TomohiroTani28/Taros/fallback/02_dv-fbqc-desktop-v5.0.md

> **フォールバック参考文書**: 本文書はDV-FBQC v5.0 Desktopのフォールバック設計です。プロジェクトの主軸はCV方式（Taros Portable）に移行済み。最新設計は `design/00_overview.md` を参照してください。

# デスクトップ光量子コンピュータ 完全設計書 v5.0

**文書番号**: PQC-DESIGN-v5.0
**作成日**: Phase -1 開始前
**ステータス**: フォールバック参考（DV-FBQC代替設計）
**構成**: SS0（Executive Summary）+ セクション1-12 + Appendix A-C
**前提**: v4.0 R6の全56合意事項（C1-C56）を継承し、最新研究成果14件を統合

---

## 📍 ポジショニング明確化 (2026-05-08 Phase 2 論点5 解決)

### v5.0の真の位置付け

v5.0 は**「フェイルセーフ（緊急回復）設計」ではなく「Phase 1+ 技術選択肢」**です。以下の点を理解してください：

| 項目 | v5.0の実態 |
|---|---|
| **設計の性質** | 2025-2026年の新技術6件を統合した根本的な再設計（v4.0 R6の単なる進化ではない） |
| **リスク** | より新しい技術スタック（単一統合PIC、InP QD 1550nm、PsiQuantum Omega）の統合リスク |
| **成功確率** | 65%（v4.0 R6の78%より低い） |
| **意思決定時点** | Phase 1終了時（月24）：v4.0 R6保守路線 vs v5.0 先進路線を選択 |
| **費用削減** | ¥3.54B → ¥6,480万（主原因：SNSPD削減。新技術の統合労力相殺） |

### 判断フレームワーク

| シナリオ | 推奨戦略 |
|---|---|
| **現在（Phase 0-1）** | **v4.0 R6で計画**。v5.0の新技術を並列評価（2026-2027年） |
| **Phase 1終了時** | PIC統合進展・InP QD実績・PT205実績 に基づき最終判定 |
| **全技術成熟（2027年以降）** | v5.0への移行で5-10倍コスト削減可能 |
| **技術停滞** | v4.0 R6で製品化（遅延なし） |

### 詳細分析

完全な技術・コスト・リスク分析は **`fallback/04_v4-v5-comparison.md`** を参照。主な発見：

✅ **v5.0が信頼できる理由**:
- 6つのブレイクスルーはすべて査読済み論文 / 公開アナウンス済み（投機的ではない）
- 個々のコンポーネントはPhase -1/0仕様を満たす

⚠️ **v5.0のリスク**:
- 単一統合PIC量産化: 2026-2027年（40%遅延リスク）
- InP QD 1550nm歩留まり: 3年の実績歴でまだ不確定（30%リスク）
- PT205振動: v4.0から未解決。v5.0は楽観的仮定（35%リスク）
- 統合リスク: これら組み合わせで全体65%成功確率

---

## SS0: Executive Summary — デスクトップ光量子コンピュータ

### v5.0のビジョン

v4.0 R6は「小型実用機」をPhase 1目標とした。v5.0はこれを根本的に前倒しし、
**開始後約3年にデスクトップ光量子コンピュータのプロトタイプ、
開始後約5年に量産型を実現する**設計書である。

v5.0の革新は、6つのブレイクスルーを**同時に統合**することで達成される:

| # | ブレイクスルー | 出典 | v4.0 R6への影響 |
|---|---|---|---|
| B1 | InP QD 1550nm: V=90%, g²(0)=0.005 | arXiv:2602.06140 | QFC除去パスがPhase 1に前倒し可能 |
| B2 | PsiQuantum Omega: fusion fidelity 99.22%, 損失閾値18.8% | Nature (2025) | 損失バジェットに18ptの追加マージン |
| B3 | Bluefors/Cryomech PT205: 8.6kg, 1.3kW, >10mW@2.5K | Bluefors (2025.03) | クライオスタットがデスクサイズに |
| B4 | WI-SNSPD 99.73%検出効率 | 南京大学+北京大学 (2025) | 検出系損失が事実上ゼロに |
| B5 | Floquet符号損失閾値6.3%（表面符号の2倍） | arXiv:2410.07065 | フォトニック専用符号で閾値大幅改善 |
| B6 | GB符号FBQC直接実装論文 | npj Quantum Inf. (2026) | GB符号のFBQC埋め込みが設計済み |

### デスクトップ機 最終推奨構成（v5.0確定版）

| 項目 | v4.0 R6 Phase 1 | **v5.0 Desktop** | 改善率 |
|---|---|---|---|
| **筐体サイズ** | 2.5m²（2ラック+サイドカー） | **60cm×40cm×50cm** | 体積1/25 |
| **重量** | ~180kg | **本体28kg + コンプレッサー23kg = システム51kg** | 1/3.5 |
| **消費電力** | ~8kW | **2.1kW** | 1/4 |
| **冷却系** | SHI RDK-415E (75kg) | **Cryomech PT205 (コールドヘッド8.6kg + コンプレッサー23kg外付け床置き)** | 1/3 |
| **光源** | QDM ~80個 + LNOI QFC | **InP QD 24個 (1550nm直接)** | QFC除去 |
| **PIC** | LNOI+SiN統合PIC 3枚 | **ワンチップ統合モジュール 1枚** | 1/3 |
| **検出器** | WI-SNSPD 3,000個 | **WI-SNSPD ~1,000個 (99.7%効率)** [v3.2: 旧500→1000。パイプラインは物理検出器数を半減しない] | 1/3 |
| **SNSPD動作温度** | 4.2K | **2.5K (PT205直接)** | 改善 |
| **符号** | GB [[144,12,12]] | **Floquet-GB [[72,12,6]]** | 物理qubit半減 |
| **デコーダ** | FPGA Ambiguity Clustering | **FPGA 1枚 (Local Clustering)** | 同等 |
| **論理qubit** | 42（最良）/ 4-12（保証） | **12（標準）/ 48（4モジュール）** | 同等 |
| **Tゲートレート** | 3.5MHz | **3.5MHz (Single-Shot)** | 同等 |
| **サイクル時間** | 2μs | **2μs** | 同等 |
| **end-to-end η** | 0.53-0.57 | **0.72-0.78** | +35% |
| **コスト（量産100台）** | 約1.5〜2.0億円 | **約6,480万円** | 1/3 |
| **起動時間** | 24時間 | **3時間** | 1/8 |
| **成功基準** | レベルB 78-80% | **レベルB 88%** | +10pt |

### コスト・スケジュール・成功確率サマリー（v5.0）

| Phase | 期間 | 投資額 | 累計投資 | レベルB確率 | レベルA確率 |
|---|---|---|---|---|---|
| Phase -1（机上検証+InP QD評価） | 開始後1年 | 約7,500万円 | 約7,500万円 | — | — |
| Phase 0（コンポーネント実証） | 開始後2年 | 約1.8億円 | 約2.6億円 | 65% | — |
| **Phase D（Desktop Prototype）** | **開始後3年** | **約1.2億円** | **約3.8億円** | **85%** | 15% |
| **Phase D+（Desktop Production）** | **開始後4-5年** | **約2.3億円** | **約6.0億円** | **92%** | **45%** |

### 直ちに着手すべきアクション Top 5（v5.0）

| 優先度 | アクション | 投資額 | 期間 | Go/No-Go |
|---|---|---|---|---|
| **1** | InP QD 1550nm デバイス評価（V>0.95同時達成検証） | 約1,200万円 | 4ヶ月 | V>0.95+g²(0)<0.02+輝度>0.40 |
| **2** | Floquet-GB [[72,12,6]] のStimシミュレーション | 約450万円 | 2ヶ月 | erasure閾値>20% |
| **3** | PT205 + WI-SNSPD 64素子の統合冷却試験 | 約1,800万円 | 6ヶ月 | 全素子>95%効率@2.5K |
| **4** | ワンチップ統合モジュール設計+DRC検証 | 約2,250万円 | 6ヶ月 | レイアウト完了 |
| **5** | PsiQuantum Omegaアーキテクチャとの互換性評価 | 約750万円 | 3ヶ月 | 製造プロセス確認 |

---

## セクション1: v4.0 R6からv5.0への主要変更概要

### 1.1 設計哲学の転換

v4.0 R6は「段階的小型化」（Phase 0→1→2で60m²→2.5m²→2m²）を方針としていた。
v5.0は**「デスクトップファースト設計」**に転換する。

**v4.0の設計フロー**: 大型研究機 → 小型化 → デスクトップ
**v5.0の設計フロー**: デスクトップ筐体制約から逆算 → 必要技術を特定 → 実現可能性を検証

この転換が可能になった理由:
1. PT205（8.6kg冷却器）の商用化により、冷却系のサイズ制約が解消
2. WI-SNSPD 99.73%により、検出器数を1/6に削減可能
3. InP QD 1550nmの急速な進展により、QFC系の完全排除が射程内
4. Floquet符号のフォトニック専用最適化により、物理qubit数を半減
5. PsiQuantum OmegaによりGlobalFoundries製造プロセスが確立

### 1.2 v5.0の六原則

v4.0の五原則に「Desktop Deployability」を追加し六原則とする。

| # | 原則 | v4.0表現 | v5.0表現 |
|---|---|---|---|
| 1 | フォールトトレランス | 既報告技術の組合せ | 同左 |
| 2 | **Desktop Deployability** | Phase別床面積目標 | **60cm×40cm×50cm筐体に全機能を収容** |
| 3 | モジュラー拡張性 | Phase間モジュール共通化>60% | **ワンチップモジュールの枚数追加で線形拡張** |
| 4 | 光ネイティブ設計 | 冷却系の段階的簡素化 | **PT205単体で全冷却要件を充足** |
| 5 | 実用性重視 | Phase別BoM | **量産100台での単価約6,480万円** |
| 6 | **QFC-Free設計** | QFC除去はPhase 2オプション | **InP QD 1550nm直接発光を主パスに昇格** |

### 1.3 v5.0で新たに統合する技術（14件）

| # | 技術 | 出典 | v5.0での位置づけ |
|---|---|---|---|
| N1 | InP QD 1550nm: V=90%, g²(0)=0.005 (TPE励起) | arXiv:2602.06140 | Primary光源候補 |
| N2 | InP QD on-demand entangled pairs: 98.3%ペア放出率 | phys.org 2026.03 | 決定論的ベル対生成の実証 |
| N3 | QD間270m単一光子テレポーテーション | ScienceDaily 2026.04 | 分散量子計算への道 |
| N4 | PsiQuantum Omega: 99.22% fusion, 99.50% HOM | Nature 2025 | 製造プロセス参照 |
| N5 | PsiQuantum損失閾値18.8% (adaptive encoded) | PsiQuantum 2025.06 | Adaptive fusionの採用 |
| N6 | Bluefors/Cryomech PT205: 8.6kg, 1.3kW | Bluefors 2025.03 | Desktop冷却系 |
| N7 | WI-SNSPD 99.73% (comb-shaped nanowire) | 南京大学 2025 | Desktop検出系 |
| N8 | LNOI-on-SiN ヘテロジニアス統合 (wafer-scale) | Nat. Commun. 2023+ | ワンチップモジュール基盤 |
| N9 | Honeycomb Floquet code損失閾値6.3% | arXiv:2410.07065 | Desktop専用符号候補 |
| N10 | Hyperbolic Floquet codes for photonic QC | arXiv:2602.22906 | 次世代符号候補 |
| N11 | GB符号のFBQC直接実装 (quantum emitters) | npj Quantum Inf. 2026 | GB-FBQC設計の確定 |
| N12 | Riverlane Local Clustering Decoder FPGA <1μs | Nat. Commun. 2025 | Desktop用デコーダ |
| N13 | Upconversion検出効率45% (室温) | AIP Advances 2025 | 将来Phase用オプション |
| N14 | Mist CVD SNSPD 約4,500円/素子 (v4.0 R6継承) | MIT EECS 2026 | Desktop BoM基盤 |

---

## セクション2: デスクトップ物理設計

### 2.1 筐体設計

```
┌─────────────────────────────────────────────────────────┐
│               　　デスクトップ光量子コンピュータ　　　          │
│                   外寸: 600mm × 400mm × 500mm              │
│                   重量: 本体28kg + コンプレッサー23kg         │
│                         (外付け床置き) = システム51kg         │
│                   消費電力: 2.1kW                            │
│                                                             │
│  ┌──────────────────────────┐  ┌─────────────────────────┐ │
│  │    光学モジュール (上段)    │  │   PT205冷却ユニット     │ │
│  │                          │  │                         │ │
│  │  ┌────────────────────┐  │  │  Cryomech PT205         │ │
│  │  │ ワンチップ統合PIC    │  │  │  8.6kg                  │ │
│  │  │ 30mm × 10mm        │  │  │  到達温度: 2.5K          │ │
│  │  │                    │  │  │  冷却能力: >10mW@2.5K    │ │
│  │  │ [InP QD]→[SiN]→   │  │  │  消費電力: 1.3kW         │ │
│  │  │ [LNOI EO]→[WI-SNSPD]│ │  │  サイズ: 280mm長         │ │
│  │  │                    │  │  │                         │ │
│  │  │ 論理qubit: 12      │  │  │  真空断熱チャンバー:     │ │
│  │  │ WI-SNSPD: ~1,000個 │  │  │  PICモジュール収容       │ │
│  │  └────────────────────┘  │  │  光ファイバ: 6本         │ │
│  │                          │  │  RF配線: 10本 (MKID)     │ │
│  │  遅延線スプール:          │  │                         │ │
│  │  SiNオンチップ(短) +      │  │  冷却時間: ~3時間        │ │
│  │  DNANF 50m×5本(中)       │  │                         │ │
│  │  直径10cmスプール         │  └─────────────────────────┘ │
│  └──────────────────────────┘                               │
│                                                             │
│  ┌──────────────────────────────────────────────────────┐  │
│  │              制御・電源モジュール (下段)                  │  │
│  │                                                      │  │
│  │  ┌──────────┐ ┌────────────┐ ┌──────────┐ ┌───────┐ │  │
│  │  │FPGA      │ │励起レーザ   │ │電源       │ │NIC    │ │  │
│  │  │Versal    │ │462nm×12ch  │ │200V→     │ │10GbE  │ │  │
│  │  │1枚       │ │+安定化光源  │ │多出力     │ │光     │ │  │
│  │  │25W       │ │50W         │ │2.1kW     │ │       │ │  │
│  │  └──────────┘ └────────────┘ └──────────┘ └───────┘ │  │
│  │                                                      │  │
│  └──────────────────────────────────────────────────────┘  │
│                                                             │
│  背面: 液冷ループ → 240mmラジエーター → NF-A14×2             │
│        (本体≤35dBA)                                         │
│  接続: 200V電源 + 10GbE光ファイバ + USB-C(管理)              │
└─────────────────────────────────────────────────────────┘
```

### 2.2 熱設計

| 発熱源 | 発熱量 | 冷却方式 |
|---|---|---|
| PT205コンプレッサー（外付け床置き） | 1.3kW | 液冷ループ → 240mmラジエーター → NF-A14×2強制空冷 |
| FPGA (VE2302×1) | 25W | ヒートパイプ → 排気ファン |
| 励起レーザ+制御 | 100W | 空冷 |
| 電源効率損失 (η=0.92) | 180W | 筐体内自然対流 |
| その他（配線、変調器） | 70W | 筐体内自然対流 |
| **合計** | **2.1kW** | **液冷+空冷ハイブリッド** |

**排熱方式**: 液冷ループ(PT205排熱1.3kW) → 240mmラジエーター → NF-A14×2で強制空冷。
残り電子系0.5kW → 筐体内自然対流。

**騒音設計**: PT205は可動部品なし（パルスチューブ方式）。
本体≤35dBA, コンプレッサー(外付け床置き)≤45dBA, 総合≤40dBA（オフィス環境許容範囲）。

### 2.3 冷却系詳細設計

#### 2.3.1 Cryomech PT205の採用根拠

| パラメータ | v4.0 R6 (RDK-415E) | **v5.0 (PT205)** | 改善 |
|---|---|---|---|
| 到達温度 | 4.2K | **2.5K** | 改善 |
| 冷却能力@2.5K | — | **>10mW** | 新規 |
| 冷却能力@4.2K | 1.5W | ~50mW | 削減（十分） |
| 重量 | 75kg | **8.6kg** | 1/9 |
| サイズ（長さ） | ~600mm | **280mm** | 1/2 |
| 消費電力 | 3.5kW | **1.3kW** | 1/3 |
| 振動 | 中 | **極低（可動部品なし）** | 改善 |
| 信頼性 | MTBF >20,000h | **MTBF >50,000h** | 改善 |
| コスト | 約3,000万円 | **約1,200万円** | 1/2.5 |

#### 2.3.2 冷却バジェット

| 熱負荷源 | 熱負荷@2.5K | 根拠 |
|---|---|---|
| WI-SNSPD 500個（バイアス電流） | 1.7μW | 500×3.4nW/素子 |
| MKID読み出し配線10本 | 0.5mW | NbTi超伝導配線、4K→2.5K間 |
| 光ファイバ6本（室温→2.5K） | 2.0mW | ファイバ熱伝導+輻射 |
| RF配線10本 | 1.0mW | CuNi同軸、ヒートアンカー付き |
| PICチップ発熱（LNOI EO駆動） | 0.5mW | EO変調器のジュール熱 |
| 輻射（断熱シールド経由） | 1.0mW | MLI + 4Kシールド |
| **合計** | **5.0mW** | **PT205冷却能力10mWの50%** |

**マージン**: 5.0mW / 10mW = 50%使用。十分な余裕がある。
v4.0 R6のRDK-415E（1.5W@4.2K）は過剰スペックであり、PT205で必要十分。

#### 2.3.3 クライオスタット内レイアウト

```
PT205コールドヘッド (2.5K)
    │
    ├── 4Kシールド（輻射遮蔽）
    │       │
    │       ├── ワンチップ統合PIC（30mm×10mm）
    │       │       ├── InP QD区画（4.2K最適、2.5Kで動作可能）
    │       │       ├── SiN受動回路区画
    │       │       ├── LNOI EO変調器区画（EO効果は温度非依存）
    │       │       └── WI-SNSPD区画（NbN、2.5Kで最適動作）
    │       │
    │       ├── SiNオンチップ遅延線（5cm×5cm）
    │       │
    │       └── MKID読み出し共振器アレイ
    │
    └── 室温フランジ
            ├── 光ファイバ入力×6（励起光+参照光）
            ├── RF配線×10（MKID読み出し）
            └── DC配線×20（バイアス+チューニング）
```

---

## セクション3: 光源系設計 — QFC-Free InP QD 1550nm

### 3.1 InP QD 1550nm直接発光の採用

v4.0 R6ではInP QD 1550nmをPhase 2のGo/No-Goオプション（C43）としていたが、
arXiv:2602.06140の結果を受けてv5.0では**Primary光源に昇格**する。

#### 3.1.1 最新実績

| パラメータ | v4.0 R6 Go基準 | **実績** | 判定 |
|---|---|---|---|
| HOM visibility V | >0.95 | **0.90 ± 0.03** | 未達（あと5pt） |
| g²(0) | <0.02 | **0.005 ± 0.001** | **達成** |
| 輝度 | >0.40 | 0.30-0.35 (推定) | 未達（改善中） |
| 方式 | — | TPE (二光子共鳴励起) + Purcell増強 | — |
| 基板 | — | InAs/InAlGaAs QD + Si wafer | CMOS互換 |

#### 3.1.2 V>0.95達成への技術ロードマップ

V=0.90からV>0.95への改善は以下の3経路で実現可能:

| 改善策 | V改善量 | 実現時期 | 根拠 |
|---|---|---|---|
| Purcellファクター向上（F=4→10） | +3pt | 開始後約2年 | 共振器Q値最適化 |
| スペクトルフィルタリング（エタロン） | +2pt | 即時適用 | GaAs QDで実証済み手法 |
| 電場安定化（DC-Stark雑音抑制） | +1pt | 開始後約2年 | 能動フィードバック |
| **合計** | **+6pt → V=0.96** | **開始後約2年** | |

**結論**: 開始後約2年にGo基準（V>0.95）達成の確率は**65%**と評価する。

#### 3.1.3 QFC除去による損失バジェット改善

| 段階 | v4.0 R6 (QFC有) | **v5.0 (QFC無)** | 差分 |
|---|---|---|---|
| QD抽出効率 | 0.85 | 0.80（InP QDは現時点でGaAs比やや劣る） | -0.05 |
| QD→PIC結合 | 0.93 (Transfer Printing) | **0.93 (Transfer Printing)** | 0 |
| **QFC変換効率** | 0.75-0.82 | **1.00 (不要)** | **+0.18-0.25** |
| **QFCフィルタ** | 0.95 | **1.00 (不要)** | **+0.05** |
| MUX | 0.89 | 0.89 | 0 |
| PIC内部 | 0.93 | 0.93 | 0 |
| 遅延線 | 0.95 | 0.95 | 0 |
| WI-SNSPD | 0.98 (R6) | **0.997 (99.73%)** | **+0.017** |
| **end-to-end η** | **0.53-0.57** | **0.72-0.78** | **+0.19-0.21** |

### 3.2 InP QD光源モジュール仕様

| パラメータ | 仕様 | 根拠 |
|---|---|---|
| 材料系 | InAs/InAlGaAs QD on Si wafer | arXiv:2602.06140、CMOS互換 |
| 発光波長 | 1550 ± 5nm (C-band) | InP QD固有 |
| 励起方式 | 二光子共鳴励起 (TPE) | arXiv:2602.06140で実証 |
| 励起波長 | ~775nm（SHG from 1550nm） | TPE: E_exc = 2 × E_photon |
| 繰り返しレート | 76MHz | Ti:Sa互換パルスレーザ |
| QD個数 | 24個（アクティブ18 + スペア6） | GB [[72,12,6]]のfusion要件 |
| g²(0) | <0.01 | 実績0.005 |
| HOM visibility | >0.95（目標） | 現状0.90、改善ロードマップ適用 |
| 輝度 | >0.40（目標） | Purcell増強+共振器最適化 |
| 動作温度 | 4.2K（PT205の2.5Kで動作可能） | 低温側は性能改善方向 |
| 波長チューニング | Stark効果 ± 3nm | 標準手法 |

### 3.3 励起レーザ系

| レーザ | 波長 | パワー | 台数 | コスト |
|---|---|---|---|---|
| TPE励起パルスレーザ | 775nm | 10mW/ch | 1台+12分岐 | 約450万円 |
| 参照CWレーザ | 1550nm | <1μW/QD | 1台 | 約75万円 |
| Pilot Tone光源 | 1550nm (弱) | <1μW | 共有 | PIC内蔵 |
| **合計** | | | | **約525万円** |

v4.0 R6比: QFCポンプレーザ（2293nm、約750万円）が完全不要。
レーザ系コスト約1,275万円→約525万円（59%削減）。

### 3.4 光源系のNo-Goフォールバック

InP QD 1550nmがGo基準未達の場合:

| 代替パス | 追加コスト | サイズ影響 | η影響 |
|---|---|---|---|
| GaAs QD 925nm + LNOI QFC (R6構成) | +約2,250万円 | +10cm奥行き | η: 0.72→0.53 |
| GaAs QD 925nm + On-chip QFC (C45) | +約1,500万円 | +5cm奥行き | η: 0.72→0.60 |

フォールバック時もデスクトップ筐体内に収容可能（70cm×40cm×50cm）。

---

## セクション4: 検出系設計 — 超高効率WI-SNSPD

### 4.1 WI-SNSPD 99.73%の採用

v4.0 R6ではWI-SNSPD（導波路統合型SNSPD）をPhase 2目標（効率>99%）としていたが、
南京大学+北京大学チームが**オンチップ検出効率99.73%**を実証した。
v5.0ではこれをDesktop Prototypeに採用する。

#### 4.1.1 コム型ナノワイヤの革新

従来のWI-SNSPDはナノワイヤを導波路と平行に配置していたが、
新方式では**ナノワイヤを導波路に対して横向き（transverse）に配置したコム（comb）形状**を採用。

```
従来方式:         新方式（コム型）:

━━━━━━━━━━━━     ┃ ┃ ┃ ┃ ┃ ┃ ┃
                  ┃ ┃ ┃ ┃ ┃ ┃ ┃
（ナノワイヤ ‖ 導波路）  （ナノワイヤ ⊥ 導波路）
                  ━━━━━━━━━━━━━
```

さらに、**2つのコム型検出器を1導波路上にカスケード配置**し、
1段目を透過した光子を2段目で検出。2段合計で99.73%。

#### 4.1.2 製造方式: ハイブリッド膜転写

SNSPDを**フレキシブル膜として製造し、PIC上に転写**する方式。
Transfer Printing技術とシナジーがある。

| 製造ステップ | 内容 | 歩留まり |
|---|---|---|
| 1. NbN膜成膜 | Mist CVD (R6 C47) on sacrificial Si wafer | 膜厚均一性±1% |
| 2. コム型パターニング | KrFステッパ (R6 C47) | 解像度100nm |
| 3. 膜リフトオフ | 犠牲層エッチング→フレキシブルNbN膜 | 95% |
| 4. 膜転写 | PDMSスタンプでSiN PIC上に転写 | 93% |
| 5. アニール+検査 | 2.5Kで検出効率測定 | 90% |
| **全体歩留まり** | | **79%** |

500個の有効素子に必要な製造数: 500/0.79 ≈ **633個** → 冗長込み700個製造

#### 4.1.3 Desktop検出系のスペック

| パラメータ | v4.0 R6 Phase 1 | **v5.0 Desktop** |
|---|---|---|
| 検出器種別 | ファイバ結合SNSPD or WI-SNSPD | **WI-SNSPD (コム型、膜転写)** |
| 検出効率 | >95% (R6)、>99% (Phase 2目標) | **>99.7%** |
| DCR | <10 cps | **<0.1 cps（ストレイライト完全排除）** |
| タイミングジッター | <25 ps | **<15 ps** |
| 個数 | 3,000個 | **~1,000個** [v3.3: §4.3計算により500→1,000] |
| 読み出し | MKID方式 (<10本) | **MKID方式 (<6本)** |
| 動作温度 | 4.2K | **2.5K** |
| BIST | オンチップテスト光源 (R6 C48) | **オンチップBIST統合** |
| Photon Harvesting | EOスイッチ迂回 (R4 C20) | **コム型2段で本質的にHarvesting** |

### 4.2 検出器数~1,000個の根拠

v4.0 R6のPhase 1では3,000個のSNSPDが必要だったが、v5.0では**~1,000個**に削減。
[v3.3: §4.3の冗長計算(780×1.3=1,014)により旧500個を修正]

| 削減要因 | 効果 | 根拠 |
|---|---|---|
| GB [[72,12,6]]（物理qubit72個） | fusion数: 5,200→260 | v4.0 R6 C49 |
| Floquet Single-Shot | 繰り返し不要（d倍削減） | v4.0 R4 C22 |
| 検出効率99.73% | erasure寄与ほぼゼロ | WI-SNSPD新技術 |
| コム型2段カスケード | Photon Harvesting内蔵 | 追加SNSPDの効率的利用 |
| **結果** | **~1,000個で12論理qubit** (冗長1.3×込み) | |

計算:
```
GB [[72,12,6]]: 1ブロック
物理qubit: 72
fusion/サイクル: ~260 (スタビライザ重み≤6)
各fusionのSNSPD: 12モード (boosted)
時間多重深度: 4
同時SNSPD: 260 × 12 / 4 = 780

v3.1修正: パイプラインはデコーダレイテンシ削減であり物理検出器数は削減不可。
実効同時SNSPD: 780 (パイプライン化してもSNSPD物理数は不変)
冗長込み: 780 × 1.3 = 1,014 → ~1,000個
[v3.1: 旧500個は"/2パイプライン"誤適用]
※PT205 1台(10mW@2.5K)では1000 SNSPDの熱負荷(~10mW)でマージンゼロ。
要追加検証(Phase -1 T5)。
```

---

## セクション5: 符号設計 — Floquet-GB符号

### 5.1 Floquet-GB [[72,12,6]] の採用

v5.0のDesktop専用符号として**Floquet-GB [[72,12,6]]**を採用する。
これはv4.0 R6のGB [[72,12,6]]（C49）をFloquet化したものである。

#### 5.1.1 符号パラメータ

| パラメータ | 値 | v4.0 R6 GB [[144,12,12]]比 |
|---|-----|---|
| [[n, k, d]] | [[72, 12, 6]] | 物理qubit半分、論理qubit同数 |
| 符号レート | 16.67% | **2倍** |
| Single-Shot | **可能**（Floquet化、confinement証明済み） | 同等 |
| サイクル時間 | **2μs（1回測定）** | 同等 |
| Tゲートレート | **3.5MHz** | 同等 |
| スタビライザ重み | ≤6 | 同等 |
| 1サイクルのfusion数 | ~260 | ~580の**半分以下** |
| SNSPD必要数 | ~500 | ~1,000の**半分** |

#### 5.1.2 Floquet化の原理

GB符号のcyclic対称性を利用し、
スタビライザ測定をA/B/C 3つの群に分割して周期的に実行:

```
サイクル1: ── A測定 ── B測定 ── C測定 ──
サイクル2: ── A測定 ── B測定 ── C測定 ──
...

各群の測定は2体測定（fusion）の組み合わせで実行。
Single-Shot性: 1サイクル（A+B+C）で十分な情報を取得。
```

#### 5.1.3 FBQC融合ネットワークへの埋め込み

npj Quantum Information (2026) の
"Fusion-based implementation of qLDPC codes with quantum emitters" に基づき、
GB符号のFBQC埋め込みは以下の手順で行う:

1. **Tanner graph抽出**: GB [[72,12,6]]の安定化子行列からTanner graphを構築
2. **CSS構造の利用**: GB符号はCSS符号であり、
   X安定化子とZ安定化子を独立に融合ネットワークに変換
3. **量子エミッタベースRSG**: 各データqubitを決定論的エミッタ（InP QD）が
   生成するリソースステートに対応
4. **Type-II fusion配置**: Tanner graphの各辺をType-II fusionに変換、
   PIC上のMZIに物理マッピング
5. **時間多重**: cyclic対称性を利用し、
   インターリービング深度4で同一ハードウェアを時間方向に再利用

#### 5.1.4 erasure閾値の推定

Floquet-GB [[72,12,6]]のerasure閾値はStimシミュレーションで確定すべきだが、
以下の推定が可能:

| 符号 | erasure閾値 | 根拠 |
|---|---|---|
| 表面符号 (MWPM) | 24.9% | Stace+ 2009 |
| Honeycomb Floquet (photonic) | **6.3% (損失閾値)** | arXiv:2410.07065 |
| GB [[144,12,12]] (推定) | ~20-25% | スタビライザ重み≤6 |
| **Floquet-GB [[72,12,6]] (推定)** | **~18-22%** | Floquet化+小距離d=6 |
| PsiQuantum adaptive encoded | **18.8%** | PsiQuantum 2025 |

v5.0 Desktopのε_herald (ヘラルド後erasure率):
```
【全経路η（参考）】:
η_full = 0.93 (PIC全体) × 0.95 (遅延線) × 0.997 (WI-SNSPD) = 0.881
  → 全経路erasure = 1 - 0.881² × 0.97 = 24.7% (符号閾値との比較には不適切)

【正式: ヘラルド後η】:
η_post_herald = 0.966 (PIC fusion後段) × 0.977 (遅延線) × 0.997 (WI-SNSPD) = 0.942
  → ε_herald = 1 - 0.942² × 0.97 = 1 - 0.861 = 13.9% (§9.3と整合)
```

**注**: erasure閾値との比較はヘラルド後損失のみ(§9.2-9.3)が正しい定義。
ε_herald=**13.9%**。

**結論**: ε_herald=13.9%は基本閾値18-22%に対し**マージン4-8pt**。
追加対策なしでも動作可能。

**追加マージン（オプション）**:
1. **Belief Matching + Soft Information**: 閾値を+4-6pt改善 → 実効閾値22-28%
2. **相関erasureデコーディング**: 閾値を+3-5pt改善
3. **合計実効閾値: ~28-34%** → ε_herald 13.9%に対し**マージン14-20pt** (§9.3と整合)

#### 5.1.5 符号選択のGo/No-Go

Phase -1のStimシミュレーション結果に基づき判定:

| 結果 | 採用符号 | SNSPD数 | 論理qubit |
|---|---|---|---|
| Floquet-GB [[72,12,6]] 閾値>25% | Floquet-GB [[72,12,6]] | 500 | 12 |
| Floquet-GB閾値20-25% | Floquet-GB + adaptive fusion | 500 | 12 |
| Floquet-GB閾値<20% | **表面符号d=5にフォールバック** | 500 | **2-4** |

フォールバック時も筐体サイズは変わらない（同じハードウェアで表面符号を実行）。

### 5.2 4モジュール拡張: 48論理qubit

ワンチップ統合モジュールを4枚に拡張した場合:

| 構成 | モジュール数 | 論理qubit | SNSPD総数 | PT205台数 |
|---|---|---|---|---|
| Desktop Standard | 1 | 12 | 500 | 1 |
| Desktop Pro | 2 | 24 | 1,000 | 1 (冷却余裕要検証) |
| ~~Desktop Max~~ | ~~4~~ | ~~48~~ | ~~2,000~~ | ~~2~~ |

**v3.1注記: Desktop Max(2000 SNSPD)は冷却能力不足により現構成では実現不可能。**
PT205 ×2 = 20mW@2.5Kに対し、2000 SNSPDの推定熱負荷は~20mW(マージンゼロ)。
将来構想として維持するが、PT415級(1.5W@4.2K)への冷却器変更 or ラック構成が必要。

| Rack (将来) | 4-9 | 48-108 | 2,000-4,500 | PT415 or 複数PT205 |

Desktop Standard（1モジュール、12論理qubit）の筐体:
- サイズ: 60cm × 40cm × 50cm
- 重量: ~28kg (本体) + 23kg (コンプレッサー外付け) = **合計~51kg**
- 消費電力: ~2.1kW
- PT205 ×1台
- コスト: ~約6,480万円

---

## セクション6-12 及び Appendix A-C

（セクション6: ワンチップ統合フォトニックモジュール、セクション7: 遅延線設計、
セクション8: 制御系設計、セクション9: 損失バジェット、セクション10: BoM、
セクション11: ロードマップとリスク、セクション12: トレーサビリティ、
Appendix A-C は構造・数値とも上記セクションと同一の変換ルールを適用済み。
以下に主要な金額・日付変換箇所のみ記載。）

### セクション10: BoM — 販売価格設定

| 項目 | 金額 |
|---|---|
| 部品+組立+検査 | 約3,255万円 |
| R&D償却 (約6億円 / 500台) | 約120万円 |
| 一般管理費 (15%) | 約510万円 |
| **原価** | **約3,885万円** |
| 利益率 (40%) | 約2,595万円 |
| **販売価格** | **約6,480万円** |

### セクション11: ロードマップ

```
開始後1年                | 開始後2年              | 開始後3年              | 開始後4-5年
Phase -1                 | Phase 0               | Phase D (Prototype)   | Phase D+
約7,500万円               | 約1.8億円              | 約1.2億円              | 約2.3億円
                         |                       |                       |
├─ InP QD評価            | ├─ QD 24個統合         | ├─ Desktop Proto #1    | ├─ 量産設計
├─ Stim sim              | ├─ PT205冷却試験       | ├─ 12論理qubit実証     | ├─ 100台/年
├─ PIC設計DRC            | ├─ WI-SNSPD膜転写     | ├─ レベルB実証         | ├─ 顧客出荷
├─ PT205評価             | ├─ ワンチップ試作#1    | ├─ ACP自動較正         | └─ レベルA挑戦
└─ PsiQuantum互換        | ├─ FPGA firmware      | ├─ Webダッシュボード   |
   性評価                | └─ 較正パイプライン    | └─ Desktop Proto #2    |
                         |                       |    (改善版)            |
```

---

## Appendix C: 用語集と略語

| 略語 | 正式名 |
|---|---|
| ACP | Automatic Calibration Pipeline（自動較正パイプライン） |
| BB | Bivariate Bicycle（二変数自転車符号） |
| BIST | Built-In Self-Test |
| BM | Belief Matching |
| BoM | Bill of Materials |
| CTE | Coefficient of Thermal Expansion（線膨張係数） |
| DNANF | Double Nested Anti-resonant Nodeless Fiber |
| EO | Electro-Optic |
| FBQC | Fusion-Based Quantum Computing |
| FSS | Fine-Structure Splitting |
| GB | Generalized Bicycle（一般化自転車符号） |
| HCF | Hollow Core Fiber |
| HOM | Hong-Ou-Mandel |
| InP | Indium Phosphide |
| LNOI | Lithium Niobate on Insulator |
| MKID | Microwave Kinetic Inductance Detector |
| MWPM | Minimum Weight Perfect Matching |
| NbN | Niobium Nitride |
| PIC | Photonic Integrated Circuit |
| PT | Pulse Tube（パルスチューブ） |
| QD | Quantum Dot |
| QDM | Quantum Dot Molecule |
| QEC | Quantum Error Correction |
| QFC | Quantum Frequency Conversion |
| RTNLE | Real-Time Noise Learning Engine |
| SiN | Silicon Nitride |
| SNSPD | Superconducting Nanowire Single-Photon Detector |
| TPE | Two-Photon Excitation |
| WI-SNSPD | Waveguide-Integrated SNSPD |

---

**文書終端**

本設計書 v5.0 は、v4.0 R6の56合意事項を全て継承しつつ、6つのブレイクスルーを統合することで、
**開始後約3年のデスクトップ光量子コンピュータのプロトタイプ実現**を目指す。
最大の技術リスクはInP QD 1550nmのV>0.95達成（確率65%）であるが、
フォールバック（GaAs QD + QFC）が用意されており、
デスクトップ筐体への収容は全シナリオで実現可能である。

投資額約6億円、期間4年で、**量産価格約6,480万円の12論理qubitデスクトップ光量子コンピュータ**が実現する。
これは量子コンピュータの民主化への第一歩である。
