TomohiroTani28/Taros/fallback/01_deskside-vision.md

> **フォールバック参考文書**: 本文書はDV-FBQC v5.0 Desktopのフォールバック設計です。プロジェクトの主軸はCV方式（Taros Portable）に移行済み。最新設計は `design/00_overview.md` を参照してください。

# デスクトップ光量子コンピュータ設計書

**Document ID**: PQC-DESKSIDE-v1.0
**Last Updated**: Phase -1 開始前
**Status**: フォールバック参考（旧「新主軸」記述は撤廃）

---

## 1. ビジョンと定義

### 1.1 「デスクトップ光量子コンピュータ」とは

**定義**: 一般的なサーバールームやラボに設置可能な、42U標準ラック1本以内に全機能を収容した誤り訂正型量子コンピュータ。

```
┌─────────────────────────────────────────────┐
│                                             │
│   ┌─────────┐                               │
│   │         │  42U Standard Rack            │
│   │  Taros  │  600mm x 1070mm x 2000mm     │
│   │ Deskside│                               │
│   │   QC    │  + 外部冷却ユニット             │
│   │         │    400mm x 400mm x 800mm      │
│   │         │                               │
│   └─────────┘  ┌────────┐                   │
│                │ Cooling │                   │
│                │  Unit   │                   │
│                └────────┘                   │
│                                             │
│   設置面積: 2.0m x 1.5m = 3.0m²             │
│   消費電力: < 5kW                            │
│   重量: < 120kg（冷却ユニット含む）            │
│   冷却水: 不要（空冷コンプレッサ）              │
│                                             │
└─────────────────────────────────────────────┘
```

### 1.2 なぜ「デスクトップ」が正しい目標か

| 観点 | 根拠 |
|---|---|
| **市場** | 量子コンピュータのオンプレミス需要（金融・製薬・防衛）は開始後約10年で1.5兆円規模と予測。クラウド専用では満たせないレイテンシ・セキュリティ要件が存在する |
| **技術的到達性** | Phase 2（開始後約6年）で1ラック+外部冷却が既に設計済み。追加2-3年の技術成熟で「空冷・冷却水不要」が射程圏内 |
| **競争優位** | 超伝導方式は原理的にmK冷却が必要で、デスクトップは不可能。フォトニック方式のみが実現可能な形態であり、決定的差別化要因 |
| **長期目標との整合** | 20年ビジョンの「個人量子デバイス」への中間マイルストーンとして、開始後約10年のデスクトップQCは不可欠 |

### 1.3 超伝導方式との構造的差異（小型化の物理的根拠）

```
超伝導方式（IBM/Google）:
  量子ビット動作温度: 10-20 mK  → 希釈冷凍機が必須（~1,000kg, ~200kW）
  配線: 同軸ケーブル数千本      → 冷凍機サイズが配線で律速
  デスクトップ化: 物理的に不可能（冷凍機だけで1トン超）

フォトニック方式（Taros）:
  量子ビット（光子）: 室温動作   → 冷却不要
  光学回路: 室温動作             → 冷却不要
  冷却対象: SNSPDのみ（2.5-4.2K）→ PT冷凍機で十分（40-75kg）
  配線: 光ファイバ（軽量）       → 重量・体積の律速要因にならない
  デスクトップ化: 技術的に到達可能
```

---

## 2. デスクトップQCのスペック目標

### 2.1 ハードウェアエンベロープ

| 項目 | 目標値 | 制約根拠 |
|---|---|---|
| **設置面積** | ≤ 3.0 m² | 標準ラック+冷却ユニット+保守スペース |
| **ラック** | 42U × 1本 | 標準サーバールーム互換 |
| **重量** | ≤ 120 kg（ラック+冷却） | エレベーター搬入可能、床荷重300kg/m²以内 |
| **消費電力** | ≤ 5 kW | 一般的な単相200V/30Aで運用可能 |
| **冷却水** | **不要**（空冷コンプレッサ） | 水配管工事の排除が設置容易性の鍵 |
| **振動** | VC-C以下（12.5 μm/s rms） | 一般オフィスビル相当。VC-D不要 |
| **騒音** | ≤ 55 dBA @ 1m | サーバールーム許容範囲 |
| **設置時間** | ≤ 3日（搬入+接続+較正） | 顧客エンジニアの最小拘束 |
| **保守** | リモート監視 + 年2回オンサイト | PT冷凍機メンテ20,000h間隔（~2.3年） |

### 2.2 計算性能目標

| 項目 | 目標値 | 根拠 |
|---|---|---|
| **論理qubit数** | 48-100 | GB [[144,12,12]]（Floquet）で42-100、最小構成でも12 |
| **論理エラー率** | p_L < 10⁻⁶ / gate | 量子化学計算の実用要件 |
| **Tゲートレート** | 3.5 MHz | Floquet Single-Shot（2μsサイクル） |
| **クリフォードゲートレート** | ~71 kHz（d=7） | d × 2μs |
| **end-to-end η** | ≥ 0.70（保守）/ 0.77（楽観） | クライオPIC構成による損失最小化 |
| **アプリケーション** | VQE（LiH, STO-3G）: ~100ms / QAOA（MaxCut n=50）: ~10ms | 50-100論理qubit範囲の実用問題 |

### 2.3 コスト目標

| 項目 | 目標値 |
|---|---|
| **製造原価** | ≤ 約1.5億円 |
| **販売価格** | 約2.3〜3.0億円 |
| **年間保守費** | 約1,500〜2,300万円 |
| **量産時目標（100台/年）** | 製造原価 約7,500万円以下 |

---

## 3. ラック内配置設計

### 3.1 42Uラック統合レイアウト

```
42U Standard Rack (600mm W x 1070mm D x 2000mm H)
┌─────────────────────────────────────────┐
│ [42-39U] 電源・UPS・PDU                  │  4U
│          + ネットワーク (10GbE)           │  ~8kg, 0.5kW
├─────────────────────────────────────────┤
│ [38-35U] 制御・デコーダ                   │  4U
│          FPGA ×1 (Versal AI Edge)       │  ~12kg, 0.3kW
│          + デコーダASIC ×1               │
│          + ホストCPU (組込みクラス)        │
├─────────────────────────────────────────┤
│ [34-27U] QD光源 + QFC（統合モジュール）    │  8U
│          Transfer Printing QD ×64-80    │  ~15kg, 0.4kW
│          + On-chip QFC ×8 (集積チップ)   │
│          + パルス励起レーザ ×2            │
│          + 小型4Kクーラー (QD用)          │
├─────────────────────────────────────────┤
│ [26-19U] 統合PIC + EO変調                │  8U
│          モノリシックPIC ×2-3            │  ~10kg
│          (LNOI+SiN ヘテロジニアス集積)    │
│          + EO集積チップ ×4               │
│          + 光スイッチ (集積型)            │
├─────────────────────────────────────────┤
│ [18-11U] 遅延線                          │  8U
│          3層構成:                        │  ~5kg
│           - DNANF 50m×5本 (v5.0削減)     │
│             (スプール直径10cm, 2U)        │
│           - SiNオンチップスパイラル (PIC内) │
│           - SNCM超短遅延 (PIC内)          │
├─────────────────────────────────────────┤
│ [10-5U]  光ファイバパッチ + 配線管理       │  6U
│          冷却ユニット接続インタフェース     │  ~5kg
│          PMF/SMF パッチパネル             │
├─────────────────────────────────────────┤
│ [4-1U]   SNSPD接続 + 読み出しI/F         │  4U
│          MKID周波数多重読み出し            │  ~5kg
│          RF配線 <10本 → 冷却ユニットへ    │
└─────────────────────────────────────────┘

ラック内合計: ~75kg, ~1.2kW (冷却系除く)
```

### 3.2 外部冷却ユニット（v1.1更新: v5.0知見反映）

> **v1.1更新**: v5.0設計書の知見（PT205 8.6kg、WI-SNSPD 99.73%コム型）を反映し、2構成を併記する。

**構成A（SNSPD ~1,000個、GB [[72,12,6]]使用時 -- v5.0推奨）**:

```
Cryomech PT205 (280mm長, 8.6kg)
┌───────────────────────┐
│  WI-SNSPDコム型 ~1,000個 │  検出効率 >99.7%
│  (ワンチップ統合PIC上)  │  Mist CVD + 膜転写
│  + InP QD 24個          │  1550nm直接、QFC不要
│  @ 2.5K                │
│                       │
│  PT205コールドヘッド    │  冷却能力 >10mW@2.5K
│  消費電力: 1.3kW       │  重量: 8.6kg
│  接続: 光ファイバ6本    │  RF (MKID) 6本
└───────────────────────┘
→ システム重量: 本体~28kg + コンプレッサー23kg(外付け床置き) = 合計~51kg,
  消費電力: ~2.1kW
```

**構成B（SNSPD 1,500個、GB [[144,12,12]]使用時 -- 元設計）**:

```
PT冷凍機一体型 (400mm W x 400mm D x 800mm H)
┌───────────────────────┐
│  WI-SNSPD 1,500-2,000個 │  検出効率 >92% → >99.7% (コム型適用時)
│  (WI-SNSPD)            │  NbN on SiN導波路
│  @ 2.5-4.2K            │
│                       │
│  PT冷凍機              │  CryoMech PT410相当 or PT205×2
│  コールドヘッド         │  到達温度 2.5K
│                       │
│  空冷コンプレッサ内蔵   │  消費電力 2.5kW
│                       │  重量 ~40kg
│  接続: 光ファイバ ~10本  │  RF信号線 <10本
└───────────────────────┘
→ システム重量: ~120kg, 消費電力: ~5kW
```

### 3.3 ラック間接続（ラック <-> 冷却ユニット）

| 接続 | 種類 | 本数 | 備考 |
|---|---|---|---|
| 光子入力 | SMF-28 1550nm | ~10本 | メイン遅延HCF出力 → SNSPD |
| MKID読み出し | 同軸RF | <10本 | 周波数多重で劇的削減 |
| バイアス電源 | DC配線 | 2本 | 一括供給 |
| 制御信号 | 同軸/光ファイバ | 5本 | クロック・同期・監視 |
| **合計** | | **~27本** | ケーブル1束で接続完了 |

Phase 0の8,320本光ファイバ+360本同軸から**99.7%削減**。
これがデスクトップ化の本質的実現要因。

---

## 4. 小型化の技術階段（Phase 2 → デスクトップQC）

### 4.1 Phase 2からの差分

Phase 2の1ラック+外部冷却構成を基盤とし、以下の追加技術でデスクトップQCを完成させる。

| 技術課題 | Phase 2（開始後約6年） | デスクトップQC（開始後約8-10年） | 差分 |
|---|---|---|---|
| **冷却水** | 水冷チラー必要 | **空冷コンプレッサ** | チラー排除 |
| **QFC** | LNOI QFC η=0.75-0.82 | **On-chip QFC or QFC除去** | InP QD 1550nm直接 or 統合QFC |
| **SNSPD接続** | ファイバ結合 | **WI-SNSPD完全統合** | 結合損失消滅 |
| **遅延線** | 外部HCF + オンチップ | **クライオHCFスプール検討** | フィードスルー削除 |
| **制御** | FPGA×1 + ASIC | **SoC統合（FPGA+ASIC+CPU）** | ボード数1/3 |
| **較正** | ACP 3層（半自動） | **ACP 3層（全自動）+ ML自己較正** | 人的介入最小化 |
| **筐体** | ラック+外部冷却 | **一体型筐体（オプション）** | 搬入・設置の簡素化 |

### 4.2 技術成熟マトリクス

各技術の現在のTRLとデスクトップQCに必要なTRL。

| 技術 | 現在TRL | Phase 2必要TRL | デスクトップQC必要TRL | 成熟確率 | Critical Path |
|---|---|---|---|---|---|
| GaAs QD (925nm) | 4-5 | 6 | 7 | 85% | |
| Transfer Printing | 3-4 | 5 | **7** | 60% | **Yes** |
| LNOI+SiN統合PIC | 3-4 | 5 | **7** | 70% | **Yes** |
| WI-SNSPD | 3 | 5 | **7** | 55% | **Yes** |
| PT冷凍機(空冷) | 7 | 7 | **8** | 90% | |
| MKID読み出し | 3-4 | 5 | 6 | 65% | |
| デコーダASIC | 2-3 | 5 | 6 | 70% | |
| DNANF HCF | 4 | 5 | 6 | 80% | |
| Floquet Single-Shot | 3 | 5 | 6 | 75% | |
| GB [[144,12,12]] | 2-3 | 5 | 6 | 70% | |
| 自動較正(ACP) | 2 | 4 | **6** | 75% | |
| InP QD 1550nm直接 | 2-3 | — | 5 (option) | 40% | |

**Critical Path技術（3つ）**: Transfer Printing、LNOI+SiN統合PIC、WI-SNSPD
→ この3技術のうち2つ以上が成功すればデスクトップQCは実現可能。

### 4.3 統合確率評価

| シナリオ | 前提条件 | デスクトップQC実現確率 | 論理qubit数 |
|---|---|---|---|
| **Best** | 3 Critical Path技術すべて成功 | 40% | 100+ |
| **Likely** | 3技術中2つ成功 | 65% | 48-72 |
| **Minimum** | 3技術中1つのみ成功 | 80% | 12-24 |
| **Fallback** | 3技術すべて失敗 | — | デスクトップ不可、2ラック構成に後退 |

3技術すべて失敗する確率: (1-0.60)×(1-0.70)×(1-0.55) = 0.40×0.30×0.45 = **5.4%**
→ **デスクトップQCが何らかの形で実現する確率: ~95%**

---

## 5. ロードマップ

### 5.1 Phase体系の再定義

既存Phase体系にPhase 2.5「デスクトップQC」を追加する。

```
Phase 0a-0c  (開始後1-3年)  コンポーネント実証 → 最小論理qubit
    │
Phase 1      (開始後4-5年)  小型実用機 [2ラック+サイドカー, 5-6m²]
    │
Phase 2      (開始後6-7年)  次世代小型機 [1ラック+外部冷却, 4m²]
    │
Phase 2.5    (開始後8-10年) デスクトップQC [1ラック統合, ≤3m²]  ← 新規追加
    │
Phase 3      (開始後11年-)  マルチノード / スケールアウト
    │
Ultimate     (開始後約20年-) 個人量子デバイス
```

### 5.2 Phase 2.5 マイルストーン

| 時期 | マイルストーン | Go/No-Go判定基準 | 投資額 |
|---|---|---|---|
| **開始後8年 Q1** | WI-SNSPD ~1,000個の安定動作（Phase 2実機で検証） | 検出効率>90% @ 4.2K、歩留>85% | 約3,000万円 |
| **開始後8年 Q3** | 空冷PT冷凍機プロトタイプ | 2.5K到達、振動<3μm p-p、騒音<60dBA | 約2,250万円 |
| **開始後9年 Q1** | クライオPICモジュール（QD+PIC+WI-SNSPD一体型）α版 | η>0.65、48論理qubit動作 | 約4,500万円 |
| **開始後9年 Q3** | 42Uラック統合プロトタイプ | 全機能収容、設置3日以内 | 約3,000万円 |
| **開始後10年 Q1** | デスクトップQC β版（社内運用開始） | 連続稼働>720h（30日）、リモート保守実証 | 約2,250万円 |
| **開始後10年 Q3** | デスクトップQC 製品版（初号機出荷） | 全スペック目標達成、CE/UL認証 | — |
| | **Phase 2.5 追加投資合計** | | **約1.5億円** |

### 5.3 累積投資計画（更新版）

| Phase | 期間 | 投資額 | 累計 | 成果物 |
|---|---|---|---|---|
| Phase 0a-0c | 開始後1-3年 | 約3.9億円 | 約3.9億円 | 最小論理qubit実証 |
| Phase 1 | 開始後4-5年 | 約3.8〜4.5億円 | 約7.7〜8.4億円 | 小型実用機（5-6m²） |
| Phase 2 | 開始後6-7年 | 約2.3億円 | 約9.9〜10.7億円 | 次世代小型機（4m²） |
| **Phase 2.5** | **開始後8-10年** | **約1.5億円** | **約11.4〜12.2億円** | **デスクトップQC（≤3m²）** |

Phase 2→2.5の追加投資が約1.5億円と小さいのは、Phase 2のハードウェア基盤をそのまま活用し、
「統合・小型化・自動化」のエンジニアリングが中心であるため。

---

## 6. 小型化の5つの技術レバー（定量分析）

### 6.1 レバー1: 冷却系の空冷化

| 項目 | Phase 2 | デスクトップQC | 改善 |
|---|---|---|---|
| 冷却方式 | PT冷凍機 + 水冷チラー | PT冷凍機 + **空冷コンプレッサ** | チラー排除 |
| 冷却水 | 必要（15L/min） | **不要** | 設置工事大幅削減 |
| コンプレッサ消費電力 | 2.5kW | 3.0kW（空冷のため微増） | +0.5kW |
| コンプレッサ重量 | 30kg + チラー20kg = 50kg | 35kg（一体型） | -15kg |
| 設置面積（冷却系） | 0.16m² + チラー0.25m² | **0.20m²** | -0.21m² |

**実現要件**: SNSPD数を1,500個以下に抑え、4Kステージ熱負荷を0.8W以下にすること。
MKID読み出し（熱負荷65mW）の導入が前提。

**リスク**: 空冷コンプレッサの騒音が55dBAを超過する可能性
（対策: 防音エンクロージャ+約150万円）。

### 6.2 レバー2: WI-SNSPD + クライオPIC統合

| 項目 | Phase 2 | デスクトップQC | 改善 |
|---|---|---|---|
| SNSPD結合方式 | ファイバ結合 | **導波路集積（WI-SNSPD）** | 結合損失 0.29dB→0.04dB |
| SNSPD-PIC間接続 | ファイバ×1,500本 | **オンチップ（接続0本）** | 配線99.9%削減 |
| 4K→室温間配線 | MKID RF <10本 | MKID RF <10本 | 同等 |
| η（検出段） | 0.92 | **0.99** | +7.6% |
| 全系η | 0.70 | **0.77** | 3技術成功時 |

### 6.3 レバー3: QFC除去（InP QD 1550nm直接発光）

| 項目 | Phase 2（QFCあり） | デスクトップQC（QFC除去時） | 改善 |
|---|---|---|---|
| QFC損失 | 0.75-0.82 | **1.0（QFCなし）** | +1.2-2.5dB回復 |
| 全系η | 0.70 | **0.80+** | 顕著な改善 |
| 部品点数 | QFCチップ×8 + ポンプレーザ×4 | **削除** | -12部品 |
| コスト削減 | — | **約-1,800万円** | QFC+ポンプレーザ分 |
| ラック占有 | 2U | **0U** | 2U空き |

**ただしInP QD 1550nmの成熟確率は40%**
（g²(0)<0.01かつV>0.95の同時達成未報告）。
Go/No-Go判定はPhase 1末（開始後約5年）。

QFC除去のGo判定: InP QD単体で V > 0.93 かつ g²(0) < 0.02 を達成した場合。
No-Go時: On-chip QFC（LNOI導波路をPIC上に統合）で対応。η=0.82は確保。

### 6.4 レバー4: DNANF + クライオHCFスプール

| 項目 | Phase 2 | デスクトップQC | 改善 |
|---|---|---|---|
| HCF種類 | NANF | **DNANF** | 損失1/3、曲げ半径1/3 |
| スプール直径 | 10cm | **7cm**（DNANF曲げ半径5cm） | -30% |
| スプール配置 | ラック内（室温） | **クライオ内（4.2K）オプション** | フィードスルー削除 |
| 全スプール体積 | 4U | **3U** | -1U |

### 6.5 レバー5: 制御系SoC統合

| 項目 | Phase 2 | デスクトップQC | 改善 |
|---|---|---|---|
| 制御ボード | FPGA×1 + ASIC×1 + CPU×1 | **SoC 1チップ** | ボード3枚→1枚 |
| 消費電力 | 0.5kW | **0.2kW** | -60% |
| ラック占有 | 4U | **2U** | -2U |

**SoCアーキテクチャ**: Xilinx Versal AI EdgeのようなFPGA+ARM+AIエンジン統合チップに、
デコーダASICをチップレット実装。
開始後約8年時点のプロセスノード（3-5nm）で十分実現可能。

---

## 7. BoM（デスクトップQC製品版）

### 7.1 部品リスト

| カテゴリ | 品目 | 数量 | 単価(万円) | 小計(万円) |
|---|---|---|---|---|
| **光源** | QDモジュール（Transfer Printing統合型） | 64-80 | — | 3,000 |
| | On-chip QFC（またはQFC除去） | 8 | — | 750 |
| | パルス励起レーザ | 2 | 225 | 450 |
| | 小型4Kクーラー（QD用） | 1 | 450 | 450 |
| **光学** | モノリシックPIC（LNOI+SiN） | 2-3 | 750 | 1,800 |
| | EO集積チップ | 4 | 150 | 600 |
| **遅延線** | DNANF HCF 200m×50本 | 50 | 7.5 | 375 |
| | SiNオンチップ遅延（PIC内） | — | — | (PIC内) |
| **検出** | WI-SNSPD一体型モジュール | 1,500 | 0.75 | 1,125 |
| | PT冷凍機（空冷コンプレッサ付） | 1 | 900 | 900 |
| | MKID読み出し回路 | 1式 | — | 450 |
| **制御** | SoC（FPGA+ASIC+CPU） | 1 | 300 | 300 |
| | ネットワーク・ストレージ | 1式 | — | 150 |
| **筐体・インフラ** | 42Uラック + 配線 | 1式 | — | 450 |
| | 光ファイバパッチパネル | 1式 | — | 150 |
| **SI** | 組立・較正・テスト | 1式 | — | 2,250 |
| | ソフトウェアライセンス | 1式 | — | 750 |
| | **合計** | | | **約1.4億円** |

**30%マージン込み: ~約1.8億円**（目標約1.5億円に対しやや超過。量産効果で約1.5億円以下を目指す）

### 7.2 コスト感度分析

| パラメータ | 基準値 | 変動 | コスト影響 |
|---|---|---|---|
| SNSPD単価 | 約7,500円/個 | ±50% | ±約560万円 |
| PICチップ数 | 3枚 | ±1枚 | ±約750万円 |
| QFC除去成功 | No | Yes | **約-1,200万円** |
| 量産規模 | 1台 | 100台/年 | **-40%（約8,400万円/台）** |

**最大コストドライバ**: 光源系（約4,650万円, 33%）とSI（約3,000万円, 22%）。
量産時はSIの自動化により約3,000万円→約750万円に削減可能。

---

## 8. 設置環境要件

### 8.1 要件比較（Phase 0 → デスクトップQC）

| 要件 | Phase 0 | デスクトップQC | 改善 |
|---|---|---|---|
| 床面積 | 60m²（専用室） | **3m²（サーバールーム内）** | **95%削減** |
| 天井高 | ≥3.0m | ≥2.5m（標準天井） | 一般オフィス対応 |
| 床荷重 | 500kg/m²（局所1000） | **300kg/m²** | 一般オフィスビル対応 |
| 室温 | 22±0.5℃ | 22±2.0℃ | 精密空調不要 |
| 湿度 | 40-60% RH | 30-70% RH | 一般空調で対応 |
| 振動 | VC-D（半導体fab相当） | **VC-C以下** | 一般オフィスビル対応 |
| 電源 | 3相200V, 60kVA | **単相200V, 30A (6kVA)** | 一般電源で対応 |
| 冷却水 | 60L/min | **不要** | 水配管工事不要 |
| クリーンレベル | ISO 7推奨 | **不要**（密閉型光路） | クリーンルーム不要 |
| EMI | RF機器持込制限 | 通常のサーバールーム | 特別な制限不要 |

**設置工事**: 電源コンセント1口 + LANケーブル1本で接続完了（理想形態）。

### 8.2 「箱出し」設置のための設計原則

1. **光路完全密閉**: すべての光路をPIC内またはコネクタ付きファイバで接続。端面露出なし → クリーンルーム不要
2. **自動アライメント**: Transfer Printing + WI-SNSPDにより個別光学調整ゼロ
3. **自己較正**: ACP 3層が起動時に全パラメータを自動較正。ML推論で経年劣化を補償
4. **リモート監視**: 全センサーデータをクラウドに送信。異常検知→自動退避→オンサイト保守依頼

---

## 9. リスクと対策

### 9.1 技術リスク

| リスク | 確率 | 影響 | 対策 | 検証時期 |
|---|---|---|---|---|
| WI-SNSPD歩留<80% | 30% | SNSPD数不足→論理qubit削減 | ファイバ結合SNSPDにフォールバック（+0.5ラック） | Phase 2 |
| 空冷PT振動>5μm | 25% | SNSPD結合不安定 | WI-SNSPDなら振動無関係（導波路統合のため）。ファイバ結合時はバッファガス対策 | Phase 2.5初期 |
| InP QD 1550nm No-Go | 60% | QFC除去不可 | On-chip QFCで対応（η=0.82確保）。コスト+約1,200万円 | Phase 1末 |
| デコーダASIC遅延 | 20% | FPGA継続使用（+0.3kW, +1U） | FPGA性能で十分。ASICは次世代での最適化 | Phase 2 |
| DNANF曲げ半径の長期信頼性 | 15% | NANF使用（スプール体積1.5倍） | Phase 2初期でDNANF加速寿命試験 | Phase 2 |

### 9.2 フォールバック構成

デスクトップQCが目標スペックを達成できない場合のフォールバック。

| レベル | 構成 | 床面積 | 論理qubit | 条件 |
|---|---|---|---|---|
| **A（目標）** | 42U×1 + 外部冷却 | 3.0m² | 48-100 | 3 Critical Path技術中2以上成功 |
| **B（縮退）** | 42U×1 + 外部冷却大型化 | 4.0m² | 24-48 | WI-SNSPD失敗→ファイバ結合SNSPD |
| **C（最小）** | 42U×1 + ハーフラック + 外部冷却 | 5.0m² | 12-24 | 統合PIC失敗→ディスクリートPIC |

レベルCでもPhase 0の60m²から**92%削減**であり、超伝導方式に対する圧倒的優位は維持。

---

## 10. 競合との差別化

### 10.1 開始後約10年時点の競合予測

| プレイヤー | 方式 | 予測スペック | デスクトップ可能性 |
|---|---|---|---|
| **Taros** | フォトニック | 48-100論理qubit, 3m², 5kW | **Yes** |
| IBM | 超伝導 | 1,000+論理qubit, 200m², 500kW | No（mK冷却必須） |
| Google | 超伝導 | 1,000+論理qubit, 150m², 400kW | No |
| PsiQuantum | フォトニック | 100+論理qubit, 50m², 50kW | No（大規模集中型設計） |
| Xanadu | フォトニック | 50-100論理qubit, 30m², 30kW | Possible（ただし小型化は非主軸） |
| QuiX | フォトニック(PIC) | 20-50論理qubit, 10m² | Possible |

**Tarosの差別化ポイント**: 「世界初のデスクトップ誤り訂正型光量子コンピュータ」を
明確な製品カテゴリとして確立。超伝導方式では原理的に到達不可能なフォームファクタ。

### 10.2 市場ポジショニング

```
                    論理qubit数
                        │
              1000+ ────┤         ○ IBM/Google
                        │         (大規模クラウド)
               100  ────┤  ★ Taros Deskside
                        │  (オンプレミス)
                50  ────┤
                        │
                10  ────┤
                        │
                    ────┼────────────────────── 設置面積
                        1m²   10m²  100m²  1000m²
```

**ターゲットセグメント**:
1. **金融機関**: ポートフォリオ最適化、リスク計算（レイテンシ要件でクラウド不可）
2. **製薬企業**: 分子シミュレーション（知的財産保護でオンプレミス必須）
3. **防衛・政府**: 暗号解析、最適化（セキュリティ要件）
4. **大学・研究機関**: 量子アルゴリズム研究（手元で実験したい）

---

## 11. 成功基準

### 11.1 Phase 2.5 成功基準

| レベル | 基準 | 達成確率 | 市場インパクト |
|---|---|---|---|
| **Level S（超過達成）** | 48+論理qubit、≤3m²、≤5kW、冷却水不要、約1.5億円以下 | 35% | 量子コンピュータ業界の再定義 |
| **Level A（完全達成）** | 24+論理qubit、≤4m²、≤6kW、約2.3億円以下 | 55% | 世界初デスクトップQC製品化 |
| **Level B（部分達成）** | 12+論理qubit、≤5m²、≤8kW | 75% | 超小型QCとしての技術実証 |
| **Level C（最低保証）** | エラー抑制実証、≤6m² | 90% | Phase 2からの明確な小型化進歩 |

### 11.2 製品としてのKPI

| KPI | 目標値 | 測定方法 |
|-----|---|---|
| MTBF（平均故障間隔） | ≥ 2,000時間 | 連続稼働ログ |
| 稼働率 | ≥ 95%（年間） | ダウンタイム集計 |
| 設置時間 | ≤ 3日 | 搬入→初回較正完了 |
| 較正時間（再起動後） | ≤ 4時間 | 冷却開始→量子計算準備完了 |
| リモート解決率 | ≥ 80% | 障害対応ログ |

---

## 12. 直ちに着手すべきアクション（デスクトップQC向け）

既存のPhase 0-2アクションに加え、デスクトップQCを見据えた追加アクション。

| 優先度 | アクション | 投資額 | 期間 | 実施Phase | 意思決定への影響 |
|---|---|---|---|---|---|
| **D1** | 空冷PT冷凍機の騒音・振動特性評価 | 約450万円 | 3ヶ月 | Phase 0b | 冷却水不要の実現可能性判定 |
| **D2** | WI-SNSPD 100個規模の歩留評価 | 約2,250万円 | 8ヶ月 | Phase 0c-1 | クライオPIC構成のGo/No-Go |
| **D3** | InP QD 1550nm のV・g²同時評価 | 約1,200万円 | 6ヶ月 | Phase 1 | QFC除去のGo/No-Go |
| **D4** | SoC統合デコーダのアーキテクチャ設計 | 約750万円 | 4ヶ月 | Phase 1 | 制御系の小型化・省電力設計 |
| **D5** | 密閉型光路モジュールの環境試験 | 約600万円 | 6ヶ月 | Phase 1-2 | クリーンルーム不要の実証 |
| **D6** | 自動較正ML（ACP Layer 3）の訓練 | 約450万円 | 12ヶ月 | Phase 1-2 | 「箱出し」設置の実現 |
| **D7** | デスクトップQC筐体の工業デザイン | 約300万円 | 3ヶ月 | Phase 2 | 製品としての外観・UX |
| | **合計** | **約6,000万円** | | | |

---

## 13. 20年ビジョンとの接続

```
開始後1-3年    Phase 0     最小論理qubit実証（60m², ラボ）
    │
開始後4-5年    Phase 1     小型実用機（5-6m², サーバールーム）
    │
開始後6-7年    Phase 2     次世代小型機（4m², サーバールーム）
    │
開始後8-10年 ★ Phase 2.5   デスクトップQC（≤3m², 一般オフィス）  ← 本書の主軸
    │
開始後11-13年   Phase 3     マルチノード（デスクトップQC ×10ノード = 1,000論理qubit）
    │
開始後14-17年   Phase 4     量子光チップ（モノリシック集積、チップ単価~1万円）
    │
開始後18-20年   Phase 5     個人量子デバイス（スマートフォンサイズ、室温動作SNSPD）
```

**デスクトップQCはPhase 3のビルディングブロック**:
マルチノード構成では、デスクトップQC同士を光ファイバで接続する。
10台のデスクトップQC（各48-100論理qubit）をエキスパンダーグラフ接続すれば、
480-1,000論理qubitの分散量子コンピュータが実現する。
これはフォトニック方式のネイティブな利点（光ファイバ接続の容易さ）を
最大限に活用するアーキテクチャである。

---

## Appendix A: 用語定義

| 用語 | 定義 |
|---|---|
| デスクトップQC | 42Uラック1本以内に全機能を収容した誤り訂正型量子コンピュータ |
| WI-SNSPD | Waveguide-Integrated SNSPD。SiN導波路上に直接NbN薄膜を堆積した検出器 |
| クライオPIC | QD光源+PIC+WI-SNSPDを2.5-4.2Kで一体動作させる統合フォトニクスモジュール |
| DNANF | Double Nested Anti-resonant Nodeless Fiber。損失0.064dB/km、曲げ半径5cm |
| MKID | Microwave Kinetic Inductance Detector。周波数多重読み出し方式 |
| ACP | Automatic Calibration Pipeline。3層自動較正パイプライン |
| SoC | System on Chip。FPGA+ASIC+CPUを1チップに統合 |

---

*本書はPQC-DESIGN-v4.0-R6を基盤とし、「デスクトップ量子コンピュータ」を主軸として再構成したものである。*
