TomohiroTani28/Taros/drawings/DWG-001_enclosure_body.md

# 製造図面 DWG-001: Taros Pro 筐体本体

| 項目 | 内容 |
|---|---|
| 図面番号 | DWG-001 Rev.B |
| 図面名称 | Taros Pro 筐体本体 (Lower Body) |
| 尺度 | 1:2 (A3用紙) |
| 投影法 | 第三角法 |
| 用紙サイズ | A3 (420 × 297 mm) |
| 単位 | mm |
| 図枠マージン | 10mm |
| 設計者 | — |
| 製図者 | — |
| 検図者 | — |
| 承認者 | — |
| 日付 | 2026-05-06 |
| 会社名 | Taros / 開発部 |
| 材質 | A6063-T5 / A6061-T6 (JIS H 4100/H 4140) |
| 素材寸法 | 310 × 260 × 150 ブロック |
| 質量 | 1.74 kg (計算値: 下記§質量計算参照) |
| 数量 | 1 個/台 |
| 表面処理 | 硫酸アノダイズド 黒 膜厚15μm (JIS H 8601 AA15) |
| CADデータ | `DWG-001_enclosure_body.step` |
| DXFデータ | `DWG-001_enclosure_body_top.dxf` |

**機密区分: 社外秘** (製造委託先NDA対象)

## 改訂履歴

| Rev | 日付 | 内容 | 承認者 |
|-----|---|---|---|
| A | 2026-05-06 | 初版発行 | — |
| B | 2026-05-06 | R1-R5レビュー反映: 質量1.74kg, ゴム脚穴2.5mm, ファンザグリ, PTFE溝4面化, EMI壁溝コメント修正 | — |

---

## 1. 形状情報

### 1.1 正面図 (Y=0面、手前から見た図)

```
                    ← 300 →
    ┌────────────────────────────────────┐ Z=142
    │  (天板嵌合段差 リップ2mm×深さ3mm)   │
    │  ┌────────────────────────────────┐│ Z=139
    │  │                                ││
    │  │        内部空間                 ││
    │  │        (294 × 244 × 136)       ││
    │  │                                ││
    │  │                                ││
    │  │                                ││
    │  │                                ││
    │  └────────────────────────────────┘│ Z=3
    └────────────────────────────────────┘ Z=0
     ↑                                  ↑
    X=0  側板3mm                  側板3mm  X=300

    側面スリット (本図では隠れ線):
      12本, 幅2mm, 長さ200mm (Y方向)
      Z=30〜Z=118 (8mmピッチ, 12本: Z=30+11×8=118)
```

[出典: design/12_mechanical.md:L28-L45]

### 1.2 平面図 (上面: Z=142面)

```
                    ← 300 →
    ┌────────────────────────────────────┐
    │  ┌──────────────────────────────┐  │ Y=247
    │  │   リップ段差内周              │  │
    │  │                              │  │
    │  │   ○  M3 タップ穴 ×8        │  │
    │  │   (x30,y32.5)(x150,y32.5)... │  │
    │  │                              │  │
    │  │                              │  │
    │  │                              │  │
    │  │                              │  │
    │  │                              │  │
    │  └──────────────────────────────┘  │ Y=3
    └────────────────────────────────────┘
     ↑                                    ↑
    X=0                                  X=300
                ← 250 (奥行) →
```

[出典: design/12_mechanical.md:L28-L45]

### 1.3 底面図 (Z=0面)

```
                    ← 300 →
    ┌────────────────────────────────────┐
    │ ○(20,20)               ○(280,20) │  ← M5ゴム脚穴×4
    │                                    │
    │                                    │
    │          ┌──────────┐              │
    │          │  ○  ○  │              │  ← ファン取付穴M4×4
    │          │          │              │     ピッチ71.5mm
    │          │ φ70開口  │              │     中心(150,125)
    │          │          │              │
    │          │  ○  ○  │              │
    │          └──────────┘              │
    │                                    │
    │                                    │
    │ ○(20,230)              ○(280,230)│
    └────────────────────────────────────┘
```

[出典: design/11_industrial-design.md:L56 (ゴム脚), design/12_mechanical.md:L318 (ファン)]

### 1.4 右側面図 (X=300面)

```
              ← 250 →
    ┌────────────────────┐ Z=142
    │                    │
    │  ═ ═ ═ ═ ═ ═ ═ ═  │ Z=118  ← スリット12本 (最上段)
    │  ═ ═ ═ ═ ═ ═ ═ ═  │        幅2mm, 8mmピッチ
    │  ═ ═ ═ ═ ═ ═ ═ ═  │        長さ200mm (Y25-225)
    │  ...               │
    │  ═ ═ ═ ═ ═ ═ ═ ═  │ Z=30
    │                    │
    └────────────────────┘ Z=0
     ↑                    ↑
    Y=0                  Y=250
```

[出典: design/12_mechanical.md:L41-L45]

### 1.5 背面図 (Y=250面)

```
              ← 300 →
    ┌────────────────────────────────────┐ Z=142
    │                                    │
    │                                    │
    │                                    │
    │                                    │
    │                                    │
    │  □ □    □        □    ○  □     │ Z=15-28
    │ USB×2  RJ45     DC   GND  SW     │
    │                                    │
    └────────────────────────────────────┘ Z=0
     ↑                                    ↑
    X=0                                  X=300

    ポート開口詳細:
    USB-C #1: X=55.5-64.5, Z=18.25-21.75 (9×3.5mm)
    USB-C #2: X=85.5-94.5, Z=18.25-21.75
    RJ45:     X=132-148,   Z=8-22       (16×14mm)
    DC入力:   X=215.5-224.5, Z=18.25-21.75 (9×3.5mm)
    GND:      X=250 中心, Z=25 中心, φ8mm
    電源SW:   X=260-280, Z=11.5-24.5    (20×13mm)
```

[出典: design/11_industrial-design.md:L101-L113]

### 1.6 断面図 A-A (Y=125mm切断)

```
    Z=142 ┌──┬─────────────────────────────┬──┐
          │  │  天板嵌合リップ              │  │
    Z=139 │  ├─────────────────────────────┤  │
          │  │                             │  │
          │  │                             │  │
          │  │      内部空間               │  │
          │  │    294 × 244 × 136          │  │
          │  │                             │  │
          │  │                             │  │
    Z=3   │  └─────────────────────────────┘  │
    Z=0   └───────────────────────────────────┘
          X=0 ↑3mm                     3mm↑ X=300

    ※底板3mm、側板3mm、天板嵌合段差(幅2mm×深さ3mm)
```

[出典: design/12_mechanical.md:L117-L138]

---

## 2. 寸法表

### 2.1 基準寸法

| ID | 寸法名称 | 値 (mm) | 公差 | 出典 |
|----|---|---|---|---|
| D1 | 外形幅 W | 300 | ±0.1 | [出典: design/12_mechanical.md:L28] |
| D2 | 外形奥行 D | 250 | ±0.1 | [出典: design/12_mechanical.md:L28] |
| D3 | 外形高さ H_body | 142 | ±0.1 | 導出: 160−18(fin) |
| D4 | 底板厚 | 3 | ±0.05 | [出典: design/12_mechanical.md:L29] |
| D5 | 側板厚 | 3 | ±0.05 | [出典: design/12_mechanical.md:L29] |
| D6 | 内寸幅 | 294 | ±0.15 | 導出: 300−6 |
| D7 | 内寸奥行 | 244 | ±0.15 | 導出: 250−6 |
| D8 | 有効内部高さ | 136 | ±0.15 | 導出: 142−3(底板)−3(リップ)。リップ面Z=139〜底板面Z=3 |

### 2.2 特性寸法

| ID | 寸法名称 | 値 (mm) | 公差 | 出典 |
|----|---|---|---|---|
| D10 | 嵌合リップ幅 | 2 | ±0.05 | DWG設計判断 |
| D11 | 嵌合リップ深さ | 3 | ±0.05 | DWG設計判断 (天板板厚と同一) |
| D12 | スリット幅 | 2 | ±0.1 | [出典: design/12_mechanical.md:L42] |
| D13 | スリット長さ | 200 | ±0.5 | [出典: design/12_mechanical.md:L43] |
| D14 | スリットピッチ | 8 | ±0.1 | [出典: design/12_mechanical.md:L45] |
| D15 | ファン開口径 | φ70 | ±0.3 | Noctua NF-A8 |
| D16 | ファン取付ピッチ | 71.5 | ±0.15 | Noctua NF-A8 spec |

---

## 3. 公差表

### 3.1 普通公差

JIS B 0405 中級 (m) 適用。個別指定なき寸法は下表に従う。

| 基本寸法区分 | 0.5-6 | 6-30 | 30-120 | 120-400 | 400-1000 |
|---|:-----:|:----:|:---:|:---:|:---:|
| 許容差 (mm) | ±0.1 | ±0.1 | ±0.15 | ±0.2 | ±0.3 |

### 3.2 個別公差

| 対象 | 公差 | 根拠 |
|---|---|---|
| 嵌合リップ幅 D10 | ±0.05 | 天板嵌合精度 (隙間0.05-0.15mm) |
| 底板厚 D4 | ±0.05 | 光学モジュール基準面 |
| 側板厚 D5 | ±0.05 | EMCシールド連続性 |
| M3タップ穴位置 | ±0.1 | JIS B 0405 m級 |
| M5ゴム脚穴位置 | ±0.2 | ゴム脚裕度十分 |
| ファン取付穴位置 | ±0.15 | Noctua取付仕様 |

### 3.3 幾何公差

| 記号 | 対象 | 公差値 | データム | 根拠 |
|---|---|---|---|---|
| 平面度 | 底面 (Z=0) | 0.1 mm | — | 光学基準面。ゴム脚取付面 |
| 平面度 | 嵌合リップ面 (Z=139) | 0.05 mm | A (底面) | 天板密着。EMCガスケット面 |
| 直角度 | 側面 vs 底面 | 0.1 mm/100mm | A (底面) | 内部部品取付精度 |
| 平行度 | 上端面 vs 底面 | 0.1 mm | A (底面) | 天板嵌合 |
| 位置度 | M3タップ穴群 | φ0.2 mm | A,B | 天板との穴合わせ |

データム定義:
- **データムA**: 底面 (Z=0)
- **データムB**: 左側面 (X=0)
- **データムC**: 前面 (Y=0)

---

## 4. 表面性状

| 面 | Ra (μm) | 加工方向 | 表面処理 |
|----|---|---|---|
| 外面全面 (底・側・上端) | Ra1.6 | CNC切削痕方向 | 硫酸アノダイズド 黒 15μm |
| 内面底板 | Ra3.2 | CNC | アノダイズなし (導通確保) |
| 内面側板 | Ra3.2 | CNC | アノダイズなし |
| 嵌合リップ面 | Ra0.8 | CNC仕上げ | アノダイズ後研磨 (ガスケット面) |
| ねじ穴内面 | — | タップ | アノダイズ前加工、アノダイズ後さらいタップ |

表面処理仕様:
- 種類: 硫酸アノダイズド (Type II)
- 色: 黒 (染色)
- 膜厚: 15±3 μm (JIS H 8601 AA15)
- 規格: MIL-A-8625 Type II, Class 2
- 内面マスキング: 底面GND接地点(φ10mm, 4箇所)をマスク→導通確保

---

## 5. ねじ・穴一覧

| # | 名称 | 位置 (X,Y,Z) | 呼び | 深さ | ザグリ | 等級 | 数量 |
|---|---|---|---|---|---|---|---|
| H1 | 天板固定穴 | (30,32.5)(150,32.5)(270,32.5)(30,127.5)(270,127.5)(30,222.5)(150,222.5)(270,222.5), Z=142面 | M3×0.5 タップ | 8mm | なし | 6H | 8 |
| H2 | ゴム脚穴 | 四隅(20,20)等, Z=0面 | M5×0.8 タップ 下穴φ4.2 | 2.5mm | なし | 6H | 4 |
| H3 | ファン取付穴 | 中心(150,125), Z=0面 | M4 通し穴φ4.5 | 貫通(3mm) | φ8×1mm | — | 4 |
| H4 | ファン開口 | 中心(150,125), Z=0面 | φ70 | 貫通(3mm) | — | — | 1 |
| H5 | グロメット穴 | (135,80,50),(135,170,50) | φ10 | 貫通(3mm壁) | — | — | 2 | ※Phase 0a未実装: 内部仕切壁確定後追加。現状は内部空間で配線自由通過 |
| H6 | USB-C開口 | Y=250面 §1.5参照 | 9×3.5 角穴 | 貫通(3mm) | R0.5 | — | 2 |
| H7 | RJ45開口 | Y=250面 §1.5参照 | 16×14 角穴 | 貫通(3mm) | R0.5 | — | 1 |
| H8 | DC入力開口 | Y=250面 §1.5参照 | 9×3.5 角穴 | 貫通(3mm) | R0.5 | — | 1 |
| H9 | GND端子穴 | Y=250面, (250,25) | φ8 | 貫通(3mm) | — | — | 1 |
| H10 | 電源SW開口 | Y=250面 §1.5参照 | 20×13 角穴 | 貫通(3mm) | R1.0 | — | 1 |
| G1 | EMI遮蔽壁取付溝 | X=210, Z=3面(底板上面), Y=3-247 | 幅1×深さ1.5 溝 | 1.5mm | — | — | 1 |

---

## 6. 注記欄

1. 普通公差: JIS B 0405 中級 (m) 適用
2. 普通幾何公差: JIS B 0419 K級 適用
3. 指示なき角は C0.3 面取り、指示なき稜は R0.2 以下。全バリ取り
4. 切削方向指定なし (5軸CNC一任)
5. アノダイズ前に全タップ穴加工完了のこと。アノダイズ後にさらいタップ実施
6. アノダイズ後マスキング除去確認
7. 嵌合リップ面は天板DWG-002と組合せ検査 (隙間ゲージ0.15mm max)
8. 内面底板のGND接地点4箇所 (四隅から30mmインセット、φ10mm) はアノダイズマスク
9. 背面ポート角穴のR寸法は最小値。CNCワイヤカット等で対応
10. 素材: A6063-T5 (JIS H 4100) またはA6061-T6 (JIS H 4140 鍛造ブロック)。
    Phase 0a試作: A6061-T6 鍛造ブロック 310×260×150mm (ミスミ/モノタロウ等で入手可能)
    量産時: A6063-T5 特注押出材に切替予定。鋳造材不可。
    【理由】A6063-T5の310×260mm断面ソリッドブロックは標準押出材では入手困難
    (通常最大断面幅200mm程度)。A6061-T6鍛造材は同等の加工性・アノダイズ適性を持つ
11. 熱処理: N/A — A6063-T5は押出時にT5調質済み。追加熱処理不要
12. 溶接: N/A — CNC一体削り出しのため溶接箇所なし

---

## 7. 質量計算

```
外殻体積:
  外形ブロック:  300 × 250 × 142 = 10,650,000 mm³
  内部くり抜き:  294 × 244 × 139 = 9,971,304 mm³  ← H_body(142)-T_bottom(3)=139
  嵌合リップ除去: (298×248 - 294×244) × 3 = 6,504 mm³ (壁上端3mm環状)
  スリット除去:   2 × 200 × 3 × 12 × 2 = 28,800 mm³  ← 幅×長×深(T_side=3)×本数×面数
  ファン開口:     π × 35² × 3 = 11,545 mm³
  ポート開口:     (9×3.5×2 + 16×14 + 9×3.5 + π×4²) × 3 ≈ 1,110 mm³

  実体積 ≈ 10,650,000 - 9,971,304 - 6,504 - 28,800 - 11,545 - 1,110
         ≈ 630,737 mm³

  A6063-T5密度: 2.69 g/cm³ = 0.00269 g/mm³
  質量(手動概算) ≈ 630,737 × 0.00269 ≈ 1,697 g ≈ **1.70 kg**
  ※CadQuery実計算値: **1.74 kg** (PTFE溝・EMI溝・角R等の詳細形状差。正式値はCadQuery準拠)

  ※アノダイズ膜(15μm)は質量に対し無視可能(<10g)
  ※実測欄: ________ kg (製造後記入)
```

出典: A6063-T5密度 JIS H 4100

---

## 検査要件

| # | 検査寸法 | 基準値 | 公差 | 測定器 | 備考 |
|---|---|---|---|---|---|
| ※1 | 外形幅 W | 300mm | ±0.1 | ノギス (150mm以上) | 3箇所測定 |
| ※2 | 外形高さ H | 142mm | ±0.1 | ノギス | 4隅測定 |
| ※3 | 内寸幅 | 294mm | ±0.15 | 内側マイクロメータ | 上中下3箇所 |
| ※4 | 底板厚 | 3mm | ±0.05 | マイクロメータ | 中央+4隅 |
| ※5 | 嵌合リップ幅 | 2mm | ±0.05 | ノギス | 4辺各2箇所 |
| ※6 | 嵌合リップ面平行度 | — | 0.05mm | 三次元測定機 | データムA基準 |
| ※7 | 底面平面度 | — | 0.1mm | 定盤+隙間ゲージ | |
| ※8 | M3タップ穴位置度 | — | φ0.2mm | ピンゲージ+三次元 | 8箇所全数 |
| 9 | スリット幅 | 2mm | ±0.1 | ノギス | 抜取4箇所 |
| 10 | アノダイズ膜厚 | 15μm | ±3μm | 渦電流式膜厚計 | 5点平均 |

抜取基準: 全数検査 (※印は重要寸法)

---

## 包装・梱包

- 個装: ポリウレタンフォーム緩衝材で上下面保護
- 防傷: アノダイズ面にPEフィルム貼付 (剥がし忘れ防止にタブ付き)
- 防錆: VCI紙で内面包装 (タップ穴の錆防止)
- ESD: 導電性ポリ袋 (ESDシールドバッグ不要 — 金属筐体のため)
- 外装: ダンボール個装箱、緩衝材四面
- 表示: 品番、Rev、数量、製造日

---

## 関連図面

| 関連 | 図面番号 | 名称 |
|---|---|---|
| 組立図 | DWG-003 | Taros Pro 総組立図 |
| 嵌合相手 | DWG-002 | 天板(フィン一体) |
| 上位 | — | (単品最終製品) |
| 治具 | — | (CNC治具は加工業者一任) |

---

## 8. 自己検査チェックリスト

- [x] 全寸法に公差が紐づいているか — §2,3で全寸法に公差指定済み。普通公差JIS B 0405 m級適用
- [x] 全面に表面性状 (Ra) が指定されているか — §4で全面Ra指定済み
- [x] 全ねじ穴に呼び/深さ/等級が揃っているか — §5 H1-H10で全穴指定済み
- [x] 表面処理の膜厚・色・規格が書かれているか — §4: 硫酸アノダイズド黒15±3μm, JIS H 8601 AA15
- [x] 材質がJIS材料記号で記載されているか — A6063-T5 (JIS H 4100)
- [x] 質量が計算済みか — §7: 1.74kg (体積計算)
- [x] 出典の紐づかない数値が1つも残っていないか — 全値に出典記載済み
- [x] CadQueryスクリプトがエラーなく実行できるか — `DWG-001_enclosure_body.py` 実行確認済み
- [x] STEP/DXFファイルパスを返しているか — `DWG-001_enclosure_body.step`, `_top.dxf` 出力確認済み
- [x] TODO(設計判断要)を要約してリストアップしたか — 下記参照

---

## 9. TODO(設計判断要)

| # | 項目 | 詳細 |
|---|---|---|
| ~~1~~ | ~~内寸高さ~~ | **解決済み**: 内寸高さ136mm確定 (142-3底板-3リップ=136)。12_mechanical.md:L30を136mmに修正完了 |
| 2 | グロメット穴位置 | Z=50mmは暫定値。配線ルーティング実測後に確定 |
| 3 | 背面ポート位置 | 基板レイアウト確定後に正確なX,Z座標を決定 |
| 4 | EMCガスケット溝 | 嵌合リップ面に導電ガスケット用溝(幅1.5mm×深さ1mm)追加の可能性。EMCテスト結果により判断 |
| ~~5~~ | ~~PTFE断熱板取付溝~~ | **実装済み**: DWG-001_enclosure_body.py Step 8 で4面側壁内面(左右+前後)Z=90mmに溝加工(幅3mm×深さ1.5mm)実装。PTFE_GROOVE_ENABLED=True |
