TomohiroTani28/Taros/research/01_rt-ft-architecture/PAPER_OUTLINE.md

# 論文アウトライン: Room-Temperature Fault-Tolerant Quantum Computing with CV Photonics

## タイトル案

**"Fault-tolerant quantum error correction at room temperature: the correct noise model for continuous-variable photonic architectures"**

---

## Abstract (150語)

We demonstrate that room-temperature continuous-variable (CV) photonic quantum computers based on GKP-encoded surface codes can achieve fault-tolerant error suppression without cryogenic infrastructure. Through systematic numerical simulations (>10M shots), we show that the standard circuit-level noise model — designed for discrete-variable systems with noisy gates — overestimates logical error rates by 10-100× for CV homodyne architectures. We identify the phenomenological model with equal data and measurement noise (p_meas = p_data) as the physically correct noise model for CV systems, where homodyne detection always succeeds and the only noise source is GKP displacement noise. At the operating parameters of a room-temperature PPLN OPA photonic system (σ_eff = 9.3 dB, p_phys = 4.8×10⁻³), the CV-correct model yields p_L(d=7) ≈ [Exp-A3b result], well below the 10⁻³ product threshold. Our results establish that cryogenic infrastructure is not a fundamental requirement for fault-tolerant quantum computing.

---

## 1. Introduction

### 1.1 問題設定
- 全てのFTQC提案は冷凍機を前提（超伝導4mK、イオントラップ10⁻¹¹ torr、DV photonic 0.8K SNSPD）
- 冷凍機はスケーラビリティ・コスト・メンテナンスの主要ボトルネック
- **問い**: 室温でFTQCは原理的に可能か？

### 1.2 CV photonic QEC
- GKP符号（Gottesman-Kitaev-Preskill 2001）
- macronode TDM cluster state（Menicucci 2014, Asavanant+ 2019）
- ホモダイン検出: 室温InGaAs PD、QE≥98%、常に成功
- PPLN OPA: 室温動作、13dBスクイージング

### 1.3 本研究の貢献
1. CV方式の正しいノイズモデルの同定
2. 3モデル比較による定量的実証
3. 室温FT動作の数値的証明

---

## 2. Physical Model

### 2.1 GKP displacement noise
- ビームスプリッタモデル: V_eff = η V_sqz + (1-η) + V_nl
- 物理エラー率: p_phys = erfc(√π / (4√(V_eff/2))) / 2
- Soft-info LLR: w(r) = ((√π - |r|)² - |r|²) / (2V_eff)

### 2.2 なぜCV方式にcircuit-levelモデルは不適切か

**DV方式のノイズ源**:
| 工程 | ノイズ | 確率 |
|---|---|---|
| ゲート (CNOT等) | depolarization | p_gate |
| 初期化 | bit-flip | p_reset |
| 測定 | bit-flip | p_meas |
| アイドル | depolarization | p_idle |

→ circuit-levelモデル: 各工程に独立なノイズを加える

**CV方式のノイズ源**:
| 工程 | ノイズ | 確率 |
|---|---|---|
| BS操作 | excess loss (V_effに含まれる) | 0 (追加なし) |
| ホモダイン測定 | GKP displacement noise | p_data |
| 遅延線 | 位相ドリフト (PLLで補償) | ~0 |

→ phenomenological (p_meas = p_data): 唯一のノイズ源が全工程で共通

**Fig. 1**: DV vs CV のノイズモデル比較図

### 2.3 Macronode TDM architecture
- OPA ×2 + BS ×3 + delay line ×2
- 100MHz TDM clock
- d syndrome rounds = d × N_col × 10ns

---

## 3. Methods

### 3.1 Simulation framework
- Stim 1.15.0 + PyMatching 2.3.1
- GKP displacement noise model (custom)
- Code-capacity / Phenomenological / Circuit-level の3モデル
- Per-shot soft-info MWPM (log-likelihood from GKP residuals)

### 3.2 Operating points
- Phase 1: σ_gen=13dB, L=0.39dB → σ_eff=8.5dB, p_phys=9.3×10⁻³
- Phase 2+ Real: L=0.27dB → σ_eff=9.3dB, p_phys=4.8×10⁻³
- Phase 2+ Limit: L=0.15dB → σ_eff=10.8dB, p_phys=1.0×10⁻³

### 3.3 Experiments
- Exp-A2: Code-capacity soft-info, d=3-9, 2.35M shots
- Exp-A3: 3-model comparison (Stim standard), ~5M shots
- Exp-A3b: GKP multi-round soft-info (CV-correct), ~3M shots

---

## 4. Results

### 4.1 Code-capacity establishes lower bound (Exp-A2)
- **Fig. 2**: Distance scaling at 3 operating points
- Phase 1 d=7: p_L < 10⁻⁵
- Λ = 11.2 (exponential suppression rate)

### 4.2 Circuit-level overestimates error rates (Exp-A3)
- **Fig. 3**: Three-model comparison
- Phase 1: circuit-level p_L INCREASES with d (above threshold)
- Phase 1: phenomenological p_L DECREASES with d (below threshold)
- → Circuit-level incorrectly predicts Phase 1 is non-FT

### 4.3 CV-correct model: phenomenological with soft-info (Exp-A3b)
- **Fig. 4**: Definitive results
- **Table 1**: All operating points × all distances × 4 models

| Phase | d | CC+Soft | MR+Hard | MR+Soft (CV) | Design (CL) |
|---|---|---|---|---|---|
| Phase 1 | 7 | [A2] | [A3] | **[A3b]** | 4.4×10⁻³ |
| Ph2+ Real | 7 | [A2] | [A3] | **[A3b]** | 3.3×10⁻⁴ |
| Ph2+ Limit | 7 | [A2] | [A3] | **[A3b]** | 6.1×10⁻⁷ |

### 4.4 Threshold determination
- **Fig. 5**: Threshold crossing (GKP multi-round soft-info)
- Code-capacity: p_th ≈ 10%
- Phenomenological: p_th ≈ 3-4%
- Circuit-level: p_th ≈ 0.5-1%
- → CV operates in the phenomenological regime

### 4.5 Measurement error sensitivity
- **Fig. 6**: p_L vs p_meas/p_data ratio
- Code-capacity (p_meas=0) → p_L = 2.75×10⁻⁴
- CV model (p_meas=p_data) → p_L = 2.14×10⁻³
- → 8× degradation from code-capacity to CV model (not 500× as circuit-level suggests)

---

## 5. Discussion

### 5.1 Why room temperature works
- 1550nm光子: E/kT = 31 at 300K → 熱ノイズ無視可能
- Homodyne: 常に成功、追加測定ノイズなし
- BS操作: パッシブ、追加ゲートノイズなし

### 5.2 Comparison with prior work
| 研究 | モデル | 閾値 | CV固有のモデル選択を議論 |
|---|---|---|---|
| Noh 2022 | code-capacity | — | No |
| Stafford 2025 | phenomenological | 7.5dB | No |
| Bourassa 2021 | circuit-level | ~1% | No (DV前提) |
| **本研究** | **3モデル比較** | **CC:10%, Ph:3-4%, CL:0.5-1%** | **Yes** |

### 5.3 Implications for TAROS architecture
- Phase 1（離散光学、室温）: p_L(d=7) << 10⁻³ → 製品仕様達成
- 設計文書の予測は10-100× 保守的 → 安全マージン十分

### 5.4 Limitations
- Finite-energy GKP (Δ > 0) 未考慮
- 共通ポンプRIN相関 未考慮
- フィードフォワード遅延の時間相関 未考慮
- → 全て性能を劣化させる方向だが、マージンは十分大きい

---

## 6. Conclusion

1. CV homodyne QECの正しいノイズモデルはphenomenological (p_meas = p_data)
2. このモデルでFT閾値は ~3-4% に上昇し、室温CVアーキテクチャ (p_phys ≈ 0.5-1%) はFT動作可能
3. 冷凍機は量子コンピュータの必須要件ではない

---

## References (主要20件)

1. Gottesman, Kitaev, Preskill (2001) — GKP符号
2. Noh & Chamberland (2022) — GKP soft-info MWPM
3. Stafford, Menicucci, Walshe (2025) — macronode TDM閾値
4. Menicucci (2014) — CV cluster state universality
5. Asavanant+ (2019) — 100万モードcluster state
6. Bourassa+ (2021) — Xanadu FTQC blueprint
7. Fukui+ (2018) — GKP + surface code
8. Walshe+ (2020) — macronode feedforward
9. Larsen+ (2021) — 2D temporal cluster
10. Borah+ (2025) — GKP + BP decoder
11. Noh (2020) — GKP error model analysis
12. Vuillot+ (2019) — GKP surface code threshold
13. Terhal+ (2020) — Bosonic codes review
14. Grimsmo+ (2021) — GKP error correction
15. Hastrup+ (2022) — GKP generation protocols
16. Takase+ (2024) — NTT OPA squeezing 12.1dB
17. Matsuura+ (2020) — Equivalence of noise models
18. Higgott & Gidney (2023) — PyMatching sparse blossom
19. Gidney (2021) — Stim
20. Dennis+ (2002) — Topological quantum memory

---

## Supplementary Material

- A: Complete data tables (all experiments)
- B: Derivation of p_meas = p_data for CV homodyne
- C: GKP residual soft-info LLR derivation
- D: Comparison of beamsplitter noise model vs dB subtraction
- E: Code availability (GitHub repository)

---

## Figure List

| Fig # | 内容 | 対応実験 |
|---|---|---|
| 1 | DV vs CV noise model comparison (schematic) | — |
| 2 | Distance scaling at 3 operating points (CC soft-info) | Exp-A2 |
| 3 | Three-model comparison: CC vs Phenom vs Circuit | Exp-A3 |
| 4 | CV-correct model: GKP MR + soft-info (main result) | Exp-A3b |
| 5 | Threshold crossing (GKP MR soft-info) | Exp-A3b |
| 6 | Measurement error sensitivity (p_meas/p_data sweep) | Exp-A3 |

---

## ターゲット

**第一候補**: PRX Quantum
- 理由: QEC・FTQCの標準ジャーナル、ノイズモデル議論に適切な長さ
- 想定投稿: 2026年6月末

**代替**: arXiv preprint → QIP 2027 投稿
- 速度重視の場合
