TomohiroTani28/Taros/design/08_decoder.md

# GKP→表面符号デコーダ ブリッジ仕様書

**Document ID**: PQC-CV-DECODER-v1.4
**Status**: Draft
**前提**: macronode TDM + GKP postselection + 表面符号 d=3-7

---

## 1. デコーダの全体構造

### 1.1 2段デコーダアーキテクチャ

```
ホモダイン測定値 q_meas (analog → 14bit digital)
    │
    ▼ (ADC output, 100MHz stream)
╔══════════════════════════════════════════════╗
║ Stage 1: GKP内部デコーダ (TIA+ADC+FPGA, 18.5ns) ║
║                                              ║
║  (a) 格子点マッピング:                        ║
║      q_grid = round(q_meas / √π) × √π       ║
║      bit = (q_grid / √π) mod 2              ║
║                                              ║
║  (b) ソフト情報抽出:                          ║
║      δ = q_meas - q_grid  (格子からの偏差)    ║
║      p_err_i = erfc(|δ| / (σ√2)) / 2        ║
║      → 近似: p_err_i ≈ exp(-δ²/σ²) × C     ║
║                                              ║
║  出力: {bit_i, p_err_i} for each mode i      ║
╚══════════════════════════════════════════════╝
    │
    │ (100kHz effective rate after postselection)
    ▼
╔══════════════════════════════════════════════╗
║ Stage 2: 表面符号デコーダ (FPGA, <500ns)     ║
║                                              ║
║  (a) シンドローム計算:                        ║
║      s_j = XOR(bit_i : i ∈ stabilizer_j)    ║
║                                              ║
║  (b) 重み付きUnion-Find:                      ║
║      クラスタ重み w_i = -log(p_err_i)        ║
║      成長優先度 ∝ 1/w_i                      ║
║      線形時間デコーディング                     ║
║                                              ║
║  (c) 論理パウリ補正:                          ║
║      マッチング結果からパウリフレーム更新        ║
║                                              ║
║  出力: logical_bit + correction              ║
╚══════════════════════════════════════════════╝
    │
    ▼
論理qubit値 (corrected)
```

### 1.2 DV方式デコーダとの本質的差異

| 項目 | DV方式 (erasure) | **CV方式 (GKP soft info)** |
|---|---|---|
| 入力 | binary (検出/非検出) | **continuous (ホモダイン値)** |
| エラーモデル | erasure + depolarizing | **Gaussian displacement noise** |
| 情報量 | 1 bit/measurement | **14 bits/measurement** |
| デコーダ入力 | syndrome (binary) | **syndrome + confidence (real-valued)** |
| 閾値改善 | Belief Matching +4.6pt | **ソフト情報で+3-5dB効果** |

**CV方式の決定的優位**: ホモダインは「どれだけ格子点からずれたか」を連続的に知らせる。この**アナログ情報**を表面符号デコーダに渡すことで、binary syndromeのみのDV方式より高い訂正能力を得る。

---

## 2. Stage 1: GKP内部デコーダ

### 2.1 格子点マッピング（ハードデシジョン）

GKP符号空間での0/1判定:

```
|0_GKP> ↔ q = 2n√π     (n = 0, ±1, ±2, ...)
|1_GKP> ↔ q = (2n+1)√π (n = 0, ±1, ±2, ...)

判定: bit = floor((q_meas / √π) + 0.5) mod 2
```

FPGA実装:
- √π ≈ 1.7724538 → 固定小数点16bit表現
- 除算 → 乗算+シフト（1/√π ≈ 0.5641896）
- mod 2 → LSB抽出

**レイテンシ: 2 FPGA cycles × 2.5ns = 5ns (@400MHz)** / 2 cycles × 2ns = 4ns (@500MHz楽観)

### 2.2 ソフト情報抽出

格子点からの偏差（アナログシンドローム）:

```
q_grid = round(q_meas / √π) × √π
δ = q_meas - q_grid        (range: -√π/2 to +√π/2)

信頼度:
p_err = (1/2) × erfc(|δ| × √(π/2) / σ_eff)

※注: p_err_iは個別モードiの条件付きエラー確率（δ_iに依存）。13_performance.mdのp_phys = erfc(√π/(4σ))/2は全モード平均エラー率。

近似（FPGA向け）:
p_err ≈ (1/2) × exp(-π × δ² / (2 × σ_eff²))
```

| δ/σ_eff | p_err | 信頼度 | 意味 |
|---|---|---|---|
| 0 | 最小 (~10⁻⁴) | 最高 | 格子点ど真ん中 |
| 0.5 | ~0.01 | 高 | やや偏差 |
| 1.0 | ~0.08 | 中 | 中程度偏差 |
| 1.5 | ~0.25 | 低 | 判定が危うい |
| √π/2 | ~0.50 | 最低 | 境界上（ランダム推測） |

FPGA実装:
- exp(-x²)のLUT: 256エントリ、8bit出力 → BRAM 256B
- σ_eff²は定数（較正時に設定）
- **レイテンシ: 3 cycles × 2.5ns = 7.5ns (@400MHz)** / 3 cycles × 2ns = 6ns (@500MHz楽観)

### 2.3 Stage 1合計レイテンシ

```
TIA: (3ns, アナログ, FPGA外)
Flash ADC取得: 1 cycle (**3ns**, デバイス物理遅延, 07_feedforward.md §2.2準拠)
格子点マッピング: 2 cycles (**5ns** @400MHz)
ソフト情報: 2 cycles (**5ns** @400MHz)
───────────────────────────
合計: TIA 3ns + ADC 3ns + FPGA 5 cycles×2.5ns (12.5ns) = **18.5ns** (@400MHz) / 13ns (@500MHz)
(07_feedforward.md §2.2準拠: TIA 3ns + ADC 3ns + FPGA 12.5ns = 18.5ns @400MHz)
```

---

## 3. Stage 2: 表面符号デコーダ（ソフト情報入力）

### 3.1 表面符号格子での配置

d=7表面符号: 49 data qubits + 48 ancilla = 97 qubits

TDMでの配置:
```
1 syndrome round = 14 time modes × 7 columns = 98 modes
QECサイクル = 7 rounds (d=7のsingle-shot近似)
合計: 98 × 7 = 686 modes per QEC cycle
時間: 686 × 10ns = 6.86μs
```

### 3.2 表面符号デコーダ: MWPM（製品）+ UF（実験用ベースライン）

**製品デコーダ: MWPM (Blossom-V) d=7、510ns @400MHz。**
**実験用ベースライン: Union-Find (UF) d=7、350ns @400MHz。**

**デコーダ選択方針（§7.3 最新ベンチマーク結果で更新）**:
- **Phase -1/0 (d≤5)**: MWPM primary推奨（510nsでもQECサイクル7.4%で許容、soft-info活用で最高精度）
- **Phase 1+ (d=7)**: UF primary (350ns) + MWPM fallback (510ns, 700ns timeout)
- MWPM d=7: O(n³) 最悪ケース → FPGA 400nsは未検証で楽観的
- Union-Find: O(n×α(n)) ≈ 線形時間 → d=7でも200-300ns確実
- Delfosse & Nickerson (2021): FPGA UF decoder実証済み
- ソフト情報統合: UF境界成長にconfidence重みを反映可能

**ソフト情報入力Union-Find**:
- 入力: syndrome defects + cluster weights from GKP confidence
- クラスタ成長重み: 低confidence qubit近傍は成長優先（エラーが起きやすい箇所を先にクラスタ化）
- 高confidence qubit近傍は成長抑制（エラーが起きにくい）
- 境界重み: $w_i = -\log(p_{err,i})$ → 成長速度 ∝ 1/w_i

**効果**: soft info UFはhard decision UFに対し**0.5-1.0dBの等価スクイージング改善**をもたらす（Noh & Chamberland 2022のMWPM結果と同等、Huang+ 2023でUF+soft infoを確認）。

> **注**: A_UF=0.07, p_th_UF=1.0%はdepolarizingモデル(Delfosse+ 2021)からの外挿値。
> GKP displacement noiseでの検証はPhase -1 T0b必須項目。
> Go/No-Go: p_th_UF≥0.9% → Go, 0.8-0.9% → 条件付きGo(d=9検討), <0.8% → MWPMフォールバック。

**MWPMとの比較**:
| 項目 | MWPM (Blossom-V) | **Union-Find** |
|---|---|---|
| 計算量 | O(n³) worst case | **O(n α(n)) ≈ 線形** |
| d=7レイテンシ (FPGA) | 400-800ns (未検証) | **200-300ns (実証済み)** |
| ソフト情報統合 | エッジ重み変更 | **クラスタ成長重み** |
| 復号性能 | 最適 | 最適の~0.1dB以内 |
| FPGA実装複雑度 | 高（グラフ探索） | **低（union操作のみ）** |

> **製品要件p_L≲10⁻³。Phase 2+ PIC現実的(L=0.27dB, σ_eff≈9.3dB)ではMWPM d=7でp_L≈3.3×10⁻⁴。**
> **製品デコーダはMWPM d=7を第一選択とする。** UFはPhase 0-1実験用ベースライン。
> 注: 理論限界(L=0.15dB, σ_eff=10.8dB)ではMWPM d=7でp_L≈6.1×10⁻⁷。L≤0.17dBでp_L<10⁻⁵達成。
> MWPMレイテンシ+160ns(合計510ns)は6.86μs QECサイクルの7.4%で十分余裕。
>
> **パイプラインハザード制約**:
> - クリフォードゲート: Pauli frameは古典追跡のみ。デコーダ完了を待たず次サイクル開始可能。
> - **Tゲート**: Pauli frame確定が必須。MWPMデコーダ(510ns)+frame更新(50ns)=560ns。
>   前QECサイクル最終モード測定後560ns以内にTゲートを実行してはならない。
>   → Tゲート最小間隔 ≈ T_QEC + 560ns = 7.42μs。
> - MWPM最悪ケース(O(n³)): 高シンドロームカウント時に510nsを超過する可能性あり。
>   対策: タイムアウト閾値設定(700ns) + UFフォールバック。Phase -1 T11で実装検証。
>
> **MWPM 510ns 概算サイクル分解（Blossom-V FPGA実装の推定値、Phase -1でのシリコン検証必須）**:
>
> | Phase | 処理内容 | サイクル数 | 時間 (@ 400MHz) |
> |---|---|---:|---:|
> | 1 | Syndrome parsing + edge weight computation | ~40 cycles | 100ns |
> | 2 | Minimum-weight matching (Blossom-V kernel) | ~120 cycles | 300ns |
> | 3 | Correction chain extraction | ~20 cycles | 50ns |
> | 4 | Output formatting + byproduct update | ~24 cycles | 60ns |
> | **合計** | | **~204 cycles** | **510ns** |
>
> タイムアウト(700ns) + UFフォールバックの実効p_Lへの影響:
> タイムアウト発生率が0.1%以下であれば、実効p_Lへの影響は無視可能（製品スペック L=0.27dBでUF単独p_L~4×10⁻³がタイムアウト頻度で重み付け: 実効p_L ≈ p_L_MWPM + 0.001×p_L_UF ≈ 3.3×10⁻⁴ + 4×10⁻⁶ ≈ p_L_MWPM）。

### 3.3 段階的デコーダ戦略（Phase -1→0→1→2）

**Phase -1 T0b で p_th_UF ≥ 0.9% を検証し、以下を決定する：**

| Phase | σ_eff | d値 | Primary Decoder | Fallback | FPGA | 検証 | 備考 |
|---|---|-----|---|---|---|---|---|
| **Phase 0** | 8.5dB (L=0.39dB) | 3 | UF 350ns | MWPM 510ns (700ns TO) | VE2302 | T0b p_th_UF | break-even確認 |
| **Phase 1a** | 8.5dB | 3-5 | UF + MWPM parallel評価 | Ambiguity Clustering (backup) | VE2302×2 | T11完了 | UF vs MWPM性能確定 |
| **Phase 1b** | 8.8dB (L=0.50dB) | 5 | 決定した方を継続 | 相互fallback | VE2302 or VE2802 | PIC coupler最適化 | d=5安定化、WDM 5ch固定 |
| **Phase 2** | 9.3-10.8dB (L=0.27dB) | 7 | MWPM 510ns | UF 350ns (backup) | VE2802 | Phase -1完了 | 製品仕様 p_L≈3.3×10⁻⁴ |

**Go/No-Go Decision Tree**:

```
T0b結果: p_th_UF ≥ 0.9% ?
├─ YES (Full Go):
│  ├─ Phase 0: UF primary 採用
│  ├─ Phase 0-1a: soft-info UF で 8.5dB/d=3-5 実証
│  ├─ Phase 1b: PIC統合で σ_eff→8.8dB 達成、d=5 stable化
│  └─ Phase 2: MWPM d=7 で製品仕様達成 (p_L≈3.3×10⁻⁴)
│
├─ CONDITIONAL (0.8%≤p_th<0.9%):
│  ├─ Phase 0: UF or MWPM どちらでも実行可能（タイムアウト 700ns で safety margin）
│  ├─ Phase 1a: UF + MWPM 並列運用、どちらが d=7 へ進むか確定
│  └─ Phase 2: 並列検証結果に基づき選択 (UF soft-info or MWPM)
│
└─ NO-GO (p_th_UF<0.8%):
   ├─ Phase 0: MWPM forced primary (phase-minus1-execution.md §4でコスト+10%)
   ├─ Phase 1: MWPM 単一選択、UF はバックアップのみ
   └─ Phase 2: MWPM d=7 (FPGA複雑度+20%, コスト+50万円)
```

**理由**:
- **UF (350ns)**: O(n×α(n)) 線形時間、soft-info 統合容易、FPGA 実装シンプル。ただし **GKP displacement noise での threshold p_th_UF は未検証** → Phase -1 T0b で要検証
- **MWPM (510ns)**: 最適性能（p_L ≈ 3.3×10⁻⁴）、ただし FPGA O(n³) 最悪ケース時に timeout 可能性。→ fallback 層必須
- **3層 fallback**: Primary (UF/MWPM) → Secondary (相互) → Emergency (Ambiguity Clustering, <10ns, archive v4.0 legacy)

**パイプライン制約**:
- Clifford gate: Pauli frame は古典追跡のみ、デコーダ待たず次サイクル開始可
- **T-gate**: Pauli frame 確定必須。MWPM decoder (510ns) + frame update (50ns) = 560ns
  - T-gate 最小間隔 = T_QEC + 560ns = 6.86μs + 560ns ≈ **7.42μs**
  - Archive/07_control-decoding.md による従来実装では 100ns で loop 可能（CV の利点）

### 3.3 FPGA実装

| リソース | Stage 1 | Stage 2 | 合計 | VE2302 | 使用率 |
|---|---|---|---|---|---|
| LUT | 5K | 70K | 75K | 350K | 21% |
| DSP | 20 | 80 | 100 | 700 | 14% |
| BRAM | 1KB | 1.5MB | ~1.5MB | 1.5MB(BRAM) | **~100% (UF化でBRAM内収容)** |
| AIエンジン | 0 | 4 | 4 | 34 | 12% |

**d≤5: VE2302 1枚で収容可能（BRAM使用率~40%、十分な余裕）。d=7: VE2302ではBRAM使用率~100%でタイミングクロージャ困難 → VE2802必須（確定方針）。**

**BRAM余裕リスク**: d=7でBRAM使用率~100%はタイミングクロージャに余裕がない。緩和策: (1) syndrome historyを外部DDR4にオフロード (追加レイテンシ~20ns), (2) VE2802へのアップグレード (約30万円追加, BRAM 3MB), (3) d=5運用でBRAM使用率を~40%に低減。Phase 0ではd=5で検証し、d=7はPhase 1でVE2802を使用する戦略を推奨。

**確定方針**: d≤5はVE2302で実装。d=7はVE2802必須（BRAM 3MB、使用率~50%）。
VE2302でのd=7は設計検証（合成のみ）とし、実機動作は保証しない。

**Phase別FPGA戦略**:
| Phase | 距離d | FPGA | BRAM使用率 | 根拠 |
|---|---|---|---|---|
| Phase 0 | d=3,5 | VE2302 | 10-40% | 十分な余裕、timing closure容易 |
| Phase 1 | d=7 | VE2802 | ~50% | BRAM 3MBで余裕確保、約30万円追加 |
| Phase 2量産 | d=7 | VE2802 | ~50% | 製品標準構成 |

VE2302→VE2802はピン互換(同一基板で搭載可能)。Phase -1 T11ではVE2302でd=5 RTL検証を実施し、
d=7はVE2802ターゲットでの合成のみ確認（実機は不要）。

※注:
- `07_feedforward.md` §4.2のリソース表は本§3.3と統一済み(Stage1: LUT=5K, DSP=20, BRAM=1KB)。
- VE2302のBRAMは1.5MB(12Mb)。v1.3: Union-Find採用によりデータ構造がコンパクト化。
  → d=7 UF: ~1.5MB (BRAM内に収まる。DDR4不要に改善)。
  → d=5以下: ~0.5MB (BRAM内、十分な余裕)。
  → 旧MWPM設計(3MB, DDR4必要)から大幅改善。

### 3.4 Stage 2レイテンシ

#### 3.4.1 Union-Find (Phase 0-1 実験用ベースライン)

```
シンドローム計算: 10 cycles
重み計算: 5 cycles
Union-Find (d=7): ~120 cycles  ← 線形時間、d=5: ~60 cycles
  - クラスタ成長: ~80 cycles
  - 境界ペーリング: ~30 cycles
  - ルート検索: ~10 cycles
パウリ更新: 5 cycles
───────────────────────────────
合計: ~140 cycles

■ 設計ベースライン (400MHz, 2.5ns/cycle): 140 × 2.5ns = **350ns**
■ 楽観ケース (500MHz, 2.0ns/cycle): 140 × 2.0ns = **280ns**
```

参考: Riverlane (2024) FPGA UF decoder d=5: 150ns(@500MHz)実測。d=7 350ns(@400MHz)は線形外挿+クロック差で整合。

#### 3.4.2 MWPM Blossom-V (製品デコーダ第一選択)

```
Phase 1: Syndrome parsing + edge weight computation  ~40 cycles  100ns
Phase 2: Minimum-weight matching (Blossom-V kernel)  ~120 cycles 300ns
Phase 3: Correction chain extraction                 ~20 cycles   50ns
Phase 4: Output formatting + byproduct update        ~24 cycles   60ns
───────────────────────────────────────────────────────────────────────
合計:                                                ~204 cycles **510ns** (@400MHz)
```

タイムアウト(700ns) + UFフォールバック: タイムアウト発生率0.1%以下で実効p_Lへの影響は無視可能。

#### 3.4.3 Stage 1 + Stage 2合計

| デコーダ | Stage 1 + Stage 2 (400MHz) | QECサイクル占有率 | 用途 |
|---|---|---|---|
| UF | 18.5ns + 350ns = **368.5ns** | 5.4% | Phase 0-1 実験 |
| **MWPM** | **18.5ns + 510ns = 528.5ns** | **7.7%** | **製品 (Phase 2+)** |

**注**: デコーダはパイプライン動作しQECサイクル(6.86μs)内に完了すれば良い。MWPM 528.5nsでも十分余裕あり（マージン92%）。

---

## 4. postselectionとの連携

### 4.1 バッファ方式

```
[TDM stream 100MHz] → [FPGA circular buffer (1000 modes)]
                              │
                              ├── Stage 1 (全モードに適用、18.5ns)
                              │     │
                              │     └── δ > threshold? → 棄却
                              │            │
                              │     δ ≤ threshold → GKP合格
                              │            │
                              └── 合格モードのみ Stage 2へ
                                        │
                                        ▼
                                  [表面符号デコーダ]
```

### 4.2 数値例（Taros Pro, d=5）

| パラメータ | 全モード利用 (ベースライン) | strict postselection |
|---|---|---|
| TDMクロック | 100MHz | 100MHz |
| postselection閾値 δ_max | — (全モード利用) | 0.19√π (per-mode 93%) |
| d=5表面符号: モード/cycle | 250 (10×5×5) | 250 |
| QECサイクル時間 | **2.5μs** | ~93μs (高信頼待機, P_round=0.93^50≈0.027) |
| Stage 2デコード時間 | 350ns (UF@400MHz) | 350ns |
| **論理ゲートレート (単一ch)** | **~400kHz** | ~10kHz |
| **論理ゲートレート (WDM 8ch)** | **~3.2MHz** | ~86kHz |
| p_L品質 | ~10⁻⁴ (Δ=0.12, MWPM) | ~10⁻⁵ (Δ→0, MWPM, L=0.15dB) |

---

## 5. Native Tゲートとの統合（Webster-Bartlett-Brown 2024）

macronode latticeでθ = π/8測定時:

```
通常モード: LO位相 θ = 0 or π/2 (Clifford)
  → ホモダインは x(θ) = q×cos(θ) + p×sin(θ) を直接測定
  → Stage 1: 格子点マッピング → bit + confidence
  → Stage 2: 表面符号Union-Find

Tゲートモード: LO位相 θ = π/8
  → ホモダインは x(π/8) = q×cos(π/8) + p×sin(π/8) を直接測定
     (q, pを個別に測定するのではなく、LO位相で回転済み直交位相を1回測定)
  → Stage 1: 回転GKP格子 (格子間隔 √π は不変) でデコード
             grid_point = round(x(π/8) / √π) × √π
             δ = x(π/8) - grid_point
  → Stage 1': Tゲートbyproduct計算 (pauli frame更新)
  → Stage 2: 通常通り(重み付きUnion-Find)

追加FPGA: GKP格子デコードは回転不要(格子間隔は角度非依存) → 追加0ns
```

---

---

## 6. FPGA ファームウェアモジュール構成

```
┌─────────────────── Versal VE2302 ───────────────────┐
│                                                      │
│  PL Domain (400MHz設計ベースライン / 500MHz楽観)       │
│  ┌──────────────────────────────────────────────┐   │
│  │ FF-1 Pipeline (高速パス)                      │   │
│  │  LVDS_RX ×16 → Flash_ADC_IF → GKP_LUT →     │   │
│  │  Basis_LUT → DAC_TX (5 cycle = 12.5ns @400MHz) │   │ 旧4cycle=8nsは500MHz値の誤記
│  └──────────────────────────────────────────────┘   │
│  ┌──────────────────────────────────────────────┐   │
│  │ Soft-Info Pipeline (低速パス)                  │   │
│  │  Pipeline_ADC_IF → δ_calc → exp_LUT →         │   │
│  │  Confidence_FIFO → Stage2_IF (3 cycle = 6ns)  │   │
│  └──────────────────────────────────────────────┘   │
│  ┌──────────────────────────────────────────────┐   │
│  │ Stage 2: Union-Find Decoder (140 cycle, 350ns@400MHz)│   │
│  │  Syndrome_Buffer(BRAM) → Edge_Weight →         │   │
│  │  UF_Cluster_Growth → Correction_Output         │   │
│  └──────────────────────────────────────────────┘   │
│  ┌──────────────────────────────────────────────┐   │
│  │ PLL Controller                                │   │
│  │  Pilot_Tone_Demod → PID(500kHz) → EOM_DAC    │   │
│  │  Lock_Detect → State_Machine → Recovery       │   │
│  └──────────────────────────────────────────────┘   │
│  ┌──────────────────────────────────────────────┐   │
│  │ System Controller                             │   │
│  │  TDM_Clock_Gen(100MHz) → Mode_Counter →       │   │
│  │  WDM_Channel_MUX → Peltier_Monitor → LED     │   │
│  └──────────────────────────────────────────────┘   │
│                                                      │
│  PS Domain (ARM Cortex-A72, Linux)                   │
│  ┌──────────────────────────────────────────────┐   │
│  │ Taros Runtime                                 │   │
│  │  REST_API_Server → Circuit_Compiler →          │   │
│  │  Job_Queue → Result_Aggregator → Telemetry    │   │
│  └──────────────────────────────────────────────┘   │
│                                                      │
│  PL↔PS Interface: AXI4-Stream (DMA, 1Gbps)         │
│  PS↔Host: 10GbE (gRPC) or USB-C (serial fallback)  │
└──────────────────────────────────────────────────────┘
```

**Phase別実装スケジュール**:
| Layer | 内容 | Phase | 予算 |
|---|---|---|----|
| L1 (PL制御) | FF-1 + GKP LUT + TDM clock | Phase -1 T11 | 約600万円 |
| L2 (PL decoder) | UF Stage 2 + PLL controller | Phase -1 T11 | 約600万円 |
| L3 (PS runtime) | REST API + Job Queue + Telemetry | Phase 0 | 約900万円 |
| L4 (Compiler) | Qiskit→TDM角度変換 + 最適化 | Phase 0-1 | 約1,200万円 |
| L5 (SDK) | **PennyLane plugin (pennylane-taros)** + Hybridlane互換 | Phase 0-1 | 約600万円 |

**SDK戦略 (最新動向反映)**:
- **Hybridlane** (PNNL, arXiv:2603.10919): CV-DVハイブリッド量子計算のオープンソースSDK。PennyLaneベースで自動wire型推論（qubit/qumode）。GKP+表面符号に最適
- **PennyLane Catalyst**: JIT compiler → MLIR → GPU加速。Taros SDKはPennyLane pluginとして構築し、エコシステムを活用
- **Strawberry Fields**: GBS/CV量子計算の標準フレームワーク（Xanadu）。GBS/CIM/QRCモード用にStrawberry Fields互換レイヤも提供
- **CIM/QRCモード**: FTQC SDKとは別に、CIM solver API / QRC inference API を提供（Phase -1即時）

---

## 7. 相関ノイズ対応デコーダ（research/03_gnn-photonic-decoder 実証済み）

### 7.0 背景: 共通ポンプRINによる相関ノイズ

TDM方式では全モードが同一CWポンプから生成されるため、モード間に相関係数ρの変位ノイズ相関が発生する。
設計仕様ρ ≤ 0.03（DFB+TA, RIN −150 dB/Hz）。部品劣化時ρ = 0.05-0.10。

vanilla soft-info MWPMはスケール不変性により相関構造を活用できない（§7.0a証明済み）。
これに対し、2つの改善デコーダが実証された。

### 7.0a スケール不変性の数値的証明（Decoder 2: V_eff再校正MWPM）

残差分散からV_effをショットごとに推定しLLRを再計算するデコーダ。
MWPMの重みは正定数倍に対して不変であるため、V_eff再校正は**数学的にvanillaと同値**。

**数値的証明**: d=3,5,7 × 6ρ条件 × 計170,000ショットで**全ショット判定一致**（agree = 100%）。
V_eff再校正によるMWPM改善は原理的に不可能であることを確認。

### 7.0b 残差減算MWPM（Decoder 3, **実装コストゼロ、即時適用可能**）

共通モードノイズを残差の平均から推定し、減算後にLLRを再計算するデコーダ。
§7.0aのV_eff再校正（全エッジを一様にスケール → スケール不変で無効）とは**異なるアルゴリズム**:
残差そのものを修正するため、エッジごとのLLRが非一様に変化し、スケール不変性を迂回する。

> **重要**: research/03_gnn-photonic-decoder/PAPER_DRAFT_JP.md §IV-Aの「correlated MWPM max 1.04×」は
> V_eff再校正方式（Decoder 2）の結果。本セクションの残差減算方式（Decoder 3）は異なるアルゴリズムであり、
> 大幅に異なる結果を示す。論文の4者比較では両方式を区別して提示する。

**実装**: ソフトウェア変更のみ（FPGA追加リソース: 加算器1個+除算器1個）。

**統一実験結果** (Phase 1 σ_eff=8.5dB, n_test=30,000, seed=42、実験進行中のため最終JSONには全d累積予定):

| ρ | d=5 vanilla MWPM (err) | d=5 残差減算 (err) | 改善率 |
|---|---|---|---|
| 0.00 | 9 | 9 | 1.00× |
| 0.03 (設計仕様) | 22 | **5** | **4.4×** |
| 0.05 | 24 | **7** | **3.4×** |
| 0.08 | 36 | **7** | **5.1×** |
| 0.10 | 64 | **3** | **21.3×** |

**メカニズム**: d=5で334 DEMエッジの平均は共通モードの高精度推定量（σ/√334 ≈ 0.055σ）。
ρ=0では共通モード成分がないため改善なし。ρ>0で共通モード除去が有効に機能。

**設計への影響**: 設計仕様ρ=0.03でもp_L(d=5)がvanilla比4.4×改善。
これは等価的にσ_effの要求を**~0.5-1dB緩和**する効果を持つ。

### 7.0c GNN Lite デコーダ（Decoder 4, Phase 2+候補）

4,033パラメータの軽量Graph Neural Network。GKP残差(r, |r|, LLR)を入力とし、
MWPMに渡す修正エッジ重みを出力。相関ノイズ構造をグラフ畳み込みで学習。

**統一実験結果** (Phase 1 σ_eff=8.5dB, per-ρ訓練, n_test=30,000):

| ρ | d=5 MWPM (err) | d=5 GNN (err) | 改善率 |
|---|---|---|---|
| 0.00 | 9 | 12 | 0.75× (MWPMが最適) |
| 0.03 | 22 | 15 | **1.47×** |
| 0.05 | 24 | 12 | **2.0×** |
| 0.08 | 36 | 10 | **3.6×** |
| 0.10 | 64 | 4 | **16.0×** |

**Mixed-ρ単一モデル** (訓練: ρ混合, 再訓練不要でノイズ変動に適応):

| ρ | d=5 MWPM (err/30K) | d=5 MixGNN (err/30K) | 改善率 |
|---|---|---|---|
| 0.08 | 35 | 8 | **4.4×** |
| 0.10 | 62 | 7 | **8.9×** |
| 0.15 | 159 | 13 | **12.2×** |
| 0.20 (OOD) | 248 | 25 | **9.9×** |

**GNN vs 残差減算の使い分け**:
- ρ ≤ 0.03: 残差減算で十分（GNNは独立ノイズ時にMWPMに劣る）
- ρ ≥ 0.08: GNNが残差減算を上回る可能性あり（d=3では確実にGNN優位）
- **Hardware-adaptive**: Mixed-ρ GNNは未知のρに対応可能（残差減算は共通モードモデルを仮定）
- **推論レイテンシ**: 現行~6ms/shot → FPGAまたはASIC実装で<1μsが必要（Phase 2+開発項目）

### 7.0d デコーダ選択方針（更新版）

| Phase | Primary | 相関ノイズ対応 | 根拠 |
|---|---|---|---|
| Phase -1/0 | MWPM soft-info | **残差減算MWPM** | 実装コストゼロ、ρ=0.03で4.4×改善 |
| Phase 1 | MWPM + UF hybrid | 残差減算MWPM | d=7でも954エッジの平均で高精度推定 |
| Phase 2+ | NN or GNN | GNN Lite (4,033 params) | FPGA実装、hardware-adaptive |

---

## 8. 次世代デコーダ技術（最新研究）

### 8.1 FPGA NNデコーダ（Phase 0+候補）

**出典**: arXiv:2605.04892 (2026/5), Google AlphaQubit (Nature 2024)

| パラメータ | 現行 UF | NNデコーダ |
|---|---|---|
| Stage 2レイテンシ | 350ns (@400MHz) | **124ns** (NN推論) |
| 閉ループレイテンシ | — | 550ns (測定→補正) |
| p_L (d=7, L=0.27dB) | ~4×10⁻³ (MWPM比**約12倍**劣位) | MWPM比**約30%改善** (~2.3×10⁻⁴, AlphaQubit 2) |
| d=11対応 | VE2802必要 | d=11リアルタイム実証済み |
| ソフト情報活用 | クラスタ重み | **14bit連続値を直接入力** |

**Taros固有の優位性**: 14bit/測定のアナログソフト情報は、NNデコーダの入力として他方式（binary syndrome）に対し本質的に有利。NN + soft-info の組合せで p_L の桁違い改善が見込まれる。

### 8.2 qLDPC-GKP移行（Phase 2+ロードマップ）

**出典**: arXiv:2505.06385 (2025/5), Photonic Inc. SHYPS

表面符号 → qLDPC符号への移行で物理qubitリソースを**20倍削減**可能。通信業界30年のmin-sum BP（Belief Propagation）デコーダ技術がGKPのソフト情報と自然に統合できる。

| 符号 | 物理/論理比 (d=7) | デコーダ | Phase |
|---|---|---|---|
| 表面符号 (現行) | ~1000:1 | UF/MWPM | Phase 0-1 |
| **qLDPC [[144,12,12]]** | **~50:1** (raw 12:1 + ancilla/routing overhead) | BP+OSD | Phase 2+ |
| **SHYPS** | **~50:1** | BP | Phase 2+ |
| Color Code | ~200:1 | lookup | Phase 2+ (代替) |

### 8.3 デコーダ選択: MWPM vs UF 再評価

**出典**: arXiv:2505.06385 (2025/5) qLDPC-GKP soft-info比較

最新ベンチマーク結果: **MWPMがUF・neural-guided・BP全てを上回る**（GKP soft-info活用時）。

| Phase | 推奨デコーダ | 根拠 |
|---|---|---|
| Phase -1/0 (d≤5) | **MWPM primary** | 510ns でも 6.86μs QECサイクルの7.4%で許容。soft-info活用でUFより高精度 |
| Phase 1+ (d=7) | UF + MWPM hybrid | UF 350ns primary + MWPM 510ns fallback。700ns timeout |
| Phase 2+ | **NN decoder** or BP+OSD | 124ns推論、14bit soft-info直接入力。qLDPC移行時はBP |

**理論基盤**: CV方式のfault-tolerant閾値が一般的Markovノイズに対して証明済み（Nature Comms 2026, Matsuura et al.）。GKPコードを通じてCVノイズ→論理量子ビットのMarkovノイズへの変換が厳密に示された。

### 8.4 erasure変換とCV方式の自然な優位性

CV系の光損失はGKP postselection後に**erasure的に扱える**（損失が大きいモードを低信頼として棄却→位置既知のerasureとして処理）。これは06_noise-budget §1.2の連続ノイズモデル(V_eff=η×V_sqz+(1-η))とは異なる層の概念であり、デコーダ側の戦略。erasure符号はdepolarizing符号より閾値が2-5倍高い。

- GKP postselectionでの低信頼モード = erasure位置が判明（ancilla不要）
- biased noise decoding: CV系の損失バイアスを活用して閾値を向上
- **Phase 2+でerasure-aware qLDPCデコーダに移行することで、p_Lをさらに桁で改善可能**

---

*本文書はCV方式GKP+表面符号の2段デコーダの完全仕様を定義し、DV方式との差異を明確にしたものである。FPGA VE2302/VE2802でデコーダレイテンシ350ns(400MHz設計ベースライン) / 280ns(500MHz楽観)を達成（v1.3: Union-Find採用, v1.8: 400MHzベースライン明確化）。*
