TomohiroTani28/Taros/design/_parameters.md

# Taros パラメータレジストリ (Single Source of Truth)

**Document ID**: PQC-PARAMS-v1.0
**Status**: 確定版

> 本文書はプロジェクト全体のパラメータ定義の単一真実源（SSOT）です。
> 他の文書がパラメータ値を引用する場合、本文書を参照元とすること。
>
> **BSモデル公式（正式）**: `V_eff = η × V_sqz + (1 − η) + V_nl`
> - η: 全光学透過率, V_sqz = 10^(−σ_gen/10): スクイーズド分散, V_nl: 非損失ノイズ (0.010 SNU)
> - 旧dB減算公式 σ_eff = σ_gen − L は**廃止**。BSモデルが全文書の正式公式。
>
> **SSOT階層**:
> - **本文書 `_parameters.md`**: プロジェクト全体のSSOT。全方式(CV/DV)横断のパラメータ定義
> - **`00_overview.md` 正規パラメータ表**: CV方式の詳細パラメータ。本文書の値を展開・詳細化したもの
> - **各design文書 (01-14)**: 個別サブシステムの設計詳細。パラメータ値は上位2文書に準拠
> - **矛盾時の優先順位**: `_parameters.md` > `00_overview.md` > 個別design文書

---

## 1. Phase 定義（統一版）

プロジェクト全体で統一するPhase番号と期間の対応表。

| Phase | 期間 | CV方式（主軸） | DV-FBQC方式（凍結） | 主要マイルストーン |
|---|---|---|---|---|
| **-1** | 開始後0-12ヶ月 | 約4.6億円, GKP実験+Stim検証 | — | Go/No-Go判定 |
| **0a** | 開始後約9-12ヶ月 | Taros Edu プロトタイプ (d=3) | — | QEC break-even |
| **0b** | 開始後約15-18ヶ月 | Taros Pro プロトタイプ (d=5) | — | 製品プロトタイプ |
| **1** | 開始後約2年 | Taros Max プロトタイプ (d=7) | Phase 1: 8ラック構成 | 製品設計完了 |
| **2** | 開始後約3-4年 | 量産設計 (100台/年) | Phase 2: クライオPIC | 量産立ち上げ |
| **3** | 開始後約4年以降 | WDM 20ch フルスペック | — | 高性能FTQC |

> **注**: archive/ 配下のDV方式文書では「Phase 0/1/2/3」が上記と異なる定義で使用されている場合があります。
> archive/のPhase定義は凍結されており、本表のCV方式列が正式です。

---

## 2. CV方式パラメータ（主軸）

`design/00_overview.md` の正規パラメータ表が正式値。以下は要約。

### 2.1 光源・スクイージング

| パラメータ | 記号 | 正規値 | 根拠文書 |
|---|---|---|---|
| 生成スクイージング | σ_gen | 13 dB | design/02_opa-source |
| ポンプ波長 | λ_pump | 775 nm (SHG from 1550nm) | design/02_opa-source |
| 信号波長 | λ_signal | 1550 nm | design/02_opa-source |
| TDMクロック | f_TDM | 100 MHz | design/03_tdm-cluster |

### 2.2 損失・ノイズ

| パラメータ | 記号 | Phase 1 (離散) | Phase 2+ PIC (現実的) | Phase 2+ PIC (理論限界) | 根拠文書 |
|---|---|---|---|---|---|
| 全光学損失 | L_total | 0.39 dB | 0.27 dB | 0.15 dB | design/06_noise-budget |
| 全光学透過率 | η_total | 0.914 | 0.940 | 0.966 | design/06_noise-budget |
| 実効スクイージング | σ_eff | 8.5 dB | **≈9.3 dB** (L=0.27dB, non-loss込み) | 10.8 dB | design/06_noise-budget |
| 物理エラー率 | p_phys (=p_err) | 9.3×10⁻³ | ≈4.9×10⁻³ (L=0.27dB) | ≈1.0×10⁻³ | design/13_performance |

### 2.3 QEC性能

| パラメータ | 記号 | 正規値 | 条件 | 根拠文書 |
|---|---|---|---|---|
| 閾値 (soft-info MWPM) | p_th_eff | 1.5% | Noh-Chamberland 2022 | design/08_decoder |
| 閾値 (保守 hard MWPM) | p_th | 0.59% | 文献値 | design/13_performance |
| 論理エラー率 d=7 (MWPM, Phase 1) | p_L | ~4.4×10⁻³ | L=0.39dB, σ_eff=8.5dB, break-even境界 | design/06_noise-budget |
| 論理エラー率 d=7 (MWPM, Phase 2+ PIC現実的) | p_L | **~3.3×10⁻⁴** | L=0.27dB, QE≥99%, V_non-loss込み, **Δ・RIN未包含**。Δ+RIN全込み推定: 5-9×10⁻⁴（p_L≲10⁻³達成）。Phase -1実測で確定。L≤0.22dBで≲10⁻⁴ | design/06_noise-budget |
| 論理エラー率 d=7 (MWPM, Phase 2+ PIC理論限界) | p_L | 6.1×10⁻⁷ | L=0.15dB, Δ=0, QE=99% | design/13_performance |
| 論理エラー率 d=7 (UF, L=0.27dB) | p_L | ~4.0×10⁻³ | 製品要件(≲10⁻³)未達→MWPM必須 | design/06_noise-budget |
| デコーダ遅延 (MWPM製品) | t_dec | 510 ns | @400MHz | design/08_decoder |
| デコーダ遅延 (UF実験) | t_dec | 350 ns | @400MHz | design/08_decoder |
| フィードフォワード (FF-1) | t_FF | 27 ns | @400MHz | design/07_feedforward |

### 2.4 製品仕様

| パラメータ | Taros Edu | Taros Pro | Taros Max | 根拠文書 |
|---|---|---|---|---|
| 表面符号距離 | d=3 | d=5 | d=7 | design/00_overview |
| 重量 | ~4.3 kg | ~7.5 kg | ~9.7 kg | design/00_overview |
| 消費電力 | ~104 W | ~109 W | ~112 W | design/00_overview, design/10_portable |
| 原価 | 約840万円 | 約1,125万円 | 約1,425万円 | analysis/bom |
| 販売価格 | 約1,350万円 | 約1,800万円 | 約2,550万円 | analysis/bom |

### 2.5 Rack CV+QD 仕様

| パラメータ | 正規値 | 根拠文書 |
|---|---|---|
| ラックサイズ | 20U ハーフラック (482×890×450mm) | design/09_rack-design |
| ラック内重量 | ~30kg | design/09_rack-design |
| システム総重量 | ~42kg (ラック30kg + クライオ12kg) | design/09_rack-design |
| ラック内消費電力 | ~185W | design/09_rack-design |
| システム総消費電力 | ~1.5kW (ラック185W + PT205 1.3kW) | design/09_rack-design |
| 原価 (量産100台) | 約2,925万円 | design/09_rack-design |
| 販売価格 | 約5,700万円 | design/09_rack-design |

### 2.6 7-in-1 動作モード定義

| Mode | 名称 | 説明 | OPA動作 | 追加HW | 利用開始 | 根拠文書 |
|---|---|---|---|---|---|---|
| 1 | **FTQC** | GKP+表面符号→qLDPC 誤り訂正型量子計算 | 閾値以上 | なし | Phase 0+ | design/08_decoder, design/13_performance §1-4 |
| 2 | **CIM** | コヒーレントイジングマシン（組合せ最適化） | **閾値以下** | なし(SW) | Phase -1† | design/13_performance §8.4 |
| 3 | **QRC** | 量子リザーバコンピューティング（時系列予測） | 通常 | なし(SW) | Phase -1† | design/13_performance §8.5 |
| 4 | **QRNG** | 量子乱数生成（真空ゆらぎホモダイン） | OFF可 | なし(SW) | Phase -1† | design/13_performance §8.11 (Mode 4) |
| 5 | **Sensing** | 量子センシング（SQL以下精密測定） | 通常 | なし(SW) | Phase -1† | design/13_performance §8.11 (Mode 5) |
| 6 | **Imaging** | 量子イメージング（サブショットノイズ） | 通常 | なし(SW) | Phase -1† | design/13_performance §8.7 |
| 7 | **Tensor** | フォトニックテンソル処理（AI推論加速） | コヒーレント光 | なし(SW) | Phase -1† | design/13_performance §8.9 |

†開発フェーズではPhase -1から利用可能。製品出荷後は購入即日（初期SW設定1-2週間）。全モード共通HW: OPA + BS網 + PMF遅延線 + ホモダイン + FPGA + EOM

### 2.7 SNSPD材料（Phase別推奨）

| Phase | 推奨材料 | SDE | 動作温度 | 根拠 |
|---|---|-----|---|---|
| Phase 0-1 | **MoSi** | 87% @2.3K | PT205 (2.5K) | 01_system-architecture §4.3 |
| Phase 2+ | **MgB2** (候補) | 未公表(飽和確認@3.7K) | 最大20K | Nature Comms 2024 |
| 商用候補 | ID Quantique ID281 | 88% (28px PNR) | <2.5K | 01_system-architecture §4.3 |

### 2.8 スクイージング増強技術（研究候補）

| 技術 | 効果 | コスト | Phase | 根拠文書 |
|---|---|---|---|---|
| ML-SLM空間モード最適化 | σ_eff +0.6-1.0dB (離散光学系) | ~40万円 | Phase -1 T0a | design/02_opa-source §6.1 |
| 非エルミートEP増強 | σ_gen 15dB+ (理論) | 研究費 | Phase 1+ | design/02_opa-source §6.2 |
| GKP低入力ブリーディング | 3dB入力→9.75dB等価GKP | なし(プロトコル) | Phase 1+ | design/02_opa-source §6.3 |

### 2.9 QEC Phase 2+移行候補

| 符号 | 物理/論理比 | デコーダ | 特徴 | 根拠文書 |
|---|---|---|---|---|
| 表面符号 (現行) | ~1000:1 | UF/MWPM | Phase 0-1 | design/08_decoder §3 |
| qLDPC [[144,12,12]] | ~50:1 (raw 12:1) | BP+OSD | 20倍効率化 | design/08_decoder §7.2 |
| Color Code | ~200:1 | lookup | transversal CNOT | design/08_decoder §7.2 |

---

## 3. DV-FBQC方式パラメータ（凍結・参考）

> **⚠ 凍結**: 以下の値は DV-FBQC v4.0 R6  時点で凍結されています。
> archive/ 配下の文書を参照する際のリファレンスとしてのみ使用してください。

### 3.1 光源

| パラメータ | 記号 | R6最終値 | 注記 |
|---|---|---|---|
| QD材料 | — | GaAs (925nm) / InP (1550nm) | archive/02_physical-layer/quantum-dots/ |
| QD収集効率 | η_QD | 0.57 (現状) → 0.85 (Phase 1目標) | **注意: 文書間で0.57/0.60/0.65/0.85が混在** |
| QD繰り返し周波数 | f_QD | 76 MHz (Ti:Sa同期) | archive/04_hardware/rack1-source |
| QFC変換効率 (end-to-end) | η_QFC | 0.57 (Phase 0) → 0.75-0.82 (R6目標) | **注意: Phase 1で0.57 vs 0.87が混在** |
| QFCポンプ波長 | λ_pump_QFC | 2,290 nm | エネルギー保存: 1/925-1/1550=1/2290 |
| Boosted fusion成功率 | P_fusion | 97% (n=4) | **注意: n=1/2/4の3値が文書間で混在** |

### 3.2 損失バジェット

| パラメータ | 記号 | R6最終値 | 注記 |
|---|---|---|---|
| HCF 600m損失 | L_HCF | 0.07 dB (@0.11dB/km) | **注意: 1.2dBは誤記** |
| SNSPD検出効率 | η_SNSPD | 95% (@2.5K) / 98% (@0.8K) / 99.7% (WI-SNSPD) | Phase/技術依存 |
| 全経路透過率 | η_total | ~14.4% (Phase 0) | 符号閾値比較には使用不可（ヘラルド後損失を使用） |
| ヘラルド後透過率 | η_post-herald | ~84.7% (Phase 0改善前) | 符号関連erasure率の計算に使用 |
| ヘラルド後erasure率 | ε_herald | ~30.4% (Phase 0) | **注意: ~21%は改善後の値で誤適用** |

### 3.3 QEC符号

| 符号 | パラメータ | Erasure閾値 | 優先度 (R6) | 注記 |
|---|---|---|---|---|
| GB [[144,12,12]] | Primary | **未計算（要Stim実行）** | Primary (R4で昇格) | 閾値・性能データ欠如 |
| GB [[72,12,6]] | 最小構成 | **未計算** | Primary (R6追加) | Phase 0-1向け |
| SHYPS [[400,25,8]] | Secondary | ~50% | Secondary (R4でPrimaryから降格) | **注意: 24.9%は表面符号の値の誤適用** |
| 4D HPC | — | ~22-25% / ~30% | — | **注意: 2値が混在** |
| 表面符号 | Tertiary | ~24.9% | Tertiary | Bartolucci+ 2023 |

### 3.4 弾道RSG成功確率

| 透過率 η | 成功確率 P(k≥4) | 注記 |
|---|---|---|
| 0.5 | 0.344 | Phase 1相当 |
| 0.7 | **0.744** | Phase 2相当。**旧値0.930は誤り** |
| 0.85 | 0.953 | Phase 3相当 |

---

## 4. 共通コンポーネントパラメータ

DV/CV方式で共通の物理コンポーネントの正規値。

| コンポーネント | パラメータ | 正規値 | 注記 |
|---|---|---|---|
| HCF (DNANF) | 損失 | **0.091 dB/km** (2025記録) / 0.11 dB/km (2023) | Microsoft/Southampton, Nature Photonics 2025 |
| PMF | 損失 | 0.35 dB/km | 標準PMF @1550nm (現行設計採用) |
| LNOI EO MZM | 挿入損失 | 0.3 dB (arm loss) | DC arm + RF core |
| TFLN OPA | on-chip gain | 10 dB net (23.5dB gross) | UT Austin 2026, arxiv:2602.05982 |
| Si₃N₄ PIC | 導波路損失 | 0.01 dB/cm | Ligentec ANT |
| InGaAs PD | 量子効率 | 99% (設計目標) / 95% (市販品) | QE≥98%必須。商用: Noisy Labs HQE |
| TFLN Foundry | 商用アクセス | QCI (AZ), CCRAFT (CH), Lightium (CH) | 150mmウェーハ、Phase 2+ PIC外注候補 |

---

## 5. コスト正式文書（3文書限定）

| 文書 | 内容 | 最終更新 |
|---|---|---|
| `analysis/bom.md` | 製品BOM（原価・販売価格・TCO） |  |
| `analysis/development-cost-summary.md` | 開発費全体（Phase -1~2: 約8.7億円） |  |
| `analysis/phase-minus1-execution.md` | Phase -1 詳細実行計画 (約4.6億円) |  |

> 他の文書がコスト数値を引用する場合、上記3文書のいずれかを参照元として明記すること。

---

## 6. 文書体系

| ディレクトリ | 状態 | 内容 |
|---|---|---|
| `design/` | **生きた文書（正式）** | CV方式 Taros Portable 設計 |
| `analysis/` | **生きた文書（正式）** | コスト・リスク・ロードマップ |
| `experiments/` | **生きた文書（正式）** | 実験計画・数値検証 |
| `fallback/` | **参考（DV代替）** | DV-FBQC v5.0 Desktop フォールバック |
| `archive/` | **凍結（レガシー）** | DV-FBQC v4.0 R6 設計（凍結） |

---

*本文書はプロジェクトの全パラメータ定義を一元管理するためのレジストリである。パラメータの変更は本文書を起点とし、関連文書に伝播させること。*
