TomohiroTani28/Taros/experiments/01_gkp-optical.md

# GKP光学生成実験計画

**Document ID**: PQC-CV-GKP-EXP-v1.0
**Last Updated**: Phase -1 開始前
**Status**: Draft (最優先)
**目的**: PPLN OPA → postselection GKP生成の世界初の光学実証

**注意**: 本文書の実験コストBOMは初期概算版。最新の統合見積もりは `experiments/05_verification-plan.md` Level 2を参照のこと。

---

## 1. 実験の位置づけ

### 1.1 なぜこの実験が最優先か

Taros Portableの全設計は**単一モード acceptance rate p_acc ≈ 93% (δ=0.19√π窓)**を前提としている
（旧P_s記号は廃止: 04_gkp-protocol §2.2参照。P_round=p_acc^98≈10⁻³はstrict mode参考値）。しかし:
- この値は理論計算 erfc(δ/σ) に基づく
- 光学系でのGKP postselection生成は**世界初**（先行実験なし）
- Konno+ 2024 (arXiv:2312.06536) はcat qubit論文でありGKPではない。
  超伝導系GKP初実証はCampagne-Ibarcq et al., Nature 584, 368 (2020)
  - Asavanant+ 2019はスクイーズド光クラスタだがGKPではない
- **Stimシミュレーションでは検証不可能 — 実機でのみ確認可能**

### 1.2 成功・失敗シナリオ

| 結果 | p_acc | 有効GKPレート | 影響 | 対応 |
|---|-----|---|---|---|
| **成功** | ≥10⁻³ | ≥100kHz | 設計通り | Phase 0へ進行 |
| 部分成功 | 10⁻⁴ | 10kHz | 性能10倍低下 | QD追加(Step B)前倒し or クロック向上 |
| **失敗** | <10⁻⁵ | <1kHz | 設計前提崩壊 | CV pure断念→CV+QD or DV v5.0 |

---

## 2. 実験構成

### 2.1 最小構成図

```
┌─────────────────────────────────────────────────────────────┐
│                     光学テーブル (1.2m × 0.6m)               │
│                                                             │
│  ┌────────────┐    ┌────────────┐    ┌──────────────────┐  │
│  │ 775nm CW LD│───►│ PPLN OPA   │───►│ 50:50 BS         │  │
│  │ 200mW      │    │ (NTT提供)  │    │                  │  │
│  └────────────┘    │ σ≈13dB     │    │  ├─► Homodyne A  │  │
│                    └────────────┘    │  │    (LO: master)│  │
│  ┌────────────┐                      │  └─► Homodyne B  │  │
│  │ Master LD  │──────────────────────┘       (LO: master)│  │
│  │ 1550nm CW  │                                          │  │
│  │ (NKT E15)  │                                          │  │
│  └────────────┘                                          │  │
│                                                             │
│  ┌──────────────────────────────────────────────────────┐  │
│  │ 制御電子系 (ラック内)                                   │  │
│  │  ADC (14bit 400MSPS, ADS5474) ×2                     │  │
│  │  FPGA (Versal VE2302)                                │  │
│  │  PC (データ収集 + 解析)                                │  │
│  └──────────────────────────────────────────────────────┘  │
└─────────────────────────────────────────────────────────────┘
```

### 2.2 TDMなし簡易版（Phase -1a）

Phase -1aの目標: **GKP postselection生成の原理実証**。TDMクラスタは不要。

```
PPLN OPA#1 (CW squeezing 13dB) ──┐
                                   ├── [50:50 BS] ── arm C: ホモダイン測定 (q_C)
PPLN OPA#2 (CW squeezing 13dB) ──┘        │
                                            └── arm D: ホモダイン測定 (q_D, 条件付き)

2モードスクイーズド状態(EPR)から、条件付き状態準備:
  Step 1: arm Cのホモダイン測定値 q_C を記録
  Step 2: q_C mod √π ∈ [-δ, +δ] の条件を満たす事象のみ選択
  Step 3: 選択された事象のarm D測定結果をWigner再構成
  → arm Dの条件付き状態がGKP格子構造を持つことを検証
```

**物理的説明**:
- 2つのスクイーズド真空をBSで干渉させると**EPR相関**（2モードスクイージング）が生成される。
- arm Cの測定結果で条件付けることで、arm Dの状態を**事後的に**「準備」する。
- postselection条件 `q_C mod √π ≈ 0` を満たす時、arm DはGKP格子構造を持つ近似状態になる。
- これは厳密にはGKP状態ではなく**approximate GKP state conditioned on EPR measurement**。
- 2スクイーザ方式は Vasconcelos+ (2010) のbreeding protocol第1段階に相当。

**理論予測値**:
- 13dBスクイージング(V_sqz=0.05)のEPR相関からpostselection幅δ=0.1√πで条件付けた場合:
  - 有限エネルギーGKPパラメータ: Δ ≈ 0.12-0.15
    (Eaton+ 2022解析に基づく推定)
  - Wigner関数忠実度: F ≈ 0.75-0.85
  - **F>0.80は「達成見込み範囲内だが余裕なし」** — 楽観シナリオ
- 単一モードpostselection通過率:
  p_acc ≈ 2δ/√π ≈ 11%（CW、δ=0.1√πの場合。運用値δ=0.19√πでは~93%）
- **Δ測定方法**:
  Wigner tomography格子ピーク幅 σ_W ≈ Δ（位相空間直接）。
  ホモダイン測定ではσ_meas ≈ Δ/√2（片quadrature）。
  Phase -1ではWigner再構成を使用するためσ_W=Δを適用。Go基準: Δ < 0.15
- **成功基準**: F > 0.70（必須）/ F > 0.80（目標）の2段階で評価

**注意**: 単一OPA + 単一BSのみではGKP状態は生成不可
（ガウシアン操作のみでは非ガウシアン状態は原理的に生成できない）。
2モードEPR相関 + ホモダインpostselectionの組み合わせにより、
**測定による非ガウシアン条件付け**が非ガウス性を誘起する。

**CW動作で実行可能**。PPLN OPA 2本のCWスクイージング13dBを使用（パルス化不要）。

### 2.3 パルスTDM版（Phase -1b）

Phase -1aの成功後に実施:
- パルスOPA化 → 100MHz動作（Option B採用、EO gate不要。`design/03_tdm-cluster.md`参照）
- PMF短遅延(2m)追加 → macronode 1列
- GKP postselectionの**パルス動作での**成功確率確認

---

## 3. 測定項目と成功基準

### 3.1 Phase -1a: CW GKP生成

| 測定項目 | 成功基準 | 測定手法 |
|---|---|---|
| OPAスクイージング | >12dB (CW) | ホモダインスペクトラム |
| 反スクイージング | ≤15dB (単一パスOPA理論値=σ_gen。excess noise margin +2dB) | 同上 (旧<20dBは共振器OPO値。単一パスOPAではV_sqz×V_anti=1、13dB sqz→13dB anti-sqz) |
| GKP Wigner関数 | 格子構造確認 (F>0.80) | ホモダイントモグラフィー |
| postselection成功確率 | **>5×10⁻⁴** | 判定回数/全ショット数 |
| GKP忠実度 (合格時) | >0.85 | 理想GKPとのfidelity |
| 位相安定性 | ±2° (1時間) | Pilot Tone or DC出力監視 |

### 3.2 Phase -1b: パルスTDM GKP生成

| 測定項目 | 成功基準 | 追加機材 |
|---|---|---|
| パルスOPAスクイージング | >11dB (100MHz) | パルスOPAポンプ (Option B) |
| TDMモード間相関 | 隣接モードentanglement確認 | PMF 2m遅延 |
| GKP postselection (パルス) | **>10⁻³** | FPGA判定 |
| リアルタイム判定レイテンシ | <50ns | FPGA実装 |

---

## 4. 必要機材と予算

### 4.1 Phase -1a（CW）

| 機材 | 仕様 | 調達 | コスト |
|---|---|---|---|
| PPLN OPA ×2 | NTT研究所品、50mm導波路 | 共同研究 | 約90万円 (×2本、単価約45万円) |
| マスターレーザ | NKT Koheras E15 1550nm | 購入 | 約225万円 |
| 775nm ポンプLD | CW 200mW | 購入 | 約30万円 |
| ホモダインPD ×2 | InGaAs balanced (Thorlabs PDB480C) | 購入 | 約30万円 |
| BS, ミラー, マウント | 標準光学部品 | 購入 | 約15万円 |
| ADC ×2 | 14bit 400MSPS (TI ADS5474) | 購入 | 約60万円 |
| FPGA評価ボード | Versal VE2302 | 購入 | 約30万円 |
| PC + DAQ | データ収集・解析用 | 既存 | 0円 |
| 光学テーブル | 1.2m×0.6m（既存利用想定） | 共用 | 0円 |
| **Phase -1a合計** | | | **約480万円** |

### 4.2 Phase -1b（パルスTDM）追加

| 機材 | コスト |
|---|---|
| LNOI EOM ×1 (基底選択。Option B採用でEO gate不要) | 約45万円 |
| EO driver | 約30万円 |
| PMF 2m + カプラ | 約4.5万円 |
| **Phase -1b追加** | **約80万円** |

### 4.3 総予算

| Phase | コスト | 期間 | 成果物 |
|---|---|---|---|
| -1a (CW GKP) | **約480万円** | **3ヶ月** | GKP Wigner + p_acc実測 |
| -1b (パルスTDM) | +約80万円 | +2ヶ月 | パルスGKP + TDM検証 |
| **合計 (装置BOM)** | **約560万円** | **5ヶ月** | Taros実現可能性の最終判定 |

> **コスト定義**: 約560万円=装置BOM直接費(Phase -1a 480万+Phase -1b 80万)。予備・消耗品込み約800万円。人件費(2名×5ヶ月)込み完全コスト約2,900万円。

---

## 5. スケジュール

```
開始後  1ヶ月   2ヶ月   3ヶ月   4ヶ月
        │       │       │       │
-1a     ████████████████         CW GKP実験
        │   ↓ Go/No-Go          │
-1b             ████████████████ パルスTDM GKP
                        ↓
                  Phase 0判定データ完成
```

### 5.1 Go/No-Go判定

| 判定 | 時期 | Go基準 | No-Go対応 |
|---|---|---|---|
| **G-EXP1** | 開始後2ヶ月 | CW GKP F>0.80, p_acc>85% | (1)スクイージング改善 (2)QD追加前倒し |
| **G-EXP2** | 開始後3ヶ月 | パルスGKP P_round>10⁻³ | クロック低下(50MHz)で対応 |

---

## 6. この実験がTaros全体に与える意味

| 実験結果 | Taros Portableへの影響 | Taros Edu/Pro/Max 実現性 |
|---|---|---|
| P_round > 10⁻³ | **設計通り。Phase 0即時開始** | Edu: 確実、Pro: 確実、Max: 確実 |
| P_round = 10⁻⁴ | 性能10倍低下。QD追加 or WDM必要 | Edu: 確実、Pro: QD追加で確実、Max: 要検討 |
| P_round < 10⁻⁵ | CV pure断念 | DV v5.0にフォールバック |

**楽観シナリオ**: CW 13dBスクイージングでP_round > 10⁻²が達成されれば、
有効GKPレート1MHzとなり、Taros Proのゲートレートが30kHzに向上（設計の10倍）。
ただしP_round>10⁻²はδ窓を広げる必要があり、GKP忠実度とのトレードオフ。

**NTT現状**: CW 12.1dBが実証済み（リッジ型PPLN導波路）。
13dBはSiN clad改良で達成見込み（+0.9dB）。
15dBは中長期目標であり、Phase -1では13dBを基準とする。

---

## 7. NTTとの共同研究体制

| 役割 | 担当 | 提供 |
|---|---|---|
| PPLN OPA提供 | NTT研究所 | 12-13dB級CWスクイーザ |
| GKP理論・判定アルゴリズム | 理研量子情報グループ | postselectionプロトコル |
| 光学系組立・測定 | Taros実験チーム | ホモダイン・DAQ |
| Stim検証（並行） | 理論チーム | p_acc/P_round理論予測の精密化 |
| FPGA実装 | 制御チーム | リアルタイム判定 |

---

*本文書はTaros Portable設計の最大の不確定性（GKP postselection成功確率）を解消するための世界初の光学実験計画を定義したものである。装置BOM約560万円・5ヶ月(完全コスト約2,900万円)でPhase 0進行可否の最終判定データを取得する。*
