TomohiroTani28/Taros/x.md

評価:各主張の新規性
主張1: ノイズモデルの選択(部分的に既知)
CV光学系で位相論的ノイズが回路レベルノイズより適切であるという認識は、すでにコミュニティのコンセンサスに近い状態です:

Walshe et al. (2021)はマクロノードクラスタ状態でClifford gateとGKP誤り訂正を1ステップで実装し、論理エラー率を有限スクィージングのみから計算しました(本質的に位相論的) arXiv
Stafford et al. (2025)とFukui et al. (2018)も同様
Renault et al. (2025, Quantum)はend-to-endのスイッチレスCV-FTQCアーキテクチャを発表、12〜13 dBのクラスタスクィージング閾値を示しています Quantum Journal

ただし、3つのモデル(CC、位相論的、回路レベル)を1論文内で系統的に比較し、CVシステムではpmeas=pdatap*\text{meas} = p*\text{data}
pmeas=pdataが同じVeffV\_\text{eff}
Veffから自然に導かれることを明示した点は、整理として価値があります。Appendix Bの導出は教育的に有用です。
主張2: ソフト情報の必要性(ほぼ新規性なし)
これは最も問題のある主張です。Noh, Chamberland, Brandão (PRX Quantum 2022) がすでに本質的に同じことを示しています:

マッチンググラフのすべてのエッジ重みがGKP誤り訂正からのアナログ情報に基づいて、すべての症候測定ラウンドの完全な履歴を用いて動的に計算される Amazon
距離3の表面符号で3ラウンド中に2つのフォルトが発生する場合... アナログ情報を考慮しないと、MWPMデコーダが症候履歴と一致する誤った経路を選ぶ。これは表面GKP符号で論理Pauliエラーを引き起こす American Physical Society

さらに最近の Borah et al. (2025)も「リアルタイムソフト情報が回路レベルノイズ下での連結デコードに critical である」と明示的に結論しています。 arXiv
つまり「マルチラウンドでソフト情報が必須である」という定性的結論は2022年から確立済みです。本論文の「13〜75倍の改善」という具体的数値自体は新しい可能性がありますが、「これが新規発見である」という枠組みは正確ではありません。
主張3: 室温FTQC(コンセプト自体は新規性なし)
CV光学系での室温FTQCは、業界標準の主張です:

Bourassa et al. (2021, Xanadu Blueprint)で「室温量子計算を可能にする」と明示 arxiv
Aurora (Nature 2025)は「もつれ生成と論理ゲートはビームスプリッタとフォトダイオード(つまり室温部品のみ)で決定論的に実装される」と記載 Nature
QC82は2022年から室温フォトニックFTQC用集積チップを開発中 Future of Computing
古澤研の最新成果(2026)では、PPLN導波路OPAから12.1 dBのスクィージングを達成し、これは室温THzクロック量子計算への重要なマイルストーンとされる arXiv

新規性があるとすれば、特定の動作点(8.5〜9.3 dB)での具体的数値予測くらいです。
論文の質に関する懸念点
新規性とは別に、以下の問題が見られます:

参考文献[21]が "arXiv:2502.xxxxx" というプレースホルダーのまま — 査読前段階の原稿の可能性
参考文献[15] の「Matsuura et al., 'Mean-field analysis of quantum phase transitions in a bosonic model'」がノイズモデル等価性の文脈で引用されているが、タイトルが完全にずれている
「設計文書(design document)」への言及が複数あり、社内技術文書を学術論文化したものと思われる
d=7d=7
d=7で15,000ショット中3エラーという統計からpL=2.00×10−4p_L = 2.00\times10^{-4}
pL=2.00×10−4を導出している部分は、信頼区間が非常に広い(Poisson 95% CIで約4×10−54\times10^{-5}
4×10−5〜5.8×10−45.8\times10^{-4}
5.8×10−4)

総合評価
真に新規な貢献は限定的です。本論文は:

✓ **整理・統合論文(synthesis paper)**としては有用 — 既知の議論を1つのアーキテクチャ(マクロノードTDM + PPLN OPA)に対して数値的に統合
✓ 特定動作点での10710^7
107ショット規模のMonte Carlo検証は実用的価値あり
✗ 「physically correct noise model」「necessity not optimization」「establish room-temperature FTQC」などの強い表現は、Noh-Chamberland-Brandão (2022)、Bourassa (2021)、Aurora (2025)、Renault (2025) の既存成果に対して不当に新規性を主張している
✗ 一部参考文献の不備、社内文書的な記述
