TomohiroTani28/Taros/note.md

# TAROS — Investor Pitch

> **「電源コンセントとLANケーブルで動く 7-in-1 量子プラットフォーム」**

AC アダプタで動くデスクトップ誤り訂正型光量子コンピュータ (FTQC)。
**購入初日から6つの商用モードが稼働** — 量子優位証明を待たずに価値を提供する世界初のプラットフォーム。

---

## Slide 1: COVER

**TAROS**
Desktop Photonic Quantum Computer

AC アダプタで動く **デスクトップ誤り訂正型光量子コンピュータ**

Photonic CV + GKP + macronode TDM | 完全室温・109W | 1,350万〜2,550万円

**7-in-1 Quantum Platform** — 購入初日から商用価値を提供

Investor Pitch | Confidential | v4.0

---

## Slide 2: VISION — 7-in-1 量子プラットフォーム

> **「1台で7役。量子優位の証明を待たずに、購入初日から価値を届ける。」**

| Mode | 名称 | 応用 | 追加HW | 利用開始 |
|---|---|---|---|---|
| 1 | **FTQC** | 量子化学・量子重力・格子ゲージ理論 | なし | Phase 0+ |
| 2 | **CIM** | 組合せ最適化・物流（最大~2,000スピン） | なし(SW) | **購入即日** |
| 3 | **QRC** | 時系列予測・異常検知 | なし(SW) | **購入即日** |
| 4 | **QRNG** | 認証済み量子乱数 ~200Mbps | なし(SW) | **購入即日** |
| 5 | **Sensing** | SQL以下精密測定 | なし(SW) | **購入即日** |
| 6 | **Imaging** | サブショットノイズ顕微鏡 | なし(SW) | **購入即日** |
| 7 | **Tensor** | AI推論加速（フォトニック行列演算） | なし(SW) | **購入即日** |

**Mode 2-7は購入初日からSW変更のみで稼働。HW追加ゼロ。**

---

## Slide 3: THE PROBLEM — 量子コンピュータは「データセンター専用」で止まっている

超伝導・イオン方式は希釈冷凍機 (15mK) または高真空イオントラップを必須とし、原理的に小型化が不可能。研究室・教室・産業現場には届かない。

| | 冷却 | 消費電力 | サイズ | 価格 |
|--|---|---|---|---|
| 競合 | **15mK〜4K** | **30〜200kW** | **部屋規模** | **4.5〜22.5億円** |
| | 希釈冷凍機/He冷凍機 | 施設の専用配電 | 既存建屋に改装が必要 | 政府・大企業のみ |

結果として、量子コンピュータを「実機で触れる」研究者は世界で1万人未満。教育・研究のボトルネックに。

---

## Slide 4: OUR SOLUTION — 光だから、室温で動く。光だから、デスクに置ける。

| **7.5kg** | **109W** | **0K** | **1,800万円** |
|---|---|---|---|
| 重量 | 消費電力 | 冷凍機 | 価格 |
| Pro モデル(WDM込み) | USB-PD EPR 駆動 | 完全室温 | Pro モデル |

### HOW — 技術スタック

- **PPLN導波路OPA**: 13dB スクイーズド光生成 (NTT 12.1dB CW実証ベース)
- **macronode TDM クラスタ**: 光ファイバ遅延線で時分割に論理qubitを量産
- **GKP + 表面符号 (d=3/5/7)**: Phase 2+ PIC 統合で +1.8dB マージンを確保

### WHY NOW — 今、成立する理由

- **PPLN導波路の量産化**: NTT・住友・nLight が商用ライン稼働
- **Soft-info MWPM デコーダの成熟**: Noh-Chamberland 2022 で閾値1.5%が確立
- **Versal FPGA 27ns フィードフォワード**: 光-電気-光ループが ns 級で閉じる時代に
- **CVBQP ⊇ BQP 証明** (ITCS 2025): CV量子計算が標準QCと同等以上と理論的に確立

---

## Slide 5: DAY-1 VALUE — 量子優位を待たない。購入初日から6モードで収益化。

> **「量子コンピュータ業界最大の問題 — いつ役に立つのか? — に対する回答」**

**Mode 2: CIM (組合せ最適化)**
- OPAを閾値以下で動作 → コヒーレントイジングマシン
- 200m遅延線で最大~2,000スピン。車両ルーティング、スケジューリング
- **競合CIM製品 ($5K-50K) を内蔵。追加HWゼロ**

**Mode 3: QRC (量子リザーバ計算)**
- TDMループ = 量子リザーバコンピュータ (Nature Photonics 2026)
- 時系列予測、異常検知。14bit soft-infoでDV方式では不可能な高精度

**Mode 4: QRNG (量子乱数)**
- ホモダイン検出で真空ゆらぎを測定 → ~200Mbps認証済み量子乱数
- 商用QRNGモジュール ($5K-50K) のサイドプロダクト収益化

**Mode 5-7**: 量子センシング / 量子イメージング / フォトニックテンソル処理

**投資家にとっての意味**: FTQC完成前からMode 2-7で顧客価値を提供し、初期売上を確保。

---

## Slide 6: TECHNICAL EDGE — 性能の根拠。数字は文献と独立計算で裏付け済み

**パラメータチェーン**:

| 13dB → | L=0.27dB → | 9.3dB → | ~4.9×10⁻³ → | **~3.3×10⁻⁴** |
|---|---|---|---|---|
| PPLN OPA | 全劣化 (BSモデル) | 実効 σ_eff | p_phys | **p_L (d=7, MWPM)** |
| 生成スクイージング | PIC統合・GAWBS・PD QE込み | BS モデル | 物理エラー率 (erfc) | 製品要件 (理論限界 6.1×10⁻⁷) |

**閾値マージン**: Phase 2+ PIC 余裕 **+1.8dB** (postselection) — 製品要件 p_L ≈ 3.3×10⁻⁴ を達成

### CV方式の3つの決定的優位性

1. **14bit soft-info**: 全競合方式（超伝導/イオン/中性原子）の binary シンドロームに対し、デコーダ精度で本質的有利
2. **qumode = 無限次元ヒルベルト空間**: ボソニック場理論をネイティブにシミュレーション
3. **7-in-1**: 同一HWで7モード。量子優位証明前から6モードで商用価値を提供

---

## Slide 7: PRODUCT LINE — 単一プラットフォームで 3 製品。d=3/5/7 スケーリング戦略

### Taros Edu — 教育・QEC研究
- **1,350万円** / ~4.3kg / ~104W
- d=3, WDM 5ch, 論理qubit 1-10
- p_L ~10⁻² (MWPM)

### Taros Pro [FLAGSHIP] — 研究・VQE/QAOA
- **1,800万円** / ~7.5kg / ~109W
- d=5, WDM 8ch, 論理qubit 10-100
- p_L ~10⁻⁴ (MWPM)

### Taros Max — FTQC・量子化学
- **2,550万円** / ~9.7kg / ~112W
- d=7, WDM 7ch, 論理qubit 10-1,000+
- p_L ~3.3×10⁻⁴ (MWPM, L=0.27dB) / 理論限界 6.1×10⁻⁷

単一光学プラットフォーム + PMF遅延線の長さ調整のみで3製品を展開 → 量産設計コスト 1/3

---

## Slide 8: MARKET & COMPETITION — 「量子コンピュータの Raspberry Pi」ブルーオーシャン市場

### 競合比較

| 製品 | 方式 | サイズ | 消費電力 | 冷却 | 価格 | 顧客 |
|---|---|---|---|---|---|---|
| IBM Quantum System Two | 超伝導 | 部屋 | 200kW+ | 15mK | 22.5億円+ | 政府機関 |
| IonQ Forte | イオン | ラック×3 | 30kW | 高真空 | 4.5億円+ | 大企業 |
| Xanadu Aurora | フォトニック | ラック多数 | 100kW+ | 4K (SNSPD) | 15億円+ | クラウド事業者 |
| **Taros Pro** | **CV 光子** | **7.5kg** | **109W** | **完全室温** | **1,800万円** | **大学・研究所** |

### 市場規模

- **TAM** (量子情報全体): ~1,250機関 / 約225億円
- **SAM** (CV/QEC 適合層): ~650機関 / 約117億円
- **SOM Y3** (15%シェア): ~100台 / **約18億円**
- **SOM Y4** (拡大): ~200台 / **約36億円**

> **1,350万〜2,550万円帯にFTQC製品は存在しない — 独占的価格帯を確保。**

---

## Slide 9: VALIDATION — 机上の数字ではない。既に独立検証済み

| **100M** | **9件** | **156q** | **確定版** |
|---|---|---|---|
| shots | 文献 | 実機 | |
| **Stim 量子シミュレーション** | **公開文献との独立照合** | **IBM Quantum 実機検証** | **ノイズバジェット (BSモデル)** |
| p_phys=5×10⁻⁴, d=3/5/7 | Noh-Chamberland 2022, | ibm_fez (156 qubit) 上で | GAWBS, EO消光比, AWG, PIC |
| すべての論理エラー率予測を | Stafford-Menicucci 2025 | デコーダ計算量・サイクル | 統合損失など13項目をBSモデル |
| 約1億ショット規模で再現 | など9件の査読済論文と突合 | 時間を実測 | で個別計上。隠れた損失なし |

→ 設計書 14本 (システム / ノイズ / GKP / 位相ロック / FF / デコーダ / 機械 / 工業デザイン他) 公開 — 完全な技術DD可

---

## Slide 10: ROADMAP — 段階的検証 → プロトタイプ → 量産

| Phase -1 | Phase 0 | Phase 1 | Phase 2 |
|---|---|---|---|
| 12ヶ月 | 12-18ヶ月 | 12-18ヶ月 | 6-12ヶ月 |
| **原理検証** | **Edu試作 / Break-even** | **Pro 製品化** | **量産 (100台/年)** |
| **4.6億円** | **1.8億円** | **1.5億円** | **0.8億円** |

最重要マイルストーン: **G-EXP1 (開始後2ヶ月)** — 約800万円の装置直接費で Level A 成功確率を 25-35% → 50%超 へ引き上げ

累計: **約8.7億円** で量産可能製品まで到達

---

## Slide 11: RISK — リスクは透明に開示。レッドチーム評価を経た保守的見積り

### 主要リスクと緩和策

| リスク | 対応 |
|---|---|
| OPA 13dB パルス未実証 | NTT 12.1dB CW 実証済 → SiN clad改良で0.9dBギャップを埋める。Phase -1で検証 |
| MWPM / Soft-info 製品化 | Phase 0/1はUF 350nsで実証 → Phase 2+ PICでMWPM 510nsへ移行。製品要件 p_L~3.3×10⁻⁴ |
| G-EXP1 結果未取得 | 約800万円 / 約2,900万円 (完全コスト) で Phase -1 開始後2ヶ月に実施。失敗時はDV-FBQCフォールバック |

### フォールバック設計

| | CV (主トラック) | DV-FBQC (フォールバック) |
|--|---|---|
| | **7.5kg / 109W / 1,800万円** | 本体28kg (システム51kg) / 2.1kW / 約6,480万円 |

### 成功確率 (何らかの形でのデスクトップQC実現, Level B+)

- **CV pure** — **81%**
- **CV + QD** — **90%**

---

## Slide 12: CAPITAL EFFICIENCY — 段階的に検証、最小資本で世界初へ

### Go/No-Go ゲート — 失敗時の損失を限定しながら検証を進める

| **75万円** | **800万円** | **2,900万円** | **4.6億円** |
|---|---|---|---|
| 2週間 | 2ヶ月 | 5ヶ月 | 12ヶ月 |
| **原理判定** | **GKP光学実証** | **完全コスト** | **QEC Break-even** |
| GPU Stimシミュレーション | 装置直接費 | 人件費込み | 世界初の論理エラー抑制 |

### 競合の累計調達額 — 桁違いの資本効率

| PsiQuantum | IonQ | Xanadu | **Taros (計画)** |
|---|---|---|---|
| **約1,500億円超** | **約1,350億円** | **約560億円** | **約8.7億円** |

> **競合の100分の1以下の資本で、デスクトップFTQCを目指す。**

---

## Slide 13: FINANCIAL PROJECTION — 黒字化から36億円 ARR を視野

| 黒字化 | 粗利率 | Y3 ARR | Y4 ARR |
|---|---|---|---|
| Phase 2完了後1〜2年 | ~33% | **18億円** | **36億円** |
| 量産30-50台で達成 | 規模効果で逓増 | 100台 × 1,800万円 | 200台 (SAM 30%超) |

**投資論理**: 失敗時上限 4.6億円 (Phase -1)、成功時 ARR 36億円 (Y4) — リスク調整後リターン **~3.5倍** (81-90% × 36億 / 8.7億)

---

## Slide 14: 2030 MOONSHOT — Taros が拓く4つの未来産業

```
量子創薬(不老長寿) ←→ 仮想生物(量子脳NeuroQ)
        ↘              ↙
         Taros 7-in-1
        ↗              ↘
 ヒューマノイドロボット ←→ 3Dホログラム(QGH 10⁶倍)
```

### 量子脳 (NeuroQ)
NeuroQフレームワーク（CV量子直接互換）でC.elegans 302ニューロンをリアルタイムシミュレーション → ロボット知能。市場: $20B→$130B (2029)

### 量子ホログラム (QGH)
QFTで干渉パターンをN倍高速計算 (N=物体点数≈10⁶)。GKPのフーリエ構造 = ホログラムのフーリエ構造。6G要件 4.32Tbps

### 量子創薬・不老長寿
プロトントンネリング（DNA変異の量子起源）解明。セノリティクス分子の量子設計。P450シミュレーション精度 71%→94%

### ロボット知能
CIMで50ms制御壁突破。スクイーズド光でSQL超え力覚センシング

---

## Slide 15: ECOSYSTEM — 日本量子エコシステムとの連携

- **日本量子予算**: 2025年度 **1,009億円超**
- **JST ムーンショット**: 古澤PM (東大) — TDM方式、Tarosと直接関連
- **NEDO**: 浜松ホトニクス 30億円 — フォトニック量子
- **NTT PPLN**: 12.1dB CW世界記録 (2026/3) — Tarosの光源技術基盤
- **衛星搭載QC**: オーストリア製フォトニックQP、3L/10W、2025年打上げ成功 → Taros Portable (7.5kg) は衛星搭載に理想的

### 知財・規制

- Xanadu特許 114件/40ファミリー → **FTO調査をPhase -1で実施**
- EAR ECCN 4A906 輸出規制 → CV方式の「qubit」定義について法務確認
- **補助金**: JST/NEDO/AMED応募準備中

---

## Slide 16: THE ASK — Phase -1 シード: 4.6億円 / 12ヶ月

### RAISE

**4.6 億円**

シード資金で全14タスクを実行し、Phase 0 移行判定の全データを取得

### USE OF FUNDS

| 用途 | 金額 |
|---|---|
| 人件費 (11名 × 12ヶ月) | **約 2.9 億円** |
| 光学実験装置・部品 (PPLN OPA, EOM, ホモダイン検出系, 位相ロック) | **約 9,200万円** |
| GPU計算 / 外部委託 / 施設 (Stim, GKP実験委託, クリーンブース, 既存設備活用) | **約 8,300万円** |

### KEY MILESTONE

**G-EXP1 (開始後2ヶ月)**: CW GKP光学実験。装置直接費約800万円で Level A 成功確率を 50%超 へ引き上げ

---

## Slide 17: CLOSING

### THE FUTURE OF QUANTUM IS

# デスクトップに来る。

室温 109W で動く誤り訂正型量子コンピュータを、世界の研究室・教室・企業 R&D に。
**購入初日から7つのモードで価値を届ける。**

次のステップ: 技術 DD パッケージ (設計書14本) のレビュー → タームシート協議 → Phase -1 着手

TAROS · Desktop Photonic Quantum Computer · v4.0

---

*為替前提: 1USD = 150円*
*p_L ≈ 3.3×10⁻⁴ はV_non-loss込み、Δ・RIN未包含。全込み推定: 5-9×10⁻⁴ (p_L≲10⁻³達成)。Phase -1実測で確定。*
