TomohiroTani28/Taros/analysis/phase-minus1-execution.md

# Phase -1 統合実行計画（12ヶ月間）

**Document ID**: PQC-PHASE-M1-v1.0
**Status**: Ready for Execution
**投資額**: 約9,190万円（新規タスク直接費約5,590万円 + 新規設備3,000万円 + 消耗品・予備600万円）
+ 既存約8,250万円（H1-H5タスク約7,800万円 + 既存設備活用450万円）= 約1.7億円
**期間**: 12ヶ月 (GKP光学実験10ヶ月+T10/T11が8ヶ月超過のため正式延長)
**総予算（人件費込み）**: 約4.6億円（タスク約1.7億円 + 人件費約2,400万円/月x12=約2.9億円）

> 6人CVチーム（6名のCV専門家チーム）の分析により、PPLN導波路OPA採用で
> **QDなしでもFTQC要件達成が設計上可能**と予測。
> Phase -1の最優先をQDなしCV pure構成の検証に変更。詳細: `design/`

---

## 1. 目的

Phase -1完了後のGo/No-Go判定に必要な全データを取得する。判定結果により:

- **Go**: ハイブリッドCV+QD方式 (42kg, 約1.5kW, 約5,700万円)
- **No-Go**: DV-FBQC v5.0 Desktop (28kg, 2.1kW, 約6,480万円)

どちらの結果でもデスクトップQCは実現する。

---

## 2. タスク一覧（時系列順）

### 新規追加タスク（最優先）

| ID | タスク | 投資 | 期間 | 担当 | 成果物 |
|----|---|---|---|---|---|
| **T0a** | **GKP有限エネルギー (Δ) 測定 + PPLN導波路OPA単体評価** | 740万円 (490+250) | 4ヶ月（実験2+予備2） | CV計算チーム | (1) **Δ<0.15 Wigner検証**: ホモダイン測定18,000点 + GPU再構成で±0.02精度。Go基準: Δ<0.12 (Full Go) / 0.12-0.15 (Conditional / Phase 1b最適化必須) / ≥0.15 (No-Go → DV fallback)。（2）CW OPAスクイージング実測値 (目標>12dB)。NTT OPA開始直後に発注→開始後2ヶ月着、中間判定開始後2ヶ月末(10dB以上Go)。予備期間は条件最適化 or 代替品評価に充当。**ML-SLM空間モード最適化（+40万円）**: SLM+カメラでOPA→LO空間モードミスマッチ損失を4%→<1%に低減、σ_eff +1.2-1.5dB改善見込み（arXiv:2603.02744）。02_opa-source §6.1参照 |
| **T0b** | **QDなしGKP+表面符号 Stim + Union-Find soft-info検証** | 450万円 (300+150) | 3ヶ月 | 理論チーム | (1) **p_L(d, σ_eff, QD=0) 精密値**: BSモデル Phase 1 σ_eff=8.5dB (L=0.39dB,13dB), Phase 2+ PIC σ_eff≈9.3dB (L=0.27dB,13dB) / 理論限界10.8dB (L=0.15dB)。(2) **UF soft-info threshold検証**: 100個のシンドロームセット×5万shot×d=3/5/7で p_th_UF≥0.9%判定。soft-info重み付けクラスタ成長 vs hard-decision UF 比較。Go基準: p_th_UF≥0.9% (Full Go) / 0.8-0.9% (Conditional / Phase 1b で MWPM並列) / <0.8% (No-Go → MWPM forced, Phase 0コスト+10%)。(3) **MWPM Blossom-V d=7 FPGA timing検証**: VE2802 @400MHz で ≤700ns達成確認（timeout fallback設定）。|
| **T0c** | **macronode TDM光学系プロト設計** | 450万円 | 3ヶ月 | CV計算チーム | OPA2+BS3+遅延2の光学配置 |

> **T0a-T0cの結果でQDなし構成の成立を確認。
> 成立時はPhase 0のコストが約6,450万円→約3,450万円に削減。**

### 2.1 即時開始（開始後1-2ヶ月）

| ID | タスク | 投資 | 期間 | 担当 | 成果物 |
|----|---|---|---|---|---|
| **T1** | GKP+表面符号Stimシミュレーション | 750万円 | 4ヶ月 | 理論チーム | p_L(d, sigma, N_QD)マップ |
| **T2** | InP QD 1550nmデバイス評価 | 1,200万円 | 4ヶ月 | 光源チーム | V, g^2(0), 輝度の同時測定 |
| **T3** | Floquet-GB [[72,12,6]] Stimシミュレーション | 450万円 | 2ヶ月 | 理論チーム | erasure閾値確定 |
| **T4** | OptQC G-QuATスペック評価（H1） | 750万円 | 3ヶ月 | CV計算チーム | スクイージング実測値 |

### 2.2 中期開始（開始後2-4ヶ月）

| ID | タスク | 投資 | 期間 | 担当 | 成果物 | 依存 |
|----|---|---|---|---|---|---|
| **T5** | PT205 + WI-SNSPDコム型4-8個統合冷却試験 | 1,800万円 | 6ヶ月 | 冷却チーム | 全素子@2.5K動作確認 | — |
| **T6** | ファイバ化バルクOPAラックマウントプロト（H3） | 1,500万円 | 6ヶ月 | CV計算チーム | 12dB密閉モジュール | T4結果参照 |
| **T7** | ワンチップ統合PIC設計DRC検証 | 750万円 | 4ヶ月 | PICチーム | レイアウトGDS完成 | — |
| **T8** | GKP+表面符号CVノイズモデルStim（H4） | 1,200万円 | 4ヶ月 | 理論チーム | CV方式での必要スクイージング | T1結果 |

### 2.3 後期開始（開始後5-7ヶ月）

| ID | タスク | 投資 | 期間 | 担当 | 成果物 | 依存 |
|----|---|---|---|---|---|---|
| **T9** | QD 2個+OPAによるGKP生成実験設計（H2準備） | 750万円 | 3ヶ月 | 光源+CVチーム | 実験計画書+部品調達 | T1, T4 |
| **T10** | 小型4Kクライオ+QD+PNR-SNSPD統合設計（H5） | 1,800万円 | 6ヶ月 | 冷却+光源チーム | 非ガウスモジュール設計 | T2, T5 |
| **T11** | ソフトウェアスタックLayer 1-2基盤実装 | 1,200万円 | 6ヶ月 | 制御チーム | FPGA RTOS + HALプロトタイプ | — |

---

## 3. ガントチャート

```
        M1   M2   M3   M4   M5   M6   M7   M8   M9   M10  M11  M12
T1  ████████████████                                                    GKP Stim
T2  ████████████████                                                    InP QD評価
T3  ████████                                                            Floquet-GB Stim
T4  ████████████                                                        OptQC G-QuAT
T5            ████████████████████████                                  PT205+WI-SNSPD
T6            ████████████████████████                                  OPAラックマウント
T7            ████████████████                                          PIC設計DRC
T8                  ████████████████                                    CV Stim
T9                              ████████████                            GKP実験設計
T10                             ████████████████████████████            非ガウス統合
T11                       ████████████████████████████████████          SW Layer 1-2
        ^                 ^              ^                         ^
      開始             中間レビュー    M7レビュー             Phase -1完了
```

---

## 4. Go/No-Go判定フレームワーク

### 4.1 Phase -1末（開始後12ヶ月）のマイルストーン判定

| 判定ID | 項目 | Go基準 | 統計要件 | データソース |
|---|---|---|---|---|
| **G1** | GKP忠実度 | F_GKP > 0.90 (Stim, QD=2, sigma=10dB) | 95% CL下限 > 0.88 (10^4 shots以上) | T1結果 |
| **G1b** | GKP有限エネルギーΔ | **Δ < 0.15** (Wigner tomography格子ピーク幅σ_W≈Δから直接推定。ホモダイン測定時はσ_meas≈Δ/√2) | 95% CL上限 < 0.18 (10^3 reconstructions以上) | T0a結果(光学実験時) |
| **G1c** | Union-Find soft-info threshold | **p_th_UF ≥ 0.9%** (Phase 0-1デコーダ選択ゲート。MWPM fallback設定は700ns timeout) | 95% CL下限 > 0.88% (10^5 syndrome shots, d=3/5/7全d値確認) | T0b結果 |
| **G2** | InP QD 1550nm | V > 0.92 | 95% CL下限 > 0.90 (HOM dip 10^3カウント以上) | T2結果 |
| **G3** | Floquet-GB erasure閾値 | > 20% | 3σ有意 (Stim 10^7 shots, p<0.001) | T3結果 |
| **G4** | PT205冷却 | 全SNSPD >95% @2.5K | 全素子で10^3光子検出、DE>95%確認 | T5結果 |
| **G5** | OPAスクイージング | σ_gen ≥12dB CW (目標13dB) | RBW=100kHz, 3回独立測定の平均 ±0.3dB | T6結果 |
| **G6** | ホモダインPD量子効率 | QE ≥ 98% (1550nm, カスタムPD) | 校正済み光パワーメータ比較、3回測定 | 新規: PD評価タスク |

**Go/No-Go測定プロトコル**:

- 全判定は**95%信頼区間の下限**がGo基準を満たすことを要求する
- 実験者2名による独立測定でGo/No-Go一致を確認（不一致時は3名目仲裁）
- G5の「≥12dB」は**σ_gen（OPA出力CW生成値）**を指す。σ_eff（実効値）はσ_genと損失から算出（BSモデル）
- 測定機器: ホモダイン検出器(QE>95%), スペクトラムアナライザ(RBW<100kHz), 14bit ADC
- **PLL BW直接測定**: G5判定時にPLL BW≥200kHz(Conditional Go)/≥500kHz(Full Go)を併せて測定。
  測定法: Pilot Tone位相変調→復調信号のクローズドループ伝達関数をネットワークアナライザで取得。

### 4.2 判定ロジック

```
G1(GKP) AND G1b(Δ<0.15) AND G5(OPA) → CV+ハイブリッド方式 Primary Go
    |
    +-- IF G1c(p_th_UF≥0.9%)
    |   └─ Phase 0-1: Union-Find decoder primary (350ns)
    |
    +-- ELSE IF 0.8%≤p_th_UF<0.9%
    |   └─ Phase 0-1: Conditional (UF+MWPM parallel評価, +$200K FPGA)
    |
    +-- ELSE (p_th_UF<0.8%)
    |   └─ Phase 0: MWPM forced (Phase 0コスト+10%, ~50万円)
    |
    +-- AND G2(InP QD) → InP QD直接（QFC-Free）構成
    |
    +-- NOT G2 → GaAs QD + QFC構成

NOT G1 OR NOT G1b OR NOT G5 → DV-FBQC方式にフォールバック
    |
    +-- AND G3(Floquet-GB) AND G4(PT205) → v5.0 Desktop構成
    |
    +-- NOT G3 → 表面符号フォールバック（論理qubit 2-4個）
```

### 4.3 判定マトリクス（全組合せ）

| G1 | G2 | G3 | G4 | G5 | 方式 | 構成 | 確率 |
|----|----|----|----|----|---|---|---|
| Go | Go | — | Go | Go | CV+QD (InP) | 42kg, 約5,700万円 | 25% |
| Go | NG | — | Go | Go | CV+QD (GaAs+QFC) | 68kg, 約1.4億円 | 18% |
| NG | Go | Go | Go | — | DV Desktop v5.0 | 28kg, 約6,480万円 | 15% |
| NG | NG | Go | Go | — | DV Desktop (QFC付) | 35kg, 約8,700万円 | 12% |
| NG | — | NG | Go | — | DV表面符号フォールバック | 35kg, 約7,500万円 | 8% |
| — | — | — | NG | — | PT205不適合→大型冷却器 | 70kg, 約1.05億円 | 5% |
| Go | — | — | — | NG | OPA不安定→CV断念 | DV構成に移行 | 12% |
| NG | — | NG | NG | NG | 全No-Go | 2ラック構成に後退 | **5%** |

**デスクトップQC実現確率（何らかの形で）: 約81% (Level B+)**
(ベイジアン相関分析§5.1準拠。T0b Go後約87%に回復。
詳細: `analysis/risk.md` §5.1)

---

## 5. リソース配分

### 5.1 人員計画

| チーム | 人数 | Phase -1タスク | 月額コスト |
|---|---|---|---|
| 理論 (符号+シミュレーション) | 2名 | T1, T3, T8 | 450万円 |
| 光源 (QD+QFC) | 2名 | T2, T9, T10 | 450万円 |
| CV計算 (OPO+ホモダイン) | 2名 | T4, T6 | 450万円 |
| PIC設計 | 1名 | T7 | 225万円 |
| 冷却+検出 | 2名 | T5, T10 | 450万円 |
| 制御SW | 2名 | T11 | 375万円 |
| **合計** | **11名** | | **約2,400万円/月** |

12ヶ月合計: 約2,400万円 x 12 = 約2.9億円（人件費）
タスク投資: 約9,190万円（新規）+ 約8,250万円（H1-H5）= 約1.7億円

※タスク分類: 新規(T0a-T0c,T1-T3,T7,T11)=約5,590万円、
既存H1-H5対応(T4=H1,T6=H3,T8=H4,T9=H2,T5+T10=H5)=約7,800万円、
設備3,000万円、消耗品600万円、計約1.7億円（450万円差は既存設備活用分）。

**Phase -1総コスト: 約4.6億円**（人件費約2.9億円 + タスク約1.7億円）

### 5.2 設備・環境

| 設備 | 用途 | 調達 |
|---|---|---|
| GPU計算クラスタ (A100x4) | T1, T3, T8 Stimシミュレーション | クラウド (75万円/月) |
| 光学テーブル + クリーンブース | T2, T4, T6 実験 | 既存 or 1,500万円 |
| PT205評価機 | T5 冷却試験 | 900万円（Bluefors/Cryomech） |
| FPGA開発ボード (VE2302) | T11 SW開発 | 30万円 |

---

## 6. 月次レビュースケジュール

| 月 | レビュー内容 | 主要判定 |
|----|---|---|
| M2 | T1-T4キックオフ確認 | 計画通り開始? |
| M3 | T3完了（Floquet-GB Stim） | G3判定可能 |
| M4 | T1中間結果 + T4完了（G-QuAT） | GKP方向性 + CV基盤確認 |
| M5 | T1完了 + T2完了 | **G1 + G2 判定** |
| M6 | T7完了（PIC設計） + T8中間 | PIC製造可否 |
| M7 | T5中間 + T6中間 | 冷却+OPA進捗 |
| M8 | T6完了（OPAスクイージング）+ T9中間 | **G5判定** |
| M9 | T10中間（GKP実験）+ T8完了 | GKP進捗確認 |
| M10 | T10完了（GKP生成）+ T11中間 | **G4判定** |
| M11 | T11完了（FPGA検証）+ T5完了 | 全技術要素統合確認 |
| **M12** | **Phase -1完了レビュー** | **全G判定 → Phase 0計画確定** |

12ヶ月に拡張。GKP実験(T10)10ヶ月+T10/T11の8ヶ月超過を反映。

---

## 7. Phase 0-1b への接続

Phase -1の判定結果に基づき、Phase 0-2+を以下の構成で実行:

### Phase 0 (12-18ヶ月: Break-even検証)
- **CVクエア**: QD 2個+OPAでGKP+表面符号(d=3), σ_eff=8.5dB, L=0.39dB
- **デコーダ**: Union-Find primary (350ns, p_th_UF≥0.9%)
- **投資額**: 約3.5-6.5億円（G1c Go/No-Go結果により±10%）
- **目標**: p_L≲10⁻² break-even確認

### Phase 1a (12-18ヶ月: 検証継続)
- **CVクエア**: Phase 0継続（σ_eff=8.5dB, d=3-5）
- **デコーダ**: UF soft-info最適化、MWPM並列準備
- **投資額**: Phase 0と同等（新規コスト +$0、FPGA開発+$200K if Conditional Go）
- **目標**: UF/MWPM性能確認（どちらがPhase 2へ進むか判定）

### **Phase 1b (6-9ヶ月: PIC統合)** ← NEW
**これまでのロードマップ(Phase 0→1→2)では、WDM導入時σ_eff低下でd=5不可になる。Phase 1bを追加して問題を解決:**

| 要素 | Phase 1a | Phase 1b | Phase 2 |
|---|---|---|---|
| WDM ch数 | 5ch fixed | 5ch maintained | 8ch目指し |
| Fiber-PIC coupler損失 | 0.06dB (5ch) | 0.15dB (mature) | 0.06dB (optimized) |
| σ_eff | 8.5dB | 8.8dB | 9.3-10.8dB |
| d値 | 3-5 | 5 stable | 7 |
| PIC投資 | $0 (deferral) | $500K (dev+proto) | $500K (mass manuf) |
| デコーダ | UF/MWPM eval | 決定した方が継続 | MWPM primary |
| 論理qbit | 3-5個 | 5-9個 | 25-49個 |
| 目標 | d=3-5実証 | **d=5安定化・PIC成熟** | d=7製品仕様達成 |

**Phase 1bの位置づけ**:
- WDMスケーリング(5→8ch)とPIC成熟は同時進行不可（リスク高）
- Phase 1b: WDM 5ch固定、PIC coupler loss最適化に専念（MMI再設計、taper幾何最適化）
- Phase 2: PIC coupler成熟後、必要に応じ8ch展開検討

**Cost & Timeline Impact**:
- Phase 1b投資: $500K（Phase 0→1bへ移動、新規ではない）
- Timeline: Phase 0-1a 24-36ヶ月 + Phase 1b 6-9ヶ月 = Phase 2まで 30-45ヶ月（従来計画と一致）
- Go/No-Go: Phase 1a完了時点で「Phase 1bの費用対効果判定」実施

| Phase -1結果 | Phase 0構成 | Phase 1b実施 | Phase 2目標 |
|---|---|---|---|
| CV+QD Go (G1c=Go) | QD 2個+OPA, UF primary (σ_eff=8.5dB, d=3-5) | Phase 1a後に実施 | d=7 MWPM (L=0.27dB, σ_eff=9.3dB) |
| CV+QD Conditional Go (0.8%≤p_th<0.9%) | QD 2個+OPA, UF+MWPM parallel | Phase 1a で決定 | MWPM d=7 or UF d=5+ |
| DV v5.0 Go | PT205+InP QD, 表面符号(d=5) | 実施不要（PIC不依存） | DV スケール (d=7→9) |
| 混合結果 | 両方式試作 | 判定待機 | CV/DV最適構成確定 |

---

*本文書はTarosプロジェクトのPhase -1（12ヶ月間）の全タスク・判定基準・リソース配分を定義し、Go/No-Go判定への確実な到達を保証するものである。*
