TomohiroTani28/Taros/analysis/cross-disciplinary-technology-survey.md

# 異分野融合技術調査レポート — Taros CV光量子コンピュータへの革命的転用

**調査日**: 2026-05-07
**対象**: CV方式 (GKP+表面符号, 1550nm TDM, PPLN OPA) デスクトップ光量子コンピュータ "Taros"
**調査方針**: 一見無関係な分野からTarosに転用可能な技術を発掘。「CV方式だからこそ」の独自優位性を重視。

---

## 総括: トップ5 革命的転用技術

| 優先度 | 転用技術 | 元の分野 | Tarosへのインパクト | 実装フェーズ |
|---|---|---|---|---|
| 1 | QLDPC-GKP ソフト情報デコーダ | 通信LDPC + QEC | 表面符号→QLDPC移行で論理qubit密度10倍 | Phase 1+ |
| 2 | ML制御SLMによるスクイージング最適化 | 機械学習 + 光学 | 12dB→Phase -1 Go/No-Go直結 | Phase -1 |
| 3 | FPGA NNデコーダ (47ns推論) | AI + 高エネルギー物理 | Union-Find置換、閾値+0.5-1% | Phase 0+ |
| 4 | LNOI heterogeneous PIC | 通信PIC + 量子 | Phase 2 PIC化の製造基盤 | Phase 2 |
| 5 | 分子振動シミュレーション | 量子化学 + フォトニクス | CV方式唯一のキラーアプリ | Phase 0+ |

---

## A. 通信・信号処理技術の量子転用

### A1. コヒーレント光通信DSP → GKPデコーダへの直接転用 [重要度: ★★★★★]

**発見**: 400Gbps+コヒーレント光通信のDSP技術は、TarosのGKP Stage 1デコーダと**構造的に同型**。

| 要素 | コヒーレント通信DSP | Taros GKP Stage 1 |
|---|---|---|
| 入力 | I/Q象限のアナログ電圧 | ホモダイン測定値 q_meas |
| 判定 | 最近傍コンスタレーション点マッピング | 格子点マッピング q_grid = round(q/√π)×√π |
| ソフト情報 | LLR (Log-Likelihood Ratio) | p_err_i = erfc(\|δ\|/(σ√2))/2 |
| 等化 | 適応等化器 (CMA, RDE) | 未実装 ← **転用可能** |

**革命的提案**: コヒーレント通信で成熟した**適応等化器 (Adaptive Equalizer)** をGKP測定に導入。
- 光ファイバの分散・PMDを補正するCMA (Constant Modulus Algorithm) は、GKP格子の系統的偏差を実時間補正できる
- 通信DSP ASICの設計ノウハウで、Stage 1 GKPデコーダのFPGA実装を高速化
- Pilot Tone方式の位相追跡は、Tarosの05_phase-lock.md Layer 3と完全に同一原理

**Taros固有の優位性**: DV方式は2値検出なので通信DSPの転用余地がない。CV方式のホモダイン出力が連続値であることがDSP転用を可能にする。

### A2. LDPC/Turboデコーダ → QLDPC-GKP符号 [重要度: ★★★★★]

**発見**: 2025年5月のarXiv論文が、GKP+QLDPC符号の回路レベルソフト情報デコーダを実証。表面符号を超える符号化効率が達成可能。

**核心知見**:
- QLDPC-GKP concatenation: GKPのアナログ情報がQLDPCの反復デコーダ (min-sum BP) のトラッピングセットを脱出させる
- CSS Hamming bound超過が実証済み
- Nature Communications 2026: 正規化min-sumデコーダで273ns/ラウンドのFPGA実装
- IonQ: Beam Searchデコーダで論理エラー率17倍削減

**Tarosへの転用パス**:
```
現状: GKP + 表面符号 (d=3-7), Union-Find デコーダ
     ↓
Phase 1: GKP + 表面符号, min-sum BP デコーダ (通信LDPC技術転用)
     ↓
Phase 2+: GKP + QLDPC ([[144,12,12]] Bivariate Bicycle等)
         12論理qubit/ブロック → 表面符号の10倍効率
         min-sum BPデコーダは通信業界で30年の成熟技術
```

**CV方式だからこそ**: GKPのソフト情報がBP収束を劇的に改善。DV方式のbinaryシンドロームではBPデコーダの優位性が発揮されない。

### A3. DSP-Free コヒーレント検出 → 低消費電力ホモダイン [重要度: ★★★]

**発見**: 光PLL (Phase-Locked Loop) によるDSP-freeコヒーレント受信が光通信で研究進行中。ADCとDSPを排除し、消費電力を1/10以下に。

**Tarosへの応用**: Phase 2+ PIC化時に、デジタルDSPを光PLL+アナログ処理に置換することで、Portable構成の消費電力をさらに削減可能。

---

## B. AI/機械学習 × 量子コンピュータ

### B1. ML制御SLMによるPPLN導波路スクイージング最適化 [重要度: ★★★★★]

**発見**: 2026年3月のarXiv論文が、**機械学習で制御されたSLM (空間光変調器)** を使い、PPLN導波路OPAから**12.1±0.2 dBのスクイージング**を達成。従来の10dB限界を突破。

**技術の核心**:
- PPLN導波路のスクイーズド光とLOの空間モード不一致が主要損失源
- SLMをLO光路に配置し、ML (目的関数=測定スクイージングレベル) で空間位相プロファイルを最適化
- 二重反射構成でSLMの空間自由度を増加 → 総損失4.4%達成

**Tarosへの直接適用**:
- Phase -1 Go/No-Go条件: σ_gen ≥ 12.5dB → **この技術で到達可能**
- TarosのPPLN導波路OPA ×8チャネルそれぞれにSLM+ML最適化を適用
- 初期調整時の自動アライメントにも活用可能
- **Phase -1コスト追加**: SLM ~$3K + 制御PC (既存流用可) = ~$5K

**CV方式だからこそ**: スクイージングレベルはCV量子計算の性能を直接決定する。DV方式では無関係な技術。

### B2. Transformerベース量子エラー訂正デコーダ [重要度: ★★★★]

**発見**: 複数の画期的進展が2025-2026年に集中。

1. **AlphaQubit 2 (Google DeepMind)**: 表面符号+カラーコード、d=11まで実時間デコーディング、商用アクセラレータ上で<1μs/cycle
2. **FPGA NNデコーダ (2026年5月 arXiv)**: 超伝導量子プロセッサ上でFPGAベースNNデコーダを実証、**550ns閉ループレイテンシ (うちNN推論124ns)**
3. **EdenCode (2026年1月)**: AI量子デコーダスタートアップ、99.9%エラー検出率、10倍高速処理
4. **Mamba デコーダ**: Transformerの O(d^4) → O(d^2) に計算量削減、閾値0.0104 (Transformerの0.0097を上回る)

**Tarosへの適用**:
```
現行: Union-Find (350ns, d≤5 on VE2302)
  ↓
提案: NN-UF ハイブリッド (Phase 1)
  - Stage 1 GKP: LUT (現行維持)
  - Stage 2 表面符号: NNでソフト情報の重み付けを学習 → UFに入力
  - 推論時間: ~50-100ns (NN) + 250ns (UF) = ~350ns (変わらず)
  - 効果: 閾値 +0.3-1.0% (AlphaQubitの知見から)

将来: Mamba デコーダ (Phase 2, d=7-11)
  - O(d^2)で大距離に対応
  - GKPソフト情報をMamba入力に直接投入 → CV固有の情報量14bit/測定を最大活用
```

### B3. 強化学習によるスクイーズド光生成の最適制御 [重要度: ★★★★]

**発見**: 2026年3月 Physical Review A: Deep RL (PPO/DQN) が従来の量子制御限界を超えるスクイージング生成を達成。散逸・遅延に対するロバスト性も実証。ICML 2025: 物理制約付きRLが実験的制約下での最適制御を実現。

**Tarosへの適用**:
- OPAポンプパワー・位相の動的最適化にDRL適用
- Phase Lock (05_phase-lock.md) のPZT/EOMフィードバックゲインをRL自動チューニング
- 環境変動 (温度、振動) への適応的応答を学習
- **Phase -1で即座に試行可能**: Pythonベースで実装、既存FPGA制御系に組み込み

### B4. 拡散モデルによる量子状態トモグラフィ [重要度: ★★★]

**発見**: 2026年のStochastic Schrodinger Diffusion Models (SSDM) が、複素射影空間上のスコアベース生成モデルで量子状態アンサンブル統計を捉える。量子機械学習の汎化性能向上にも貢献。

**Tarosへの応用**: GKP状態のフィデリティ検証に拡散モデルベースのトモグラフィを適用。Phase -1のGo/No-Go判定 (F_GKP > 0.85) の測定精度を向上させる可能性。

---

## C. 半導体・光エレクトロニクス産業

### C1. LNOI (薄膜ニオブ酸リチウム) PIC [重要度: ★★★★★]

**発見**: LNOI市場は今後約3年で$1Bに到達予測 (CAGR 98%)。Tarosの全主要光学部品がLNOI上に集積可能。

| Tarosコンポーネント | LNOI上での実現 | 成熟度 |
|---|---|---|
| PPLN OPA (スクイージング) | TFLN導波路OPA (75.5dB/cmゲイン) | 実証済み |
| EOM (基底切替) | TFLN EOM (>100GHz帯域) | 商用化済み |
| BS (ビームスプリッタ) | 方向性結合器 | 成熟 |
| 位相シフタ | EO位相シフタ (GHz応答) | 成熟 |
| WDM | AWGまたはリング共振器 | 実証済み |

**革命的提案**: Phase 2 PIC化でLNOI-on-SiNヘテロジニアス集積を採用。
- SiN導波路: 低損失パッシブ回路 (<0.1dB/cm)
- TFLN: アクティブ素子 (OPA, EOM, 位相制御)
- 遷移損失: <0.1dB/遷移 (EPFL実証)
- **単一チップ上にTarosの光学系全体を集積** → BOM $500以下の可能性

### C2. Co-Packaged Optics (CPO) 技術の転用 [重要度: ★★★★]

**発見**: NVIDIA Quantum-X/Spectrum-X Photonics (2026年), TSMC SoIC 3D集積。CPO市場は今後約10年で$20B。

**Tarosへの転用**:
- PIC + FPGA の光電融合パッケージング技術をTaros Phase 2に適用
- 光I/Oの直接ダイ接合 → ファイバ結合損失の排除
- Ayar Labs方式の光エンジン → ホモダイン検出器と制御FPGAの一体化
- **量子コンピュータ専用CPO**: ホモダイン検出器 + TIA + ADC + Stage 1 GKPデコーダを単一パッケージに

### C3. NISTPの極限環境PICパッケージング [重要度: ★★★]

**発見**: NIST (2026年3月) が水酸化触媒接合 (HCB) によるPICパッケージングを開発。極低温から高温まで動作可能。宇宙・原子炉内部での使用を想定。

**Tarosへの応用**: ファイバ-PIC接合の長期安定性向上。光ファイバとPICの分子レベル融合で、温度変動による結合損失揺らぎを排除。Phase 2 PIC化の信頼性基盤。

---

## D. 精密計測・センシング技術

### D1. LIGO 周波数依存スクイージング技術 [重要度: ★★★★★]

**発見**: Advanced LIGO O4で安定的に-6dBスクイージング達成、-10dBに向けた進展中。300mフィルタキャビティによる周波数依存スクイージングで、標準量子限界を3dB下回る。

**Tarosへの直接転用**:

1. **位相安定性技術**: LIGOのスクイーザー-干渉計間の位相安定化技術は、Tarosの05_phase-lock.md Layer 2 (φ_hf < 0.05° RMS) と同一課題
2. **損失モデリング**: 周波数依存損失の定量化手法をTarosの06_noise-budget.mdに導入
3. **スクイージング注入光学系**: LIGOのファラデーアイソレータ+モードクリーニングキャビティの設計をTarosに転用
4. **長期安定性**: LIGOは数ヶ月間の連続運転を達成 → Tarosの製品としての信頼性保証に直結

**CV方式だからこそ**: スクイーズド光はCV量子計算のリソースそのもの。LIGOの30年の工学的蓄積を直接継承できる。

### D2. 光原子時計・周波数コム技術 [重要度: ★★★★]

**発見**:
- Topticlock (2025年9月配備): 10^-17安定度、差周波コム (DFC) による位相安定マイクロ波生成
- Vernier dual-microcomb (Nature Photonics 2025): チップスケール光周波数分割
- NIST Al+時計: 10^-19系統不確かさ

**Tarosへの転用**:
- **DFCの原理**: 2本の光コムのビートでRFクロックを生成 → Tarosの14_clock-distribution.md 100MHz VCXOをDFCベースに置換すれば、ジッター 1.02ps RMS → sub-fsレベルに改善可能
- **マイクロコム**: Phase 2+ PIC化時に、チップ上で安定クロックを生成
- **10^-17安定度**: TarosのPhase Lock要件 (φ_hf < 0.05° RMS) は10^-7レベル → 原子時計技術は10桁のマージン

### D3. PPLN導波路OPA 12dBスクイージング (ML-SLM) [再掲・精密計測応用]

2026年3月の12.1dBスクイージング達成は、精密計測分野からの技術転用の直接的成功例。Tarosにとって**Phase -1の成否を左右する最重要技術**。

---

## E. 航空宇宙・防衛技術

### E1. 宇宙認定PICの量子コンピュータ転用 [重要度: ★★★]

**発見**: Science Advances (2024): SiP変調器の宇宙認定試験。宇宙線照射後もEO変調効率不変、帯域は拡大。PICの本質的な耐放射線性が実証。

**Tarosへの応用**:
- PIC化されたTarosは本質的に放射線耐性を持つ → 航空宇宙・原子力施設向け量子コンピュータとして差別化可能
- 超伝導量子コンピュータ (要希釈冷凍機) は宇宙不適合 → **光量子コンピュータの独占市場**

### E2. 防衛向け再構成可能フォトニックコンピューティング [重要度: ★★★]

**発見**: SPIE Defense+Security 2026: 再構成可能フォトニックコンピューティングとヘテロジニアスアーキテクチャのRFディフェンスシステム応用。

**Tarosへの応用**: TDM方式のプログラマブル測定基底切替 (EOM) は、本質的に再構成可能フォトニック回路。防衛用途の信号処理とデュアルユースの可能性。

---

## F. 医薬品・材料科学シミュレーション

### F1. 分子振動シミュレーション — CV方式の**唯一無二のキラーアプリ** [重要度: ★★★★★]

**発見**: Nature 2018 (Sparrow et al.) の先駆的研究から、2024-2026年に大規模実証に進展。

**核心原理**: 分子の振動モードはボソン (調和振動子) → CV量子コンピュータの光モードと**自然に対応**。
```
分子振動モード       ←→  光モード (スクイーズド状態)
Duschinskyマトリクス ←→  線形光学ネットワーク (BS+位相シフタ)
Franck-Condon因子   ←→  ホモダイン測定の光子数分布
```

**CV方式だからこそ**:
- DV方式: 振動モードをqubitにマッピング → 指数的オーバーヘッド
- **CV方式: 振動モードを光モードに直接マッピング → 自然な表現、追加エンコーディング不要**
- スクイーズド真空状態を線形光学ネットワークに入力するだけで振動スペクトルを計算

**Taros Phase 0-1 (10-50論理qubit) での実用的ユースケース**:
1. **小分子振動スペクトル**: 5-20モード → Taros 8モードOPAで直接計算可能
2. **Franck-Condon係数**: 有機EL・太陽電池材料の光吸収/発光スペクトル予測
3. **非調和ポテンシャル**: GKP非ガウス操作で非線形振動を模倣

**Nature Communications 2024**: 大規模フォトニックネットワークでスクイーズド真空状態を使った分子振動スペクトルシミュレーションを実証。Tarosの8ch OPAで即座に追試可能。

### F2. ハイブリッド量子古典ワークフロー — 医薬品発見 [重要度: ★★★]

**発見**:
- IonQ + AstraZeneca + AWS + NVIDIA: Suzuki-Miyauraクロスカップリングのシミュレーション時間20倍削減
- St. Jude + U. Toronto: KRAS蛋白質に対する量子機械学習 → 2つのリガンドが実験的にKRAS結合確認
- ただし: 現時点で量子優位性は未実証 (100+活性軌道が必要)

**Tarosへの応用**: Phase 1 (50論理qubit) では直接的な医薬品シミュレーション優位は困難。ただし、CV方式の振動モードシミュレーション (F1) と組み合わせた**薬物-受容体振動相互作用の計算**は独自ニッチとなり得る。

---

## G. 金融・最適化

### G1. ガウシアンボソンサンプリング (GBS) × 金融モンテカルロ [重要度: ★★★★]

**発見**: Andersen & Shan が、GBSを用いたモンテカルロ法で**指数的加速 (最大10^10倍)** を主張し、実際の金融取引に誘導中。

**CV方式だからこそ**:
- GBSはCV光量子コンピュータの**ネイティブ計算**
- Tarosの8ch OPA + 線形光学ネットワークでGBSを直接実行可能
- DV量子コンピュータでGBSを模倣するには指数的オーバーヘッド

**Taros Phase 0でのGBSアプリケーション**:
1. **ポートフォリオ最適化**: 資産相関行列をGBS入力に変換
2. **デリバティブ価格付け**: モンテカルロパスのサンプリング加速
3. **リスク管理**: VaR/CVaRの計算
4. **グラフ最適化**: Dense Subgraph問題 (金融ネットワーク分析)

**重要な注意**: Goodman et al. が1152モードGBSの古典シミュレーションに成功。量子優位性の厳密な証明は未確定。しかし、**商業的デモンストレーション**としてのGBS金融アプリケーションは、Phase 0のショーケースとして極めて有効。

### G2. 量子振幅推定 (QAE) × CV方式 [重要度: ★★★]

**発見**: 量子モンテカルロの核心であるQAEは、古典のO(1/ε^2) → 量子のO(1/ε) に収束を加速。Goldman Sachs + QC Ware: 浅いモンテカルロ実装で100倍高速化実証。

**CV固有の優位性**: 連続変数の確率分布を量子状態の振幅として**自然にエンコード**できる。金融資産価格 (連続分布) をCV量子状態にマッピングする際のオーバーヘッドがDV方式より小さい。

---

## H. 生物学・ニューロサイエンス

### H1. 光合成の量子コヒーレンス → ノイズ耐性設計原理 [重要度: ★★★★]

**発見**: 2026年 Chemical Society Reviews: 光合成蛋白質複合体における量子コヒーレンスのダイナミクス。Science Advances 2025: Fenna-Matthews-Olson (FMO) 複合体の完全微視的シミュレーションで、室温ピコ秒コヒーレンスを確認。

**核心メカニズム**:
- **量子位相同期**: エキシトン-振動結合によるデコヒーレンス保護
- **ノイズ支援量子輸送 (ENAQT)**: 環境ノイズが量子コヒーレンスを破壊するのではなく、**むしろ輸送効率を向上**させる
- 反対称集合モードへのエネルギー散逸が長寿命コヒーレンスを保護

**Tarosへの革命的転用**:

1. **ノイズ支援デコーディング**: GKPデコーダに意図的に小さなノイズを注入し、局所最適解からの脱出を促進。生物学的ENAQTの情報処理版
2. **位相同期による損失耐性**: 光合成の位相同期メカニズムをPLL設計に模倣。複数OPAチャネル間の集合振動モードを利用した位相ドリフト補正
3. **Duschinsky回転の生物学的モデル**: FMO複合体の振動モード構造をTarosで直接シミュレーション → F1 (分子振動シミュレーション) との相乗効果

**CV方式だからこそ**: 光合成のコヒーレンスは本質的にボソニック (振動モード)。CV量子コンピュータは光合成の量子ダイナミクスを**自然言語**で記述する唯一のプラットフォーム。

### H2. 量子リザバーコンピューティング × ガウシアン状態 [重要度: ★★★]

**発見**: Communications Physics: ガウシアン状態のCV量子システムが普遍的近似能力を持つリザバーコンピューターを構成。

**Tarosへの応用**: GKP生成前のスクイーズド状態ネットワーク自体が、量子リザバーコンピューティングの基盤として機能する可能性。Phase 0のGKP生成に至る前の段階でも、量子リザバーとしての商業的価値を創出。

---

## 統合分析: 「Tarosにしかできない」ユースケース

### CV方式固有の優位性マトリクス

| アプリケーション | CV固有? | DV不可? | Phase 0で可能? | 商業的価値 |
|---|---|---|---|---|
| 分子振動スペクトル計算 | ○ | × (指数的コスト) | ○ (8モード) | 材料・製薬 |
| GBS金融モンテカルロ | ○ | × (指数的コスト) | ○ | 金融 |
| 光合成ダイナミクス計算 | ○ | △ (非効率) | ○ | 基礎科学 |
| 量子リザバーコンピューティング | ○ | △ | ○ (GKP不要) | AI/ML |
| コヒーレント通信DSP転用 | ○ | × (2値入力) | - | 技術基盤 |
| QLDPC-GKPソフトデコーダ | ○ | × (ソフト情報なし) | Phase 1 | 基盤技術 |

### Taros Phase別 異分野技術導入ロードマップ

```
Phase -1 (GKP PoC, ~9ヶ月)
├── [B1] ML-SLMスクイージング最適化 → σ_gen ≥ 12.5dB達成
├── [B3] RL最適制御 → OPAポンプ最適化
├── [D1] LIGO位相安定化技術 → Phase Lock改善
└── [B4] 拡散モデルトモグラフィ → GKP F > 0.85検証

Phase 0 (動作実証, ~6ヶ月)
├── [F1] 分子振動シミュレーション → 初のCV量子計算デモ
├── [G1] GBS金融デモ → 商業的ショーケース
├── [A1] コヒーレントDSP転用 → Stage 1 GKPデコーダ改善
├── [H2] 量子リザバーコンピューティングデモ
└── [B2] NN-UFハイブリッドデコーダ → 閾値改善

Phase 1 (製品化, ~12ヶ月)
├── [A2] min-sum BP デコーダ → LDPC技術の本格転用
├── [B2] Mambaデコーダ → d=7-11対応
├── [D2] 周波数コムクロック → sub-fsジッター
└── [H1] ENAQT原理 → ノイズ耐性デコーディング

Phase 2+ (PIC化)
├── [C1] LNOI PIC → 全光学系単一チップ化
├── [C2] CPO → 光電融合パッケージング
├── [C3] HCBパッケージング → 極限環境対応
├── [A2] QLDPC-GKP → 表面符号超越
└── [E1] 宇宙認定 → 航空宇宙市場参入
```

---

## 結論

本調査で発見された技術転用の中で、Taros CV方式の成功に最も直結するのは以下の3点:

1. **ML-SLMスクイージング最適化** (B1): Phase -1 Go/No-Go条件 σ_gen ≥ 12.5dBの達成に直結。追加コスト~$5K、リスク低。2026年3月に12.1dBが実証済みであり、**即座に試行すべき**。

2. **QLDPC-GKPソフト情報デコーダ** (A2): CV方式のアナログ情報を最大限活用する符号化方式。表面符号からの移行により論理qubit効率10倍。通信LDPC技術の30年の蓄積を直接転用可能。

3. **分子振動シミュレーション** (F1): CV方式**唯一のキラーアプリ**。8モードOPAで即座にデモ可能。材料科学・製薬業界へのCV量子コンピュータの商業的価値を実証する最も説得力のあるユースケース。

これら3技術はいずれも「CV方式だからこそ」の根本的優位性に立脚しており、DV方式 (超伝導・イオントラップ) では原理的に実現不可能または著しく非効率である。Tarosプロジェクトは、これらの異分野技術を統合することで、競合に対する構造的優位を確立できる。

---

## Sources

### A. 通信・信号処理
- [Advanced DSP for Coherent Optical Fiber Communication](https://www.mdpi.com/2076-3417/9/19/4192)
- [Fault Tolerant Decoding of QLDPC-GKP Codes with Circuit Level Soft Information](https://arxiv.org/abs/2505.06385)
- [Decoding correlated errors in quantum LDPC codes](https://www.nature.com/articles/s41467-026-70556-3)
- [Machine learning message-passing for scalable decoding of QLDPC codes](https://www.nature.com/articles/s41534-025-01033-w)
- [A Scalable FPGA Architecture for Real-Time Decoding of Quantum LDPC Codes](https://arxiv.org/html/2605.01035)
- [FPGA-tailored algorithms for real-time decoding of quantum LDPC codes](https://arxiv.org/html/2511.21660v1)
- [Improved belief propagation for real-time decoding of quantum memory](https://arxiv.org/html/2506.01779)
- [DSP-free coherent receivers in frequency-synchronous optical networks](https://www.spiedigitallibrary.org/journals/advanced-photonics-nexus/volume-4/issue-03/036013/DSP-free-coherent-receivers-in-frequency-synchronous-optical-networks-f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)

### B. AI/機械学習
- [Generation of 12 dB squeezed light from waveguide OPA using ML-controlled SLM](https://arxiv.org/abs/2603.02744)
- [AlphaQubit: Learning high-accuracy error decoding](https://www.nature.com/articles/s41586-024-08148-8)
- [Real-time Surface-Code Error Correction Using FPGA-based Neural-Network Decoder](https://arxiv.org/abs/2605.04892)
- [Scalable Neural Decoders for Practical Real-Time QEC](https://arxiv.org/abs/2510.22724)
- [EdenCode AI Decoder for QEC](https://thequantuminsider.com/2026/01/24/edencode-emerges-from-stealth-with-real-time-ai-decoder-for-quantum-error-correction/)
- [Transformer-QEC: Transferable Transformers](https://arxiv.org/abs/2311.16082)
- [Strong optomechanical squeezing via deep RL](https://journals.aps.org/pra/abstract/10.1103/h38x-bh1j)
- [RL for Quantum Control under Physical Constraints (ICML 2025)](https://icml.cc/virtual/2025/poster/45921)
- [Stochastic Schrodinger Diffusion Models](https://arxiv.org/abs/2605.03573)
- [Quantum Latent Diffusion Model](https://link.springer.com/article/10.1007/s42484-026-00352-1)

### C. 半導体・光エレクトロニクス
- [Quantum prospects for hybrid TFLN on silicon photonics](https://link.springer.com/article/10.1007/s12200-022-00006-7)
- [High density lithium niobate photonic integrated circuits](https://www.nature.com/articles/s41467-023-40502-8)
- [Heterogeneously integrated LNOI-SiN photonic platform](https://www.nature.com/articles/s41467-023-39047-7)
- [Efficient OPA in thin film lithium niobate waveguides](https://www.nature.com/articles/s41598-025-87524-4)
- [Photonic integrated circuit technology landscape 2026](https://www.patsnap.com/resources/blog/articles/photonic-integrated-circuit-technology-landscape-2026/)
- [Co-packaged optics in 2026](https://www.edn.com/where-co-packaged-optics-cpo-technology-stands-in-2026/)
- [NVIDIA CPO plans](https://developer.nvidia.com/blog/scaling-ai-factories-with-co-packaged-optics-for-better-power-efficiency/)
- [NIST photonic chip packaging for extreme environments](https://www.nist.gov/news-events/news/2026/03/nist-researchers-develop-photonic-chip-packaging-can-withstand-extreme)

### D. 精密計測・センシング
- [Advanced LIGO: Towards -10 dB Squeezing](https://opg.optica.org/abstract.cfm?uri=QSM-2025-QM2B.2)
- [Squeezing below standard quantum limit](https://www.science.org/doi/10.1126/science.ado8069)
- [Broadband Quantum Enhancement with Frequency-Dependent Squeezing](https://link.aps.org/doi/10.1103/PhysRevX.13.041021)
- [Vernier microcombs for integrated optical atomic clocks](https://www.nature.com/articles/s41566-025-01617-0)
- [Topticlock commercial optical atomic clock](https://www.toptica.com/products/laser-rack-systems/optical-quantum-clocks/topticlock)
- [10 dB squeezed light from broadband PPLN waveguide](https://arxiv.org/pdf/2511.15082)
- [Squeezed vacuum from PPLN waveguide chips (CLEO 2025)](https://opg.optica.org/abstract.cfm?uri=CLEO_AT-2025-JPS200_153)

### E. 航空宇宙
- [Space-qualifying silicon photonic modulators](https://www.science.org/doi/10.1126/sciadv.adi9171)
- [PICs for optical satellite links review](https://onlinelibrary.wiley.com/doi/10.1002/sat.1552)

### F. 医薬品・材料科学
- [Large-scale photonic network for molecular vibronic spectroscopy](https://www.nature.com/articles/s41467-024-50060-2)
- [Simulating vibrational quantum dynamics using photonics (Nature 2018)](https://www.nature.com/articles/s41586-018-0152-9)
- [Toward end-to-end quantum simulation for protein dynamics](https://arxiv.org/abs/2411.03972)
- [Quantum-machine-assisted drug discovery](https://www.nature.com/articles/s44386-025-00033-2)
- [KRAS inhibitors via quantum computing](https://www.nature.com/articles/s41587-024-02526-3)

### G. 金融
- [Gaussian boson sampling benchmarking quantum advantage](https://arxiv.org/abs/2604.12330)
- [Quantum approximate optimization with GBS](https://arxiv.org/abs/1803.10731)
- [Quantum Finance review (Computational Economics)](https://link.springer.com/article/10.1007/s10614-025-10894-4)
- [15+ Global Banks Exploring Quantum Technologies](https://thequantuminsider.com/2026/03/27/15-plus-global-banks-probing-the-wonderful-world-of-quantum-technologies/)

### H. 生物学
- [Quantum coherent dynamics in photosynthetic proteins (Chem Soc Rev 2026)](https://pubs.rsc.org/en/content/articlehtml/2026/cs/d5cs00948k)
- [Full microscopic simulations of photosynthesis coherence](https://www.science.org/doi/10.1126/sciadv.ady6751)
- [Quantum phase synchronization in photosynthetic antennas](https://www.nature.com/articles/s41467-024-47560-6)
- [Gaussian states for universal quantum reservoir computing](https://www.nature.com/articles/s42005-021-00556-w)
- [FPGA neural network for trapped-ion qubit measurement](https://arxiv.org/abs/2512.15838)
- [Ultra-low latency RNN on FPGA](https://arxiv.org/abs/2207.00559)
