TomohiroTani28/Taros/analysis/roadmap.md

> **[DEPRECATED] 本文書はDV-FBQC v4.0時代のロードマップであり、CV方式への移行後は完全に陳腐化しています。**
> **予算規模が10倍異なります（本文書: 70億円 vs CV方式: 約8.7億円）。参照禁止。**
> **CV方式の最新ロードマップは `design/00_overview.md` §ロードマップ を参照してください。**
> **CV方式の詳細実行計画は `analysis/phase-minus1-execution.md` を参照してください。**
> **本文書は `archive/` への移動候補です。**

# セクション12: 段階的構築ロードマップ

## 12.1 フェーズ定義（Phase統合版）

> **Phase体系**: Phase -1〜3をPhase 0のサブフェーズとして再編し、
> 新たにPhase 1（小型実用機）・Phase 2（次世代小型機）を追加した。

| Phase | 期間 | 目標 | 投資額 | Go/No-Go判定基準 | 構成 |
|---|---|---|---|---|---|
| **Phase 0a** (旧Phase -1) | 開始後約12ヶ月 | 机上検証 + コンポーネント単体テスト | 約7,500万円 + 約8,850万円 | Stim閾値シミュレーション完了、6-QD HOM V>0.90、18ch SNSPD >95%、LNOI PIC <1.5dB | 計算資源 + 最小動作構成（3m2、約1.8億円） |
| **Phase 0b** (旧Phase 0) | 開始後約1-2年 | 基礎実証 + 2光子fusion + 最小論理qubit | 約7.5億円 + 約5,850万円 | 4ch QD+QFC動作、SNSPD 16個、fusion忠実度>80%、d=3エラー抑制実証（3σ有意） | 小規模テストベンチ |
| **Phase 0c** (旧Phase 1) | 開始後約2-3年 | スケール検証 | 約22.5億円 | 64ch動作、SNSPD 256個、d=6 | 中規模実証機 |
| **Phase 0d** (旧Phase 2) | 開始後約3-6年 | フルスケール研究機 | 約74.3億円 | SNSPD 8,192個、100論理qubit | 8ラック+2クライオ(60m2) |
| **Phase 0.5** | 開始後約2.5年 | **16-QD同時運転デモ** | — | 全ペアHOM visibility >0.93 | **Phase 0の拡張** |
| **Phase 1** | 開始後約3-4年 | **小型実用機** | **約3.75-4.5億円** | 16論理qubit、床面積5-6m2 | **2ラック+サイドカー** |
| **Phase 2** | 開始後約5-6年 | **次世代小型機** | **約2.25億円** | 48論理qubit、床面積4m2 | **1ラック+外部冷却** |

> **世界的専門家レビュー追加 — Phase 0.5（開始後約2.5年）: 16-QD同時運転デモ**
> Phase 0bからPhase 0cへの移行前に、16個のQDモジュールの同時運転デモを実施する。
>
> - **Go条件**: 全ペア（120組）のHOM visibility >0.93を達成
> - **Go**: Phase 1のスケジュール通り進行
> - **No-Go**: Phase 1を1-2年延期し、QD均一性改善に集中投資
>
> このマイルストーンは、QD均一性のスケーリングがPhase 1の最大リスクであるという
> 7人の専門家の合意に基づく。

> **注記**: Phase 0d（フルスケール研究機）とPhase 1（小型実用機）は時期的に重複する。
> Phase 0dで得られた技術知見を基にPhase 1の設計を確定し、
> Phase 1は独立したハードウェアとして新規製造する。

## 12.2 各フェーズの定量基準

### 12.2.1 Phase -1: 机上検証（約7,500万円）

**目標**: 設計パラメータの理論的整合性を確認し、Phase 0の仕様を確定する。

**実施内容**:

1. **Stimシミュレーション**: SHYPS / 4D HPC / 表面符号の3符号について、
   erasure率とdepolarizing率の閾値マップを作成
2. **SHYPS confinement property検証**:
   理論的にconfinement propertyが成立する条件を厳密に導出
3. **損失バジェット精査**: 各コンポーネントのデータシートベースでの積算検証
4. **HCF遅延線設計**: 600m x 1,000本のスプール配置、温度安定化の熱シミュレーション
5. **行列読出しアーキテクチャ設計**: 128x64のタイミング解析、クロストーク評価

**Go/No-Go基準**:

| 基準ID | 評価項目 | Go条件 | No-Go時の対策 |
|---|---|---|---|
| P-1.1 | erasure閾値（Stim） | SHYPS or HPCでp_erasure閾値 > 50% | 表面符号にフォールバック |
| P-1.2 | depolarizing閾値（Stim） | 選択符号でp_depol閾値 > 2.0% | fusion品質要求の再検討 |
| P-1.3 | SHYPS confinement | 理論的に成立条件が明確 | 4D HPCに切替 |
| P-1.4 | 損失バジェット整合性 | η_total > 0.10（全経路） | コンポーネント見直し（QFC仕様変更等） |
| P-1.5 | HCF熱安定化 | 位相ドリフト < π/100 per cycle | アクティブ位相補償回路追加 |

### 12.2.2 Phase 0: 基礎実証（約7.5億円）

**目標**: 主要コンポーネントの単体・結合動作を実証する。

**構成**:

- QDモジュール: 4個（925nm GaAs）
- QFCモジュール: 4個
- Si3N4チップ: 4個
- LNOI EOチップ: 8個
- HCF 600m: 10本
- SNSPD: 16個（4x4行列読み出し）
- クライオスタット: 1台（既存機流用可）
- FPGA: 2枚
- 符号: d=4（SHYPS or 表面符号）

**Go/No-Go基準**:

| 基準ID | 評価項目 | Go条件 | 測定方法 |
|---|---|---|---|
| P0.1 | QD単一光子純度 | g^2(0) < 0.02 | HBT測定 |
| P0.2 | QD不可弁別性 | HOM visibility > 0.95 | Hong-Ou-Mandel干渉 |
| P0.3 | QFC変換効率 | η_QFC > 0.40（端面間） | 入出力パワー比 |
| P0.4 | QFC後の光子純度 | g^2(0) < 0.05 | HBT測定（QFC後） |
| P0.5 | SNSPD行列読出 | 16ch同時動作、クロストーク < 1% | 較正光源による全ch試験 |
| P0.6 | fusion成功確率 | > 50%（boosted fusion） | 4光子一致計数 |
| P0.7 | d=4符号erasure耐性 | 実測閾値がStim予測の80%以上 | 意図的erasure注入試験 |
| P0.8 | HCF遅延安定性 | 位相変動 < 0.1 rad / hour | MZI干渉計による連続測定 |
| P0.9 | サイクル時間 | < 5μs（d=4） | トリガ-検出-フィードバック全系 |

### 12.2.3 Phase 1: スケール検証（約22.5億円）

**目標**: 中規模システムで論理量子ビット動作を実証する。

**構成**:

- QDモジュール: 8個
- QFCモジュール: 8個
- Si3N4チップ: 24個
- LNOI EOチップ: 48個
- HCF 600m: 100本
- 光スイッチ行列: 2台
- SNSPD: 256個（16x16行列読み出し）
- クライオスタット: 1台（BlueFors LD-400）
- FPGA: 6枚
- GPU: 1台
- 符号: d=6（選定済み符号）

**Go/No-Go基準**:

| 基準ID | 評価項目 | Go条件 | 根拠 |
|---|---|---|---|
| P1.1 | 論理エラー率 | p_L < 10^-2 per logical cycle | d=6で閾値以下動作の確認 |
| P1.2 | erasure率（実測） | p_erasure < 閾値の70% | 閾値マージンの確保 |
| P1.3 | depolarizing率（実測） | p_depol < 閾値の50% | 最大リスク項目、厳格に評価 |
| P1.4 | SNSPD歩留 | 256個中有効 > 240個（94%） | フルスケール95%目標の妥当性検証 |
| P1.5 | 行列読出スケーラビリティ | 256chでクロストーク < 2% | 8,192個への外挿可能性 |
| P1.6 | サイクル時間 | < 3μs（d=6） | フルスケール2μs目標への進捗 |
| P1.7 | HCF 100本同時安定動作 | 全本で位相変動 < 0.05 rad/hour | 1,000本への外挿可能性 |
| P1.8 | マジック状態蒸留 | 蒸留成功率 > 10% | 専用レーンの実証 |
| P1.9 | デコーダレイテンシ | FPGA全系 < 1μs | リアルタイムフィードバック要件 |

### 12.2.4 Phase 2: フルスケール（約74.3億円）

**目標**: 100論理量子ビット、実用レベルの論理エラー率を達成する。

**Go/No-Go基準**（段階的）:

| 基準ID | マイルストン | 評価項目 | Go条件 | 時期 |
|---|---|---|---|---|
| P2.1 | SNSPD全数実装 | 8,192個の動作率 | > 95%（7,782個） | +6ヶ月 |
| P2.2 | HCF全数実装 | 1,000本の位相安定性 | 全本 < 0.05 rad/hour | +9ヶ月 |
| P2.3 | QD全数実装 | 12個の不可弁別性 | 全ペアHOM > 0.95 | +12ヶ月 |
| P2.4 | d=8符号動作 | 論理エラー率 | p_L < 10^-4 | +18ヶ月 |
| P2.5 | 100論理qubit | 同時動作 | 100 logical qubit x d=8 | +24ヶ月 |
| P2.6 | 最終性能 | 論理エラー率 | p_L < 10^-6 | +30ヶ月 |

## 12.3 符号選択ゲート

3パス並行設計（SHYPS / 4D HPC / 表面符号）の選択スケジュール:

```
開始        ── Phase -1 開始 ────────────────────────────
              |
開始後約8ヶ月  +- Gate 0: Stim閾値マップ完成
              |   → 3符号の閾値比較表を作成
              |   → 明らかに劣る符号があれば候補から除外
              |
開始後約14ヶ月 +- Gate 1: SHYPS confinement property検証
              |   → 成立: SHYPS + HPCの2候補に絞り込み
              |   → 不成立: HPCに一本化（表面符号は保険として保持）
              |
開始後約20ヶ月  +- Gate 2: HPC閾値シミュレーション結果
              |   → HPCの実効閾値がp_depol > 1.5%: HPC有力
              |   → HPCの実効閾値がp_depol < 1.0%: SHYPSまたは表面符号
              |
開始後約2年   +- Gate 3: Phase 0実測データによる最終選択
              |   → 実測erasure率・depolarizing率を3符号にプロット
              |   → 最大マージンの符号を選定
              |   → 選定結果をPhase 1設計にフィードバック
              |
開始後約2.5年  +- Phase 1: 選定符号でのd=6実証開始
```

**判定マトリクス**:

| 条件 | 選択符号 | 理由 |
|---|---|---|
| SHYPS confinement成立 & p_erasure < 30% | **SHYPS** | erasure耐性が最高（閾値 約50%）、リソース効率最良 |
| confinement不成立 & HPC p_depol閾値 > 1.5% | **4D HPC** | depolarizing耐性が表面符号より優位 |
| confinement不成立 & HPC閾値 < 1.0% | **表面符号** | 最も成熟した符号、実装リスク最小 |
| 全閾値が実測ノイズに対しマージン < 2x | **設計見直し** | コンポーネント品質改善または設計変更 |

> **重要**: 符号選択はPhase 0終了時（開始後約2年）に確定する。
> それ以前はSi3N4チップおよびFPGAデコーダを3符号対応で設計する。
> これにより追加コスト約7,500万円が発生するが、
> 選択ミスによるやり直しリスク（推定約4.5-7.5億円）を回避できる。

## 12.4 Phase間ゲート条件一覧

### 12.4.1 ゲート条件マトリクス

各Phase移行には以下のゲート条件を全て満たす必要がある。

#### Phase 0b → Phase 0c ゲート（基礎実証 → スケール検証）

| ゲートID | 条件 | 定量基準 | 検証方法 |
|---|---|---|---|
| G-0bc-1 | QD単一光子品質 | g^2(0) < 0.02, HOM > 0.95 | HBT測定、HOM干渉 |
| G-0bc-2 | QFC変換効率 | η_QFC > 0.40 | 入出力パワー比 |
| G-0bc-3 | SNSPD行列読出 | 16ch動作、クロストーク < 1% | 較正光源試験 |
| G-0bc-4 | d=4符号erasure耐性 | Stim予測の80%以上 | erasure注入試験 |

#### Phase 0c → Phase 0d ゲート（スケール検証 → フルスケール）

| ゲートID | 条件 | 定量基準 | 検証方法 |
|---|---|---|---|
| G-0cd-1 | 論理エラー率 | p_L < 10^-2 (d=6) | 実機QEC実験 |
| G-0cd-2 | SNSPD歩留 | 256個中有効>240個(94%) | 全ch動作試験 |
| G-0cd-3 | デコーダレイテンシ | FPGA全系 < 1μs | タイミング実測 |
| G-0cd-4 | depolarizing率 | p_depol < 閾値の50% | fusion品質測定 |

#### Phase 0d → Phase 1 ゲート（フルスケール研究機 → 小型実用機）

| ゲートID | 条件 | 定量基準 | 検証方法 |
|---|---|---|---|
| G-01-1 | PT冷凍機でのSNSPD動作 | 検出効率>95% @ 2.5K | Phase 0でのPT冷凍機テスト |
| G-01-2 | 集積型QDモジュール | 128モジュールの同時動作 | Phase 0cの拡張テスト |
| G-01-3 | HCF 300m遅延の安定性 | 位相変動 < 0.05 rad/hour | 連続安定性測定 |
| G-01-4 | 表面符号d=6での論理qubit | 16論理qubitの同時QEC | Phase 0dでの実証 |
| G-01-5 | Deployability目標 | 設計上の床面積≤7-8m2、消費電力≤9.5kW | 設計レビュー |

#### Phase 1 → Phase 2 ゲート（小型実用機 → 次世代小型機）

| ゲートID | 条件 | 定量基準 | 検証方法 |
|---|---|---|---|
| G-12-1 | Quantum LDPC符号の実機検証 | p_L < 10^-3 (d=6) | Phase 1実機テスト |
| G-12-2 | ASICデコーダの動作 | レイテンシ < 500ns | テストチップ評価 |
| G-12-3 | モノリシックPICの製造 | 歩留 > 80% | ファウンドリ試作 |
| G-12-4 | PT冷凍機一体型の検証 | 2,000 SNSPD安定動作 | プロトタイプテスト |
| G-12-5 | Deployability目標 | 設計上の床面積≤4m2、消費電力≤6kW | 設計レビュー |

### 12.4.2 ゲート不合格時の対策

| 不合格ゲート | 影響 | 対策 |
|---|---|---|
| G-01-1（PT冷凍機でのSNSPD） | Phase 1で希釈冷凍機が必要 | Phase 1の床面積を12m2に拡大（Deployability目標未達） |
| G-01-4（16論理qubit） | Phase 1の論理qubit数削減 | 4-8論理qubitで運用開始、段階的拡張 |
| G-12-1（LDPC符号） | Phase 2で表面符号を使用 | 論理qubit数を16に据置（48目標は達成不能） |
| G-12-2（ASICデコーダ） | FPGA継続使用 | 消費電力目標6kW→8kWに緩和 |

### 12.5 Phase 0 具体的実験計画（7人専門家会議確定版）

Phase 0は以下の3段階で実施する。総コスト約1.65億円、総期間24ヶ月。

#### Phase 0a: コンポーネント単体テスト（開始後3-10ヶ月、8ヶ月、約8,850万円）

3実験を並行実施:

**実験1: 6-QD同時動作テスト** — QDチップ(24デバイス)上の6 QDでHOM visibility V>0.90を
全ペアで実証。コスト約3,150万円。

**実験2: 18ch SNSPDアレイ検証** — 検出効率>95%を16ch以上で実証。コスト約2,400万円。

**実験3: LNOI PIC検証** — 6 fusionゲート+12スイッチ。全経路挿入損失<1.5dB。
コスト約3,300万円。

Go/No-Go判定: 開始後約10ヶ月末

#### Phase 0b: 2光子fusion実証（開始後11-16ヶ月、6ヶ月、約1,650万円）

**実験4: QD光子ペアのType-II fusion** — Phase 0aの装置を統合。
η>0.50かつfusion忠実度>80%が成功基準。

Go/No-Go判定: 開始後約16ヶ月末

#### Phase 0c: 最小論理qubit実証（開始後17-25ヶ月、9ヶ月、約4,200万円）

**実験5: d=3表面符号エラー抑制実証** — 6 QD + 18 SNSPD + PIC + SiN遅延線 + FPGA。
d=3→d=5でのエラー率改善を統計的に実証（3σ有意）。

---
