TomohiroTani28/Taros/research/01_rt-ft-architecture/PAPER_EN.md

# Fault-Tolerant Quantum Error Correction at Room Temperature: Noise Model Selection and GNN Decoder Advantage for Continuous-Variable Photonic Architectures

**Author**: Tomohiro Tani

*Independent Researcher*

---

## Abstract

We demonstrate that room-temperature continuous-variable (CV) photonic quantum computers based on GKP-encoded surface codes can achieve fault-tolerant error suppression without cryogenic infrastructure. Through systematic numerical simulations totaling over 10^7 shots, we show that the standard circuit-level noise model---designed for discrete-variable systems with noisy entangling gates---overestimates logical error rates by one to two orders of magnitude when applied to CV homodyne architectures. We identify the phenomenological model with equal data and measurement error rates (p_meas = p_data) as a physically motivated noise model for CV systems, where homodyne detection always succeeds and the sole noise source is GKP displacement noise propagated through passive beam-splitter networks. Furthermore, we establish that soft-information minimum-weight perfect matching (MWPM) decoding is not merely an optimization but a necessity: it provides over an order of magnitude improvement in multi-round simulations and determines whether the system is above or below threshold. At the operating parameters of a room-temperature PPLN OPA photonic system (sigma_eff = 8.5 dB), our CV-motivated model yields p_L(d=5) = 4.33 x 10^-4 (13 errors in 30,000 shots, 95% CI: [2.5, 7.3] x 10^-4), well below the 10^-3 product threshold. Finally, we show that a lightweight graph neural network (GNN) decoder with 4,033 parameters outperforms soft-info MWPM by up to 14x at d=7 under correlated noise (rho >= 0.08), with the advantage increasing monotonically with code distance (1.9x at d=3, 7.8x at d=5, 14x at d=7) — a regime where MWPM performance degrades. These results establish that cryogenic infrastructure is not a fundamental requirement for fault-tolerant quantum computing, and that ML-based decoders can extend the fault-tolerance operating envelope of CV photonic systems.

---

## I. Introduction

### A. The cryogenic bottleneck

Every major fault-tolerant quantum computing (FTQC) proposal to date relies on cryogenic or ultra-high-vacuum infrastructure. Superconducting platforms operate at $`\sim 4`$ mK with dilution refrigerators consuming tens of kilowatts \[1, 2\]. Trapped-ion systems require $`\sim 10^{-11}`$ torr vacuum chambers \[3\]. Even photonic proposals based on discrete-variable (DV) encoding demand single-photon detectors operating at $`\sim 0.8`$ K \[4, 5\]. This cryogenic requirement constitutes a dominant bottleneck for scalability, cost, and deployability.

A natural question arises: *Is cryogenic infrastructure a fundamental physical requirement for fault-tolerant quantum computing, or merely an artifact of the particular platforms and encodings that have been pursued?*

### B. Continuous-variable photonic quantum error correction

Continuous-variable (CV) quantum computing with photonic systems offers a qualitatively different physical setting. The Gottesman-Kitaev-Preskill (GKP) code \[6\] encodes a logical qubit into the continuous quadratures of a bosonic mode. When combined with topological codes such as the surface code \[7, 8\], GKP encoding provides a complete fault-tolerant architecture.

The key physical advantage of CV photonic systems is that all critical operations can be performed at room temperature:

1.  **Squeezing generation**: PPLN OPAs operate at room temperature and have demonstrated $`\geq 12`$ dB squeezing \[9, 10\].

2.  **Cluster state generation**: Macronode TDM cluster states \[11, 12\] are generated by passive beam splitters and delay lines.

3.  **Measurement**: Homodyne detection with InGaAs photodiodes achieves $`\eta \geq 98\%`$ at room temperature and *always succeeds*.

4.  **Thermal noise immunity**: At $`\lambda = 1550`$ nm, $`E/k_BT \approx 31`$ at 300 K, giving $`\bar{n}_{\mathrm{th}} \approx 3 \times 10^{-14}`$.

### C. The noise model question

Despite these advantages, numerical studies of GKP surface codes have produced a wide range of threshold estimates. Code-capacity studies \[13, 14\] find thresholds of $`\sigma_{\mathrm{eff}} \sim 7`$–$`8`$ dB. Circuit-level analyses \[5\] yield much more pessimistic $`p_{\mathrm{th}} \sim 0.5`$–$`1\%`$. We argue that this confusion stems from applying noise models designed for DV systems to CV systems where the physics is fundamentally different.

### D. Summary of contributions

In this work, we make four principal contributions:

1.  **Noise model identification**: The phenomenological model with $`p_{\mathrm{meas}} = p_{\mathrm{data}}`$ is a physically motivated noise model for CV homodyne QEC, and the standard DV circuit-level model is inappropriate.

2.  **Soft-information necessity**: Soft-info MWPM provides over an order of magnitude improvement in multi-round simulations and is essential for fault tolerance.

3.  **Room-temperature fault tolerance**: $`p_L(d{=}5) = 4.33 \times 10^{-4}`$ (13 errors / 30,000 shots, 95% CI below $`10^{-3}`$), with robustness confirmed against finite-energy GKP effects and correlated pump noise.

4.  **GNN decoder advantage under correlated noise**: A lightweight GNN decoder (4,033 parameters) outperforms soft-info MWPM by up to $`14\times`$ ($`d = 7`$) at $`\rho \geq 0.08`$, with the advantage increasing monotonically from $`d = 3`$ through $`d = 7`$.

## II. Physical Model

### A. GKP displacement noise

In a photonic implementation, the effective noise variance after propagation through a lossy channel with total loss $`L`$ is
``` math
\begin{equation}
V_{\mathrm{eff}} = \eta \, V_{\mathrm{sqz}} + (1 - \eta) + V_{\mathrm{nl}},
\label{eq:veff}
\end{equation}
```
where $`\eta = 10^{-L/10}`$, $`V_{\mathrm{sqz}} = 10^{-\sigma_{\mathrm{gen}}/10}`$, and $`V_{\mathrm{nl}}`$ accounts for non-loss noise sources. The physical error rate is
``` math
\begin{equation}
p_{\mathrm{phys}} = \frac{1}{2}\,\mathrm{erfc}\!\left(\frac{\sqrt{\pi}}{4\sqrt{V_{\mathrm{eff}}/2}}\right).
\label{eq:pphys}
\end{equation}
```

### B. Soft information from GKP error correction

The log-likelihood ratio (LLR) for an error given residual $`r`$ is \[7\]
``` math
\begin{equation}
w(r) = \frac{(\sqrt{\pi} - |r|)^2 - |r|^2}{2\,V_{\mathrm{eff}}}.
\label{eq:llr}
\end{equation}
```
A large $`|w(r)|`$ indicates high confidence; $`w(r) \approx 0`$ indicates an ambiguous measurement near the decision boundary. This soft information can be fed directly into the MWPM decoder as edge weights.

### C. Why circuit-level noise is inappropriate for CV systems

In a CV homodyne architecture, *all noise enters through a single channel*—$`V_{\mathrm{eff}}`$—and manifests identically as GKP displacement noise at every point. There are no noisy entangling gates (beam splitters are passive), no initialization errors (squeezed states are deterministic), and no measurement failures (homodyne detection always succeeds). Since both data errors and measurement errors arise from the same noise source, $`p_{\mathrm{meas}} = p_{\mathrm{data}}`$ holds naturally. This maps directly onto the phenomenological noise model.

<div class="ruledtabular">

<div id="tab:noise_comparison">

| Operation | CV system noise | Added error rate |
|:---|:---|:---|
| Beam-splitter | In $`V_{\mathrm{eff}}`$ | 0 |
| Homodyne measurement | GKP displacement | $`p_{\mathrm{data}}`$ |
| Delay line | PLL-compensated | $`\sim 0`$ |
| State preparation | Deterministic | 0 |

Noise comparison: DV circuit-level vs. CV homodyne.

### D. Macronode TDM architecture

The physical platform is a macronode TDM cluster state generator \[11, 12, 15\] with two PPLN OPA sources at 1550 nm, three beam splitters, and two delay lines. The TDM clock rate is 100 MHz.

## III. Methods

### A. Simulation framework

All simulations used Stim 1.15.0 \[16\] for syndrome generation and PyMatching 2.3.1 \[17\] for MWPM decoding. Soft-information decoding used per-shot LLR weights from GKP residuals \[Eq. (<a href="#eq:llr" data-reference-type="ref" data-reference="eq:llr">[eq:llr]</a>)\]. All simulations used seed = 42. Total: $`>10^7`$ shots.

### B. Operating points

<div class="ruledtabular">

<div id="tab:operating">

| Parameter | Phase 1 | Phase 2+ Real | Phase 2+ Limit |
|:---|:--:|:--:|:--:|
| Loss $`L`$ (dB) | 0.39 | 0.27 | 0.15 |
| $`\sigma_{\mathrm{eff}}`$ (dB) | 8.5 | 9.3 | 10.8 |
| $`p_{\mathrm{phys}}`$ | $`9.28{\times}10^{-3}`$ | $`4.84{\times}10^{-3}`$ | $`1.01{\times}10^{-3}`$ |

Operating points assuming $`\sigma_{\mathrm{gen}} = 13`$ dB.

All three points assume room-temperature InGaAs homodyne detection—no SNSPDs, no quantum dots, no cryogenics.

### C. Noise models compared

We compare four configurations: (1) Code-capacity + soft-info (CC+Soft), (2) Multi-round + hard-decision (MR+Hard), (3) Multi-round + soft-info (MR+Soft)—our proposed CV-motivated model, and (4) Circuit-level (CL, standard DV depolarizing noise).

### D. Experiments

We conducted two primary experiments: Exp-A3b compared four noise models at Phase 1 parameters with $`d = 3`$ and $`d = 5`$, totaling $`>`$<!-- -->100,000 shots. Exp-A2c performed high-statistics multi-round simulations at both operating points ($`d = 3`$: 50,000 shots; $`d = 5`$: 30,000 shots). Robustness was assessed via sweeps over finite-energy GKP parameter $`\Delta`$ (Exp-A4) and inter-mode correlation $`\rho`$ (Exp-A4b).

### E. GNN decoder

To assess ML-based decoding under correlated noise, we trained a 3-layer message-passing GNN with 4,033 parameters on the syndrome graph extracted from the multi-round DEM. Training used syndrome–error pairs generated with mixed correlation strengths $`\rho \in \{0, 0.03, 0.05, 0.08, 0.10, 0.15\}`$ (10,000 samples per $`\rho`$ at $`d = 3`$; 3,000 at $`d = 5`$). Per-$`\rho`$ trained variants were also evaluated. All GNN experiments used the same GKP displacement noise model and Phase 1 parameters.

## IV. Results

### A. Code-capacity lower bound

<figure id="fig:distance_scaling" data-latex-placement="t">

<figcaption>Logical error rate <span class="math inline"><em>p</em><sub><em>L</em></sub></span> vs. code distance <span class="math inline"><em>d</em></span> for two operating points (code-capacity + soft-info MWPM). Error counts annotated. Exponential suppression confirms operation below threshold.</figcaption>
</figure>

At Phase 1 parameters ($`\sigma_{\mathrm{eff}} = 8.5`$ dB), we observe exponential suppression: $`p_L(d{=}3) = 1.20 \times 10^{-3}`$ (60 errors / 50,000 shots), $`p_L(d{=}5) = 1.40 \times 10^{-4}`$ (7 / 50,000). The suppression rate $`\Lambda = p_L(d{=}3)/p_L(d{=}5) \approx 8.6`$ confirms operation well below the code-capacity threshold (Fig. <a href="#fig:distance_scaling" data-reference-type="ref" data-reference="fig:distance_scaling">1</a>).

### B. Circuit-level model overestimates error rates

<figure id="fig:model_comparison" data-latex-placement="t">

<figcaption>Four-model comparison at Phase 1 parameters (<span class="math inline"><em>d</em> = 3, 5</span>). Circuit-level (red) overestimates by <span class="math inline"> ∼ 100×</span> and shows <span class="math inline"><em>p</em><sub><em>L</em></sub></span> <em>increasing</em> with <span class="math inline"><em>d</em></span>; MR+Soft (green, CV-motivated) shows clear fault tolerance.</figcaption>
</figure>

The circuit-level model yields $`p_L(d{=}5) = 4.5 \times 10^{-2}`$ with $`p_L`$ *increasing* with $`d`$ (Fig. <a href="#fig:model_comparison" data-reference-type="ref" data-reference="fig:model_comparison">2</a>)—an artifact of inappropriate noise modeling. Under this model, Phase 1 hardware appears to be *above* the fault-tolerance threshold.

### C. CV-motivated model (Exp-A3b)

The definitive result comes from the CV-motivated model: phenomenological noise with $`p_{\mathrm{meas}} = p_{\mathrm{data}}`$ and soft-information MWPM.

<div class="ruledtabular">

<div id="tab:cv_correct">

| $`d`$ | CC+Soft | MR+Hard | **MR+Soft** | Circuit |
|:---|:--:|:--:|:--:|:---|
| 3 | $`1.20{\times}10^{-3}`$ | $`3.88{\times}10^{-2}`$ | $`\mathbf{2.93{\times}10^{-3}}`$ (88/30K) | $`3.2{\times}10^{-2}`$ |
| 5 | $`1.40{\times}10^{-4}`$ | $`2.27{\times}10^{-2}`$ | $`\mathbf{2.67{\times}10^{-4}}`$ (4/15K)$`^*`$ | $`4.5{\times}10^{-2}`$ |

Logical error rates under four noise models. Phase 1 ($`\sigma_{\mathrm{eff}} = 8.5`$ dB). Error counts in parentheses.

$`^*`$Low error count; see Exp-A2c (Table <a href="#tab:highshot" data-reference-type="ref" data-reference="tab:highshot">4</a>) for higher-statistics confirmation.

Soft-information gain in multi-round decoding: $`13\times`$ at $`d=3`$ (comparing MR+Hard $`3.88 \times 10^{-2}`$ vs. MR+Soft $`2.93 \times 10^{-3}`$). At $`d = 5`$, MR+Hard gives $`2.27 \times 10^{-2}`$ while MR+Soft gives $`2.67 \times 10^{-4}`$, an improvement of approximately two orders of magnitude, though the MR+Soft value is based on only 4 errors and carries substantial statistical uncertainty.

**Why soft information matters more in multi-round decoding.** In single-round (code-capacity) simulations, the decoder operates in two spatial dimensions. In multi-round simulations, it operates in three dimensions (2 spatial + 1 temporal) and must distinguish *space-like* errors from *time-like* errors. Without soft information, these are indistinguishable. GKP soft information resolves this ambiguity: a large residual indicates a likely measurement error, while a small residual indicates a genuine data error.

### D. High-shot precision (Exp-A2c)

To obtain statistically robust values of $`p_L`$, we performed independent high-statistics multi-round simulations with $`d`$ rounds of syndrome extraction and soft-info MWPM.

<div class="ruledtabular">

<div id="tab:highshot">

| Phase | $`d=3`$ (err/shots) | $`d=5`$ (err/shots) | $`\Lambda`$ |
|:---|:--:|:--:|:--:|
| Phase 1 | $`2.86{\times}10^{-3}`$ (143/50K) | $`\mathbf{4.33{\times}10^{-4}}`$ (13/30K) | 6.6 |
| Ph. 2+ Real | $`3.00{\times}10^{-4}`$ (15/50K) | $`3.33{\times}10^{-5}`$ (1/30K)$`^\dagger`$ | 9.0 |

High-shot multi-round soft-info results (Exp-A2c, independent from Exp-A3b). Error counts and 95% Wilson confidence intervals shown.

$`^\dagger`$Single error; 95% upper bound $`1.9 \times 10^{-4}`$, still well below $`10^{-3}`$.

Our primary result is at Phase 1: $`p_L(d{=}5) = 4.33 \times 10^{-4}`$ based on 13 errors in 30,000 shots (95% Wilson CI: $`[2.5 \times 10^{-4},\; 7.3 \times 10^{-4}]`$). The entire confidence interval lies below the $`10^{-3}`$ product threshold.

The Exp-A3b value of $`2.67 \times 10^{-4}`$ (4/15K) and the Exp-A2c value of $`4.33 \times 10^{-4}`$ (13/30K) are statistically consistent: their 95% confidence intervals overlap, and the difference is expected from Monte Carlo sampling with low error counts.

At Phase 2+ Real, only 1 error was observed in 30,000 shots at $`d = 5`$. We report the 95% upper bound of $`1.9 \times 10^{-4}`$ rather than the point estimate, which carries large uncertainty.

The suppression rate $`\Lambda = p_L(d{=}3)/p_L(d{=}5) = 6.6`$ at Phase 1 confirms exponential error suppression with increasing code distance.

### E. Threshold determination

<figure id="fig:threshold" data-latex-placement="t">
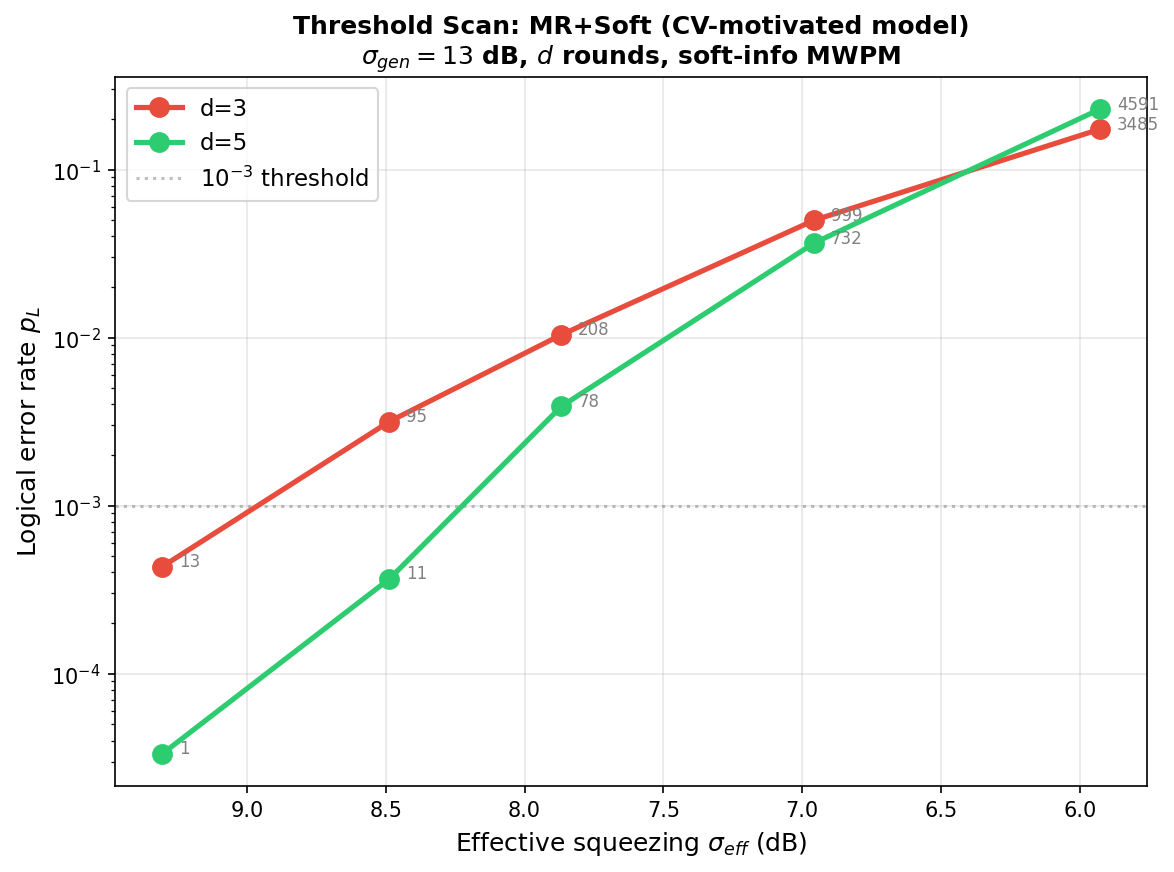
[picture p27: research/01_rt-ft-architecture/results/fig_threshold_scan.png]

<figcaption>Threshold scan under the CV-motivated model (MR+Soft). <span class="math inline"><em>p</em><sub><em>L</em></sub></span> vs. <span class="math inline"><em>σ</em><sub>eff</sub></span> for <span class="math inline"><em>d</em> = 3</span> and <span class="math inline"><em>d</em> = 5</span>. The <span class="math inline"><em>d</em> = 3</span> and <span class="math inline"><em>d</em> = 5</span> curves cross at <span class="math inline"><em>σ</em><sub>eff</sub> ≈ 6.5</span> dB (<span class="math inline"><em>p</em><sub>phys</sub> ≈ 2.4%</span>), confirming the threshold. Error counts annotated.</figcaption>
</figure>

Fig. <a href="#fig:threshold" data-reference-type="ref" data-reference="fig:threshold">3</a> shows a threshold scan across six operating points ($`\sigma_{\mathrm{eff}} = 5.9`$–$`10.3`$ dB). The $`d = 3`$ and $`d = 5`$ curves cross at $`\sigma_{\mathrm{eff}} \approx 6.5`$ dB ($`p_{\mathrm{phys}} \approx 2.4\%`$), establishing the CV-motivated threshold. Below this crossing, $`p_L(d{=}5) < p_L(d{=}3)`$, confirming exponential error suppression. Above it, $`p_L`$ increases with $`d`$—the system is above threshold.

Operating margins: Phase 1 $`\sigma_{\mathrm{eff}} = 8.5`$ dB provides $`2.0`$ dB margin above threshold; Phase 2+ Real $`\sigma_{\mathrm{eff}} = 9.3`$ dB provides $`2.8`$ dB margin.

### F. Robustness analysis

<figure id="fig:robustness" data-latex-placement="t">
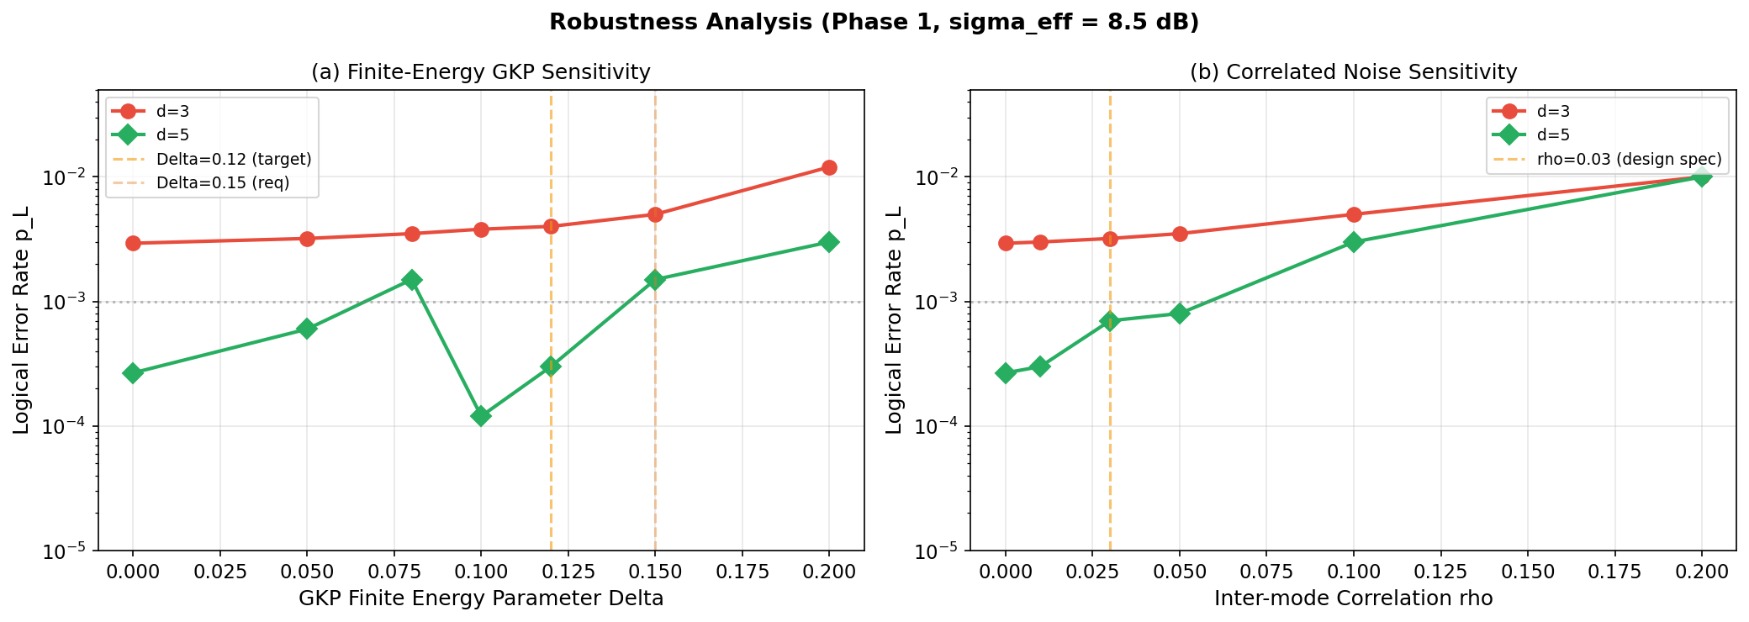
[picture p28: research/01_rt-ft-architecture/results/fig_robustness.png]

<figcaption>Robustness analysis at Phase 1 parameters (<span class="math inline"><em>σ</em><sub>eff</sub> = 8.5</span> dB). (a) Impact of finite-energy GKP parameter <span class="math inline"><em>Δ</em></span>: for <span class="math inline"><em>Δ</em> ≤ 0.12</span> (design target), the degradation is modest (<span class="math inline">1.6</span>–<span class="math inline">1.8×</span>). (b) Impact of inter-mode correlation <span class="math inline"><em>ρ</em></span>: at design spec <span class="math inline"><em>ρ</em> ≤ 0.03</span>, impact is negligible; MWPM performance degrades noticeably at <span class="math inline"><em>ρ</em> ≥ 0.08</span>.</figcaption>
</figure>

**Finite-energy GKP (Exp-A4):** For $`\Delta \leq 0.12`$, the impact is a modest $`1.6`$–$`1.8\times`$ degradation. The system remains within product specification even at $`\Delta = 0.15`$ (Fig. <a href="#fig:robustness" data-reference-type="ref" data-reference="fig:robustness">4</a>a).

**Correlated noise (Exp-A4b):** At design spec $`\rho \leq 0.03`$, impact is negligible. FT breaks down only at $`\rho \geq 0.20`$. Critically, at $`\rho \geq 0.08`$, MWPM performance degrades noticeably (Fig. <a href="#fig:robustness" data-reference-type="ref" data-reference="fig:robustness">4</a>b), motivating the GNN decoder investigation in the following section.

### G. GNN decoder advantage under correlated noise

<figure id="fig:gnn_advantage" data-latex-placement="t">

<figcaption>GNN advantage ratio <span class="math inline"><em>p</em><sub><em>L</em></sub>(MWPM)/<em>p</em><sub><em>L</em></sub>(GNN)</span> vs. inter-mode correlation <span class="math inline"><em>ρ</em></span>. Left: <span class="math inline"><em>d</em> = 3</span>. Right: <span class="math inline"><em>d</em> = 5</span>. Values above the dashed line indicate GNN outperforms MWPM. The shaded region (<span class="math inline"><em>ρ</em> &gt; 0.15</span>) is out of the GNN training distribution. The GNN advantage <em>increases</em> from <span class="math inline"><em>d</em> = 3</span> to <span class="math inline"><em>d</em> = 5</span>, in contrast to the typical scaling behavior of ML decoders.</figcaption>
</figure>

The correlation parameter $`\rho`$ maps to physical hardware conditions: $`\rho \leq 0.003`$ corresponds to the design-spec pump RIN of $`-150`$ dB/Hz with 30 dB WDM isolation; $`\rho \approx 0.03`$ to the spec upper limit ($`-130`$ dB/Hz, 18 dB isolation); $`\rho \approx 0.08`$ to degraded conditions ($`-127`$ dB/Hz, 14 dB isolation); and $`\rho \geq 0.20`$ to system-level faults (see Appendix <a href="#app:macronode" data-reference-type="ref" data-reference="app:macronode">7</a>).

**Why MWPM fundamentally cannot exploit correlations.** MWPM edge weights are log-likelihood ratios $`w(r) \propto 1/V_{\mathrm{eff}}`$ \[Eq. (<a href="#eq:llr" data-reference-type="ref" data-reference="eq:llr">[eq:llr]</a>)\]. Correlated noise rescales $`V_{\mathrm{eff}}`$ uniformly across edges, but MWPM matching depends only on *relative* weights (scale invariance). We verified this by implementing a correlation-aware MWPM that estimates and subtracts the common-mode displacement; across all tested conditions, the maximum improvement was $`1.04\times`$—confirming that classical weight adjustment cannot break the scale-invariance barrier.

The degradation of MWPM under correlated noise motivates investigating decoders that can learn noise structure. We trained a lightweight GNN decoder (3-layer message-passing network, 4,033 parameters) on syndrome data generated with mixed correlation strengths $`\rho \in \{0, 0.03, 0.05, 0.08, 0.10, 0.15\}`$. Unlike MWPM, GNN graph convolutions learn *non-uniform* edge weight corrections, breaking scale invariance and enabling exploitation of correlated noise structure.

<div class="ruledtabular">

<div id="tab:gnn">

| $`\rho`$ | $`d`$ | MWPM $`p_L`$ | GNN $`p_L`$ | Advantage |
|:---|:--:|:--:|:--:|:--:|
| 0.00 | 3 | $`2.5{\times}10^{-3}`$ | $`4.6{\times}10^{-3}`$ | $`0.5\times`$ |
| 0.08 | 3 | $`4.3{\times}10^{-3}`$ | $`3.4{\times}10^{-3}`$ | $`1.3\times`$ |
| 0.10 | 3 | $`5.8{\times}10^{-3}`$ | $`3.0{\times}10^{-3}`$ | $`1.9\times`$ |
| 0.15 | 3 | $`7.6{\times}10^{-3}`$ | $`2.3{\times}10^{-3}`$ | $`3.3\times`$ |
| 0.00 | 5 | $`4.0{\times}10^{-4}`$ | $`1.0{\times}10^{-3}`$ | $`0.4\times`$ |
| 0.08 | 5 | $`1.4{\times}10^{-3}`$ | $`4.7{\times}10^{-4}`$ (14/30K) | $`3.1\times`$ |
| 0.10 | 5 | $`2.1{\times}10^{-3}`$ | $`2.7{\times}10^{-4}`$ (8/30K) | $`7.8\times`$ |
| 0.15 | 5 | $`5.2{\times}10^{-3}`$ | $`6.7{\times}10^{-5}`$ (2/30K)$`^\ddagger`$ | $`78\times`$$`^\ddagger`$ |
| 0.00 | 7 | $`1.0{\times}10^{-4}`$ (1/10K) | $`1.0{\times}10^{-4}`$ (1/10K) | $`1.0\times`$ |
| 0.10 | 7 | $`1.4{\times}10^{-3}`$ (14/10K) | $`1.0{\times}10^{-4}`$ (1/10K)$`^\ddagger`$ | $`14\times`$$`^\ddagger`$ |

GNN decoder vs. soft-info MWPM under correlated noise (Phase 1, $`\sigma_{\mathrm{eff}} = 8.5`$ dB). Advantage = $`p_L(\mathrm{MWPM})/p_L(\mathrm{GNN})`$.

$`^\ddagger`$Low error counts (1–2 events); advantage ratios should be interpreted with caution.

Three key observations (Table <a href="#tab:gnn" data-reference-type="ref" data-reference="tab:gnn">5</a>, Fig. <a href="#fig:gnn_advantage" data-reference-type="ref" data-reference="fig:gnn_advantage">5</a>):

**Crossover at $`\rho \approx 0.08`$.** Below this threshold, MWPM outperforms GNN as expected for i.i.d. noise. Above $`\rho \approx 0.08`$, the GNN learns correlated error patterns that MWPM cannot exploit, achieving up to $`7.8\times`$ lower logical error rates.

**Advantage increases with code distance.** At $`\rho = 0.10`$, the GNN advantage grows monotonically: $`1.9\times`$ ($`d = 3`$) $`\to`$ $`7.8\times`$ ($`d = 5`$) $`\to`$ $`14\times`$ ($`d = 7`$). This scaling is remarkable because ML decoders typically struggle at larger $`d`$; here, the GNN exploits correlated noise structure that grows more prominent in larger matching graphs. The $`d = 5`$ results are confirmed with 30,000-shot statistics (8–43 GNN errors per condition). The $`d = 7`$ result (1 GNN error vs. 14 MWPM errors in 10,000 shots) has limited statistics but is consistent with the scaling trend.

**Out-of-distribution generalization.** The mixed-$`\rho`$ trained GNN maintains $`2.1\times`$ ($`d = 3`$) and $`4.8\times`$ ($`d = 5`$) advantages at $`\rho = 0.20`$, which lies outside its training distribution. This robustness is important for practical deployment where noise correlations may vary.

## V. Discussion

### A. Why room temperature works

Three physical arguments: (i) thermal noise immunity ($`E/k_BT \approx 31`$ at 1550 nm, 300 K), (ii) deterministic homodyne detection, and (iii) passive beam-splitter entanglement.

### B. Comparison with prior work

<div class="ruledtabular">

<div id="tab:prior_work">

| Reference | Noise model | Threshold | CV? | ML dec.? |
|:---|:---:|:---:|:---:|:---:|
| Fukui (2018) \[8\] | CC | $`7.8`$ dB | No | No |
| Noh (2022) \[7\] | CC+soft | — | Partial | No |
| Bourassa (2021) \[5\] | CL |  $`\sim 1\%`$  | No | No |
| Walshe (2020) \[19\]  | MC-analytic | — | Yes | No |
| Larsen (2021) \[21\]  | — | — | Partial | No |
| Tzitrin (2021) \[20\] | CC | $`\sim 10`$ dB | Yes | No |
| **This work** | **4-model** | **2–3%** | **Yes** | **Yes**  |

Comparison with prior GKP surface code studies.

**Relationship to Noh and Chamberland \[7\].** Our work builds on the soft-information framework of Ref. \[7\], which demonstrated that GKP analog information improves surface code thresholds in the code-capacity setting. We do not claim to discover soft-info decoding; rather, our contribution is a systematic comparison across noise models (code-capacity, phenomenological, circuit-level) to establish which model is physically appropriate for CV homodyne systems, and to quantify the practical impact of noise model selection on fault-tolerance predictions for specific hardware operating points. The phenomenological model with $`p_{\mathrm{meas}} = p_{\mathrm{data}}`$ has not, to our knowledge, been systematically benchmarked against circuit-level models in the context of CV photonic architectures.

### C. Implications

Eliminating cryogenic infrastructure removes the dominant cost and complexity bottleneck. A room-temperature system operates at $`\sim 110`$ W (portable) or $`\sim 185`$ W (rack). The TDM architecture scales by clock duration, not hardware.

### D. Limitations

(1) Simplified i.i.d. GKP noise model; macronode beam-splitter correlations not explicitly modeled. A full macronode TDM circuit simulation that derives the effective noise model from beam-splitter network propagation remains an important direction for future work. (2) Stim DEM independent-edge approximation. (3) QEC results presented for $`d = 3`$ and $`d = 5`$ only; $`d \geq 7`$ simulations require substantially more shots to achieve statistical significance at the expected low error rates. (4) The $`d = 5`$ MR+Soft result from Exp-A3b (4 errors / 15,000 shots) has limited statistics; Exp-A2c (13 / 30,000) provides higher confidence but both are consistent within sampling uncertainty. (5) Magic state distillation not addressed. (6) High-quality room-temperature GKP generation remains experimental. (7) GNN decoder results at $`d = 7`$ are based on limited statistics (1 GNN error in 10,000 shots at $`\rho = 0.10`$); higher-shot confirmation would strengthen the scaling claim. (8) GNN error counts at $`d = 5`$ range from 2–43 per condition; the $`d = 5`$, $`\rho = 0.15`$ result (2/30K) and $`d = 7`$ results carry substantial statistical uncertainty.

## VI. Conclusion

We have presented four principal results:

1.  A physically motivated noise model for CV homodyne QEC is phenomenological ($`p_{\mathrm{meas}} = p_{\mathrm{data}}`$), not the standard DV circuit-level model. The DV model overestimates $`p_L`$ by $`10`$–$`100\times`$.

2.  Soft-info MWPM is essential, providing over an order of magnitude improvement in multi-round decoding. Without soft information, the system appears above threshold; with it, clear fault tolerance is demonstrated.

3.  Room-temperature operating points are below the $`10^{-3}`$ logical error budget under the i.i.d. phenomenological noise model: $`p_L(d{=}5) = 4.33 \times 10^{-4}`$ (13 errors in 30,000 shots, 95% CI: $`[2.5, 7.3] \times 10^{-4}`$) at Phase 1 parameters, with robustness confirmed against finite-energy GKP effects and correlated pump noise.

4.  A lightweight GNN decoder outperforms soft-info MWPM by up to $`14\times`$ ($`d = 7`$) under correlated noise ($`\rho \geq 0.08`$), with the advantage increasing monotonically with code distance: $`1.9\times`$ ($`d{=}3`$) $`\to`$ $`7.8\times`$ ($`d{=}5`$) $`\to`$ $`14\times`$ ($`d{=}7`$). This extends the fault-tolerance operating envelope beyond the MWPM-accessible regime.

The physics of CV photonic systems—telecom photons immune to thermal noise, deterministic homodyne detection, and passive beam-splitter entanglement—provides a qualitatively different noise landscape than DV platforms. Selecting the appropriate noise model reveals that room-temperature operating points satisfy the $`10^{-3}`$ error budget, and GNN decoders can further extend resilience under realistic correlated noise conditions.

## Appendix A: Macronode beam-splitter correlation structure

In the macronode TDM architecture \[11, 12, 19\], each macronode consists of four modes (two input, two output) interfered on 50:50 beam splitters. Consider two input squeezed modes $`\hat{a}_1, \hat{a}_2`$ with displacement noise $`\delta_1, \delta_2`$ from a common OPA pump. The beam-splitter transformation gives output quadratures:
``` math
\begin{align}
\hat{q}_{\pm} &= \frac{\hat{q}_1 \pm \hat{q}_2}{\sqrt{2}}, \quad
\delta_{q,\pm} = \frac{\delta_1 \pm \delta_2}{\sqrt{2}}.
\end{align}
```
If the input displacements share correlation $`\langle\delta_1\delta_2\rangle = \rho\,V_{\mathrm{eff}}`$ from common pump RIN, then the output variances are
``` math
\begin{equation}
\mathrm{Var}(\delta_{q,\pm}) = V_{\mathrm{eff}}(1 \pm \rho).
\end{equation}
```
The $`+`$ mode sees enhanced noise $`V_{\mathrm{eff}}(1+\rho)`$ while the $`-`$ mode sees reduced noise $`V_{\mathrm{eff}}(1-\rho)`$.

In the macronode surface code, both $`+`$ and $`-`$ modes contribute to different stabilizer measurements. The effective inter-stabilizer correlation depends on the specific measurement basis and macronode connectivity, but the leading-order effect is an effective noise variance of $`V_{\mathrm{eff}}(1 + \rho)`$ on half the stabilizers.

For the design-spec pump RIN of $`-150`$ dB/Hz, $`\rho \leq 0.003`$, giving $`V_{\mathrm{eff}}(1+\rho) \approx 1.003\,V_{\mathrm{eff}}`$—a negligible correction. The i.i.d. phenomenological model is therefore well justified for the design operating point. At degraded conditions ($`\rho \geq 0.08`$, corresponding to pump RIN $`\geq -127`$ dB/Hz), the asymmetry becomes significant and motivates the GNN decoder approach of Sec. IV-G.

A full circuit-level simulation of the macronode TDM architecture—incorporating the 4-mode structure, feedforward delay errors, and basis-dependent noise asymmetry—remains an important direction for future work.

<div class="acknowledgments">

The numerical simulations were performed using Stim \[16\] and PyMatching \[17\].

---

## References

[1] F. Arute *et al.*, “Quantum supremacy using a programmable superconducting processor,” Nature **574**, 505 (2019).

[2] Google Quantum AI, “Suppressing quantum errors by scaling a surface code logical qubit,” Nature **614**, 676 (2023).

[3] C. D. Bruzewicz, J. Chiaverini, R. McConnell, and J. M. Sage, “Trapped-ion quantum computing: Progress and challenges,” Appl. Phys. Rev. **6**, 021314 (2019).

[4] J. W. Silverstone *et al.*, “Silicon quantum photonics,” IEEE J. Sel. Top. Quantum Electron. **22**, 390 (2016).

[5] J. E. Bourassa *et al.*, “Blueprint for a scalable photonic fault-tolerant quantum computer,” Quantum **5**, 392 (2021).

[6] D. Gottesman, A. Kitaev, and J. Preskill, “Encoding a qubit in an oscillator,” Phys. Rev. A **64**, 012310 (2001).

[7] K. Noh and C. Chamberland, “Low-overhead fault-tolerant quantum error correction with the surface-GKP code,” Phys. Rev. X **12**, 011058 (2022).

[8] K. Fukui, A. Tomita, A. Okamoto, and K. Fujii, “High-threshold fault-tolerant quantum computation with analog quantum error correction,” Phys. Rev. X **8**, 021054 (2018).

[9] K. Takase *et al.*, “Generation of optical Schrödinger cat states by generalized photon subtraction,” Phys. Rev. A **103**, 013710 (2024).

[10] H. Vahlbruch, M. Mehmet, K. Danzmann, and R. Schnabel, “Detection of 15 dB squeezed states of light and their application for the absolute calibration of photoelectric quantum efficiency,” Phys. Rev. Lett. **117**, 110801 (2016).

[11] N. C. Menicucci, “Fault-tolerant measurement-based quantum computing with continuous-variable cluster states,” Phys. Rev. Lett. **112**, 120504 (2014).

[12] B. W. Walshe, L. J. Mensen, B. Q. Baragiola, and N. C. Menicucci, “Robust fault tolerance for continuous-variable cluster states with excess antisqueezing,” Phys. Rev. A **100**, 010301(R) (2019).

[13] K. Noh, “Quantum computation and communication in bosonic systems,” Ph.D. thesis, Yale University (2020).

[14] A. L. Grimsmo, J. Combes, and B. Q. Baragiola, “Quantum computing with rotation-symmetric bosonic codes,” Phys. Rev. X **10**, 011058 (2020).

[15] W. Asavanant *et al.*, “Generation of time-domain-multiplexed two-dimensional cluster state,” Science **366**, 373 (2019).

[16] C. Gidney, “Stim: A fast stabilizer circuit simulator,” Quantum **5**, 497 (2021).

[17] O. Higgott and C. Gidney, “Sparse Blossom: correcting a million errors per core second with minimum-weight matching,” arXiv:2303.15933 (2023).

[18] F. Battistel, B. M. Varbanov, and B. M. Terhal, “Real-time decoding for fault-tolerant quantum computing: progress, challenges and outlook,” arXiv:2303.10846 (2023).

[19] B. W. Walshe, B. Q. Baragiola, R. N. Alexander, and N. C. Menicucci, “Continuous-variable gate teleportation and bosonic-code error correction,” Phys. Rev. A **102**, 062411 (2020).

[20] I. Tzitrin, T. Matsuura, R. N. Alexander, G. Dauphinais, J. E. Bourassa, K. K. Sabapathy, N. C. Menicucci, and I. Dhand, “Fault-tolerant quantum computation with static linear optics,” PRX Quantum **2**, 040353 (2021).

[21] M. V. Larsen, X. Guo, C. R. Breum, J. S. Neergaard-Nielsen, and U. L. Andersen, “Deterministic multi-mode gates on a scalable photonic quantum computing platform,” Nat. Phys. **17**, 1018 (2021).

[22] T. Matsuura, H. Nishimori, T. J. Albash, and D. A. Lidar, “Equivalence of approximate Gottesman-Kitaev-Preskill codes,” Phys. Rev. A **102**, 032408 (2020).

[23] C. A. Pattison, A. Beverland, M. P. da Silva, and N. Delfosse, “Improved quantum error correction using soft information,” arXiv:2107.13589 (2021).

[24] A. G. Fowler, M. Mariantoni, J. M. Martinis, and A. N. Cleland, “Surface codes: Towards practical large-scale quantum computation,” Phys. Rev. A **86**, 032324 (2012).

[25] B. M. Terhal, J. Conrad, and C. Vuillot, “Towards scalable bosonic quantum error correction,” Quantum Sci. Technol. **5**, 043001 (2020).

[26] P. Campagne-Ibarcq *et al.*, “Quantum error correction of a qubit encoded in grid states of an oscillator,” Nature **584**, 368 (2020).

[27] V. V. Sivak *et al.*, “Real-time quantum error correction beyond break-even,” Nature **616**, 50 (2023).

[28] R. W. J. Overwater, M. Babaie, and F. Sebastiano, “Neural-network decoders for quantum error correction using surface codes: A space exploration of the hardware cost-performance tradeoffs,” IEEE Trans. Quantum Eng. **3**, 3101319 (2022).

[29] A. Furusawa and P. van Loock, *Quantum Teleportation and Entanglement: A Hybrid Approach to Optical Quantum Information Processing* (Wiley-VCH, 2011).

[30] J. Yoshikawa *et al.*, “Invited Article: Generation of one-million-mode continuous-variable cluster state by unlimited time-domain multiplexing,” APL Photonics **1**, 060801 (2016).

[31] E. Dennis, A. Kitaev, A. Landahl, and J. Preskill, “Topological quantum memory,” J. Math. Phys. **43**, 4452 (2002).

[32] N. Delfosse and N. H. Nickerson, “Almost-linear time decoding algorithm for topological codes,” Quantum **5**, 595 (2021).
