TomohiroTani28/Taros/archive/09_bom-cost/01_bom.md

> **⚠ DEPRECATED**: 本文書はDV-FBQC方式に基づいており、CV方式移行に伴い数値（コスト・確率・スケジュール）は現行計画と大幅に異なります。CV方式の最新情報: `analysis/bom.md`, `analysis/risk.md`, `analysis/development-cost-summary.md`

# セクション11: 部品リスト（BoM）と概算コスト

## 11.1 詳細BoM表（Phase 0: 研究実証機）

> **v4.0注記**: 本節のBoMはPhase 0（研究実証機）のものである。Phase 1/2のBoMは11.1A節を参照。

### 11.1.1 光源系

| カテゴリ | 品目 | 数量 | 単価(万円) | 小計(万円) | 備考 |
|---|---|---|---|---|---|
| 光源 | 925nm GaAs QDモジュール (Quandela eDelight系) | 12 | 2,500 | 30,000 | g²(0)<0.01, HOM>0.97, 4K動作 |
| 光源 | QD用小型クライオスタット (4K GM冷凍機) | 2 | 3,000 | 6,000 | SHI RDK-101E相当。12QD / 2クライオ |
| 光源 | QD温調コントローラ | 2 | 500 | 1,000 | 12ch温度制御 |
| 光源 | パルス励起レーザ (800nm, 1GHz) | 2 | 1,500 | 3,000 | QD励起用、冗長1台 |
| QFC | LNOI QFCモジュール (925→1550nm) | 12 | 1,200 | 14,400 | PPLN導波路、内部効率>80% |
| QFC | QFCポンプレーザ (2100nm CW) | 6 | 800 | 4,800 | 2QFCで1ポンプ共有 |
| QFC | ノイズフィルタ (バンドパス+ノッチ) | 12 | 150 | 1,800 | ラマン散乱除去 |
| | **光源系 小計** | | | **61,000** | |

### 11.1.2 フォトニック回路系

| カテゴリ | 品目 | 数量 | 単価(万円) | 小計(万円) | 備考 |
|---|---|---|---|---|---|
| 干渉回路 | Si₃N₄ フォトニックチップ (SHYPS用) | 48 | 300 | 14,400 | MZI干渉計、fusion測定回路。Ligentec/IMEC委託 |
| 干渉回路 | ファイバアレイ接続ユニット (V溝アレイ) | 96 | 50 | 4,800 | Si₃N₄チップI/O、8chアレイ |
| EO変調 | LNOI EOチップ | 96 | 200 | 19,200 | Vπ < 1V、帯域 > 10GHz、HyperLight系 |
| EO変調 | RF駆動回路 (マルチチャネルDAC) | 12 | 400 | 4,800 | 8ch/基板、14bit、1GSPS |
| 光スイッチ | 光スイッチ行列 (Polatis系 192×192) | 4 | 1,500 | 6,000 | 挿入損失 < 0.5dB、切替 < 25ms |
| | **フォトニック回路系 小計** | | | **49,200** | |

### 11.1.3 遅延線系

| カテゴリ | 品目 | 数量 | 単価(万円) | 小計(万円) | 備考 |
|---|---|---|---|---|---|
| HCF | 中空コアファイバ 600m スプール | 1,000 | 30 | 30,000 | 損失 2dB/km、OFS/Lumenisity |
| HCF | HCF-SMF スプライスアダプタ | 2,000 | 5 | 10,000 | 両端接続、接続損失 < 0.3dB |
| HCF | 温度安定化筐体 | 4 | 200 | 800 | ±0.1℃、250スプール/筐体 |
| HCF | 光サーキュレータ (共有設計用) | 200 | 10 | 2,000 | 双方向アクセス用 |
| | **遅延線系 小計** | | | **42,800** | |

### 11.1.4 検出系

| カテゴリ | 品目 | 数量 | 単価(万円) | 小計(万円) | 備考 |
|---|---|---|---|---|---|
| SNSPD | Fiber-coupled SNSPD | 8,192 | 15 | 122,880 | NbTiN、η>93%@1550nm、DCR<10Hz。Photon Spot/ID Quantique/SCONTEL。行列読み出し対応 |
| クライオ | BlueFors LD-400 | 2 | 8,000 | 16,000 | Tbase 0.8K、冷却能力 400μW@100mK |
| 読み出し | 行列読み出し回路基板 | 32 | 150 | 4,800 | 256ch/基板、HEMT前置増幅、4Kステージ動作 |
| 読み出し | バイアス電源ユニット | 8 | 300 | 2,400 | 1,024ch/ユニット、電流分解能 0.01μA |
| 読み出し | 同軸ケーブル (クライオ内、NbTi) | 256 | 3 | 768 | 低熱伝導、クライオ-室温間 |
| | **検出系 小計** | | | **146,848** | |

### 11.1.5 制御・演算系

| カテゴリ | 品目 | 数量 | 単価(万円) | 小計(万円) | 備考 |
|---|---|---|---|---|---|
| FPGA | Xilinx Versal AI Edge VEK280 | 12 | 250 | 3,000 | リアルタイムデコーダ、フィードバック制御 |
| Time Tagger | Swabian Instruments Time Tagger Ultra | 8 | 400 | 3,200 | 8ch/台、分解能 1ps |
| GPU | NVIDIA H200 GPUサーバ | 2 | 1,500 | 3,000 | 80GB HBM3、オフラインデコード・最適化 |
| CPU | AMD EPYC 9654 サーバ | 2 | 600 | 1,200 | 96コア、ホスト制御・データ管理 |
| NW | 100GbE スイッチ (Arista) | 1 | 300 | 300 | 32ポート |
| NW | 100GbE QSFP28 ケーブル | 8 | 5 | 40 | FPGA-GPU間 |
| クロック | Rb原子時計 + 分配器 | 1 | 200 | 200 | 10MHz基準、12ch分配 |
| SW | 量子制御ソフトウェアライセンス | 1 | 500 | 500 | Qiskit/Perceval統合 |
| | **制御・演算系 小計** | | | **11,440** | |

### 11.1.6 インフラ・共通

| カテゴリ | 品目 | 数量 | 単価(万円) | 小計(万円) | 備考 |
|---|---|---|---|---|---|
| ラック | 19インチラック (42U) | 8 | 80 | 640 | 耐震、ケーブルマネジメント付 |
| 光ファイバ | PMF パッチコード (925nm) | 30 | 3 | 90 | FC/APC両端 |
| 光ファイバ | SMF-28 パッチコード (1550nm) | 500 | 1 | 500 | 短距離接続用 |
| 光ファイバ | 16芯ファイバリボン + MTPコネクタ | 520 | 8 | 4,160 | Rack3→Rack5/6間 |
| 同軸 | SMA同軸ケーブル | 400 | 1 | 400 | RF信号・フィードバック |
| 電源 | UPS 20kVA | 1 | 300 | 300 | 制御系保護用 |
| 電源 | PDU (インテリジェント) | 8 | 30 | 240 | 各ラック1台 |
| 冷却 | 精密空調機 (PAC) | 2 | 500 | 1,000 | 22±0.5℃維持 |
| 冷却 | チラー (冷却水循環) | 1 | 400 | 400 | 60L/min, 18℃ |
| 除振 | 除振台 (Rack5/6用) | 2 | 300 | 600 | VC-D達成用、クライオスタット下 |
| 設備 | OAフロア (床下600mm) | 32m² | 3 | 96 | ファイバ・配管経路 |
| | **インフラ系 小計** | | | **8,426** | |

### 11.1.7 システムインテグレーション

| カテゴリ | 品目 | 数量 | 単価(万円) | 小計(万円) | 備考 |
|---|---|---|---|---|---|
| SI | 光学系アライメント・結合最適化 | 1式 | — | 15,000 | 8,192 SNSPD + 1,000 HCFの全結合調整 |
| SI | システム統合テスト | 1式 | — | 8,000 | 全系動作検証、6ヶ月 |
| SI | 制御ソフトウェア開発 | 1式 | — | 12,000 | デコーダ実装、GUI、自動校正 |
| SI | 据付・配線工事 | 1式 | — | 5,000 | クリーンルーム内施工 |
| | **SI 小計** | | | **40,000** | |

### 11.1.8 BoM合計

| カテゴリ | 小計(万円) | 構成比 |
|---|---|---|
| 光源系 | 61,000 | 17.0% |
| フォトニック回路系 | 49,200 | 13.7% |
| 遅延線系 | 42,800 | 11.9% |
| 検出系 | 146,848 | 40.8% |
| 制御・演算系 | 11,440 | 3.2% |
| インフラ・共通 | 8,426 | 2.3% |
| SI | 40,000 | 11.1% |
| **ハードウェア+SI 合計** | **359,714** | **100%** |

> **最大コストドライバ**: 検出系が全体の40.8%を占める。SNSPD 8,192個（12.3億円）が単独最大品目。SNSPD単価の低減（量産効果で15万円→10万円）が実現すれば約4億円の削減が可能。

### 11.1A Phase別BoMサマリー（v4.0新規）

#### 11.1A.1 Phase 0: 研究実証機（$8.0M = 約12億円）

| カテゴリ | コスト($K) | 構成比 | 主要品目 |
|---|---|---|---|
| 光源系 | 2,400 | 30% | QD 40,000個, QFC 2,048ch, レーザ系 |
| フォトニック回路系 | 1,200 | 15% | Si₃N₄ PIC 20枚, LNOI EO 96個 |
| 遅延線系 | 800 | 10% | HCF 600m×1,000本 |
| 検出系 | 2,400 | 30% | SNSPD 8,192個, BlueFors LD-400×2 |
| 制御・演算系 | 400 | 5% | FPGA×4, GPU×4 |
| インフラ・SI | 800 | 10% | ラック, 配線, 冷却, 据付 |
| **合計** | **$8,000K** | **100%** | **= $8.0M ≈ 12億円** |

> **注記**: v3.0のBoM合計（35.9億円）との差異は、v4.0ではPhase 0のハードウェアコストのみを計上し、人件費・保守費・ソフトウェア開発費を除外しているためである。プロジェクト総コスト（人件費・保守費込み）はセクション11.2を参照。

#### 11.1A.1b Phase 0実験計画コスト（v4.0 7人専門家会議確定版）

Phase 0の具体的実験計画（セクション12.5参照）のコスト内訳:

| Phase | 期間 | コスト | 主要品目 |
|---|---|---|---|
| Phase 0a（コンポーネント単体テスト） | Phase -1後半〜Phase 0前半（8ヶ月） | $590K | QDチップ24デバイス($210K)、18ch SNSPDアレイ($160K)、LNOI PIC($220K) |
| Phase 0b（2光子fusion実証） | Phase 0前半〜中盤（6ヶ月） | $110K | Phase 0a装置統合、追加光学系 |
| Phase 0c（最小論理qubit実証） | Phase 0後半〜Phase 1前半（9ヶ月） | $280K | SiN遅延線、FPGA、追加SNSPD |
| **合計** | **24ヶ月** | **$1.1M** | |

最小動作構成（1論理qubit、d=3表面符号）の総コスト: **$1.2M**（セクション3.5参照）

#### 11.1A.2 Phase 1: 小型実用機（$2.5-3.0M = 約3.8-4.5億円）（v4.0世界的専門家レビュー修正）

| カテゴリ | コスト($K) | 構成比 | 主要品目 | Phase 0比 |
|---|---|---|---|---|
| 光源系 | 700 | 26% | QD 2,000個（集積型）, QFC 128ch | 1/3.4 |
| フォトニック回路系 | 500 | 18% | Si₃N₄ PIC 4枚（高集積）, LNOI EO 24個 | 1/2.4 |
| 遅延線系 | 150 | 6% | 3層ハイブリッド遅延線（SiNオンチップ+SMF-28+HCF） | 1/5 |
| 検出系 | 800 | 30% | SNSPD 3,000-3,500個（erasure-aware符号で半減）, PT冷凍機(RDK-415E)+振動対策+水冷チラー, 周波数多重読み出し（MKID方式） | 0.33× |
| 制御・演算系 | 250 | 9% | FPGA×2 | 0.63× |
| インフラ・SI | 300 | 11% | 2ラック, 配線, サイドカー筐体, 水冷チラー | 0.38× |
| **合計** | **$2,700K** | **100%** | **= $2.5-3.0M ≈ 3.8-4.5億円** | **0.34×** |

> **v4.0実戦チーム注記**: v4.0当初の$2.5M見積りはSNSPD数3,200個を前提としていたが、qLDPC符号の未成熟と行列読み出し限界により6,000-7,000個が必要。PT冷凍機の振動対策（$50-80K）と水冷チラーの追加も反映。
>
> **v4.0世界的専門家レビュー修正**: Breuckmann + Rudolphの提案によるerasure-aware表面符号 + ソフト情報デコーディングの導入、およびBerggren提案の周波数多重読み出し（MKID方式）への変更により、SNSPD数を6,000-7,000個→3,000-3,500個に半減。検出系コストが大幅に削減され、Phase 1全体のコストは$3.5-4.0M→$2.5-3.0Mに修正。

**Phase 1コスト変動の主要要因**:
- SNSPD数: 3,200→6,000-7,000→**3,000-3,500個**（erasure-aware符号+ソフト情報デコーディングで半減。専門家レビュー修正）
- 読み出し方式: 行列読み出し→**周波数多重読み出し（MKID方式）**（配線本数12,000→<10本、熱負荷1.2W→65mW。Berggren提案）
- 冷却系: 希釈冷凍機→PT冷凍機（ただし振動対策+水冷チラー追加）
- 遅延線: HCF 600m×数千本→**3層ハイブリッド（SiNオンチップ+SMF-28+HCF）**（コスト70倍削減。Rudolph再計算）
- 集積化: QD/QFC/EO/PICの集積度向上 → 光源・回路コスト削減

#### 11.1A.3 Phase 2: 次世代小型機（$1.5M = 約2.3億円）

| カテゴリ | コスト($K) | 構成比 | 主要品目 | Phase 0比 |
|---|---|---|---|---|
| 光源系 | 400 | 27% | QD 1,000個（モノリシック集積）, QFC集積チップ | 1/6 |
| フォトニック回路系 | 250 | 17% | モノリシックPIC 2枚, EO集積チップ | 1/5 |
| 遅延線系 | 80 | 5% | HCF 200m×50本 + チップ上遅延 | 1/10 |
| 検出系 | 400 | 27% | SNSPD 1,500-2,000個（erasure-aware符号+ソフト情報デコーディングで半減）, PT冷凍機一体型, 周波数多重読み出し | 1/6 |
| 制御・演算系 | 150 | 10% | FPGA×1 + デコーダASIC | 0.4× |
| インフラ・SI | 170 | 11% | 1ラック, 外部冷却ユニット | 0.2× |
| **合計** | **$1,500K** | **100%** | **= $1.5M ≈ 2.3億円** | **0.19×** |

#### 11.1A.4 Phase別コスト推移グラフ（テキスト表現）

```
コスト($M)
  8.0 |████████████████████████████████████████  Phase 0
  2.75|██████████████                              Phase 1 ($2.5-3.0M, 専門家レビュー修正)
  1.5 |████████                                  Phase 2
      └──────────────────────────────────────
```

**累積投資計画（Phase 0→2）**:
- Phase 0: $8.0M（約1〜2年後）
- Phase 1: $8.0M + $2.5-3.0M = $10.5-11.0M（約3〜4年後）（専門家レビュー修正）
- Phase 2: $10.5-11.0M + $1.5M = $12.0-12.5M（約5〜6年後）（専門家レビュー修正）

> Phase 0のハードウェアは研究資産として保持し、Phase 1/2は新規製造。Phase 0の一部コンポーネント（FPGA、GPU、光学テスト機器等）はPhase 1/2の開発・検証に再利用可能。

## 11.2 コストサマリー

### 11.2.1 総コスト構成

| 費目 | 金額(億円) | 備考 |
|---|---|---|
| ハードウェア + SI | 36.0 | BoM合計（11.1.8） |
| ソフトウェア開発（追加分） | 5.0 | デコーダ最適化、シミュレータ、運用ツール（7年分） |
| 人件費（7年分） | 18.0 | 研究者8名 + エンジニア6名 + PM2名、年平均1,600万円/人 |
| 消耗品・保守（7年分） | 7.0 | He回収、SNSPD交換、ファイバ清掃、クライオメンテ |
| 予備費 | 4.0 | 想定外リスク対応（総額の約5%） |
| **総額（基準シナリオ）** | **70.0** | |

### 11.2.2 3シナリオ比較

| シナリオ | ハードウェア | 人件費+SW | 保守+予備 | 総額(億円) | 前提条件 |
|---|---|---|---|---|---|
| **楽観** | 30.0 | 20.0 | 8.0 | **58.0** | SNSPD単価30%減（量産効果）、QFC歩留90%超、Phase1でSHYPS確定 |
| **基準** | 36.0 | 23.0 | 11.0 | **70.0** | 本設計書のBoM通り |
| **悲観** | 45.0 | 25.0 | 20.0 | **90.0** | SNSPD歩留60%（再製造必要）、HCF価格2倍、符号変更によるSI再実施 |

### 11.2.3 年度別投資計画

| 年度 | Phase | 投資額(億円) | 累計(億円) |
|---|---|---|---|
| Year 0 | Phase -1 | 0.5 | 0.5 |
| 約1年後 | Phase 0 | 5.0 | 5.5 |
| 約2年後 | Phase 1 | 15.0 | 20.5 |
| 約3〜4年後 | Phase 2 (前半) | 30.0 | 50.5 |
| 約4〜5年後 | Phase 2 (後半) | 19.5 | 70.0 |

## 11.3 v2.0とのコスト比較

| 項目 | v2.0 (億円) | v3.0 (億円) | 倍率 | 変更理由 |
|---|---|---|---|---|
| QD光源 | 5.0 | 4.0 | 0.8× | 1550nm InP→925nm GaAs（単価減）、12個は同数 |
| QFC | 0 | 2.1 | — | v3.0新規。925→1550nm変換が必要 |
| フォトニック回路 | 4.0 | 4.9 | 1.2× | Si₃N₄チップ増（SHYPS対応）、LNOI EO採用 |
| 遅延線 | 1.5 | 4.3 | 2.9× | ファイバ80ループ→HCF 1,000本。マジック状態蒸留レーン |
| SNSPD | 3.0 | 12.3 | 4.1× | 256個→8,192個（32倍）。ただし量産効果で単価は半減 |
| クライオスタット | 1.5 | 2.2 | 1.5× | 1台→2台（SNSPD増に伴う冷却容量確保） |
| 読み出し回路 | 0.5 | 0.8 | 1.6× | 行列読み出し回路追加 |
| 制御・演算 | 2.0 | 1.1 | 0.6× | FPGAの世代更新で台数削減 |
| インフラ | 1.5 | 0.8 | 0.5× | ラック数増だがスケールメリット |
| SI | 5.0 | 4.0 | 0.8× | 経験蓄積による効率化、ただし規模は増大 |
| 人件費(7年) | 8.0 | 18.0 | 2.3× | チーム規模拡大（10名→16名）、期間延長 |
| その他 | 1.0 | 16.5 | — | ソフトウェア、保守、予備費の充実 |
| **合計** | **33.0** | **70.0** | **2.1×** | |

> **コスト増の主因**: (1) SNSPD 32倍増 (+9.3億円)、(2) HCF遅延線拡大 (+2.8億円)、(3) QFC新規追加 (+2.1億円)、(4) 人件費・保守の現実的見積り (+17.5億円)。v2.0では人件費・保守が過小評価であった。

---
