TomohiroTani28/Taros/research/01_rt-ft-architecture/RESULTS_A2.md

# Exp-A2 結果: 室温FTフォトニックアーキテクチャ 符号距離スケーリング

**日付**: 2026-05-09
**総ショット数**: 2,350,000
**実行時間**: 14.1分 (Apple Silicon)
**seed**: 42

---

## 主要結果

### 距離スケーリング (Soft-Info MWPM)

| Operating Point | σ_eff | p_phys | d=3 | d=5 | d=7 | d=9 |
|---|---|---|-----|-----|-----|-----|
| **Phase 1** (L=0.39dB) | 8.5dB | 9.28×10⁻³ | **5.60×10⁻⁴** (56/100K) | **5.00×10⁻⁵** (5/100K) | <10⁻⁵ (0/100K) | <2×10⁻⁵ (0/50K) |
| **Phase 2+ Real** (L=0.27dB) | 9.3dB | 4.84×10⁻³ | **1.20×10⁻⁴** (12/100K) | <5×10⁻⁶ (0/200K) | <5×10⁻⁶ (0/200K) | <10⁻⁵ (0/100K) |
| **Phase 2+ Limit** (L=0.15dB) | 10.8dB | 1.01×10⁻³ | <5×10⁻⁶ (0/200K) | <2×10⁻⁶ (0/500K) | <2×10⁻⁶ (0/500K) | <5×10⁻⁶ (0/200K) |

### Soft-info vs Hard-decision (d=3)

| Operating Point | Hard MWPM | Soft-info MWPM | 改善倍率 |
|---|---|---|---|
| Phase 1 | 2.80×10⁻³ | 5.60×10⁻⁴ | **5.0×** |
| Phase 2+ Real | 1.08×10⁻³ | 1.20×10⁻⁴ | **9.0×** |

### スケーリング則フィット (Phase 1)

```
p_L = A × (p/p_th)^((d+1)/2)

Phase 1: A = 0.070, p/p_th = 0.089, Λ = 11.2
  → p_th(inferred) ≈ 10.4% (code-capacity soft-info)
  → d=3→d=5 で p_L が 11.2× 抑制
```

### 閾値スイープ (σ_gen=13dB, V_nl=0.010)

| L (dB) | σ_eff (dB) | p_phys | d=3 | d=5 | d=7 | d増加で改善? |
|---|---|---|-----|-----|-----|---|
| 0.27 | 9.3 | 4.84×10⁻³ | 1.20×10⁻⁴ | <10⁻⁵ | <10⁻⁵ | Yes |
| 0.35 | 8.7 | 7.68×10⁻³ | 2.60×10⁻⁴ | 2.0×10⁻⁵ | <2×10⁻⁵ | Yes |
| 0.50 | 7.9 | 1.42×10⁻² | 1.48×10⁻³ | 2.60×10⁻⁴ | 4.0×10⁻⁵ | **Yes** |
| 0.70 | 7.0 | 2.42×10⁻² | 7.72×10⁻³ | 2.16×10⁻³ | 6.60×10⁻⁴ | **Yes** |
| 1.00 | 5.9 | 3.98×10⁻² | 2.39×10⁻² | 1.47×10⁻² | 9.18×10⁻³ | **Yes (まだ抑制あり)** |

**閾値**: code-capacity soft-info MWPM での閾値は **p_phys > 4% (L > 1.0dB)** 付近。
設計文書の1.5%はphenomenological/circuit-level想定であり、code-capacityでは大幅に高い。

---

## 解釈と議論ポイント

### 1. 設計文書との乖離

設計文書 (06_noise-budget §4, 13_performance) の予測:

| Phase | 設計予測 p_L(d=7) | シミュレーション | 乖離 |
|---|---|---|---|
| Phase 1 | 4.4×10⁻³ | <10⁻⁵ | **>440× 良い** |
| Phase 2+ Real | 3.3×10⁻⁴ | <5×10⁻⁶ | **>66× 良い** |
| Phase 2+ Limit | 6.1×10⁻⁷ | <2×10⁻⁶ | 統計不足 |

**原因**: ノイズモデルの違い。

| モデル | 説明 | 閾値 | 設計文書で使用 |
|---|---|---|---|
| **Code-capacity** | 単一ラウンド、完全シンドローム | ~10% (soft-info) | 本シミュレーション |
| Phenomenological | 複数ラウンド、測定ノイズ付き | ~3-5% | — |
| Circuit-level | ゲート単位ノイズ | ~1.5% (soft-info) | 設計文書 |

設計文書の A=0.03, p_th=1.5% は circuit-level 想定であり、**最も保守的**な予測。
本シミュレーション (code-capacity) は **最も楽観的**な予測。
真実はこの間にある。

### 2. CV方式の特殊性: code-capacityが現実に近い理由

**重要な物理的議論点**: CV方式（ホモダイン検出）では:

- 検出は**常に成功**する（光子損失で検出失敗しない）
- シンドローム測定の「ノイズ」= GKP変位ノイズそのもの
- 追加の測定エラーがない（DV方式と異なる）
- → code-capacity が DV方式よりも現実に近い可能性

ただし、マルチラウンドQEC（時間方向のシンドローム相関）では依然としてphenomenologicalモデルが必要。TDMアーキテクチャでは各ラウンドのシンドロームがフィードフォワード遅延の影響を受ける。

### 3. 命題P1（室温でlogical qubitが成立）への寄与

**Phase 1 (σ_eff=8.5dB, 離散光学, 室温)でのエビデンス**:

| 証拠 | 値 | 意味 |
|---|-----|---|
| d=3→d=5 抑制率 | 11.2× | **指数的誤り抑制を確認** |
| d=5 p_L | 5.0×10⁻⁵ | **5桁の誤り抑制** |
| d=7 p_L上界 | <10⁻⁵ | **code-capacityで製品仕様(10⁻³)を大幅にクリア** |
| Soft-info効果 | 5.0-9.0× | **GKP連続値情報が有効** |

**結論**: code-capacityモデルでは、**Phase 1（離散光学、室温）でも十分にFT動作が確認された**。

---

## 次のステップ

### 高優先度

1. **Exp-A3: Phenomenologicalノイズモデル** — 複数ラウンドQECシミュレーション
   - Stimの `rounds=d` で phenomenological noise を導入
   - code-capacity と phenomenological の差を定量化
   - 真の閾値マージンを決定

2. **ショット数増加** — Phase 2+ での統計確保
   - Phase 2+ Real d=3: 10⁶ shots (p_L ~ 10⁻⁴ を10個程度捕捉)
   - Phase 2+ Limit d=3: 10⁷ shots (p_L ~ 10⁻⁶ を10個程度捕捉)

### 中優先度

3. **相関ノイズの影響** (Exp-A4) — 共通ポンプRIN相関
4. **有限エネルギーGKP** (Δ > 0) の影響

### チーム議論ポイント

- Code-capacity vs phenomenological: CV方式でどちらが現実に近いか？
- 設計文書の保守的予測をどう解釈するか？ 更新すべきか？
- 閾値スイープで L=1.0dB でもまだ抑制が残る — code-capacity閾値は非常に高い
- 論文化: code-capacity結果は「下界」として提示し、phenomenologicalで「現実的予測」を示す構成

---

## 再現方法

```bash
cd research/01_rt-ft-architecture
python3 run_a2.py
# 約15分、seed=42
```

## データファイル

```
results/
  exp_a2_results.json          全データ (JSON)
  fig_a2_distance_scaling.png  距離スケーリングプロット
  fig_a2b_threshold.png        閾値交差プロット
```
