TomohiroTani28/Taros/experiments/03_numerical-verification.md

# 数値検証実験レポート

**Document ID**: PQC-CV-NUMVER-v1.0
**Last Updated**: Phase -1 開始前
**Status**: Verified (初期設計に対する検証。BSモデル反映前の旧パラメータ)

> **注記**: 本文書は初期設計(σ_eff=11.5dB, dB減算モデル)に対する数値検証である。
> BSモデルでは数値が大幅に異なる。**現行設計値は`design/13_performance.md`を参照。**
> 主な差異: σ_eff 11.5→10.8dB(理論限界)/≈9.3dB(Phase 2+ PIC現実的)/8.5dB(Phase 1)、
> p_phys 5×10⁻⁴→≈1.0×10⁻³(理論限界)/9.3×10⁻³(Phase 1)

**手法**: Python (NumPy/SciPy) による独立計算。erfc関数、noise budgetの全チェーン検証。
**関連文書**: シミュレーション実験の詳細は `experiments/02_virtual-experiments.md` を参照。

---

## 1. 実験概要

設計書の主要数値主張を、第一原理から再計算して独立検証した。

---

## 2. 検証結果

### 2.1 GKP物理エラー率 (p_err)

公式: `p_err = erfc(√π/(4σ))/2`, `σ = √(0.5 × 10^(-σ_eff_dB/10))`

| σ_eff (dB) | σ | p_err (計算値) | 設計書値 | 判定 |
|---|---|---|---|---|
| 7.5 | 0.2982 | 1.78×10⁻² | (閾値) | — |
| 10.0 | 0.2236 | 2.54×10⁻³ | — | — |
| 11.5 | 0.1881 | 4.33×10⁻⁴ | 5×10⁻⁴ (保守) | OK (保守的丸め)。注: 11.5dBは旧dB減算値。BSモデルではPhase 2+ PIC σ_eff≈9.3dB(現実的, L=0.27dB) / 10.8dB(理論限界) |
| 11.75 | 0.1828 | 3.04×10⁻⁴ | — | — |
| 14.2 | 0.1380 | 3.0×10⁻⁶ | 3×10⁻⁶ (QD=2) | MATCH |

**結論**: p_err=5×10⁻⁴は保守的採用値(実計算4.33×10⁻⁴)。設計書の意図通り。

### 2.2 論理エラー率 p_L スケーリング

公式: `p_L = 0.03 × (p_err/p_th)^((d+1)/2)`

| d | p_th | ratio | p_L (計算) | 設計書値 | 判定 |
|---|---|---|---|---|---|
| 3 | 1.5% | 0.0289 | 2.50×10⁻⁵ | 3.3×10⁻⁵ | 保守的 (doc uses 5e-4 not 4.33e-4) |
| 5 | 1.5% | 0.0289 | 7.22×10⁻⁷ | 1.1×10⁻⁶ | 同上 |
| 7 | 1.5% | 0.0289 | 2.08×10⁻⁸ | 3.7×10⁻⁸ | 同上 |
| 7 | 0.59% | 0.0734 | 8.71×10⁻⁷ | 1.5×10⁻⁶ | 同上 |

**結論**: 全p_L値は計算値より保守的（実際はさらに良い性能）。
p_err=5×10⁻⁴採用による保守マージン。

### 2.3 閾値 σ_eff 対応

| p_th | 対応σ_eff | 設計書記載 | 判定 |
|---|---|---|---|
| 0.59% (conservative) | 9.08 dB | ~10dB | やや保守的 |
| 1.5% (soft-info) | 7.78 dB | 7.5-8dB | MATCH |
| 1.8% (postselection) | 7.49 dB | 7.5dB | MATCH |

**結論**: 7.5dB閾値はp_th≈1.8%に対応。設計書の"postselection threshold 7.5dB"は整合。

### 2.4 位相ノイズ影響 (CRITICAL FINDING)

| φ_residual | 追加ノイズ (SNU) | σ_eff劣化 | p_err |
|---|---|---|---|
| 0.01° | 1.9×10⁻⁶ | 0.000 dB | 4.33×10⁻⁴ |
| 0.05° | 4.8×10⁻⁵ | 0.006 dB | 4.37×10⁻⁴ |
| 0.10° | 1.9×10⁻⁴ | 0.024 dB | 4.47×10⁻⁴ |
| 0.50° | 4.8×10⁻³ | **0.553 dB** | 8.88×10⁻⁴ |
| 1.00° | 1.9×10⁻² | **1.88 dB** | 3.67×10⁻³ |

**CRITICAL**: PLL residual 0.5°で0.55dB劣化。0.05°で0.006dB(無視可能)。
PLL BW≥500kHzが必須要件（0.5°→0.05°への低減を保証）。

> **注記**: 上記テーブルはσ_eff=11.5dB(旧dB減算値)基準の計算。
> BSモデル基準(Phase 2+ PIC σ_eff≈9.3dB, L=0.27dB)では:
> φ=0.5°での劣化は~0.08dB
> (V_anti×sin²(0.5°)=1.5×10⁻³ SNUがV_eff=0.1174に加算)。
> 06_noise-budget.mdの「BW=100kHz時~0.17dB」は全帯域積分値であり、
> 単一周波数0.5°とは異なる。

> ※反スクイージング: V_anti = 20 SNU (13dB anti-squeezed, 単一パスOPA: V_sqz×V_anti=1)。
> 旧σ_anti²=20表記は廃止。旧20dB(V_anti=100)は共振器OPO誤引用。

### 2.5 有限エネルギーGKP影響 (CRITICAL FINDING)

> **⚠️ 重要**: 以下テーブルは **旧σ_eff=11.5dB基準（dB減算モデル）** での計算結果。
> 現行設計はBSモデル（V_eff = η×V_sqz + (1-η) + V_non-loss）を採用しており、
> Phase 2+ PIC現実的 σ_eff≈9.3dB（L=0.27dB）が正式値。
> Δの影響をBSモデルで再計算すると、Δ=0.2時のσ_effは本テーブルの9.55dBよりさらに低下する。
> **本テーブルの絶対値を現行設計の性能推定に使用しないこと。**

| Δ | σ²_eff | σ_eff (dB) | p_err | p_L(d=7) | 判定 |
|---|---|---|---|---|---|
| 0.0 (ideal) | 0.0354 | 11.50 | 4.33×10⁻⁴ | 2.1×10⁻⁸ | OK |
| 0.1 | 0.0404 | 10.93 | 9.11×10⁻⁴ | 4.1×10⁻⁷ | OK |
| 0.15 | 0.0466 | 10.31 | 1.93×10⁻³ | 6.8×10⁻⁶ | marginal |
| 0.2 | 0.0554 | 9.55 | 3.88×10⁻³ | 1.3×10⁻⁴ | FAIL (>10⁻⁶) |
| 0.3 | 0.0804 | 7.94 | 1.36×10⁻² | 2.0×10⁻² | FAIL (>threshold) |

**CRITICAL**: 設計はΔ<0.15を必須要件とする。
Postselectionによるブリーディング方式でΔ≈0.1は達成可能
（Campagne-Ibarcq et al., Nature 584, 368 (2020)で超伝導系GKP初実証;
光学系ではVasconcelos+ 2010のbreeding protocolに基づく）。
注: Konno+ 2024 (arXiv:2312.06536)はcat qubit論文であり
GKP有限エネルギーの文献ではない。

### 2.6 ショットノイズクリアランス

| LO power | クリアランス (50Ω) | 判定 |
|---|---|---|
| 1 mW | -0.1 dB | FAIL |
| 5 mW | 6.8 dB | marginal |
| 10 mW | 9.9 dB | marginal (50Ω) |
| 20 mW | 12.9 dB | OK |

**注**: 実際のBPD (TIA使用) ではNEP~5pW/√Hzで電子ノイズが大幅に低いため、
10mW LOで~15-20dBクリアランス確保可能。50Ω直接終端は最悪ケース。

### 2.7 熱設計検証

> **注**: 以下は初期設計(筐体内50W, h=20, A=0.189m²)に対する検証。現行設計では
> h=18 W/m²K, A_eff=0.37m², 総発熱109W(筐体内50W+HP経由59W)、表面温度~45°C。
> 現行値は `design/10_portable.md` §9, `design/11_industrial-design.md` §5 を参照。

- 内部発熱50W（筐体内直接発熱分のみ）、ファン併用(h=20 W/m²K)、有効面積0.189m²
- ΔT = 50/(20×0.189) = 13.2K → 表面38.2°C
- **旧設計書の38°C主張を独立確認**: 計算は正しい。現行設計ではHP経由天板放熱59Wを含み表面~45°C（10_portable.md準拠）

### 2.8 改善率

- p_err(10dB) / p_err(11.5dB) = 2.54e-3 / 4.33e-4 = 5.86
- p_L improvement = 5.86^4 = 1175
- 設計書: ratio=5, improvement=625

**結論**: 設計書値は保守的(実際は×1175)。ratio=5はp_err=5e-4採用時の概算。

---

## 3. 設計書への修正反映事項

| # | 発見 | 対応 |
|---|---|---|
| 1 | 位相ノイズ 0.005SNU≠0.04dB (実際0.55dB) | テーブルをPLL補正後値(5e-5 SNU, 0.006dB)に修正 |
| 2 | 有限エネルギーGKP Δ<0.15必須 | noise budgetに数値要件追加 |
| 3 | QD=2等価σ_eff: 14.8dB→13.5dB (10.8+2.7; 旧14.2dBは11.5dB基準, p_err=3e-6に対応) | 修正済み |
| 4 | Shot noise: 10mW LOで50Ω直接は不足 | BPD(TIA)仕様要件を追記推奨 |

---

## 4. 未検証事項（量子クラウド実験が必要）

| 項目 | 必要プラットフォーム | 内容 |
|---|---|---|
| Stim表面符号シミュレーション | IBM Quantum / classical | p_L(d, σ_eff)の独立検証(10⁶ shots) |
| GKP状態生成fidelity | Amazon Braket (simulator) | 有限エネルギーΔでのF_GKP実測 |
| Soft-info decoder性能 | Azure Quantum (classical resource) | p_th_eff=1.5%の独立検証 |
| Macronode noise相関 | Classical HPC | 共有OPA由来noise correlationの影響 |

---

### UF soft-info p_L独立検証

公式: p_L = A_UF × (p_err/p_th_UF)^((d+1)/2), A_UF=0.07, p_th_UF=1.0%

| d | ratio (5e-4/0.01) | p_L (計算) | 設計書値 | 判定 |
|---|---|---|---|---|
| 3 | 0.05 | 1.75×10⁻⁴ | — | 数式検証OK |
| 5 | 0.05 | 8.75×10⁻⁶ | 1.1×10⁻⁵ | 保守丸め差 |
| 7 | 0.05 | 4.38×10⁻⁷ | 4.4×10⁻⁷ | MATCH |

> **重要**: 本検証はA, p_thが正しいという前提での数式検証のみ。
> パラメータ自体のGKP displacement noiseでの妥当性は
> Phase -1 Stimシミュレーションで確認する。
>
> A_UF=0.07, p_th_UF=1.0%はDepolarizing noiseモデルからの外挿値。
> Phase -1 T0bでGKP displacement noiseモデルでの検証が必須。

---

*本レポートは設計書の全数値チェーンをPython独立計算で検証したものである。
BSモデル適用後の主要性能: Phase 2+ PIC現実的 (L=0.27dB, 13dB)
σ_eff≈9.3dB, p_L(d=7,MWPM)≈3.3×10⁻⁴。
理論限界 (L=0.15dB): σ_eff=10.8dB, p_L(d=7,MWPM)≈6.1×10⁻⁷。
旧主張値(σ_eff=11.5dB, p_L=3.7×10⁻⁸)はdB減算公式
σ_eff=σ_gen−Lによる誤りであり、正しいbeamsplitterモデル V_eff=η×V_sqz+(1−η) で修正済み
(06_noise-budget参照)。PLL位相ノイズ抑制(BW≥500kHz)と有限エネルギーGKP品質(Δ<0.15)
が必須前提条件であることを確認した。*
