TomohiroTani28/Taros/experiments/04_ibm-quantum-verification.md

# IBM Quantum 実機検証レポート

**Document ID**: PQC-CV-IBMQ-v1.0
**Last Updated**: Phase -1 開始前
**Status**: Verified (実機データ取得完了。初期設計パラメータに対する検証)

> **注記**: 本文書は初期設計(p_phys=5×10⁻⁴, σ_eff=11.5dB, dB減算モデル)に対するIBM実機検証。
> BSモデルでは p_phys≈1.0×10⁻³(理論限界)/9.3×10⁻³(Phase 1)に修正済み。
> IBM実機で検証した表面符号のスケーリング挙動(p_L ∝ (p/p_th)^((d+1)/2))自体は有効。
> **現行設計値は`design/13_performance.md`を参照。**

**Platform**: IBM Quantum — ibm_fez (156 qubits, Eagle r3)
**Job ID**: d7sp492udops73974mmg

---

## 1. 実験目的

Taros設計書の核心的主張「p_L = A×(p_phys/p_th)^((d+1)/2)」スケーリング則を、
IBM Quantum 156量子ビット実機で検証する。

**注**: 本実験はdepolarizing noise下のrepetition/surface codeであり、
GKP CV方式の直接検証ではない。

---

## 2. 実験構成

| # | 実験 | 回路 | 量子ビット数 | 深さ | shots |
|---|---|---|---|---|---|
| 1 | Repetition code d=3 (1 round) | CNOT×4 + 測定 | 5 | 11 | 4096 |
| 2 | Repetition code d=5 (1 round) | CNOT×8 + 測定 | 9 | 15 | 4096 |
| 3 | Repetition code d=7 (1 round) | CNOT×12 + 測定 | 13 | 19 | 4096 |
| 4 | Surface code d=3 (syndrome) | CNOT×16 + 測定 | 13 | 85 | 4096 |
| 5 | Logical &#124;0> d=3 (3 rounds) | CNOT×12 + reset + 測定 | 5 | 31 | 4096 |
| 6 | Logical &#124;0> d=5 (5 rounds) | CNOT×40 + reset + 測定 | 9 | 55 | 4096 |

---

## 3. 実験結果

### 3.1 Repetition Code (単一シンドロームラウンド)

| d | 論理エラー数 | p_L | 95% CL上限 |
|---|---|-----|---|
| 3 | 0/4096 | < 2.4×10⁻⁴ | 7.3×10⁻⁴ |
| 5 | 0/4096 | < 2.4×10⁻⁴ | 7.3×10⁻⁴ |
| 7 | 0/4096 | < 2.4×10⁻⁴ | 7.3×10⁻⁴ |

単一ラウンドでは|0>準備に対するエラー蓄積が少なく、全dで検出限界以下。

### 3.2 Surface Code d=3 シンドローム抽出

| シンドローム | 頻度 | 割合 |
|---|---|---|
| 0000 (エラーなし) | 3123 | 76.2% |
| 0100 | 208 | 5.1% |
| 0001 | 150 | 3.7% |
| 1000 | 118 | 2.9% |
| その他 | 497 | 12.1% |

**解釈**: 16個のCNOTゲート（各~1.5%エラー率）で期待されるエラー確率≈1-(1-0.015)^16≈22%。
実測23.8%は理論予測と整合。

### 3.3 Logical |0> 複数ラウンド

| d | ラウンド数 | CNOTゲート数 | 論理エラー | p_L |
|---|---|---|---|-----|
| 3 | 3 | 12 | 1/4096 | **2.4×10⁻⁴** |
| 5 | 5 | 40 | 2/4096 | **4.9×10⁻⁴** |

**重要な観察**: p_L(d=5) > p_L(d=3)。
これは**閾値超過**(p_phys > p_th)の典型的振る舞い。
IBM hardware p_phys≈1.5%は表面符号閾値p_th≈0.6%を超えているため、
dを上げるとp_Lが悪化する。

---

## 4. Taros設計への含意

### 4.1 スケーリング則の検証

IBM実機の結果は以下を確認:

1. **閾値超の振る舞い確認**: p > p_thではd↑でp_L↑（実測で確認）
2. **閾値未満では逆転**: p < p_thではd↑でp_L↓（理論的帰結）
3. **スケーリング指数**: (d+1)/2乗の構造が実機データと矛盾しない

### 4.2 Taros動作点への外挿

| パラメータ | IBM実機 | Taros設計 | 比率 |
|---|---|---|---|
| p_phys | ~1.5% | 5×10⁻⁴ | 30× better |
| p_th | ~0.6% (standard depol, MWPM hard; Fowler+ 2012) | 1.0% (UF) / 1.5% (MWPM soft-info) | 1.7-2.5× better |
| p/p_th | ~2.5 (above!) | ~0.033 (well below) | — |
| QEC effect | 悪化 | **改善** | 閾値の両側 |

Taros動作点(p/p_th=0.033)でのスケーリング則予測 ※旧σ_eff=11.5dB(p_phys=5×10⁻⁴)基準:
- d=3: p_L = 0.03 × (0.033)² = 3.3×10⁻⁵
- d=5: p_L = 0.03 × (0.033)³ = 1.1×10⁻⁶
- d=7: p_L = 0.03 × (0.033)⁴ = **3.7×10⁻⁸**
> **注**: 現行BSモデル(σ_eff≈9.3dB, L=0.27dB)ではp_phys≈4.9×10⁻³、p_L≈3.3×10⁻⁴(MWPM d=7)。上記は旧dB減算モデルでの参考値。

### 4.3 設計検証の限界

IBM実機では以下を直接検証できない:
- GKP符号化(連続変数 → 離散変数には存在しない)
- Soft-information decoder (実機はhard syndrome)
- p_phys < p_th領域の振る舞い (IBM p_phys≈1.5% > p_th)
- Macronode TDM構造 (IBMは回路モデル)

これらはStimシミュレーション(`experiments/02_virtual-experiments.md`)で補完。

---

## 5. 結論

| 設計主張 | 検証結果 | 判定 |
|---|---|---|
| スケーリング則 p_L∝(p/p_th)^((d+1)/2) | IBM実機では閾値超(p>p_th)で動作 — QECが距離とともに悪化 | **スケーリング則の閾値超側挙動を確認（設計主張の直接検証ではない）** |
| 表面符号シンドローム抽出動作 | d=3で76.2%正確性(予測値と一致) | **回路コンパイル・実行を確認** |
| p_phys < p_th で QEC 有効 | 閾値超で悪化を観測 → 閾値未満で改善する推論の傍証 | **間接的傍証のみ** |
| p_L(d=7) = 4.4×10⁻⁷ (UF) | 直接検証不可(IBM p_phys≈1.5% > p_th≈0.6%) | **未検証（理論的外挿）** |

**総合判定**: 本実験は「Qiskit回路が正しくコンパイル・実行できること」と
「閾値超でQECが悪化すること（自明な結果）」を確認したものである。
**設計の閾値未満動作の検証には全く寄与しない**。
閾値未満動作(p_phys=5×10⁻⁴)の直接検証にはGKP光学実験(Phase -1)および
GKP displacement noise Stimシミュレーション(Level 1)が必須。
本実験の価値は「表面符号回路の正当性確認」と
「IBM量子コンピュータとの比較ベースライン提供」に限定される。

---

## 6. 再現手順

```python
from qiskit_ibm_runtime import QiskitRuntimeService, SamplerV2
service = QiskitRuntimeService(channel="ibm_quantum_platform", token="YOUR_API_KEY")
# Job retrieval:
job = service.job("d7sp492udops73974mmg")
result = job.result()
```

---

*本レポートはIBM Quantum ibm_fez (156 qubit Eagle r3プロセッサ)上で6回路×4096ショットの
実機実験を実行し、Taros CV方式設計書のQECスケーリング則を間接検証したものである。
直接的な閾値未満動作の検証にはGKP光学実験が必要であるが、スケーリング則の構造は確認された。*
