TomohiroTani28/Taros/archive/14_future-vision/03_performance-10x.md

> **⚠ DEPRECATED**: 本文書はDV-FBQC方式に基づいており、CV方式移行に伴い数値（コスト・確率・スケジュール）は現行計画と大幅に異なります。CV方式の最新情報: `analysis/bom.md`, `analysis/risk.md`, `analysis/development-cost-summary.md`

## 16.3 性能10倍向上パス

### 16.3.1 3つの独立パス

v3.0設計の性能を10-1000倍に向上させる3つの独立したパスが存在する。各パスは独立に成功可能であり、複合的な効果も期待できる。

**パス1: 符号効率の改善（1000論理qubit達成）**

量子LDPC符号の導入により、1000論理量子ビットを約10,000物理量子ビットで実現する。表面符号では同等の性能に約1,000,000物理量子ビットが必要であるため、100倍の効率改善に相当する。

- 成功確率: 80%以上（理論は確立済み、実装が課題）
- 時期: Phase 1〜Phase 2（約3〜5年後）
- 前提: LDPC符号のFBQCデコーダ実装

**パス2: 速度の改善（100ns T gate間隔）**

量子メモリの導入によりサイクル時間を100nsに短縮し、さらに50並列蒸留によりT gate間隔を約100nsに短縮する。

- 成功確率: 40-60%（量子メモリの成熟が鍵）
- 時期: Phase 1-2〜Phase 2完了後（約4〜6年後）
- 前提: 光量子メモリの効率>50%、保存時間>10us

**パス3: スケールアウト（マルチノード接続）**

10ノード x 100論理量子ビット = 1000論理量子ビットを、エキスパンダーグラフ接続で実現する。光ファイバによるノード間接続はフォトニックシステムのネイティブな利点である。

- 成功確率: 60-70%（工学的課題が主）
- 時期: Phase 2〜Phase 2-3（約5〜7年後）
- 前提: ノード間ベルペア生成レート>1MHz

### 16.3.2 成功確率の統合評価

少なくとも1パスが成功する確率は90%以上と評価される。

---
