TomohiroTani28/Taros/archive/06_performance/01_logical-error-model.md

> **⚠ FROZEN (2026-05-04)**: 本文書はDV-FBQC v4.0 R6時点の設計を記録したものです。プロジェクトの主軸はCV方式に移行しています。最新設計は `design/00_overview.md` を参照してください。

# セクション8: 性能予測

## 8.1 論理誤り率モデル（改訂）

### 8.1.1 v2.0からの変更点

v2.0では以下の近似・外挿を用いていたが、Critical Reviewで全て否定された:

1. **AlphaQubit外挿の撤回**: AlphaQubit [Bausch+ 2024, Nature] は超伝導量子ビットのノイズモデルに最適化されたニューラルネットワークデコーダであり、フォトニック系への転用は不当。超伝導系のコヒーレントエラー構造とフォトニック系のerasure/loss構造は根本的に異なる。
2. **解析的外挿式の廃止**: p_L ∝ (p_phys/p_th)^(d/2) の近似式は、erasureとdepolarizingが混在するフォトニック系には適用できない。
3. **Stimシミュレーションを唯一の根拠とする**: 論理誤り率の予測は全てStimシミュレーション結果に基づく。Phase -1完了まで予測値は「暫定範囲」として扱う。

### 8.1.2 暫定性能予測範囲

Stimシミュレーション完了前の暫定予測として、既存文献の数値結果から範囲を推定する。

**表8.1: 暫定論理誤り率予測**

| 符号 | 符号距離 d | p_erasure | p_depol | 論理誤り率 p_L（暫定範囲） | 出典・根拠 |
|---|---|---|---|---|---|
| SHYPS | 7 | 40% | 1.0% | 10⁻² - 10⁻³ | Sahay+ 2023 Fig.5 からの読み取り（条件が完全一致しないため範囲で表示） |
| SHYPS | 11 | 40% | 1.0% | 10⁻³ - 10⁻⁵ | 同上の外挿; Stimで要検証 |
| 4D HPC | 7 | 40% | 1.0% | 10⁻¹ - 10⁻² | erasure率が4D HPCの閾値(~30%)を超過; 動作不能の可能性あり |
| 表面符号 | 7 | 40% | 1.0% | 動作不能 | erasure率が閾値(24.9%)を大幅超過 |
| SHYPS | 7 | 36% (Phase 3) | 0.7% | 10⁻³ - 10⁻⁴ | Phase 3改善後の推定 |
| SHYPS | 11 | 36% | 0.7% | 10⁻⁴ - 10⁻⁶ | 同上 |

**重要な注意**: 上記は暫定値であり、Stimシミュレーションの結果で大幅に変更される可能性がある。設計判断はPhase -1のシミュレーション完了後に確定する。

### 8.1.3 3パス別の評価

| パス | 主符号 | Phase 2 動作可否 | Phase 3 動作可否 | 優位性 |
|---|---|---|---|---|
| パス1: SHYPS | SHYPS (Sahay+ 2023) | 可能（マージン狭） | 可能（マージン十分） | erasure耐性最高; フォトニック系に最適 |
| パス2: 4D HPC | 4D Hyperbolic Product Code | 困難 | 可能（マージン狭） | 論理キュービット符号化効率が高い; 物理キュービット数削減 |
| パス3: 表面符号 | Raussendorf lattice | 不可能 | 困難 | 実装・復号が最も成熟; 超伝導系との比較容易 |

**推奨**: Phase 2ではパス1（SHYPS）に集中。Phase 3でerasure率改善後にパス2（4D HPC）を評価。パス3（表面符号）はベンチマーク・比較用途に限定。

---

## 8.2 性能予測まとめ

### 8.2.1 サイクル時間とゲート時間

**表8.2: タイミングパラメータ**

| パラメータ | 値 | 根拠 |
|---|---|---|
| 基本サイクル時間 | 2 μs | HCF 600m遅延 = 2μs; パウリフレーム更新 < 200ns |
| Fusionゲート時間 | 2 μs / fusion | 1サイクルで1 fusion実行 |
| 論理CZゲート時間 | d × 2μs = 14μs (d=7) | 符号距離d回のfusionサイクルが必要 |
| 論理Tゲート時間 | d × 2μs + 蒸留レイテンシ | 蒸留レイテンシは ~10 サイクル = 20μs（パイプライン化時） |
| マジック状態蒸留1ラウンド | ~20μs（パイプライン化） | 15 fusion × 2μs + 復号1ms → パイプライン化で隠蔽 |

### 8.2.2 論理ゲートレート

**表8.3: 論理ゲートレート予測**

| メトリック | Phase 2 (d=7, SHYPS) | Phase 3 (d=11, SHYPS) | 根拠 |
|---|---|---|---|
| 論理クリフォードゲートレート | ~71 kHz (= 1/14μs) | ~45 kHz (= 1/22μs) | d × 2μs |
| 論理Tゲートレート (1ファクトリ) | ~25 kHz | ~20 kHz | パイプライン化された蒸留 |
| 論理Tゲートレート (50ファクトリ) | ~1.25 MHz | ~1.0 MHz | ファクトリ数 × 単体レート |
| 論理キュービット数 | ~10-20 (Phase 2) | ~50-100 (Phase 3) | SNSPD 8,192個のリソース配分に依存 |

### 8.2.3 アプリケーション性能予測

v2.0からの再計算。全て暫定値であり、Stimシミュレーション結果に基づいて更新される。

**表8.4: アプリケーション性能予測**

| アプリケーション | 必要論理キュービット数 | 必要Tゲート数 | 推定実行時間（Phase 3） | 根拠 |
|---|---|---|---|---|
| VQE (H₂分子, 最小基底) | 4 | ~10³ | ~1 ms | 論理Tレート1MHz × 10³ = 1ms; Peruzzo+ 2014 |
| VQE (LiH, STO-3G) | 10 | ~10⁵ | ~100 ms | 同上スケーリング |
| Shor RSA-256 | ~512 | ~10⁹ | ~17 分 | Tゲート10⁹ / 1MHz = 10³ s ≈ 17分; Gidney & Ekera 2021ベース |
| Shor RSA-2048 | ~4,096 | ~10¹² | ~12 日 | 論理キュービット不足; Phase 3の50-100では実行不能。将来拡張が必要 |
| QAOA (MaxCut, n=50) | ~50 | ~10⁴ | ~10 ms | 浅い回路; Farhi+ 2014 |

**注意事項**:
- RSA-2048は本設計のスケール（50-100論理キュービット）では実行不能。実用的な暗号解読には10⁶物理キュービット規模が必要 [Gidney & Ekera 2021, Quantum 5, 433]。
- VQEやQAOA等のNISQ-like応用が本設計のPhase 2-3での現実的なターゲットである。
- 量子優位性の実証（例: ランダム回路サンプリング）は ~50論理キュービット × 深さ20で可能であり、Phase 3の目標範囲内。

---
