TomohiroTani28/Taros/archive/03_logical-layer/advanced/04_measurement-free-qec.md

> **⚠ FROZEN (2026-05-04)**: 本文書はDV-FBQC v4.0 R6時点の設計を記録したものです。プロジェクトの主軸はCV方式に移行しています。最新設計は `design/00_overview.md` を参照してください。

### 5.12 Measurement-Free QEC（v4.0 R4新規、Higgott提案 C26）

Phase 2+の長期オプションとして、デコーダ不要の自律的QECを記録する。

#### 5.12.1 原理

シンドローム測定→デコーダ→修正のサイクルを、**自律的フィードバック回路**で置換。fusion測定結果を直接次のfusion操作パラメータにフィードバックし、古典計算を不要にする [Crow+ 2016, PRL]。

- FPGA/GPU/ASIC全て不要 → 制御系コスト$50K→$5K
- サイクル時間が光速限界のみで決定
- ただしerasure閾値が~10-15%と低い → **クライオPIC（η=0.77、ε_herald~3%）が前提条件**

#### 5.12.2 導入判定

| 条件 | 基準 | 検証時期 |
|---|---|---|
| クライオPIC η≥0.75 | ε_herald < 10% | Phase 2中期 |
| MFQEC符号の設計完了 | Stim検証でerasure閾値>12% | Phase 1終了時 |
| フィードバック回路のPIC実装 | レイテンシ<1ns | Phase 2中期 |

---
