TomohiroTani28/Taros/research/01_rt-ft-architecture/results/fig_a2b_threshold.png

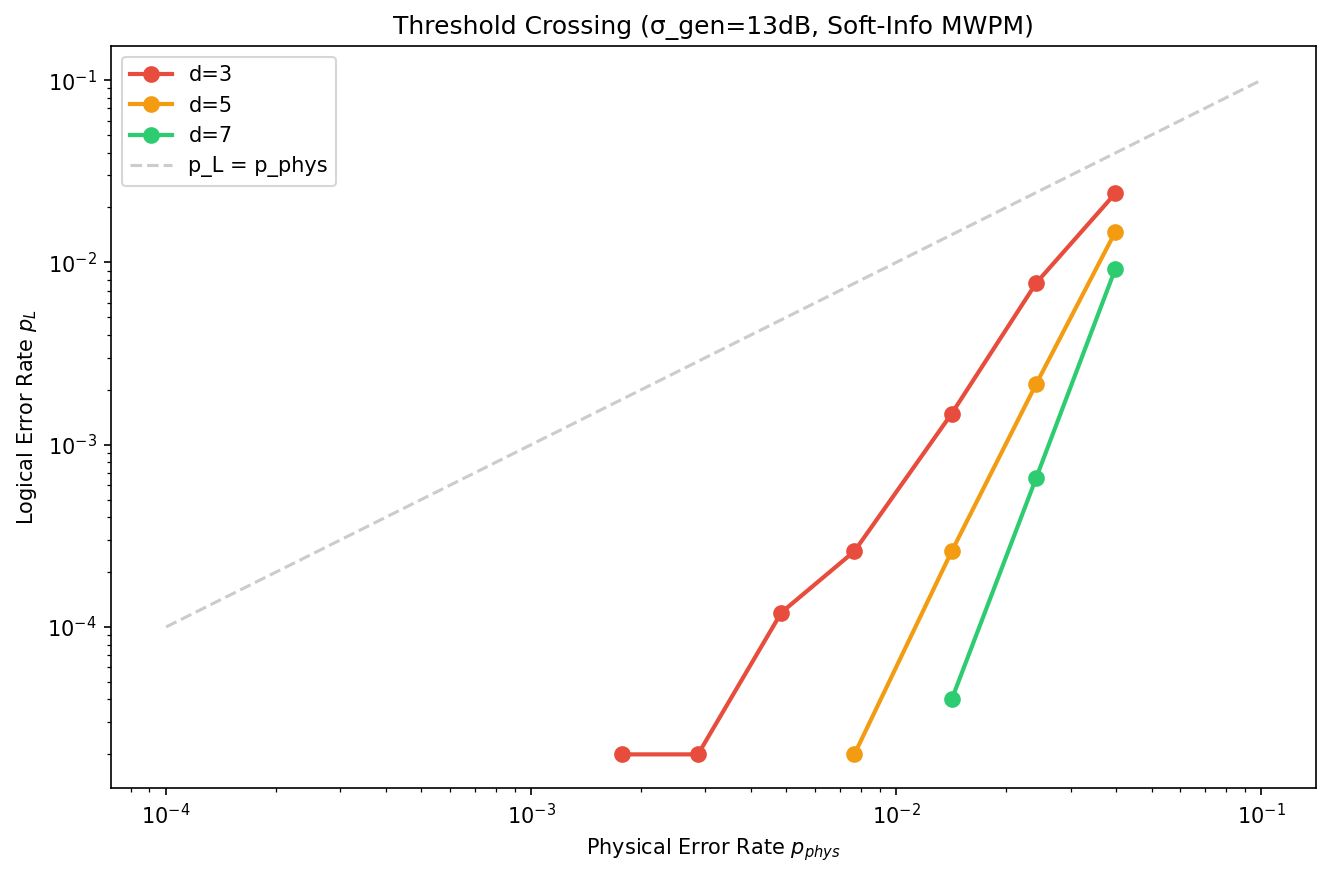
research/01_rt-ft-architecture/results/fig_a2b_threshold.png
