TomohiroTani28/Taros/research/01_rt-ft-architecture/results/fig_a3_cv_sensitivity.png

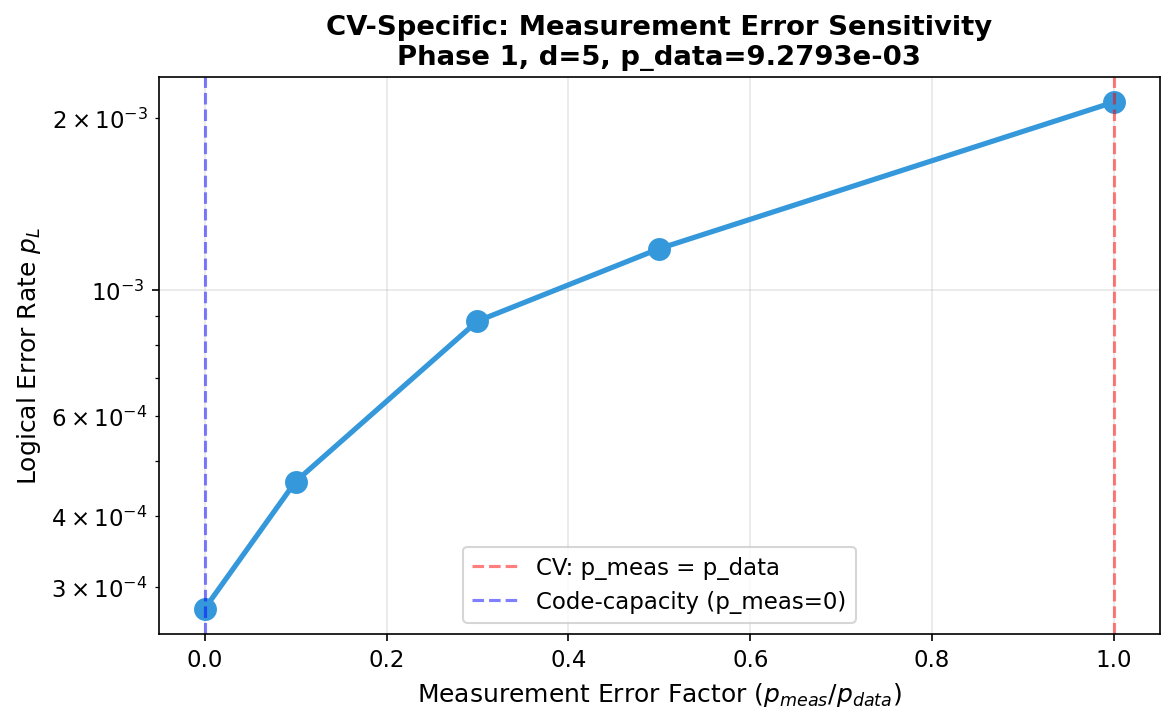
research/01_rt-ft-architecture/results/fig_a3_cv_sensitivity.png
