TomohiroTani28/Taros/research/01_rt-ft-architecture/results/fig_a3_threshold.png

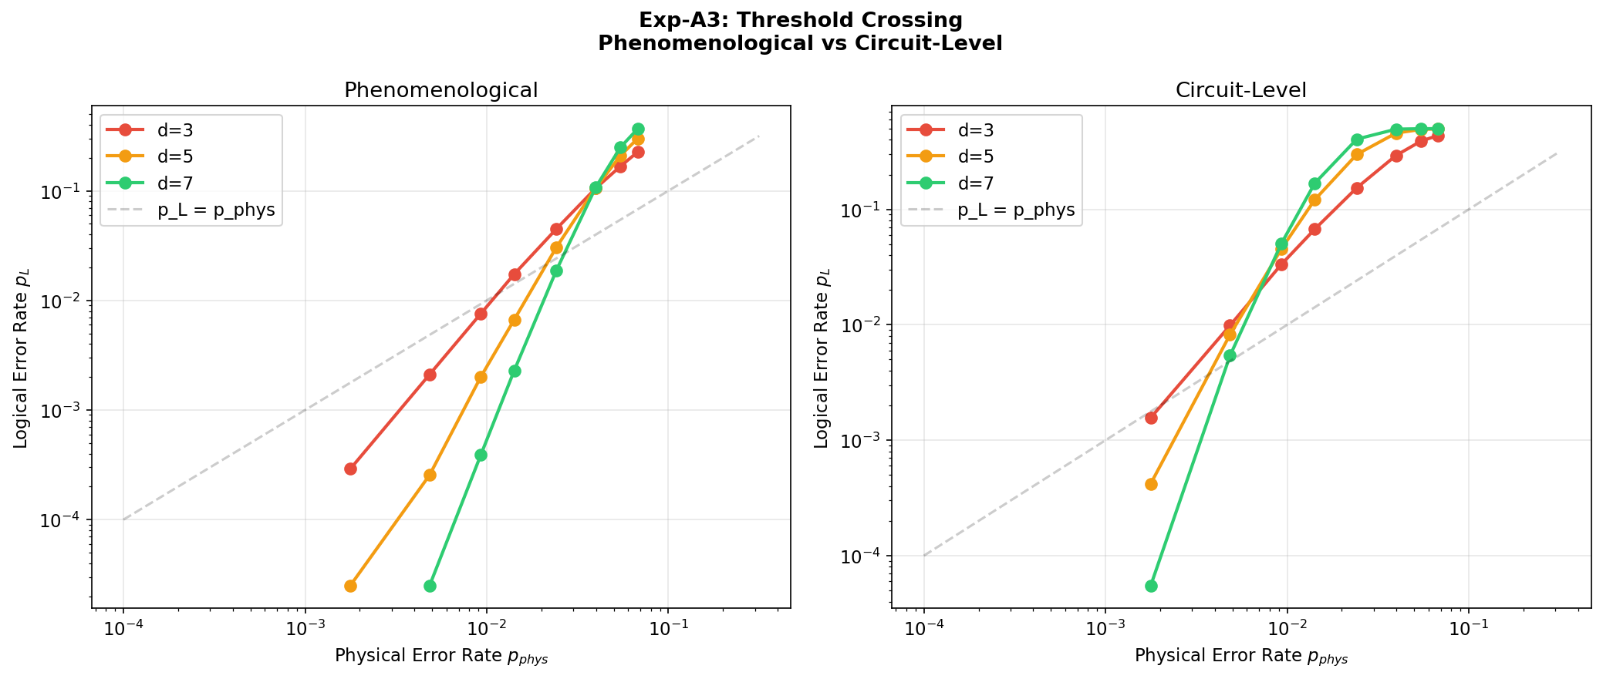
research/01_rt-ft-architecture/results/fig_a3_threshold.png
