TomohiroTani28/Taros/research/01_rt-ft-architecture/results/fig_advantage_ratio.png

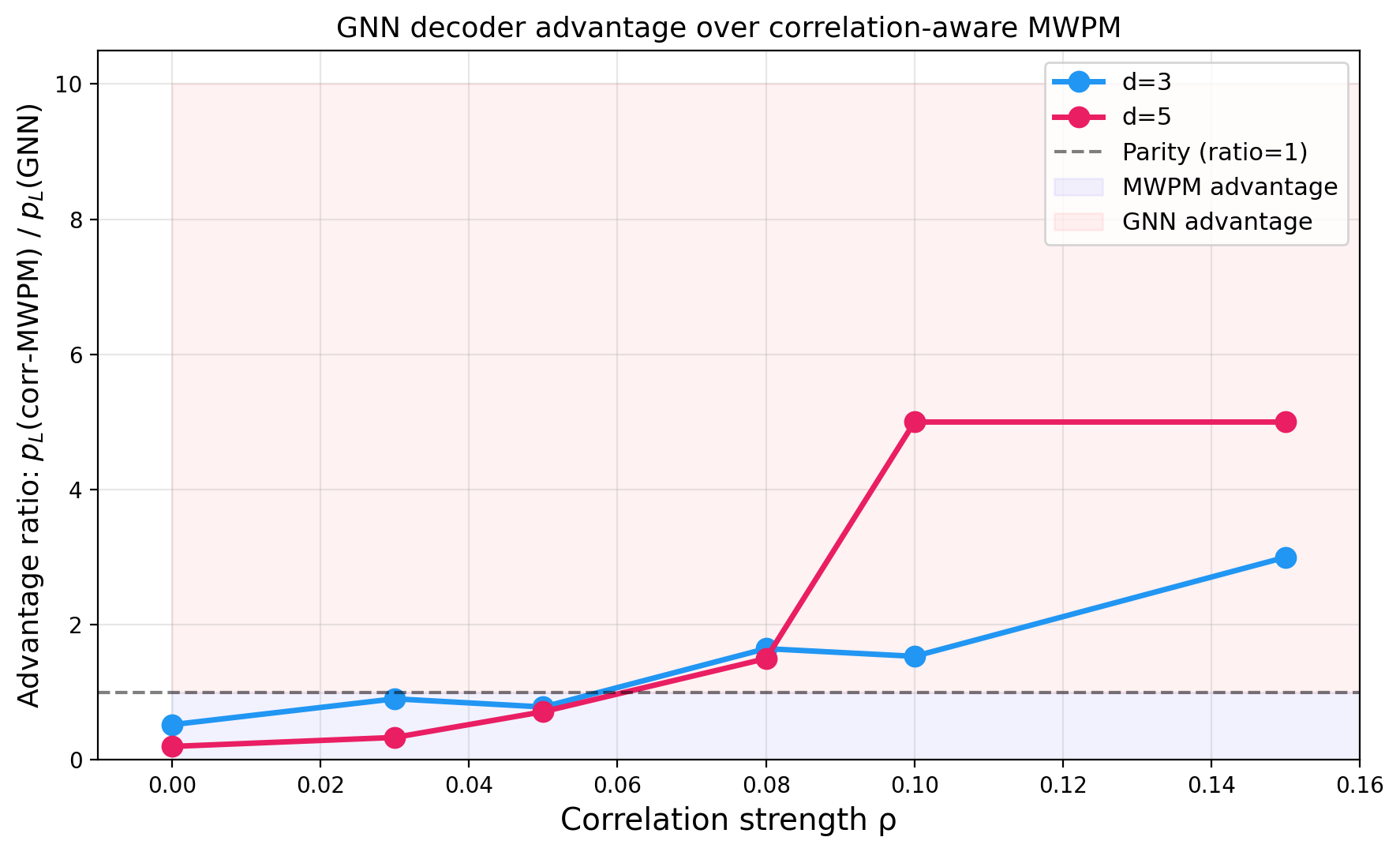
research/01_rt-ft-architecture/results/fig_advantage_ratio.png
