TomohiroTani28/Taros/research/01_rt-ft-architecture/results/fig_main_ler_vs_rho.png

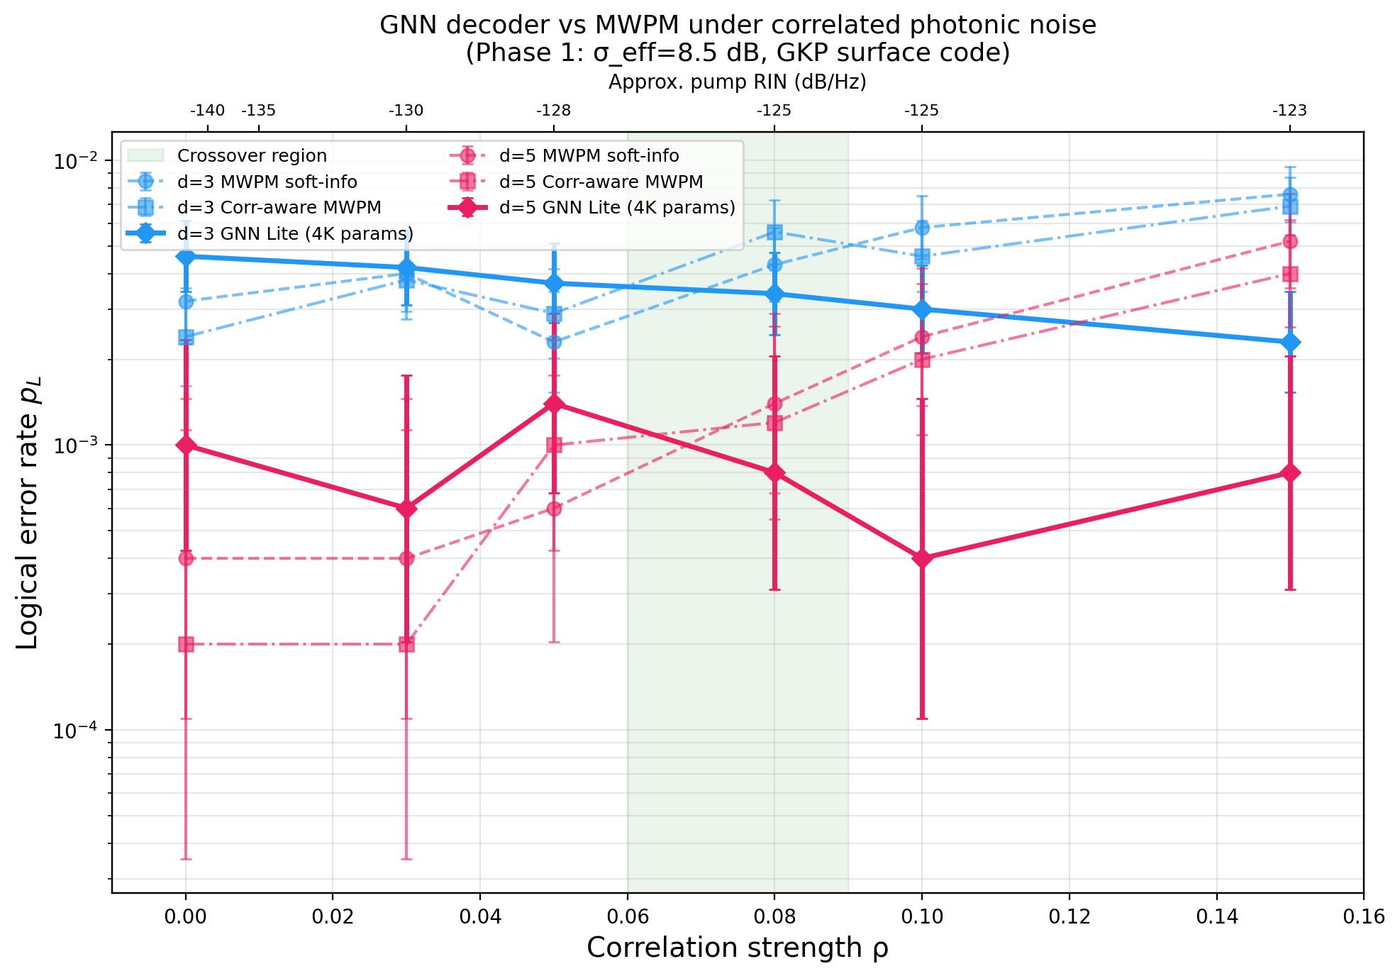
research/01_rt-ft-architecture/results/fig_main_ler_vs_rho.png
