TomohiroTani28/Taros/research/01_rt-ft-architecture/results/fig_main_model_comparison.png

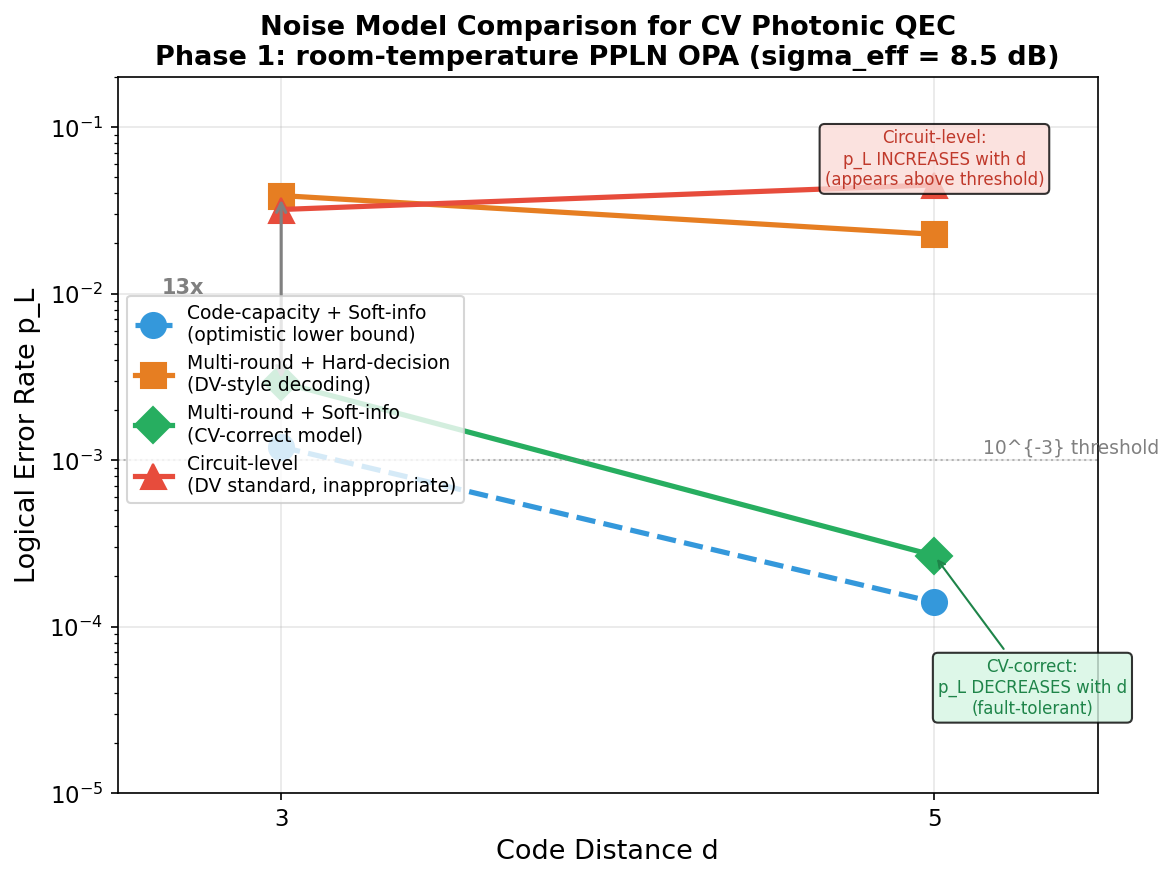
research/01_rt-ft-architecture/results/fig_main_model_comparison.png
