TomohiroTani28/Taros/research/03_gnn-photonic-decoder/results/fig_gnn_crossover.png

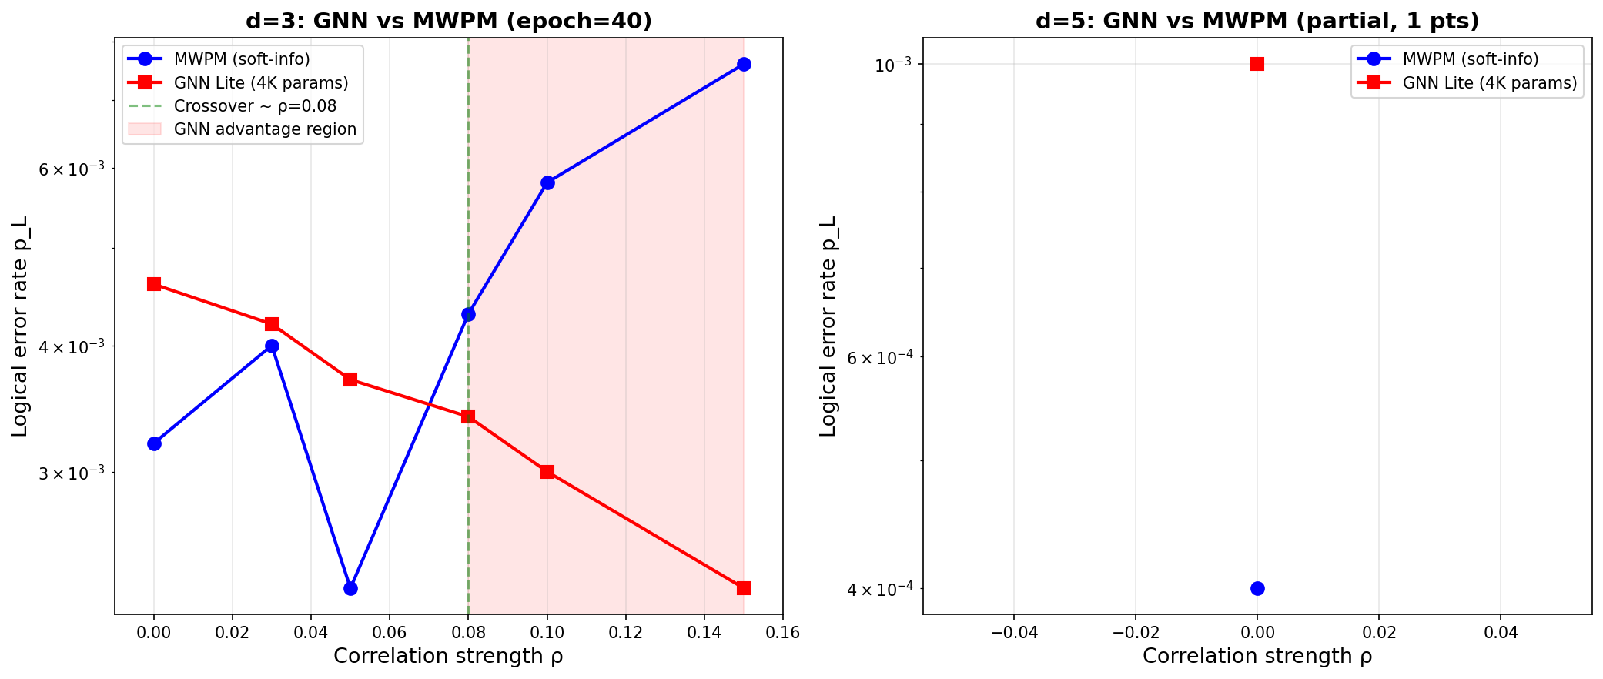
research/03_gnn-photonic-decoder/results/fig_gnn_crossover.png
