TomohiroTani28/Taros/research/results/fig1_comparison.png

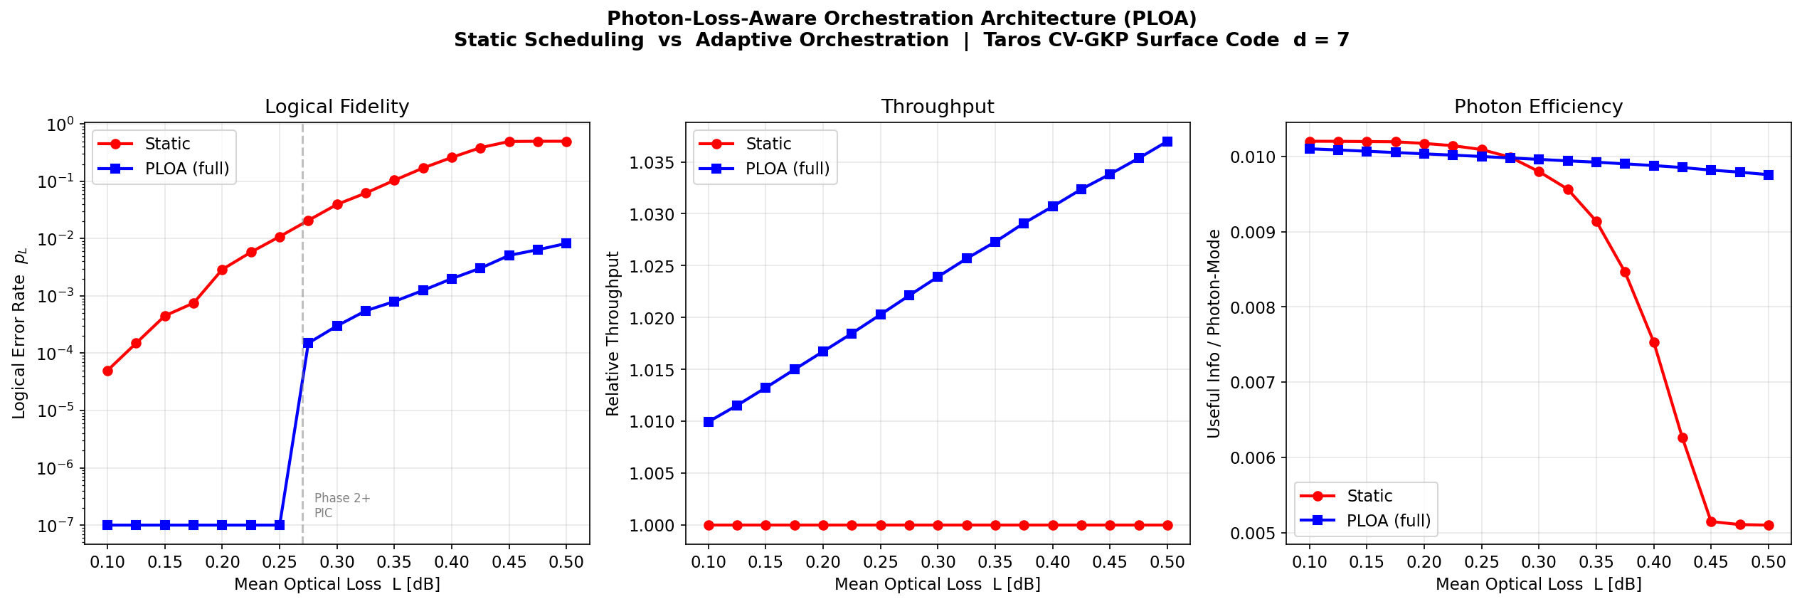
research/results/fig1_comparison.png
