TomohiroTani28/Taros/research/results/fig2_breakdown.png

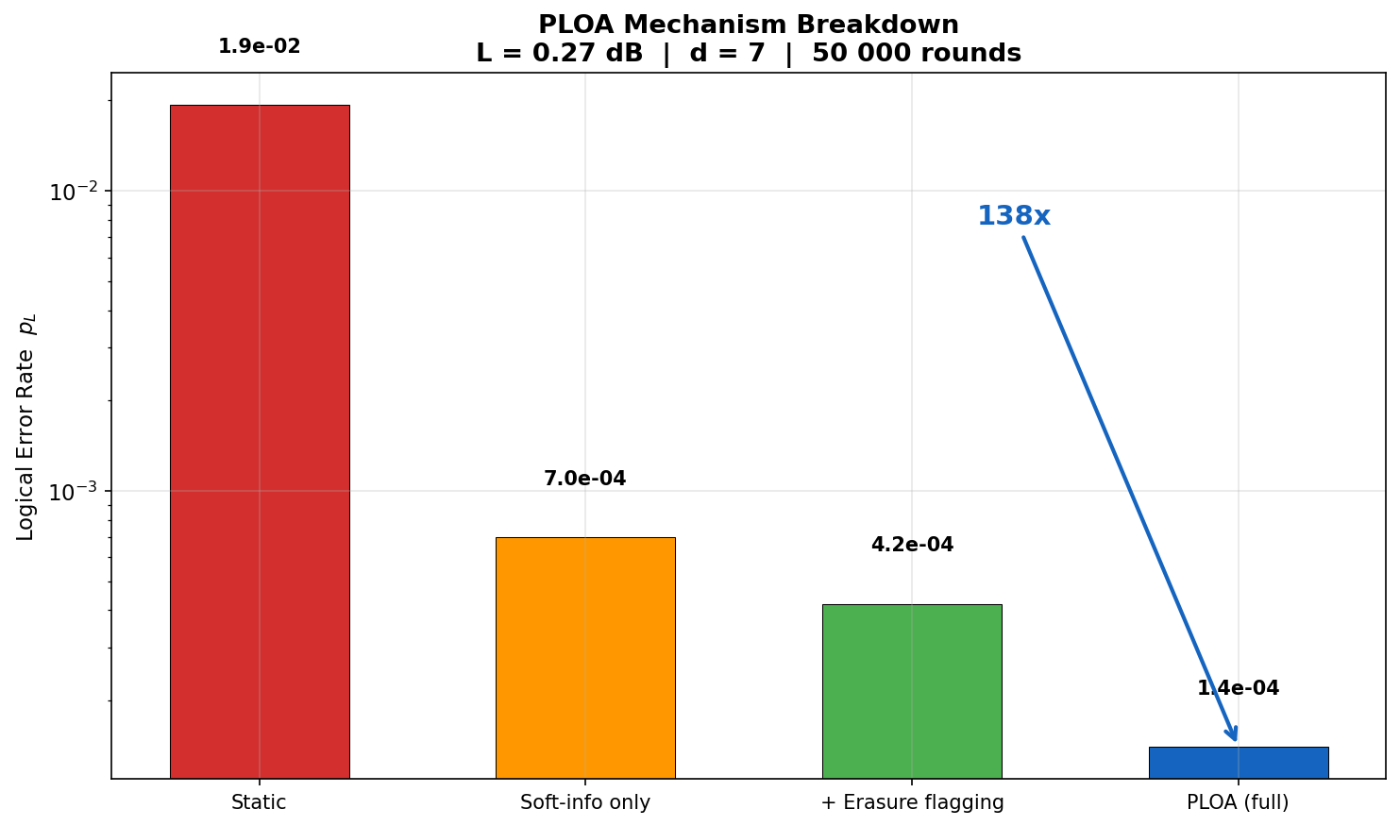
research/results/fig2_breakdown.png
