TomohiroTani28/Taros/research/results/fig3_distance.png

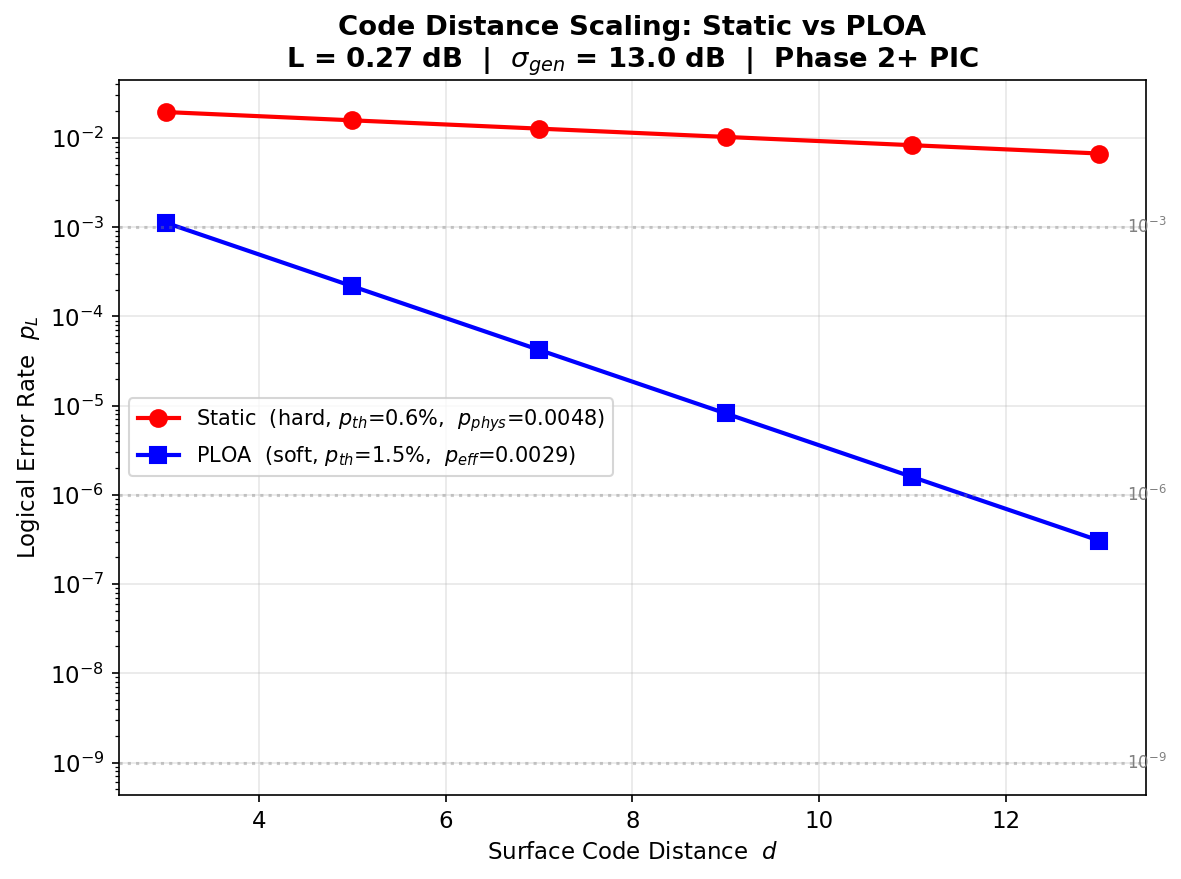
research/results/fig3_distance.png
