TomohiroTani28/Taros/research/results/fig4_landscape.png

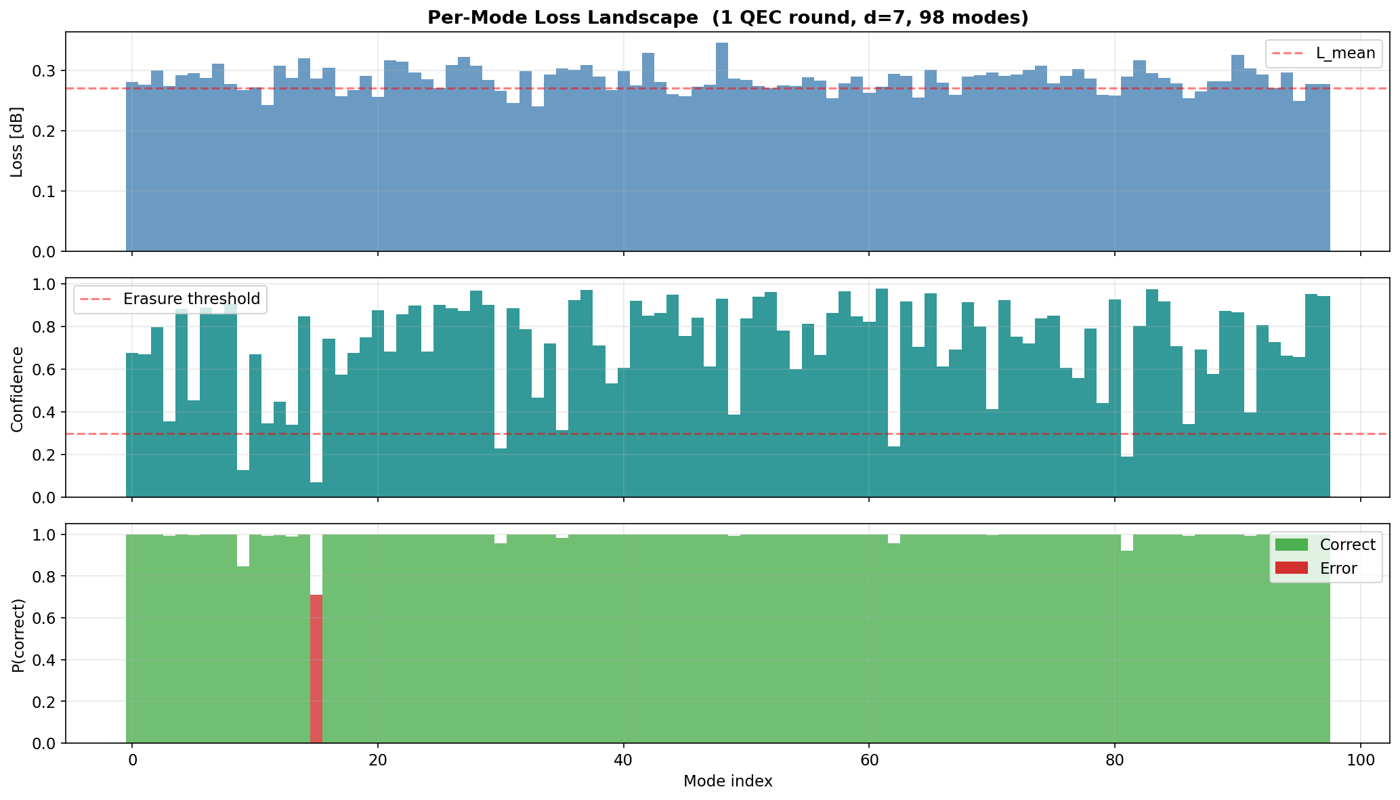
research/results/fig4_landscape.png
