TomohiroTani28/Taros/research/results/fig8_phase_comparison.png

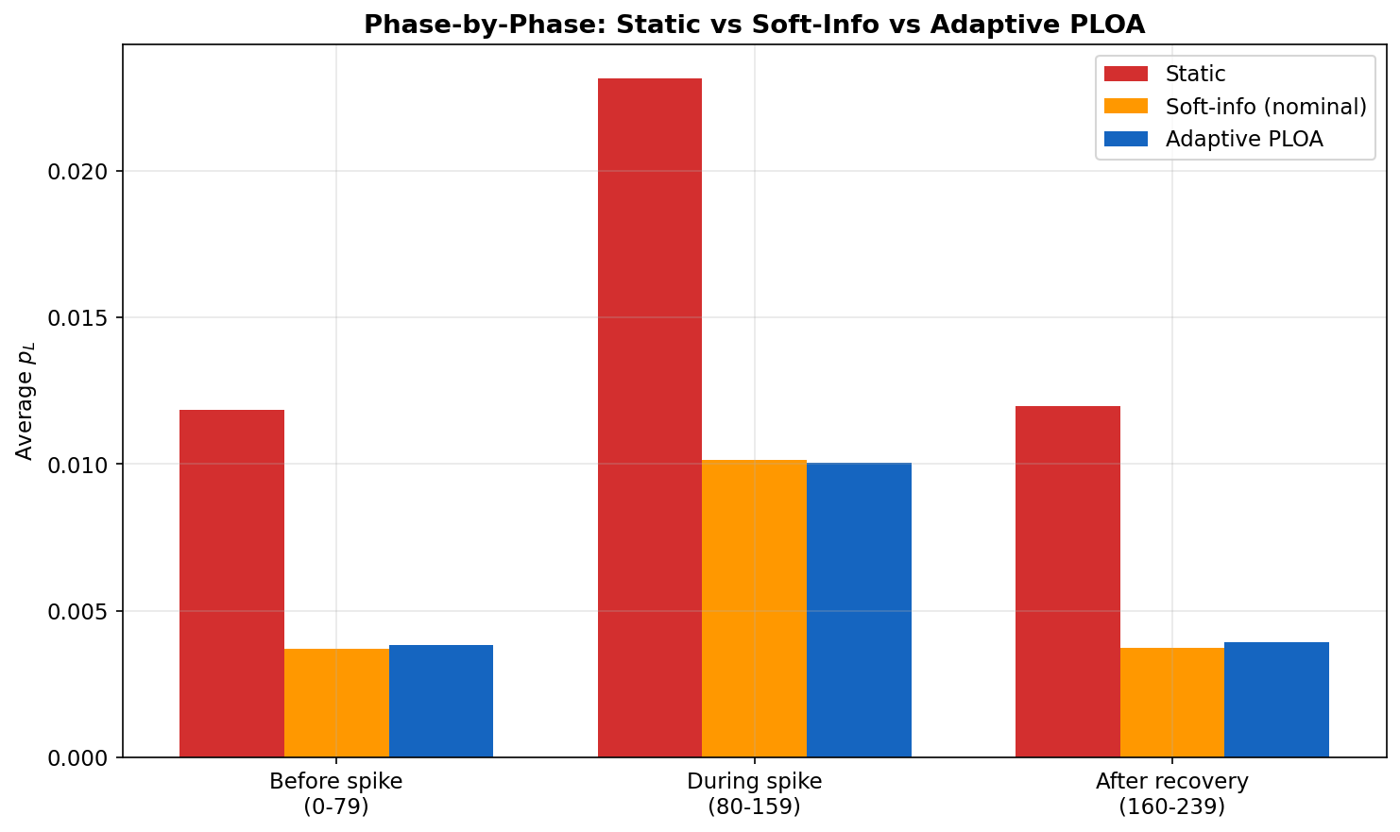
research/results/fig8_phase_comparison.png
