TomohiroTani28/Taros/research/results/fig9_turbo_mwpm.png

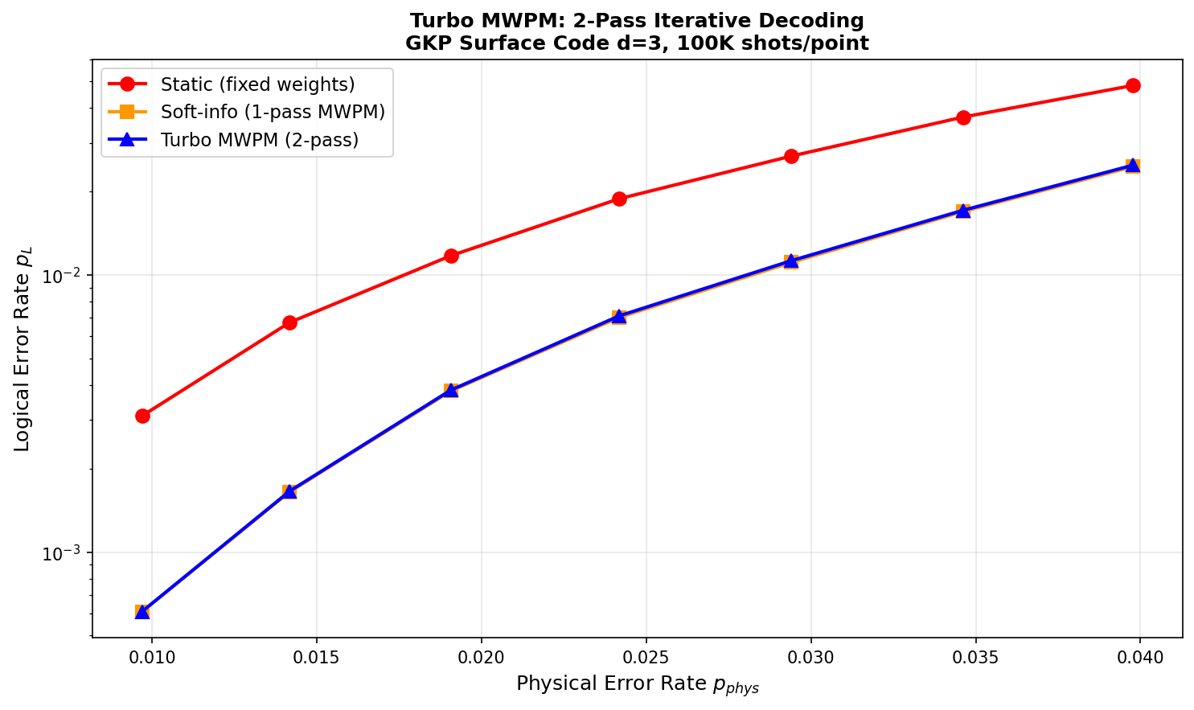
research/results/fig9_turbo_mwpm.png
