TomohiroTani28/Taros/research/results/fig11_seven_in_one.png

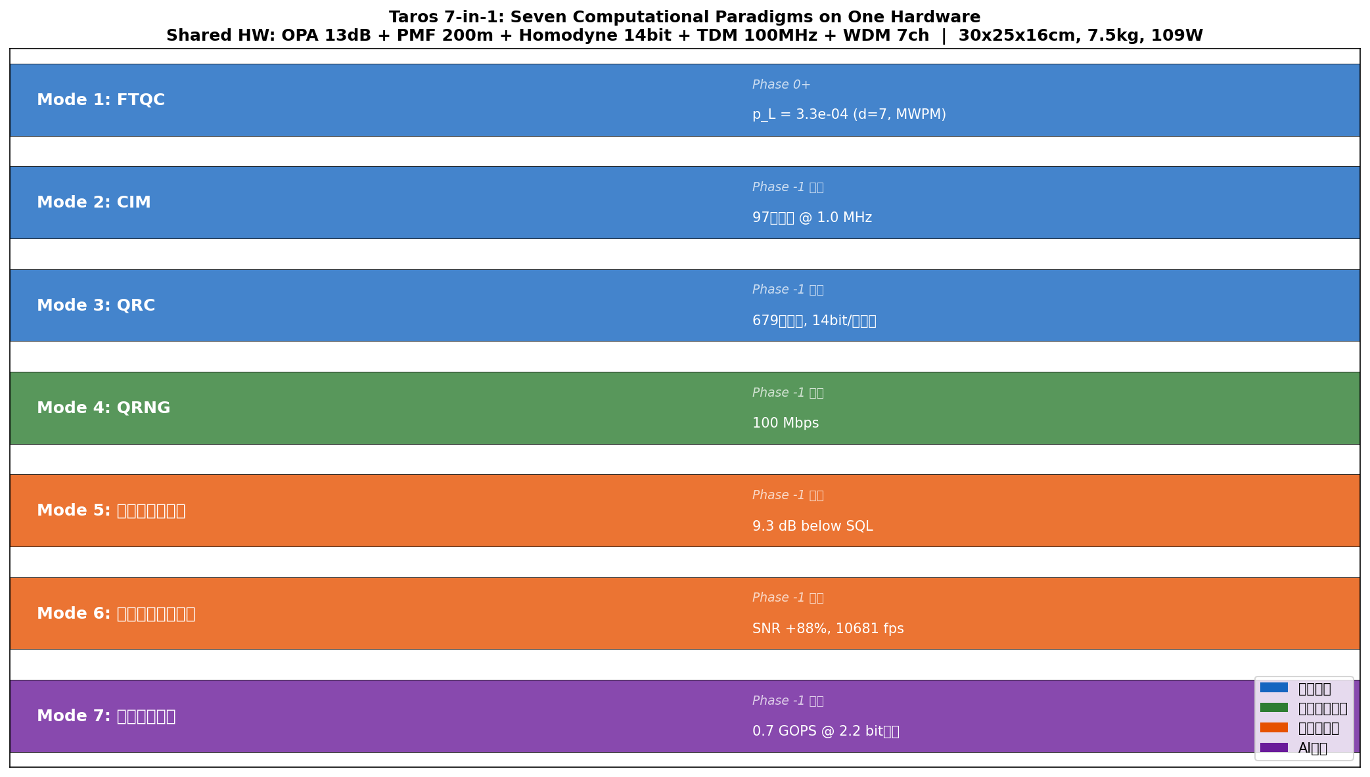
research/results/fig11_seven_in_one.png
