TomohiroTani28/Taros/research/results/fig12_hw_sharing.png

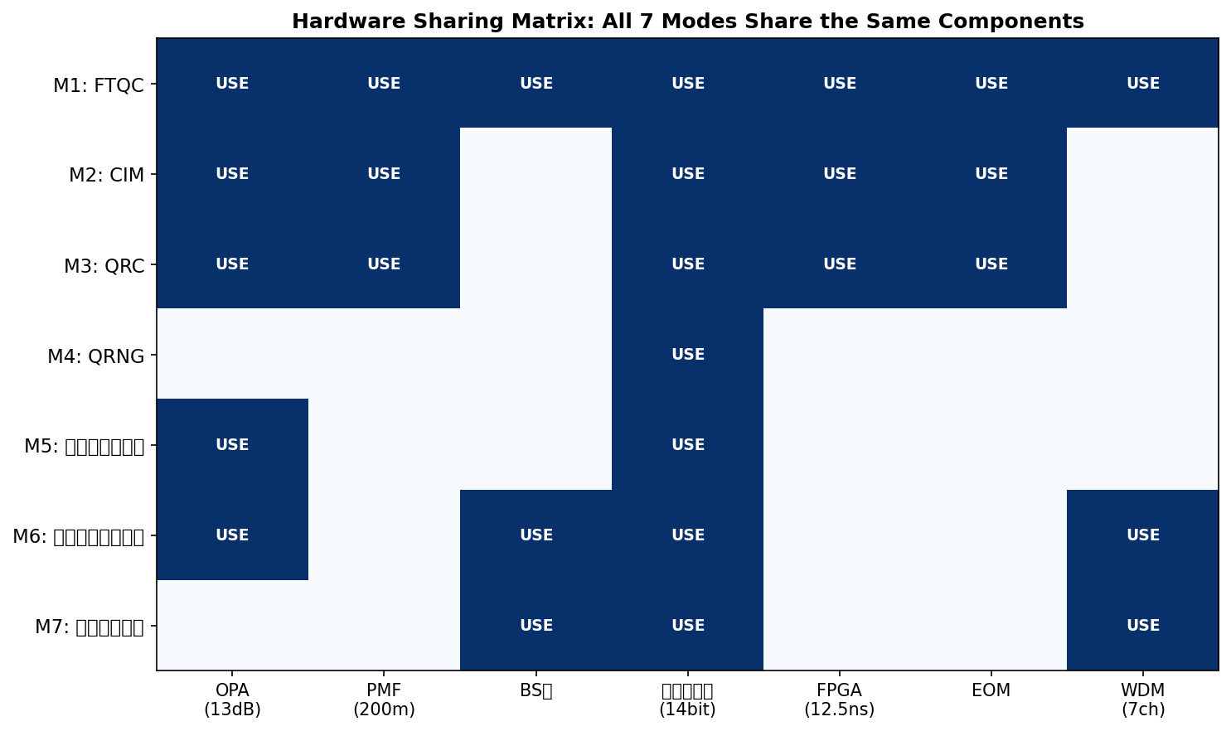
research/results/fig12_hw_sharing.png
