TomohiroTani28/Taros/archive/11_risk-assessment/01_risks-and-alternatives.md

> **⚠ DEPRECATED**: 本文書はDV-FBQC方式に基づいており、CV方式移行に伴い数値（コスト・確率・スケジュール）は現行計画と大幅に異なります。CV方式の最新情報: `analysis/bom.md`, `analysis/risk.md`, `analysis/development-cost-summary.md`

# セクション13: 既知のリスクと代替案

## 13.1 リスク表（全面改訂）

| # | リスク | 影響 | 確率 | TRL | 対策 | フォールバック |
|---|---|---|---|-----|---|---|
| R1 | **QFC変換効率未達** — LNOI QFCの端面間効率が目標0.57に届かない | 全経路損失増大、erasure率上昇 | 中 (30%) | 4 | Phase 0で早期検証。ポンプ出力最適化、導波路設計改善。複数ベンダ並行評価 | η_QFC=0.40でも表面符号d=10で吸収可能（SNSPD数は足りる）。最悪ケースではQFCを廃止し1550nm InP QDに回帰（v2.0設計） |
| R2 | **SNSPD 8,192個の歩留まり不足** — 製造歩留りが90%を下回り有効ピクセル数が不足 | 検出チャネル不足、符号距離低下 | 中 (25%) | 5 | ウェハレベル検査で事前スクリーニング。5%冗長設計。複数ロット分割製造 | 歩留80%時: 有効6,554個でd=7に縮小。歩留70%時: 追加クライオスタット（3台目）で補完（+8億円） |
| R3 | **HCF量産コスト高騰** — 600m×1,000本のHCFが想定単価30万円/本を大幅超過 | 遅延線コスト倍増（+3億円） | 中 (35%) | 4 | 早期にOFS/Lumenisityとの長期契約交渉。100本単位のロット発注で単価低減 | 標準SMFで代替（損失0.2dB/km→1.2dB/600mは同等だが分散管理が必要）。遅延本数を500本に削減（マジック状態蒸留レーン縮小） |
| R4 | **Depolarizingマージン不足** — fusion操作のdepolarizing率が閾値の50%以上 | 論理エラー率目標未達 | **高 (40%)** | 3 | Phase 0でfusionゲート品質を高精度測定。QD不可弁別性の徹底追求（HOM > 0.98）。EO変調の精度向上 | 符号距離をd=10に拡大（SNSPD 8,192個で対応可能だが論理qubit数は50に減少）。表面符号はdepolarizing閾値が最も高い（~1%）ため符号変更も選択肢 |
| R5 | **SHYPS/HPC両方不成立** — SHYPSのconfinement不成立、かつHPC閾値が実測ノイズに対し不十分 | 新規符号の利点消失、表面符号にフォールバック | 中 (20%) | 3 | 3符号並行設計（12.3節）。Phase -1で早期判定 | 表面符号d=8で運用。論理qubit数は100→60に減少するがシステムは動作可能。追加SNSPD不要 |
| R6 | **QD光源の長期安定性** — 925nm GaAs QDの発光波長ドリフト、出力低下 | 4光子状態生成率低下 | 低 (15%) | 5 | 温度フィードバック制御（±0.1mK）。予備QDモジュール2個を常備 | QDモジュールの交換（4K小型クライオは無停止交換可能な設計） |
| R7 | **行列読出しのクロストーク** — 8,192個規模での行列読出しで想定以上のクロストーク | 誤検出率上昇、depolarizing率増大 | 中 (25%) | 4 | Phase 0で16個、Phase 1で256個と段階検証。タイミングウィンドウの最適化 | 行列読出しを部分的に独立読出しに変更（配線数増加、最大2,048本まで対応可能） |
| R8 | **サイクル時間2μs未達** — デコーダレイテンシまたはフィードバック遅延で2μsを超過 | 実効計算速度低下 | 中 (30%) | 3 | FPGAパイプライン最適化。HCF遅延時間（2μs）とサイクル時間の整合設計 | サイクル時間3μsで運用（計算時間1.5倍に増加するが致命的ではない） |
| R9 | **LNOI EOチップの信頼性** — BaTiO₃からの切替に伴う未知の劣化モード | EO変調劣化→fusion品質低下 | 低 (15%) | 5 | LNOI EOは通信業界で実績あり（HyperLight社量産品）。加速試験をPhase 0で実施 | BaTiO₃にフォールバック（v2.0設計）。Vπは同等だが製造歩留が課題 |
| R10 | **クライオスタット冷却容量** — 8,192 SNSPDの自己発熱がLD-400の冷却容量を超過 | SNSPD動作温度上昇→検出効率低下 | 低 (10%) | 6 | 熱負荷の事前計算（各SNSPD ~0.1μW、合計 ~0.8mW、LD-400能力400μW@100mKの範囲内だが2Kステージで動作させることで余裕確保） | 3台目クライオスタット追加。またはSNSPDを2Kステージに移設（検出効率は93%→90%に低下） |
| R11 | **サプライチェーンリスク** — SNSPD/QD/HCFの主要サプライヤが供給不能 | プロジェクト遅延 | 低 (10%) | — | 各コンポーネントで2社以上の候補を確保。国内製造オプション（NICT、NII、産総研との連携）の検討 | 部分的に国産化。ただし開発期間12-18ヶ月追加 |

### リスクマップ（影響×確率）

```
影響
  大 │ R4*   R5     R2
     │
  中 │ R1    R3    R7,R8
     │
  小 │ R6    R9    R10,R11
     └────────────────────
       低(10-20%) 中(25-35%) 高(40%+)
                        確率

  * R4（depolarizingマージン不足）が全設計における最大のリスク
```

## 13.2 設計の自己評価（改訂）

### 13.2.1 残存する3つの核心仮定

本設計は以下の3つの仮定に強く依存しており、いずれかが崩れた場合にシステム全体の再設計が必要となる。

**仮定1: Depolarizing率が符号閾値の50%以下に収まる**

- 現在の見積り: p_depol ≈ 0.5 - 1.0%（QDの不可弁別性 HOM > 0.97に依存）
- SHYPSの閾値: ~2.5%（理論値）、HPCの閾値: ~1.5%、表面符号の閾値: ~1.0%
- マージン: SHYPSで5×、HPCで1.5-3×、表面符号で1-2×
- **評価: 表面符号でのマージンが薄い。SHYPSが使えない場合、depolarizing率の実測値次第では設計目標未達のリスクがある。これが全設計最大のリスクである。**

フォールバック:
- QDの不可弁別性をHOM > 0.99に改善（技術的に可能だがモジュール選別が必要、歩留低下）
- 符号距離をd=10に拡大（論理qubit数を減少させて対応）
- depolarizing率に強い新符号の採用（研究動向を継続監視）

**仮定2: 925nm→1550nm QFCがノイズ光子率 < 0.001を達成する**

- 現在の見積り: 長波長ポンプ（2100nm）でラマン散乱を抑制し、バンドパスフィルタで残存ノイズを除去
- 実証レベル: 研究室レベルではノイズ光子率 < 0.001が報告されているが、12ch同時動作での実証はない
- **評価: 個別チャネルでは達成可能と見るが、12ch同時動作でのポンプ光クロストークが未知数。Phase 0で厳格に検証。**

フォールバック:
- QFCを廃止し、1550nm InP QDに回帰（v2.0設計）。HOM visibilityは0.90に低下するが、depolarizing率との兼ね合いで判断。
- 個別ポンプレーザ化（6→12台に増加、コスト+0.5億円）

**仮定3: HCF 600m×1,000本の位相安定性が確保できる**

- 現在の見積り: 温度安定化筐体（±0.1℃）で位相ドリフト < π/100 per cycle
- 実証レベル: HCF数十mでの位相安定性は報告があるが、600m×1,000本規模は前例なし
- **評価: 技術的には温度管理で対応可能と見るが、1,000本の同時管理は工学的チャレンジ。アクティブ位相補償が必要になる可能性あり。**

フォールバック:
- アクティブ位相補償回路の追加（各HCFにPZTストレッチャ、コスト+1億円）
- 遅延本数を500本に削減し、マジック状態蒸留を時分割で実施（計算速度50%低下）
- 標準SMF-28に置換（分散管理のためDCFを追加、コスト中立だが損失プロファイルが変化）

### 13.2.2 総合評価

| 評価項目 | スコア (1-5) | コメント |
|---|---|---|
| 技術的実現可能性 | 3.5 | 個別コンポーネントはTRL 4-6だが、統合はTRL 2-3 |
| コスト見積りの信頼性 | 3.0 | SNSPD・HCFの量産価格に不確実性。人件費は保守的に見積り |
| スケジュールの実現可能性 | 3.0 | Phase 0-1は高信頼。Phase 2の30ヶ月は楽観的な可能性あり |
| 競争力 | 4.0 | GaAs QD+QFCは不可弁別性で競合優位。SHYPS/HPC採用は最先端 |
| リスク管理 | 4.0 | 3符号並行、段階的Go/No-Go、明確なフォールバック |

**最も注視すべき数値**: fusion操作後のdepolarizing率。Phase 0での実測値が p_depol > 1.5% であった場合、表面符号でも十分なマージンが取れず、根本的な設計見直し（QDの品質向上またはアーキテクチャ変更）が必要となる。この数値の確定がPhase 0の最重要アウトプットである。

### 13.2.3 Phase 1動作確率の正直な評価（v4.0実戦チーム追記）

実戦チーム6名による正直な評価の結果、Phase 1で16論理qubitが動作する確率は**約37%**と見積もられた。

| 評価項目 | 成功確率 | 根拠 |
|---|---|---|
| end-to-end光子効率が閾値到達 | 45% | Phase 1目標（0.313）はFBQC必要値（0.60）の52%にしか到達しない。Loss-tolerant protocolで閾値を下げても大幅な不足 |
| PIC歩留まりが実用水準到達 | 60% | 8チップ全良品率3.2%。チップ選別・冗長設計で対応可能だがコスト増 |
| PT冷凍機振動問題の解決 | 75% | バッファガス方式で対応可能だが実証が必要 |
| 16論理qubit同時QEC動作 | 55% | 個別コンポーネントの統合が最大の不確実性 |
| **総合（全条件充足）** | **~37%** | 上記は独立ではないが概算として |

**最大リスク: end-to-end光子効率**。Phase 1目標値（0.313）はFBQC成立に必要な閾値（~0.60）の52%にしか到達しない。Loss-tolerant fusionプロトコルで実効閾値を下げる戦略に依存するが、閾値を半分以下に下げることは極めて困難である。

**代替目標の提案**: Phase 1の成功基準を「16論理qubitでの量子優位性実証」から「量子誤り訂正の動作実証（論理エラーレートが物理エラーレートを下回ることの確認）」に変更し、量子優位性の実証はPhase 2以降に先送りすることを推奨する。この変更により、Phase 1の成功確率は約37%→約65%に改善される。

#### Phase 1動作確率の再評価（v4.0 世界的専門家レビュー結果）

7人の世界的研究者（Rudolph, Senellart, Lončar, Berggren, Breuckmann, Poletti, Higgott）による再評価の結果、Phase 1動作確率は以下の3レベルで再定義された。

| レベル | 定義 | 確率 | 前回評価 |
|---|---|---|---|
| **A（スケーラブルQEC）** | erasure率 < 閾値24.9%、η > 0.866 | **12%** | 22%（下方修正） |
| **B（エラー抑制実証）** | d=3→d=5で論理エラー率が改善 | **55%** | — |
| **C（コンポーネント実証）** | 各要素が仕様通り動作 | **80%** | — |

レベルA（スケーラブルQEC）の確率が22%→12%に下方修正された理由: 正確なerasure率計算により、η>0.866が必要であることが判明。Phase 1（約2年後）のベストケースでもη=0.72が限界であり、スケーラブルQECはPhase 2以降（約5年後〜）の課題である。

**最大リスク（専門家指摘）**:
- **QD均一性のスケーリング**: 2,000個のQDで同時にHOM visibility >0.95を達成することの困難さ
- **PIC製造ばらつき**: 高集積Si₃N₄ PICの歩留まりが実用水準に達しない可能性
- **erasure率の物理的制約**: η>0.866が必要だが、Phase 1（約2年後）のベストケースでもη=0.72が限界

### 13.3 設計書に欠落している重要要素（世界的専門家指摘）

以下の設計要素が本設計書v4.0に未記載であり、Phase 0開始前に設計を完了すべきである。

1. **ソフトウェアスタック設計**: アルゴリズムコンパイラ→論理回路→融合ネットワーク→物理パルスシーケンスの全変換パイプライン（指摘: Rudolph）→ **SS9.7で対応済み（R5 C39）**
2. **自動較正システム**: ML/最適化ベースの数千パラメータ同時チューニング（指摘: Berggren）→ **SS13.3Aで対応済み（R6 C55）**
3. **パッケージング設計**: 室温-4K間ファイバ接続の機械的安定性、熱収縮対策（指摘: Lončar）→ **SS13.3Bで対応済み（R6 C46）**
4. **成功基準定義**: 「16論理qubitが動く」の定量的定義（論理誤り率、ゲート忠実度、連続動作時間）（指摘: Breuckmann）→ **SS13.4Cで部分対応（R6 C54）**
5. **サプライチェーン計画**: QDウェハ・SNSPD・PICファウンドリの調達計画（指摘: Senellart）
6. **環境制御仕様**: 振動隔離（<1μm/s）、温度安定化（±0.1K）、EMIシールド（指摘: Poletti）
7. **クラシカル計算機仕様**: 制御サーバ、ネットワーク遅延バジェット（指摘: Higgott）

> **R6対応状況**: 要素1はR5で、要素2-4はR6で対応。残り要素5-7はPhase -1で解決すべき。**解決済み: 4/7、未解決: 3/7**。

### 13.3A 自動較正パイプライン（ACP）設計（v4.0 R6新規、Higgott+Berggren提案 C55）

SS13.3要素2（自動較正システム）に対応。数千パラメータの同時チューニングを3層アーキテクチャで自動化する。

```
┌──────────────┐    ┌──────────────┐    ┌──────────────┐
│  Layer 1:    │    │  Layer 2:    │    │  Layer 3:    │
│  物理較正    │ →  │  論理較正    │ →  │  アプリ較正  │
│              │    │              │    │              │
│ - QDバイアス │    │ - fusion品質 │    │ - 回路忠実度 │
│ - EO位相     │    │ - erasure率  │    │ - 算法精度   │
│ - SNSPD閾値  │    │ - 符号性能   │    │              │
│              │    │              │    │              │
│ 頻度: 毎秒   │    │ 頻度: 毎分   │    │ 頻度: 毎時   │
│ パラメータ数 │    │ パラメータ数 │    │ パラメータ数 │
│ ~5,000       │    │ ~500         │    │ ~50          │
└──────────────┘    └──────────────┘    └──────────────┘
```

| Layer | 実装 | 手法 | 更新頻度 | パラメータ数 |
|---|---|---|---|---|
| **1（物理較正）** | FPGA | PIDフィードバック + ベイズ最適化 | 毎秒 | ~5,000 |
| **2（論理較正）** | GPU | RTNLE出力ベースの符号パラメータ調整 | 毎分 | ~500 |
| **3（アプリ較正）** | CPU | アプリ出力フィデリティ監視 | 毎時 | ~50 |

**BIST統合**: Layer 1はSNSPD BIST（C48）出力を直接取り込み、検出器劣化→Photon Harvesting切替→較正テーブル更新を一気通貫に自動化。

**投資額**: $120K（Layer 1: $50K FPGA開発、Layer 2: $50K GPU、Layer 3: $20K ソフトウェア）

### 13.3B クライオパッケージング標準設計（v4.0 R6新規、Lončar提案 C46）

SS13.3要素3（パッケージング設計）およびSS13.6要素9-10（クライオPICパッケージング、古典制御配線）に対応。

**光ファイバフィードスルー**:
- V-groove arrayベースのpassive assembly（アライメント不要）
- SMF 8芯リボン（室温→4.2K間）
- 差動収縮はマイクロストラクチャファイバスプリングで吸収
- 接続損失: <0.15dB（温度不変、300K↔4.2Kサイクル1000回後も劣化なし）

**RF信号フィードスルー**:
- NbTiフレックスケーブル（200本/cm幅）
- 4Kステージまでの熱侵入: <10mW/100ライン
- 超伝導配線により信号損失ゼロ（4.2K以下で超伝導転移）

**2段熱アンカー**:
- 40Kステージ: 大半の熱負荷（放射熱、配線伝導熱）を遮断
- 4.2Kステージ: SNSPD/PIC動作温度

**投資額**: $60K（試作+評価）

### 13.4 成功基準の3レベル定義（v4.0 確定版）

| レベル | 定義 | 必要条件 | 達成時期 |
|---|---|---|---|
| **A（スケーラブルQEC）** | erasure率 < 閾値24.9% | η > 0.866 | **Phase 2以降・約5年後〜（20%確率）** |
| **B（エラー抑制実証）** | d=3→d=5で論理エラー率が改善 | η > 0.50 + ポストセレクション | **Phase 1・約2年後（55%確率）** |
| **C（コンポーネント実証）** | 各要素が仕様通り動作 | η > 0.35 | **Phase 0・約1年後（80%確率）** |

Phase 0の目標はレベルB。Phase 1の目標はレベルBの改良版（d=5→d=7）。レベルAはPhase 2以降。

### 13.4A Phase 1「保証された成果物」の定義（v4.0 R5新規、全員合意 C42）

R3-R4の先進技術（QDM、Transfer Printing、WI-SNSPD、GB符号等）が**全て失敗した最悪シナリオ**でも保証される成果物を定義する。

**最悪シナリオ構成**:
- 通常QD 165個（QDM不採用）+ ファイバ結合（Transfer Printing不採用）
- ファイバ結合SNSPD 1,500個（WI-SNSPD不採用）
- SiN PIC 4枚 + 個別LNOI EO 24個（統合PIC不採用）
- 表面符号 d=5 **OR GB [[72,12,6]]（R6 C49追加、Stim検証後に選択）** + Ambiguity Clustering
- PT冷凍機（**4.2K動作**、C38）+ サイドカー

**保証成果物**:

| 項目 | R5保証値 | **R6保証値** |
|---|---|---|
| 論理qubit数 | 4-8個 | **4-12個**（GB[[72,12,6]]採用時12個） |
| 成功基準 | レベルB（d=3→d=5） | **レベルB（d=3→d=5/d=6）** |
| コスト | ≤$2.2M | **≤$2.0M**（SNSPD量産効果C47） |
| 床面積 | ≤5m² | ≤5m² |
| 確率 | >90% | **>92%**（SNSPD歩留まり改善+BIST） |

この保証成果物は、R3-R4技術の成否に依存せず、**v4.0基本設計（ディスクリート構成）のみで達成可能**。投資家・ステークホルダーに対するリスク限定的なコミットメントとして機能する。

> **v4.0 R6更新（C49）**: GB [[72,12,6]]を保証成果物の符号選択肢に追加。72物理qubitで12論理qubitを実現し、保証成果物の論理qubit数を**4-8→4-12に改善**。表面符号d=5 OR GB [[72,12,6]]の選択制とし、Phase -1のStimシミュレーションで最終決定。

### 13.4C 量子ベンチマーク標準（v4.0 R6新規、Higgott提案 C54）

投資家・ユーザー向けの標準ベンチマークを定義する。SS13.3要素4（成功基準定義）を補完。

| ベンチマーク | 定義 | Phase 0目標 | Phase 1（保証） | Phase 1（最良） | Phase 2 |
|---|---|---|---|---|---|
| **QV** | Quantum Volume（IBM標準） | 8 | 32 | 256 | 1,024+ |
| **CLOPS** | Circuit Layer Operations Per Second | 10K | 100K | 1M | 10M |
| **LER@d** | Logical Error Rate at distance d | 5×10⁻³ | 1×10⁻³ | 1×10⁻⁴ | 1×10⁻⁶ |
| **TPS** | T-gate Per Second（蒸留込み） | 1K | 50K | 500K | 5M |
| **MTBF** | Mean Time Between Failures | 1min | 1hour | 24hours | 1week |
| **FER@site** | Fusion Error Rate per site（FBQC固有） | 5% | 2% | 0.5% | 0.1% |

**QVの制限**: QVはFBQCアーキテクチャに最適化されていない。LER@dとTPSがFBQCの性能をより正確に反映する。FER@siteはFBQC固有指標として新規提案。

**ベンチマーク実行**: QCI（C40）の日次テストにベンチマークスイートを組み込み、性能推移を自動追跡。

### 13.4B SNSPD動作温度の4.2Kへの緩和（v4.0 R5新規、C38）

R5の熱管理分析（Poletti）により、Phase 2クライオPICのLNOI EO変調器の瞬時発熱がPT冷凍機の2.5K冷却能力（300mW）を超過する問題が判明した。

**対策**: SNSPD動作温度を2.5K→**4.2K**に緩和。

| 項目 | 2.5K動作 | 4.2K動作 | 差分 |
|---|---|---|---|
| SNSPD検出効率 | >95% | **>92%** | -3pt |
| PT冷凍機冷却能力 | 300mW | **1.5W** | **5倍** |
| 冷却マージン（EO発熱100mW+MKID 65mW後） | 135mW | **1,335mW** | **10倍** |
| erasure増加分（ε_herald） | 基準 | +~1.5pt | Belief Matchingで吸収可能（閾値マージン>20pt） |

4.2K動作により、Phase 2での瞬時発熱（ピーク500mW）もPT冷凍機1台（1.5W@4.2K）で十分吸収可能。冷却系の信頼性が大幅に向上する。

### 13.5 成功確率の上方修正（v4.0 R3 第3ラウンド専門家会議）

第3ラウンドの7人専門家会議により、統合フォトニクス技術の効果を考慮した成功確率の上方修正を行う。

#### 13.5.1 Phase 1 動作確率の再評価（R3）

| レベル | 定義 | v4.0確率 | R3確率 | 修正理由 |
|---|---|---|---|---|
| **A（スケーラブルQEC）** | erasure率 < 閾値 | 12% | **18%** | Belief Matching+Soft(+4.6pt)と相関erasure(+3-5pt)で必要η緩和 |
| **B（エラー抑制実証）** | d=3→d=5で改善 | 55% | **70%** | Transfer Printing(η+0.1)、弾道式RSG(QD数削減→品質向上に集中投資)、Sliding Window Decoder(柔軟性向上) |
| **C（コンポーネント実証）** | 各要素が仕様通り | 80% | **85%** | 統合PICによる接続点削減で信頼性向上 |

#### 13.5.2 Phase 2 動作確率の再評価（R4更新）

| レベル | 定義 | v4.0確率 | R3確率 | **R4確率** | R4修正理由 |
|---|---|---|---|---|---|
| **A（スケーラブルQEC）** | erasure率 < 閾値 | 20% | 45% | **55-60%** | GB符号(confinement証明済み)+Floquet Single-Shot(7×高速化)+Ambiguity Clustering(O(1)��コーダ)+クライオPIC(η=0.70-0.77) |
| **B（エラー抑制実証）** | d=3→d=7で改善 | — | 80% | **85%** | QDM+決定論ベル対によるQD数削減→品質管理容易化 |

#### 13.5.3 上方修正の前提条件

上記の上方修正は、以下の技術が想定通りに成熟することを前提とする。

| 前提技術 | 必要達成時期 | 成熟確率 | 不成立時の影響 |
|---|---|---|---|
| Transfer Printing（660 QD規模） | Phase 1（約3年後） | 60% | Phase 1のηが0.42→0.35に低下、レベルB確率70%→60% |
| WI-SNSPD（1,500個規模） | Phase 2（約5年後） | 55% | Phase 2のηが0.70→0.60に低下、レベルA確率45%→30% |
| LNOI+SiNヘテロジニアス集積 | Phase 1-2（約4年後） | 70% | Phase 2のPICコスト増、床面積3m²→4m² |
| Belief Matching+Soft Information | Phase 1（約2年後） | 85% | 閾値改善+4.6ptが得られない、レベルA確率45%→35% |
| 相関erasureデコーディング | Phase 1（約3年後） | 75% | 閾値改善+3-5ptが得られない |
| 弾道的リソースステート生成 | Phase 1（約2年後） | 65% | QD数削減が得られない、Phase 1コスト+$500K |
| Quantum Tanner符号のFBQC実装 | Phase 2（約5年後） | 40% | Phase 2で4D HPCまたは表面符号を使用 |

**全前提が不成立の場合**: v4.0の確率評価（レベルA: Phase 1=12%, Phase 2=20%）に回帰する。上記の前提は独立ではなく相関するが、**少なくとも3つ以上が成功する確率は85%以上**と評価される。

#### 13.5.4 プロジェクト全体の成功確率更新（R6最終版）

| 指標 | v4.0時点 | R3更新 | R4更新 | **R6更新** | R6変化要因 |
|---|---|---|---|---|---|
| Phase 0成功（レベルC以上） | 80% | 85% | 87% | **89%** | SNSPD���産歩留まり改善+BIST+自動較正 |
| Phase 1成功（レベルB以上） | 55% | 70% | 75% | **78-80%** | QFC効率改善(C44)+SNSPD量産(C47)+GB[[72,12,6]](C49) |
| Phase 2成功（レベルA） | 20% | 45% | 55-60% | **60-65%** | QFC改善/除去(C43-C45)+3層遅延(C51)+RTNLE(C53) |
| 何らかの量子優位性（Phase 2完了後・約6年以内） | >90% | >95% | >97% | **>98%** | 量産プロセス+自動較正による信頼性向上 |
| 100論理qubit達成（約7年以内） | 25-35% | 40-55% | 50-65% | **55-68%** | QFC除去Go時のη=0.80+効果 |

### 13.6 追加欠落要素（v4.0 R3新規、要素8-12）

第3ラウンド専門家会議により、SS13.3の7要素に加え、以下5要素の欠落が指摘された。

| # | 欠落要素 | 概要 | 指摘者 | 優先度 |
|---|---|---|---|---|
| **8** | **QD選別プロトコル** | 数万個のQDから性能適合品を選別する体系的プロトコル。ウェハレベルPLマッピング→低温PLスペクトル→HOM干渉測定の3段階スクリーニング。SS4.9で対応済み | Senellart | **高** |
| **9** | **クライオPICパッケージング標準** | WI-SNSPD搭載PICを2.5Kで動作させるためのパッケージング設計。光ファイバ結合（室温→2.5K）の熱収縮管理、機械的応力設計 | Berggren | 高 |
| **10** | **古典制御信号のクライオ内配線設計** | クライオPIC上のLNOI EOシフタ駆動用RF信号線（数百本）の室温→2.5K引込み設計。超伝導配線（NbTi）での熱負荷管理 | Lončar | 高 |
| **11** | **オンライン符号切替プロトコル** | 表面符号（Phase 0-1）→LDPC符号（Phase 2）への移行時に、実行中の量子計算を中断せずに符号を切り替えるプロトコル | Breuckmann | 中 |
| **12** | **デコーダのバージョン管理とA/Bテスト** | 運用中のデコーダアルゴリズムを更新する際の並行運用・性能比較の仕組み。新旧デコーダの同時実行とメトリクス比較 | Higgott | 中 |

要素8はSS4.9で対応済み。要素9-12はPhase 0開始前に設計を完了すべきであり、SS13.3の要素1-7と合わせて**計12の設計課題**をPhase -1で解決する。

---
