TomohiroTani28/Taros/archive/16_changelog/01_v3-to-v4.md

> **⚠ FROZEN (2026-05-04)**: 本文書はDV-FBQC v4.0 R6時点の設計を記録したものです。プロジェクトの主軸はCV方式に移行しています。最新設計は `design/00_overview.md` を参照してください。

### 1.2 v2.0からv3.0への主要変更概要

v3.0の設計哲学は「既報告技術の組合せによるシステム統合」であり、各要素技術は査読済み論文で報告された性能値に基づくが、システム全体としての統合は未実証であることを明示する。v2.0で採用していた未実証技術（1550nm InP QD、BaTiO₃ EO変調器）を全て排除し、実証済み技術（925nm GaAs QD、LNOI）で置き換えた。

### 1.2A v3.0からv4.0への主要変更概要

v4.0の主要変更は以下の通りである。

1. **設計五原則の確立**: 四原則に「Deployability（設置展開容易性）」を第二原則として追加。床面積60m²→7-8m²→4m²への段階的縮小を定量目標化。
2. **Phase体系の再編**: v3.0の現行構成を**Phase 0（研究実証機）**として明示ラベリングし、Phase 1（約3〜4年後）/Phase 2（約5〜6年後）の小型化・省電力化ロードマップを追加。
3. **冷却系の根本変更**: 光量子コンピュータにおいてmK級冷却（希釈冷凍機）は不要であることを明記。Phase 1以降はパルスチューブ（PT）冷凍機に移行し、重量・消費電力・コストを大幅削減。
4. **損失予算のPhase別3列比較**: Phase 0: -6.3dB(効率23.4%), Phase 1: -5.4dB(28.8%), Phase 2: -4.3dB(37.2%)。
5. **BoMのPhase別再構成**: Phase 0: $8.0M, Phase 1: $3.5-4.0M, Phase 2: $1.5M。
6. **デコーダ移行計画**: GPU（Phase 0）→ FPGA（Phase 1）→ ASIC（Phase 2）。
7. **符号移行計画**: 表面符号（Phase 0-1）→ Quantum LDPC符号（Phase 2）。
