TomohiroTani28/Taros/archive/16_changelog/02_r3-integrated-photonics.md

> **⚠ FROZEN (2026-05-04)**: 本文書はDV-FBQC v4.0 R6時点の設計を記録したものです。プロジェクトの主軸はCV方式に移行しています。最新設計は `design/00_overview.md` を参照してください。

### 1.2B v4.0 R3（第3ラウンド専門家会議）での主要変更概要

第3ラウンドの7人専門家会議（Rudolph, Senellart, Lončar, Berggren, Breuckmann, Poletti, Higgott）により、以下14項目の合意事項を反映した。

1. **弾道的リソースステート生成**: ヘラルド方式（成功確率~1%）からPercolation-based生成（成功確率~15%）に移行し、必要QD数を1/6に削減（SS4.8新規）
2. **Transfer Printing**: QDチップレットをPIC上に直接ボンディングし、QD→PIC結合損失を1.0dB→0.3dBに改善（SS3.6新規）
3. **LNOI+SiNヘテロジニアス集積**: QFC・EO変調・受動回路を統合PIC 2枚に集積し、チップ間損失を3.0dB→0.5dBに削減（SS3.6新規）
4. **導波路統合型SNSPD（WI-SNSPD）**: ファイバ結合を不要にし、検出系損失を0.29dB→0.04dBに改善（SS6.4.1B新規）
5. **Quantum Tanner符号**: Phase 2のLDPC候補として追加。定数符号レート5-10%、erasure閾値~30-35%（SS5.9新規）
6. **相関erasureデコーディング**: erasure相関構造を利用し実効閾値を24.9%→28-30%に改善（SS5.10新規）
7. **DNANF**: 損失0.064dB/km、曲げ半径5cmのコンパクトスプールでPhase 2の遅延線体積1/27に削減（SS3.6新規）
8. **Sliding Windowデコーダ**: データ面のデコーダをGPU化し、FPGA依存を蒸留レーンのみに限定（SS9.4新規）
9. **Belief Matching + Soft Information**: erasure閾値を+4.6pt改善し29.5%に引き上げ（SS9.4新規）
10. **QD選別プロトコル**: ウェハレベル高速スクリーニングによる22,000 QD評価の効率化（SS4.9新規）
11. **クライオPIC長期ロードマップ**: QD+PIC+SNSPD一体型冷却構成の設計指針（SS3.6新規）
12. **マルチコアHCF**: 7コアHCFによる物理ファイバ本数1/7削減（SS3.6新規）
13. **インターリービング深度8**: 同一ハードウェアで論理qubit数を16→32に倍増（SS3.6新規）
14. **成功確率の上方修正**: Phase 2レベルA確率20%→45%（SS13.5新規）
