TomohiroTani28/Taros/archive/16_changelog/04_r5-engineering.md

> **⚠ FROZEN (2026-05-04)**: 本文書はDV-FBQC v4.0 R6時点の設計を記録したものです。プロジェクトの主軸はCV方式に移行しています。最新設計は `design/00_overview.md` を参照してください。

### 1.2D v4.0 R5（第5ラウンド専門家会議）での主要変更概要

第5ラウンドは「実現工学」に焦点を当て、R1-R4で設計されたアーキテクチャを**実際に構築・運用するための工学的設計とソフトウェア**を追加した。14合意事項（C29-C42）:

**7本の必須改訂**:

1. **Executive Summary（SS0）新設**: 5,600行超の設計書から最終推奨構成を1ページに集約（C41）
2. **ソフトウェアスタック設計**: Layer 1（RTOS）〜Layer 5（Application API）の5層アーキテクチャ。投資額$750K（C39）
3. **Pilot Tone同期設計**: PIC内全光路に弱い古典光を並行伝搬させ±1ps精度で位相補正。追加コスト<$30K（C29）
4. **QDM歩留まりの正直な再評価**: 15%→**2.4%**（ストレインチューニング込み**8.4%**）。必要評価数950-3,300個（C31）
5. **GB符号CNOTボトルネック対策**: アルゴリズムコンパイラでCNOT並列化（並列度~10で380kHz実効レート）（C37）
6. **SNSPD動作温度を2.5K→4.2Kに緩和**: 冷却マージン135mW→335mW。検出効率低下3ptはBelief Matchingで吸収（C38）
7. **Phase 1「保証された成果物」**: 全R3-R4技術が失敗しても、4-8論理qubitでのレベルB実証を$2.2M以内で保証（C42）

**追加設計項目**:

8. **Single Clock Domain Architecture**: FPGAのメタスタビリティ排除（C30）
9. **QDM Go/No-GoゲートをPhase 0bに設定**: entanglement fidelity >0.85が判定基準（C32）
10. **統合PICをFlip-Chip Bonding方式に変更**: 歩留まり60%→85%（C33）
11. **クライオPIC CTE対策**: LNOIチップレット小型化+SiO₂応力緩衝層（C34）
12. **Adaptive Ambiguity Clustering**: ノイズパラメータ変動に追従するテーブル自動更新（C35）
13. **データ管理**: 10Gbpsデータレート対応、圧縮ログ方式1TB/日（C36）
14. **QCI（Quantum Continuous Integration）**: 自動テストフレームワーク（C40）
